MinnowBoard-org/design-files/expansion-boards-lures/relay-lure/Big Relay Board/Big Relay Lure front.png

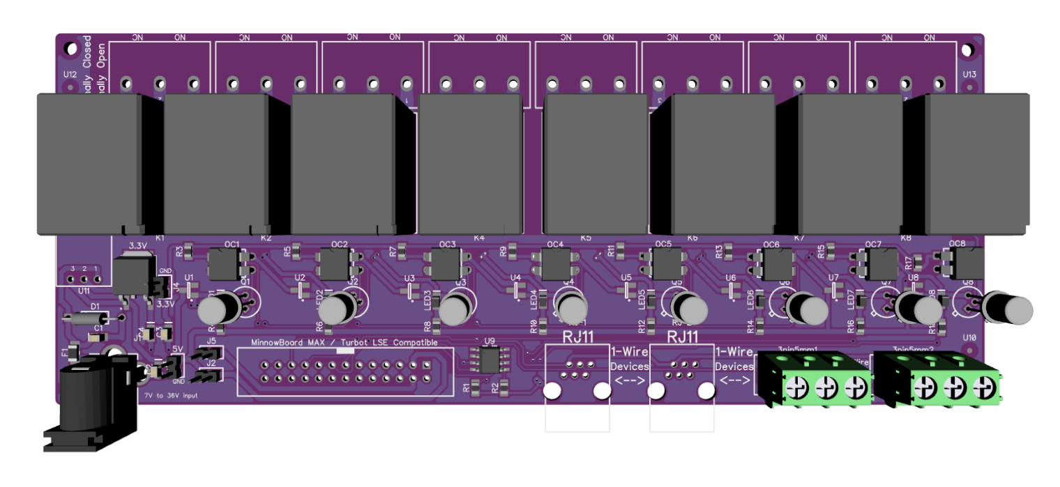
expansion-boards-lures/relay-lure/Big Relay Board/Big Relay Lure front.png
