MinnowBoard-org/design-files/minnowboard-turbot-dual-core/pcb-f200-revX205_Turbot-A/Turbot_F200_X205_VX/Minnowmax_Central_Library/LogFiles/HKP2PartsDB.txt

                    Expedition PCB ASCII to PartsDatabase Log
                    -----------------------------------------

                       10:25 PM Thursday, January 06, 2011
                                   Job Name: 

Replacing 'T:\Projects\ADI\Cinnamon_Bay_EX\Source\CBEX_X100\CBEX_Central_Library\Work\PartsDBLibs\ASCII.pdb'.

ASCII PDB           : T:\Projects\ADI\Cinnamon_Bay_EX\Source\CBEX_X100\PDB.hkp
PDB                 : T:\Projects\ADI\Cinnamon_Bay_EX\Source\CBEX_X100\CBEX_Central_Library\Work\PartsDBLibs\ASCII.pdb
Central Library     : T:\Projects\ADI\Cinnamon_Bay_EX\Source\CBEX_X100\CBEX_Central_Library\Work\ASCII.lmc
Common Property File: T:\Projects\ADI\Cinnamon_Bay_EX\Source\CBEX_X100\CBEX_Central_Library\Work\CentLib.prp

Processing Part '1110-0002'
Processing Part '1110-0003'
Processing Part '1110-0004'
Processing Part '1110-0005'
Processing Part '1110-0009'
Processing Part '1110-0010'
Processing Part '1110-0011'
Processing Part '1110-0012'
Processing Part '1110-0013'
Processing Part '1110-0014'
Processing Part '1110-0019'
Processing Part '1110-0021'
Processing Part '1110-0023'
Processing Part '1110-0024'
Processing Part '1110-0025'
Processing Part '1110-0026'
Processing Part '1110-0027'
Processing Part '1110-0028'
Processing Part '1110-0031'
Processing Part '1110-0033'
Processing Part '1110-0036'
Processing Part '1110-0038'
Processing Part '1110-0040'
Processing Part '1110-0041'
Processing Part '1110-0042'
Processing Part '1110-0044'
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
Processing Part '4641-0010'
Processing Part '4740-0010'
Processing Part '4760-0005'
Processing Part '4840-0007'
Processing Part '4840-0012'
Processing Part '4860-0009'
Processing Part '4860-0011'
Processing Part '4860-0012'
Processing Part '4860-0014'
Processing Part '44140-0008'

Verifying...

Created 'T:\Projects\ADI\Cinnamon_Bay_EX\Source\CBEX_X100\CBEX_Central_Library\Work\PartsDBLibs\ASCII.pdb' successfully.
