MinnowBoard-org/design-files/minnowboard-turbot-dual-E-Dual-and-Quadcore/F300_R201/Turbot_DUAL-E_Dual_Core_F300_R201-BOMRev201.xlsx

80201-0141-G00 - Manufactured PCA BOM, Minnowboard Turbot Dual Ethernet_Dual Core CPU, Dual I211 ENET Controllers, Rev: R201
Item | Qty | Part Number | Rev | Refdes | Description | Vendor | Vendor Part Number | Vendor Part Status | SUPPORT | PLACE
1 | 1 | 44140-0034 |  | SU1 | Label, Print on Demand, SMTC FAB SN | Brady | THT-14-728-10 | Preferred | YES
2 | 1 | 1120-0002 |  | R284 | RES, 0402, 1%, 1/16W, 29.4 | Rohm | MCR01MZPF29R4 | Preferred
 |  |  |  |  |  | KOA SPEER | RK73H1ETTP29R4F | Preferred
 |  |  |  |  |  | Panasonic | ERJ-2RKF29R4X | Preferred
 |  |  |  |  |  | Venkel Ltd. | CR0402-16W-29R4FT | Preferred
3 | 9 | 1120-0003 |  | R308,R832,R833,R834,R835,R868,R869,R870,R871 | RES, 0402, 1%, 1/16W, 33.2 | Rohm | MCR01MZPF33R2 | Preferred
 |  |  |  |  |  | KOA SPEER | RK73H1ETTP33R2F | Preferred
 |  |  |  |  |  | Panasonic | ERJ-2RKF33R2X | Preferred
 |  |  |  |  |  | Yageo | RC0402FR-0733R2L | Preferred
 |  |  |  |  |  | Walsin Technology Corporation | WR04X33R2FTL | Preferred
 |  |  |  |  |  | Venkel Ltd. | CR0402-16W-33R2FT | Preferred
4 | 11 | 1120-0009 |  | R50,R82,R119,R147,R170,R273,R274,R309,R322,R324,R340 | RES, 0402, 1%, 1/16W, 100K | Rohm | MCR01MZPF1003 | Preferred
 |  |  |  |  |  | KOA SPEER | RK73H1ETTP1003F | Preferred
 |  |  |  |  |  | Panasonic | ERJ-2RKF1003X | Preferred
 |  |  |  |  |  | Yageo | RC0402FR-07100KL | Preferred
 |  |  |  |  |  | Walsin Technology Corporation | WR04X1003FTL | Preferred
 |  |  |  |  |  | Venkel Ltd. | CR0402-16W-1003FT | Preferred
5 | 27 | 1120-0010 |  | R6-7,R15-17,R89,R94,R111,R134,R162,R186-187,R199,R208,R234,R249,R253,R259,R278,R288,R321,R837-839,R876-878 | RES, 0402, 1%, 1/16W, 1.00K | Rohm | MCR01MZPF1001 | Preferred
 |  |  |  |  |  | KOA SPEER | RK73H1ETTP1001F | Preferred
 |  |  |  |  |  | Panasonic | ERJ-2RKF1001X | Preferred
 |  |  |  |  |  | Yageo | RC0402FR-071KL | Preferred
 |  |  |  |  |  | Walsin Technology Corporation | WR04X1001FTL | Preferred
 |  |  |  |  |  | Venkel Ltd. | CR0402-16W-1001FT | Preferred
6 | 70 | 1120-0011 |  | R2,R13-14,R28-30,R71,R75,R83-84,R97,R102,R113,R116,R118,R120,R123-124,R133,R163-165,R183,R190-191,R211,R220-221,R237,R244-247,R254,R266-268,R271-272,R295,R319,R323,R400,R706,R810,R815,R820-828,R830-831,R851-852,R856-864,R866-867 | RES, 0402, 1%, 1/16W, 10.0K | Rohm | MCR01MZPF1002 | Preferred
 |  |  |  |  |  | KOA SPEER | RK73H1ETTP1002F | Preferred
 |  |  |  |  |  | Panasonic | ERJ-2RKF1002X | Preferred
 |  |  |  |  |  | Yageo | RC0402FR-0710KL | Preferred
 |  |  |  |  |  | Walsin Technology Corporation | WR04X1002FTL | Preferred
 |  |  |  |  |  | Venkel Ltd. | CR0402-16W-1002FT | Preferred
7 | 2 | 1120-0018 |  | R836,R872 | RES, 0402, 1%, 1/16W, 4.99K | Rohm | MCR01MZPF4991 | Preferred
 |  |  |  |  |  | KOA SPEER | RK73H1ETTP4991F | Preferred
 |  |  |  |  |  | Panasonic | ERJ-2RKF4991X | Preferred
 |  |  |  |  |  | Yageo | RC0402FR-074K99L | Preferred
 |  |  |  |  |  | Walsin Technology Corporation | WR04X4991FTL | Preferred
 |  |  |  |  |  | Venkel Ltd. | CR0402-16W-4991FT | Preferred
8 | 5 | 1120-0021 |  | R238,R240,R241,R242,R258 | RES, 0402, 1%, 1/16W, 49.9 | Rohm | MCR01MZPF49R9 | Preferred
 |  |  |  |  |  | KOA SPEER | RK73H1ETTP49R9F | Preferred
 |  |  |  |  |  | Panasonic | ERJ-2RKF49R9X | Preferred
 |  |  |  |  |  | Yageo | RC0402FR-0749R9L | Preferred
 |  |  |  |  |  | Walsin Technology Corporation | WR04X49R9FTL | Preferred
 |  |  |  |  |  | Venkel Ltd. | CR0402-16W-49R9FT | Preferred
9 | 5 | 1120-0022 |  | R65,R108,R169,R225,R320 | RES, 0402, 1%, 1/16W, 10.0 | Rohm | MCR01MZPF10R0 | Preferred
 |  |  |  |  |  | KOA SPEER | RK73H1ETTP10R0F | Preferred
 |  |  |  |  |  | Panasonic | ERJ-2RKF10R0X | Preferred
 |  |  |  |  |  | Yageo | RC0402FR-0710RL | Preferred
 |  |  |  |  |  | Walsin Technology Corporation | WR04X10R0FTL | Preferred
 |  |  |  |  |  | Venkel Ltd. | CR0402-16W-10R0FT | Preferred
10 | 24 | 1120-0023 |  | R311,R312,R313,R314,R315,R316,R317,R318,R328,R329,R330,R331,R341,R342,R343,R344,R345,R346,R347,R348,R349,R350,R351,R352 | RES, 0402, 1%, 1/16W, 35.7 | Rohm | MCR01MZPF35R7 | Preferred
 |  |  |  |  |  | KOA SPEER | RK73H1ETTP35R7F | Preferred
 |  |  |  |  |  | Panasonic | ERJ-2RKF35R7X | Preferred
 |  |  |  |  |  | Yageo | RC0402FR-0735R7L | Preferred
 |  |  |  |  |  | Walsin Technology Corporation | WR04X35R7FTL | Preferred
 |  |  |  |  |  | Venkel Ltd. | CR0402-16W-35R7FT | Preferred
11 | 4 | 1120-0025 |  | R91,R92,R201,R202 | RES, 0402, 1%, 1/16W, 100 | Rohm | MCR01MZPF1000 | Preferred
 |  |  |  |  |  | KOA SPEER | RK73H1ETTP1000F | Preferred
 |  |  |  |  |  | Panasonic | ERJ-2RKF1000X | Preferred
 |  |  |  |  |  | Yageo | RC0402FR-07100RL | Preferred
 |  |  |  |  |  | Walsin Technology Corporation | WR04X1000FTL | Preferred
 |  |  |  |  |  | Venkel Ltd. | CR0402-16W-1000FT | Preferred
12 | 1 | 1120-0026 |  | R179 | RES, 0402, 1%, 1/16W, 221 | Rohm | MCR01MZPF2210 | Preferred
 |  |  |  |  |  | KOA SPEER | RK73H1ETTP2210F | Preferred
 |  |  |  |  |  | Panasonic | ERJ-2RKF2210X | Preferred
 |  |  |  |  |  | Venkel Ltd. | CR0402-16W-2210FT | Preferred
13 | 2 | 1120-0029 |  | R95,R204 | RES, 0402, 1%, 1/16W, 15.0K | Rohm | MCR01MZPF1502 | Preferred
 |  |  |  |  |  | KOA SPEER | RK73H1ETTP1502F | Preferred
 |  |  |  |  |  | Panasonic | ERJ-2RKF1502X | Preferred
 |  |  |  |  |  | Yageo | RC0402FR-0715KL | Preferred
 |  |  |  |  |  | Venkel Ltd. | CR0402-16W-1502FT | Preferred
14 | 2 | 1120-0032 |  | R88,R198 | RES, 0402, 1%, 1/16W, 3.01K | Rohm | MCR01MZPF3011 | Preferred
 |  |  |  |  |  | KOA SPEER | RK73H1ETTP3011F | Preferred
 |  |  |  |  |  | Panasonic | ERJ-2RKF3011X | Preferred
 |  |  |  |  |  | Yageo | RC0402FR-073K01L | Obsolete
 |  |  |  |  |  | Walsin Technology Corporation | WR04X3011FTL | Preferred
 |  |  |  |  |  | Venkel Ltd. | CR0402-16W-3011FT | Preferred
15 | 2 | 1120-0037 |  | R106,R223 | RES, 0402, 1%, 1/16W, 165K | Rohm | MCR01MZPF1653 | Preferred
 |  |  |  |  |  | KOA SPEER | RK73H1ETTP1653F | Preferred
 |  |  |  |  |  | Panasonic | ERJ-2RKF1653X | Preferred
 |  |  |  |  |  | Yageo | RC0402FR-07165KL | Preferred
 |  |  |  |  |  | Walsin Technology Corporation | WR04X1653FTL | Preferred
 |  |  |  |  |  | Venkel Ltd. | CR0402-16W-1653FT | Preferred
16 | 1 | 1120-0041 |  | R35 | RES, 0402, 1%, 1/16W, 23.7K | Rohm | MCR01MZPF2372 | Preferred
 |  |  |  |  |  | KOA SPEER | RK73H1ETTP2372F | Preferred
 |  |  |  |  |  | Panasonic | ERJ-2RKF2372X | Preferred
 |  |  |  |  |  | Venkel Ltd. | CR0402-16W-2372FT | Preferred
17 | 3 | 1120-0044 |  | R38,R39,R213 | RES, 0402, 1%, 1/16W, 150 | Rohm | MCR01MZPF1500 | Preferred
 |  |  |  |  |  | KOA SPEER | RK73H1ETTP1500F | Preferred
 |  |  |  |  |  | Panasonic | ERJ-2RKF1500X | Preferred
 |  |  |  |  |  | Yageo | RC0402FR-07150RL | Preferred
 |  |  |  |  |  | Walsin Technology Corporation | WR04X1500FTL | Preferred
 |  |  |  |  |  | Venkel Ltd. | CR0402-16W-1500FT | Preferred
18 | 1 | 1120-0048 |  | R188 | RES, 0402, 1%, 1/16W, 1.00M | Rohm | MCR01MZPF1004 | Preferred
 |  |  |  |  |  | KOA SPEER | RK73H1ETTP1004F | Preferred
 |  |  |  |  |  | Panasonic | ERJ-2RKF1004X | Preferred
 |  |  |  |  |  | Yageo | RC0402FR-071ML | Preferred
 |  |  |  |  |  | Walsin Technology Corporation | WR04X1004FTL | Preferred
 |  |  |  |  |  | Venkel Ltd. | CR0402-16W-1004FT | Preferred
19 | 2 | 1120-0052 |  | R167,R230 | RES, 0402, 1%, 1/16W, 1.91K | Rohm | MCR01MZPF1911 | Preferred
 |  |  |  |  |  | KOA SPEER | RK73H1ETTP1911F | Preferred
 |  |  |  |  |  | Panasonic | ERJ-2RKF1911X | Preferred
 |  |  |  |  |  | Venkel Ltd. | CR0402-16W-1911FT | Preferred
20 | 2 | 1120-0055 |  | R131,R226 | RES, 0402, 1%, 1/16W, 14.0K | Rohm | MCR01MZPF1402 | Preferred
 |  |  |  |  |  | KOA SPEER | RK73H1ETTP1402F | Preferred
 |  |  |  |  |  | Panasonic | ERJ-2RKF1402X | Preferred
 |  |  |  |  |  | Yageo | RC0402FR-0714KL | Preferred
 |  |  |  |  |  | Walsin Technology Corporation | WR04X1402FTL | Preferred
 |  |  |  |  |  | Venkel Ltd. | CR0402-16W-1402FT | Preferred
21 | 1 | 1120-0060 |  | R136 | RES, 0402, 1%, 1/16W, 40.2K | Rohm | MCR01MZPF4022 | Preferred
 |  |  |  |  |  | KOA SPEER | RK73H1ETTP4022F | Preferred
 |  |  |  |  |  | Panasonic | ERJ-2RKF4022X | Preferred
 |  |  |  |  |  | Venkel Ltd. | CR0402-16W-4022FT | Preferred
22 | 1 | 1120-0079 |  | R3 | RES, 0402, 1%, 1/16W, 200 | Rohm | MCR01MZPF2000 | Preferred
 |  |  |  |  |  | KOA SPEER | RK73H1ETTP2000F | Preferred
 |  |  |  |  |  | Panasonic | ERJ-2RKF2000X | Preferred
 |  |  |  |  |  | Venkel Ltd. | CR0402-16W-2000FT | Preferred
23 | 2 | 1120-0083 |  | R24,R150 | RES, 0402, 1%, 1/16W, 12.1K | Rohm | MCR01MZPF1212 | Preferred
 |  |  |  |  |  | KOA SPEER | RK73H1ETTP1212F | Preferred
 |  |  |  |  |  | Panasonic | ERJ-2RKF1212X | Preferred
 |  |  |  |  |  | Yageo | RC0402FR-0712K1L | Preferred
 |  |  |  |  |  | Walsin Technology Corporation | WR04X1212FTL | Preferred
 |  |  |  |  |  | Venkel Ltd. | CR0402-16W-1212FT | Preferred
24 | 2 | 1120-0099 |  | R81,R194 | RES, 0402, 1%, 1/16W, 20.0 | Rohm | MCR01MZPF20R0 | Preferred
 |  |  |  |  |  | Walsin Technology Corporation | WR04X20R0FTL | Preferred
 |  |  |  |  |  | KOA SPEER | RK73H1ETTP20R0F | Preferred
 |  |  |  |  |  | Panasonic | ERJ-2RKF20R0X | Preferred
 |  |  |  |  |  | Yageo | RC0402FR-0720RL | Preferred
 |  |  |  |  |  | Venkel Ltd. | CR0402-16W-20R0FT | Preferred
25 | 4 | 1120-0103 |  | R60,R61,R256,R279 | RES, 0402, 1%, 1/16W, 20.0K | Rohm | MCR01MZPF2002 | Preferred
 |  |  |  |  |  | KOA SPEER | RK73H1ETTP2002F | Preferred
 |  |  |  |  |  | Panasonic | ERJ-2RKF2002X | Preferred
 |  |  |  |  |  | Yageo | RC0402FR-0720KL | Preferred
 |  |  |  |  |  | Walsin Technology Corporation | WR04X2002FTL | Preferred
 |  |  |  |  |  | Venkel Ltd. | CR0402-16W-2002FT | Preferred
26 | 1 | 1120-0112 |  | R153 | RES, 0402, 1%, 1/16W, 27.4K | Rohm | MCR01MZPF2742 | Preferred
 |  |  |  |  |  | KOA SPEER | RK73H1ETTP2742F | Preferred
 |  |  |  |  |  | Panasonic | ERJ-2RKF2742X | Preferred
 |  |  |  |  |  | Venkel Ltd. | CR0402-16W-2742FT | Preferred
27 | 2 | 1120-0115 |  | R105,R207 | RES, 0402, 1%, 1/16W, 44.2K | Rohm | MCR01MZPF4422 | Preferred
 |  |  |  |  |  | KOA SPEER | RK73H1ETTP4422F | Preferred
 |  |  |  |  |  | Panasonic | ERJ-2RKF4422X | Preferred
28 | 8 | 1120-0119 |  | R801,R802,R803,R804,R805,R806,R807,R808 | RES, 0402, 1%, 1/16W, 619 | Rohm | MCR01MZPF6190 | Preferred
 |  |  |  |  |  | KOA SPEER | RK73H1ETTP6190F | Preferred
 |  |  |  |  |  | Panasonic | ERJ-2RKF6190X | Preferred
 |  |  |  |  |  | Venkel Ltd. | CR0402-16W-6190FT | Preferred
29 | 1 | 1120-0121 |  | R212 | RES, 0402, 1%, 1/16W, 1.24K | Rohm | MCR01MZPF1241 | Preferred
 |  |  |  |  |  | KOA SPEER | RK73H1ETTP1241F | Preferred
 |  |  |  |  |  | Panasonic | ERJ-2RKF1241X | Preferred
 |  |  |  |  |  | Venkel Ltd. | CR0402-16W-1241FT | Preferred
30 | 1 | 1120-0122 |  | R214 | RES, 0402, 1%, 1/16W, 47.5 | Rohm | MCR01MZPF47R5 | Preferred
 |  |  |  |  |  | KOA SPEER | RK73H1ETTP47R5F | Preferred
 |  |  |  |  |  | Panasonic | ERJ-2RKF47R5X | Preferred
 |  |  |  |  |  | Venkel Ltd. | CR0402-16W-47R5FT | Preferred
31 | 2 | 1120-0138 |  | R304,R305 | RES, 0402, 1%, 1/16W, 30.1 | Rohm | MCR01MZPF30R1 | Preferred
 |  |  |  |  |  | KOA SPEER | RK73H1ETTP30R1F | Preferred
 |  |  |  |  |  | Panasonic | ERJ-2RKF30R1X | Preferred
 |  |  |  |  |  | Yageo | RC0402FR-0730R1L | Preferred
 |  |  |  |  |  | Walsin Technology Corporation | WR04X30R1FTL | Preferred
 |  |  |  |  |  | Venkel Ltd. | CR0402-16W-30R1FT | Preferred
32 | 1 | 1120-0149 |  | R816 | RES, 0402, 1%, 1/16W, 464K | Rohm | MCR01MZPF4643 | Preferred
 |  |  |  |  |  | KOA SPEER | RK73H1ETTP4643F | Preferred
 |  |  |  |  |  | Panasonic | ERJ-2RKF4643X | Preferred
 |  |  |  |  |  | Venkel Ltd. | CR0402-16W-4643FT | Preferred
33 | 1 | 1120-0157 |  | R215 | RES, 0402, 1%, 1/16W, 4.02K | Rohm | MCR01MZPF4021 | Preferred
 |  |  |  |  |  | KOA SPEER | RK73H1ETTP4021F | Preferred
 |  |  |  |  |  | Panasonic | ERJ-2RKF4021X | Preferred
 |  |  |  |  |  | Venkel Ltd. | CR0402-16W-4021FT | Preferred
34 | 4 | 1120-0167 |  | R139,R140,R327,R332 | RES, 0402, 1%, 1/16W, 240 | Panasonic | ERJ-2RKF2400X | Preferred
 |  |  |  |  |  | Rohm | MCR01MZPF2400 | Preferred
 |  |  |  |  |  | KOA SPEER | RK73H1ETTP2400F | Preferred
 |  |  |  |  |  | Yageo | RC0402FR-07240RL | Preferred
 |  |  |  |  |  | Walsin Technology Corporation | WR04X2400FTL | Preferred
 |  |  |  |  |  | Venkel Ltd. | CR0402-16W-2400FT | Preferred
35 | 1 | 1120-0168 |  | R855 | RES, 0402, 1%, 1/16W, 499 | Panasonic | ERJ-2RKF4990X | Preferred
 |  |  |  |  |  | Rohm | MCR01MZPF4990 | Preferred
 |  |  |  |  |  | KOA SPEER | RK73H1ETTP4990F | Preferred
36 | 1 | 1120-0172 |  | R25 | RES, 0402, 1%, 1/16W, 9.53K | Panasonic | ERJ-2RKF9531X | Preferred
 |  |  |  |  |  | Rohm | MCR01MZPF9531 | Preferred
 |  |  |  |  |  | KOA SPEER | RK73H1ETTP9531F | Preferred
 |  |  |  |  |  | Venkel Ltd. | CR0402-16W-9531FT | Preferred
37 | 1 | 1120-0173 |  | R34 | RES, 0402, 1%, 1/16W, 6.04K | Panasonic | ERJ-2RKF6041X | Preferred
 |  |  |  |  |  | Rohm | MCR01MZPF6041 | Preferred
 |  |  |  |  |  | KOA SPEER | RK73H1ETTP6041F | Preferred
 |  |  |  |  |  | Venkel Ltd. | CR0402-16W-6041FT | Preferred
38 | 1 | 1120-0187 |  | R814 | RES, 0402, 1%, 1/16W, 8.06K | Panasonic | ERJ-2RKF8061X | Preferred
 |  |  |  |  |  | Rohm | MCR01MZPF8061 | Preferred
 |  |  |  |  |  | KOA SPEER | RK73H1ETTP8061F | Preferred
 |  |  |  |  |  | Yageo | RC0402FR-078K06L | Preferred
 |  |  |  |  |  | Walsin Technology Corporation | WR04X8061FTL | Preferred
 |  |  |  |  |  | Venkel Ltd. | CR0402-16W-8061FT | Preferred
39 | 4 | 1120-0203 |  | R843,R844,R873,R874 | RES, 0402, 1%, 1/16W, 301 | Panasonic | ERJ-2RKF3010X | Preferred
 |  |  |  |  |  | Rohm | MCR01MZPF3010 | Preferred
 |  |  |  |  |  | KOA SPEER | RK73H1ETTP3010F | Preferred
 |  |  |  |  |  | Yageo | RC0402FR-07301RL | Preferred
 |  |  |  |  |  | Walsin Technology Corporation | WR04X3010FTL | Preferred
 |  |  |  |  |  | Venkel Ltd. | CR0402-16W-3010FT | Preferred
40 | 3 | 1120-0236 |  | R217,R218,R239 | RES, 0402, 1%, 1/16W, 402 | Rohm | MCR01MZPF4020 | Preferred
 |  |  |  |  |  | KOA SPEER | RK73H1ETTP4020F | Preferred
 |  |  |  |  |  | Panasonic | ERJ-2RKF4020X | Preferred
 |  |  |  |  |  | Yageo | RC0402FR-07402RL | Preferred
 |  |  |  |  |  | Walsin Technology Corporation | WR04X4020FTL | Preferred
 |  |  |  |  |  | Venkel Ltd. | CR0402-16W-4020FT | Preferred
41 | 1 | 1120-0267 |  | R817 | RES, 0402, 1%, 1/16W, 3.83K | Rohm | MCR01MZPF3831 | Preferred
 |  |  |  |  |  | KOA SPEER | RK73H1ETTP3831F | Preferred
 |  |  |  |  |  | Panasonic | ERJ-2RKF3831X | Preferred
 |  |  |  |  |  | Venkel Ltd. | CR0402-16W-3831FT | Preferred
42 | 2 | 1120-0282 |  | R96,R205 | RES, 0402, 1%, 1/16W, 75.0K | Rohm | MCR01MZPF7502 | Preferred
 |  |  |  |  |  | KOA SPEER | RK73H1ETTP7502F | Preferred
 |  |  |  |  |  | Panasonic | ERJ-2RKF7502X | Preferred
 |  |  |  |  |  | Yageo | RC0402FR-0775KL | Preferred
 |  |  |  |  |  | Walsin Technology Corporation | WR04X7502FTLD | Preferred
 |  |  |  |  |  | Venkel Ltd. | CR0402-16W-7502FT | Preferred
43 | 1 | 1120-0289 |  | R70 | RES, 0402, 1%, 1/16W, 88.7K | Panasonic | ERJ-2RKF8872X | Preferred
 |  |  |  |  |  | Rohm | MCR01MZPF8872 | Preferred
 |  |  |  |  |  | KOA SPEER | RK73H1ETTP8872F
44 | 2 | 1120-0294 |  | R77,R185 | RES, 0402, 1%, 1/16W, 45.3 | KOA SPEER | RK73H1ETTP45R3F | Preferred
 |  |  |  |  |  | Panasonic | ERJ-2RKF45R3X | Preferred
 |  |  |  |  |  | Vishay-Dale | CRCW040245R3FKED | Preferred
 |  |  |  |  |  | Yageo | RC0402FR-0745R3L | Preferred
 |  |  |  |  |  | Walsin Technology Corporation | WR04X45R3FTL | Preferred
 |  |  |  |  |  | Venkel Ltd. | CR0402-16W-45R3FT | Preferred
45 | 14 | 1120-0313 |  | R27,R44,R45,R47,R49,R52,R57,R117,R171,R172,R177,R236,R257,R307 | RES, 0402, 1%, 1/16W, 2.2K | Panasonic | ERJ-2RKF2201X | Preferred
 |  |  |  |  |  | Yageo | RC0402FR-072K2L | Preferred
 |  |  |  |  |  | Venkel Ltd. | CR0402-10W-2201FT | Preferred
46 | 5 | 1120-0315 |  | R11,R12,R100,R269,R270 | RES, 0402, 1%, 1/16W, 22 | Panasonic | ERJ-2RKF22R0X | Preferred
 |  |  |  |  |  | Venkel Ltd. | CR0402-10W-22R0FT | Preferred
47 | 1 | 1120-0317 |  | R819 | RES, 0402, 1%, 1/16W, 330 | Panasonic | ERJ-2RKF3300X | Preferred
 |  |  |  |  |  | Rohm | MCR01MZPF3300 | Preferred
 |  |  |  |  |  | Venkel Ltd. | CR0402-16W-3300FT | Preferred
48 | 2 | 1120-0318 |  | R148,R746 | RES, 0402, 1%, 1/16W, 470 | Panasonic | ERJ-2RKF4700X | Preferred
 |  |  |  |  |  | Yageo | RC0402FR-07470RL | Preferred
 |  |  |  |  |  | Venkel Ltd. | CR0402-16W-4700FT | Preferred
49 | 1 | 1120-0322 |  | R109 | RES, 0402, 1%, 1/16W, 499K | Vishay-Dale | CRCW0402499KFKED | Preferred
 |  |  |  |  |  | KOA SPEER | RK73H1ETTP4993F | Preferred
 |  |  |  |  |  | Panasonic | ERJ-2RKF4993X | Preferred
 |  |  |  |  |  | Venkel Ltd. | CR0402-16W-4993FT | Preferred
50 | 1 | 1120-0326 |  | R280 | RES, 0402, 1%, 1/16W, 23.2 | KOA SPEER | RK73H1ETTP23R2F | Preferred
 |  |  |  |  |  | Panasonic | ERJ-2RKF23R2X | Preferred
 |  |  |  |  |  | Vishay-Dale | CRCW040223R2FKED | Preferred
 |  |  |  |  |  | Venkel Ltd. | CR0402-16W-23R2FT | Preferred
51 | 1 | 1120-0327 |  | R281 | RES, 0402, 1%, 1/16W, 162 | KOA SPEER | RK73H1ETTP1620F | Preferred
 |  |  |  |  |  | Panasonic | ERJ-2RKF1620X | Preferred
 |  |  |  |  |  | Vishay-Dale | CRCW0402162RFKED | Preferred
52 | 16 | 1120-0328 |  | R23,R32,R33,R125,R126,R137,R138,R143,R144,R149,R282,R283,R310,R325,R326,R333 | RES, 0402, 1%, 1/16W, 4.7K | Rohm | TRR01MZPF4701 | Preferred
 |  |  |  |  |  | KOA SPEER | RK73H1ETTP4701F | Preferred
 |  |  |  |  |  | Panasonic | ERJ-2RKF4701X | Preferred
 |  |  |  |  |  | Venkel Ltd. | CR0402-16W-4701FT | Preferred
53 | 3 | 1120-0329 |  | R80,R101,R193 | RES, 0402, 1%, 1/16W, 16.9 | KOA SPEER | RK73H1ETTP16R9F | Preferred
 |  |  |  |  |  | Panasonic | ERJ-2RKF16R9X | Preferred
 |  |  |  |  |  | Vishay-Dale | CRCW040216R9FKED | Preferred
 |  |  |  |  |  | Venkel Ltd. | CR0402-16W-16R9FT | Preferred
54 | 3 | 1120-0330 |  | R104,R195,R197 | RES, 0402, 1%, 1/16W, 69.8 | KOA SPEER | RK73H1ETTP69R8F | Preferred
 |  |  |  |  |  | Panasonic | ERJ-2RKF69R8X | Preferred
 |  |  |  |  |  | Vishay-Dale | CRCW040269R8FKED | Preferred
 |  |  |  |  |  | Venkel Ltd. | CR0402-16W-69R8FT | Preferred
55 | 2 | 1120-0338 |  | R146,R227 | RES, 0402, 1%, 1/16W, 16.5K | Panasonic | ERJ-2RKF1652X | Preferred
 |  |  |  |  |  | Rohm | TRR01MZPF1652 | Preferred
 |  |  |  |  |  | KOA SPEER | RK73H1ETTP1652F | Preferred
56 | 2 | 1120-0351 |  | R93,R203 | RES, 0402, 1%, 1/16W, 18.7K | Samsung Electro-Mechanics America, Inc. | RC1005F1872CS | Preferred
 |  |  |  |  |  | Yageo | RC0402FR-0718K7L | Preferred
 |  |  |  |  |  | Panasonic | ERJ-2RKF1872X | Preferred
 |  |  |  |  |  | Vishay-Dale | CRCW040218K7FKED | Preferred
 |  |  |  |  |  | Rohm | MCR01MZPF1872 | Preferred
 |  |  |  |  |  | Walsin Technology Corporation | WR04X1872FTL | Preferred
 |  |  |  |  |  | Venkel Ltd. | CR0402-16W-1872FT | Preferred
57 | 3 | 1120-0359 |  | R142,R848,R879 | RES, 0402, 1%, 1/16W, 33.2K | Stackpole Electronics Inc | RMCF0402FT33K2 | Preferred
 |  |  |  |  |  | Vishay | CRCW040233K2FKED | Preferred
 |  |  |  |  |  | Panasonic | ERJ-2RKF3322X | Preferred
 |  |  |  |  |  | Venkel Ltd. | CR0402-16W-3322FT | Preferred
58 | 2 | 1120-0361 |  | R206,R812 | RES, 0402, 1%, 1/16W, 200K | Rohm | MCR01MZPF2003 | Preferred
 |  |  |  |  |  | KOA SPEER | RK73H1ETTP2003F | Preferred
 |  |  |  |  |  | Panasonic | ERJ-2RKF2003X | Preferred
 |  |  |  |  |  | Venkel Ltd. | CR0402-16W-2003FT | Preferred
59 | 5 | 1120-0363 |  | R8,R9,R10,R19,R21 | RES, 0402, 1%, 1/16W, 51.1 | Vishay-Dale | CRCW040251R1FKED | Preferred
 |  |  |  |  |  | KOA SPEER | RK73H1ETTP51R1F | Preferred
 |  |  |  |  |  | Panasonic | ERJ-2RKF51R1X | Preferred
 |  |  |  |  |  | Venkel Ltd. | CR0402-16W-51R1FT | Preferred
60 | 1 | 1120-0364 |  | R255 | RES, 0402, 1%, 1/16W, 73.2 | KOA SPEER | RK73H1ETTP73R2F | Preferred
 |  |  |  |  |  | Panasonic | ERJ-2RKF73R2X | Preferred
 |  |  |  |  |  | Vishay-Dale | CRCW040273R2FKED | Preferred
 |  |  |  |  |  | Venkel Ltd. | CR0402-16W-73R2FT | Preferred
61 | 1 | 1120-0365 |  | R135 | RES, 0402, 1%, 1/16W, 143K | Vishay-Dale | CRCW0402143KFKED | Preferred
 |  |  |  |  |  | KOA SPEER | RK73H1ETTP1433F | Preferred
 |  |  |  |  |  | Panasonic | ERJ-2RKF1433X | Preferred
 |  |  |  |  |  | Venkel Ltd. | CR0402-16W-1433FT | Preferred
62 | 1 | 1120-0366 |  | R76 | RES, 0402, 1%, 1/16W, 10.0M | KOA SPEER | RK73H1ETTP1005F | Preferred
 |  |  |  |  |  | Vishay-Dale | CRCW040210M0FKED | Preferred
 |  |  |  |  |  | Venkel Ltd. | CR0402-16W-1005FT | Preferred
63 | 1 | 1120-0367 |  | R40 | RES, 0402, 1%, 1/16W, 357 | Panasonic | ERJ-2RKF3570X | Preferred
 |  |  |  |  |  | Rohm | MCR01MZPF3570 | Preferred
 |  |  |  |  |  | KOA SPEER | RK73H1ETTP3570F | Preferred
 |  |  |  |  |  | Venkel Ltd. | CR0402-16W-3570FT | Preferred
64 | 62 | 1121-0001 |  | R5,R18,R20,R22,R26,R36,R37,R41,R42,R43,R46,R48,R51,R59,R62,R63,R64,R66,R67,R68,R69,R72,R73,R74,R78,R79,R98,R99,R103,R122,R127,R128,R129,R130,R151,R158,R159,R160,R175,R176,R178,R184,R192,R216,R232,R243,R248,R261,R263,R264,R293,R300,R302,R306,R353,R354,R809,R840,R841,R842,R849,R850 | RES, 0402, ZERO OHM JUMPER | Panasonic | ERJ-2GE0R00X | Preferred
 |  |  |  |  |  | Rohm | MCR01MZPJ000 | Preferred
 |  |  |  |  |  | Venkel Ltd. | CR0402-16W-000T | Preferred
 |  |  |  |  |  | Yageo | RC0402JR-070RL | Preferred
 |  |  |  |  |  | Walsin Technology Corporation | WR04X000PTL | Preferred
65 | 7 | 1121-0011 |  | R155,R156,R157,R173,R174,R180,R182 | RES, 0402, 5%, 1/16W, 100K | Panasonic | ERJ-2GEJ104X | Preferred
 |  |  |  |  |  | Rohm | MCR01MZPJ104 | Preferred
 |  |  |  |  |  | KOA SPEER | RK73B1ETTP104J | Preferred
66 | 2 | 1121-0025 |  | R90,R200 | RES, 0402, 5%, 1/16W, 47 | Panasonic | ERJ-2GEJ470X | Preferred
 |  |  |  |  |  | Rohm | MCR01MZPJ470 | Preferred
 |  |  |  |  |  | KOA SPEER | RK73B1ETTP470J | Preferred
67 | 2 | 1130-0002 |  | R107,R224 | RES, 0603, 1%, 1/16W, 100K | Panasonic | ERJ-3EKF1003V | Preferred
 |  |  |  |  |  | Rohm | MCR03EZPFX1003 | Preferred
 |  |  |  |  |  | KOA SPEER | RK73H1JTTD1003F | Preferred
 |  |  |  |  |  | Phycomp | 232270461004 | Preferred
 |  |  |  |  |  | Venkel Ltd. | CR0603-16W-1003FT | Preferred
68 | 2 | 1130-0011 |  | R853,R854 | RES, 0603, 1%, 1/16W, 49.9 | Panasonic | ERJ-3EKF49R9V | Preferred
 |  |  |  |  |  | Rohm | MCR03EZPFX49R9 | Preferred
 |  |  |  |  |  | KOA SPEER | RK73H1JTTD49R9F | Preferred
 |  |  |  |  |  | Yageo | RC0603FR-0749R9L | Preferred
 |  |  |  |  |  | Venkel Ltd. | CR0603-16W-49R9FT | Preferred
69 | 2 | 1130-0100 |  | R291,R298 | RES, 0603, 1%, 1/16W, 4.75 | Yageo | RC0603FR-074R75L | Preferred
 |  |  |  |  |  | Venkel Ltd. | CR0603-16W-4R75FT | Preferred
70 | 2 | 1130-0193 |  | R845,R846 | RES, 0603, 1%, 1/16W, 1.00 | Panasonic | ERJ-3RQF1R0V | Preferred
 |  |  |  |  |  | Yageo | RC0603FR-071RL | Preferred
 |  |  |  |  |  | Venkel Ltd. | CR0603-10W-1R00FT | Preferred
71 | 5 | 1130-0234 |  | R154,R166,R228,R229,R813 | RES, 0603, 1%, 1/16W, 2.20 | Yageo | RC0603FR-072R2L | Preferred
 |  |  |  |  |  | Vishay-Dale | CRCW06032R20FNEA | Preferred
 |  |  |  |  |  | Venkel Ltd. | CR0603-10W-2R20FT | Preferred
72 | 5 | 1131-0001 |  | FB7,R152,R222,R265,R275 | RES, 0603, ZERO OHM JUMPER | Panasonic | ERJ-3GEY0R00V | Preferred
 |  |  |  |  |  | Rohm | MCR03EZPJ000 | Preferred
 |  |  |  |  |  | Venkel Ltd. | CR0603-16W-000T | Preferred
73 | 2 | 1141-0026 |  | R168,R231 | RES, 0805, 5%, 1/10W, 2.2 | Panasonic | ERJ-6GEYJ2R2V | Preferred
 |  |  |  |  |  | Rohm | MCR10EZPJ2R2 | Preferred
 |  |  |  |  |  | KOA SPEER | RK73B2ATTD2R2J | Preferred
74 | 1 | 1150-0034 |  | R132 | RES, 1206, 1%, 1/8W, 2.20 | Rohm | MCR18EZHFL2R20 | Preferred
 |  |  |  |  |  | Vishay-Dale | CRCW12062R20FNEA | Preferred
 |  |  |  |  |  | Yageo | RC1206FR-072R2L | Preferred
 |  |  |  |  |  | Venkel Ltd. | CR1206-4W-2R20FT | Preferred
75 | 2 | 2220-0002 |  | C35,C62 | CAP, Ceramic NPO, 0402, 47pF, 5%, 50V | AVX | 04025A470JAT2A | Preferred
 |  |  |  |  |  | KEMET | C0402C470J5GACTU | Preferred
 |  |  |  |  |  | Murata | GRM1555C1H470JA01D | Preferred
 |  |  |  |  |  | Panasonic | ECJ-0EC1H470J | EOL
 |  |  |  |  |  | Murata | GRM1555C1H470JZ01 | EOL
 |  |  |  |  |  | Yageo | CC0402JRNPO9BN470 | Preferred
 |  |  |  |  |  | Walsin Technology Corporation | 0402N470J500LT | Preferred
 |  |  |  |  |  | Venkel Ltd. | C0402C0G500-470JNP | Preferred
76 | 2 | 2220-0003 |  | C42,C43 | CAP, Ceramic NPO, 0402, 18pF, 5%, 50V | AVX | 04025A180JAT2A | Preferred
 |  |  |  |  |  | Panasonic | ECJ-0EC1H180J | EOL
 |  |  |  |  |  | Murata | GRM1555C1H180JZ01 | Preferred
 |  |  |  |  |  | Walsin Technology Corporation | 0402N180J500CT | Preferred
 |  |  |  |  |  | Venkel Ltd. | C0402C0G500-180JNP | Preferred
77 | 2 | 2220-0014 |  | C36,C63 | CAP, Ceramic NPO, 0402, 220pF, 5%, 50V | Walsin | 0402N221J500LT | Preferred
 |  |  |  |  |  | Taiyo Yuden | UMK105CG221JV-F | Preferred
 |  |  |  |  |  | AVX | 04025A221JAT2A | Preferred
 |  |  |  |  |  | Murata | GRM1555C1H221JA01D | Preferred
 |  |  |  |  |  | Venkel Ltd. | C0402COG500-221JNE | Preferred
 |  |  |  |  |  | Panasonic | ECJ-0EC1H221J | EOL
78 | 7 | 2220-0017 |  | C119,C175,C176,C252,C253,C449,C450 | CAP, Ceramic NPO, 0402, 27pF, 5%, 50V | Yageo | CC0402JRNPO9BN270 | Preferred
 |  |  |  |  |  | Walsin | 0402N270J500LT | Preferred
 |  |  |  |  |  | AVX | 04025A270JAT2A | Preferred
 |  |  |  |  |  | KEMET | C0402C270J5GACTU | Preferred
 |  |  |  |  |  | Venkel Ltd. | C0402COG500-270JNE | Preferred
 |  |  |  |  |  | Panasonic | ECJ-0EC1H270J | EOL
79 | 2 | 2220-0022 |  | C106,C152 | CAP, Ceramic NPO, 0402, 22pF, 5%, 50V | AVX | 04025A220JAT2A | Preferred
 |  |  |  |  |  | Panasonic | ECJ-0EC1H220J | EOL
 |  |  |  |  |  | Murata | GRM1555C1H220JZ01D | Preferred
 |  |  |  |  |  | Venkel Ltd. | C0402COG500-220JNE | Preferred
80 | 4 | 2220-0025 |  | C39,C47,C113,C184 | CAP, Ceramic NPO, 0402, 470pF, 5%, 50V | Murata | GRM1555C1H471JA01D | Preferred
 |  |  |  |  |  | TDK | C1005C0G1H471J | EOL
 |  |  |  |  |  | TDK | C1005C0G1H471J050BA | Preferred
 |  |  |  |  |  | Walsin Technology Corporation | 0402N471J500LT | Preferred
 |  |  |  |  |  | Yageo | CC0402JRNPO9BN471 | Preferred
 |  |  |  |  |  | Venkel Ltd. | C0402C0G500-471JNP | Preferred
81 | 1 | 2220-0026 |  | C49 | CAP, Ceramic NPO, 0402, 10pF, 5%, 50V | AVX | 04025A100JAT2A | Preferred
 |  |  |  |  |  | Murata | GRM1555C1H100JA01D | Preferred
 |  |  |  |  |  | Murata | GRM1555C1H100JZ01D | EOL
 |  |  |  |  |  | Panasonic | ECJ-0EC1H100D | EOL
 |  |  |  |  |  | Venkel Ltd. | C0402C0G500-100JNP | Preferred
82 | 2 | 2220-0035 |  | C45,C167 | CAP, Ceramic NPO, 0402, 1000pF, 5%, 50V | Murata | GRM1555C1H102JA01D | Preferred
83 | 6 | 2220-0039 |  | C429,C430,C431,C462,C463,C464 | CAP, Ceramic NPO, 0402, 560pF, 5%, 50V | Murata | GRM1555C1H561JA01D | Preferred
 |  |  |  |  |  | Venkel Ltd. | C0402C0G500-561JNP | Preferred
84 | 1 | 2220-0047 |  | C382 | CAP, Ceramic NPO, 0402, 22pF, 2%, 50V | Murata | GRM1555C1H220GA01D | Preferred
 |  |  |  |  |  | Johanson Technology Inc | 500R07S220GV4T | Preferred
 |  |  |  |  |  | TDK | C1005C0G1H220G050BA | Preferred
85 | 4 | 2221-0002 |  | C37,C40,C64,C166 | CAP, Ceramic X7R, 0402, 2200pF, 10%, 50V | Walsin Technology Corporation | 0402B222K500CT | Preferred
 |  |  |  |  |  | Murata | GRM155R71H222KA01D | Preferred
 |  |  |  |  |  | AVX | 04025C222KAT2A | Preferred
 |  |  |  |  |  | Panasonic | ECJ-0EB1H222K | EOL
 |  |  |  |  |  | Venkel Ltd. | C0402X7R500-222KNP | Preferred
86 | 1 | 2221-0003 |  | C358 | CAP, Ceramic X7R, 0402, 4700pF, 10%, 25V | AVX | 04023C472KAT2A | Preferred
 |  |  |  |  |  | Panasonic | ECJ-0EB1E472K | EOL
 |  |  |  |  |  | Venkel Ltd. | C0402X7R250-472KNP | Preferred
87 | 2 | 2221-0017 |  | C425,C465 | CAP, Ceramic X7R, 0402, 0.039uF, 10%, 16V | Murata | GRM155R71C393KA01D | Preferred
 |  |  |  |  |  | KEMET | C0402C393K4RACTU | Preferred
 |  |  |  |  |  | Walsin Technology Corporation | 0402B393K160CT | Preferred
 |  |  |  |  |  | Taiyo Yuden | EMK105B7393KV-F | Preferred
 |  |  |  |  |  | Venkel Ltd. | C0402X7R160-393KNP | Preferred
88 | 2 | 2221-0023 |  | C75,C342 | CAP, Ceramic X7R, 0402, 0.22uF, 10%, 16V | Murata | GRM155R71C224KA12D | Preferred
 |  |  |  |  |  | Samsung | CL05B224KO5NNNC | Preferred
 |  |  |  |  |  | Venkel Ltd. | C0402X7R160-224KNP | Preferred
89 | 10 | 2221-0034 |  | C10-13,C173,C177-180,C210 | CAP, Ceramic X7R, 0402, 0.01uF, 10%, 50V | TDK | C1005X7R1H103K | EOL
 |  |  |  |  |  | TDK | C1005X7R1H103K050BB | Preferred
 |  |  |  |  |  | Murata | GRM155R71H103KA88D | Preferred
 |  |  |  |  |  | Walsin Technology Corporation | 0402B103K500CT | Preferred
 |  |  |  |  |  | Venkel Ltd. | C0402X7R500-103KNP | Preferred
90 | 2 | 2222-0008 |  | C50,C186 | CAP, Ceramic X5R, 0402, 0.22uF, 10%, 16V | Panasonic | ECJ-0EB1C224K | EOL
 |  |  |  |  |  | Taiyo Yuden | EMK105BJ224KV-F | Preferred
 |  |  |  |  |  | TDK | C1005X5R1C224K | EOL
 |  |  |  |  |  | TDK | C1005X5R1C224K050BB | Preferred
91 | 74 | 2222-0014 |  | C2,C24,C26-27,C44,C53,C97,C116-117,C160,C163,C170-172,C174,C181-183,C193-200,C203,C209,C213-223,C236,C239,C242-246,C255-266,C271-274,C276,C285-286,C292,C338,C340-341,C379-380,C428,C432,C457 | CAP, Ceramic X5R, 0402, 1.0uF, 10%, 25V | Murata | GRM155R61E105KA12D | Preferred
 |  |  |  |  |  | TDK | C1005X5R1E105K050BC | Preferred
 |  |  |  |  |  | Samsung Electro-Mechanics | CL05A105KA5NQNC | Preferred
 |  |  |  |  |  | Venkel Ltd. | C0402X5R250-105KNP | Preferred
92 | 142 | 2222-0016 |  | C1,C3-5,C14-15,C17-18,C20,C22,C25,C29-32,C41,C46,C59-60,C65,C70-73,C82,C84,C86,C92-94,C96,C105,C122,C124,C131,C133,C136,C138-139,C153-155,C158,C165,C168,C188-189,C191-192,C202,C204-208,C212,C226,C234-235,C237,C254,C275,C277,C283-284,C287-289,C291,C293,C300-301,C306-307,C309,C311,C320,C323,C327,C329,C332,C337,C339,C343-357,C375-377,C383,C400-418,C426-427,C433-447,C458-461 | CAP, Ceramic X5R, 0402, 0.1uF, 10%, 25V | AVX | 04023D104KAT2A | Preferred
 |  |  |  |  |  | Yageo | CC0402KRX5R8BB104 | Preferred
 |  |  |  |  |  | TDK | C1005X5R1E104K050BC | Preferred
 |  |  |  |  |  | Murata | GRM155R61E104KA87D | Preferred
 |  |  |  |  |  | Venkel Ltd. | C0402X5R250-104KNP | Preferred
93 | 2 | 2222-0017 |  | C149,C150 | CAP, Ceramic X5R, 0402, 2.2uF, 10%, 10V | TDK | C1005X5R1A225K050BC | Preferred
 |  |  |  |  |  | Samsung | CL05A225KP5NSNC | Preferred
 |  |  |  |  |  | Venkel Ltd. | C0402X5R100-225KNP | Preferred
94 | 32 | 2232-0001 |  | C108,C109,C110,C111,C123,C125,C130,C132,C134,C135,C142,C143,C144,C145,C146,C147,C318,C319,C321,C322,C330,C333,C363,C364,C365,C366,C368,C369,C370,C371,C372,C373 | CAP, Ceramic X5R, 0603, 0.47uF, 10%, 10V | AVX | 0603ZD474KAT2A | Preferred
 |  |  |  |  |  | Panasonic | ECJ-1VB1A474K | EOL
 |  |  |  |  |  | TDK | C1608X5R1A474KT | EOL
 |  |  |  |  |  | Venkel Ltd. | C0603X5R100-474KNE | Preferred
 |  |  |  |  |  | TDK | C1608X5R1A474K080AA | Preferred
95 | 35 | 2232-0012 |  | C6,C8,C19,C28,C95,C107,C115,C118,C151,C156,C159,C162,C241,C247,C267,C324,C335,C336,C359,C360,C361,C362,C367,C419,C420,C421,C422,C423,C424,C451,C452,C453,C454,C455,C456 | CAP, Ceramic X5R, 0603, 10.0uF, 20%, 6.3V | Panasonic | ECJ-1VB0J106M | EOL
 |  |  |  |  |  | Murata | GRM188R60J106ME47D | Preferred
 |  |  |  |  |  | Taiyo Yuden | JMK107BJ106MA-T | Preferred
 |  |  |  |  |  | HolyStone | C0603B106M007T | Preferred
 |  |  |  |  |  | TDK | C1608X5R0J106M | EOL
 |  |  |  |  |  | TDK | C1608X5R0J106M080AB | Preferred
 |  |  |  |  |  | Venkel Ltd. | C0603X5R6R3-106MNP | Preferred
96 | 5 | 2232-0016 |  | C48,C185,C227,C238,C240 | CAP, Ceramic X5R, 0603, 4.7uF, 10%, 16V | Samsung | CL10A475KO8NNNC | Preferred
 |  |  |  |  |  | Murata | GRM188R61C475KE11D | Preferred
 |  |  |  |  |  | HolyStone | C0603B475K016T | Preferred
 |  |  |  |  |  | TDK | C1608X5R1C475K080AC | Preferred
 |  |  |  |  |  | Venkel Ltd. | C0603X5R160-475KNP | Preferred
 |  |  |  |  |  | TDK | C1608X5R1C475K | EOL
97 | 4 | 2232-0017 |  | C51,C299,C302,C326 | CAP, Ceramic X5R, 0603, 10uF, 20%, 25V | Murata | GRM188R61E106MA73D | Preferred
 |  |  |  |  |  | TDK | C1608X5R1E106M080AC | Preferred
 |  |  |  |  |  | Samsung Electro-Mechanics | CL10A106MA8NRNC | Preferred
98 | 10 | 2232-0018 |  | C54,C55,C56,C57,C58,C98,C99,C305,C312,C313 | CAP, Ceramic X5R, 0603, 22uF, 20%, 10V | TDK | C1608X5R1A226M080AC | Preferred
99 | 2 | 2240-0005 |  | C52,C187 | CAP, Ceramic NPO, 0805, 1000pF, 5%, 50V | AVX | 08055A102JAT2A | Preferred
 |  |  |  |  |  | Panasonic | ECJ-2VC1H102J | EOL
 |  |  |  |  |  | KEMET | C0805C102J5GACTU | Preferred
 |  |  |  |  |  | Venkel Ltd. | C0805C0G500-102JNE | Preferred
 |  |  |  |  |  | Yageo | CC0805JRNPO9BN102 | Preferred
100 | 38 | 2242-0013 |  | C7,C21,C74,C83,C91,C103,C120,C121,C126,C127,C128,C137,C140,C141,C164,C190,C201,C224,C225,C248,C249,C268,C269,C278,C279,C282,C294,C295,C298,C303,C304,C308,C314,C315,C316,C317,C328,C334 | CAP, Ceramic X5R, 0805, 22uF, 10%, 16V | Samsung | CL21A226KOQNNNG | Preferred
 |  |  |  |  |  | Venkel Ltd. | C0805X5R160-226KNE | Preferred
 |  |  |  |  |  | TDK | C2012X5R1C226K125AC | Preferred
101 | 12 | 2242-0014 |  | C66,C67,C68,C78,C79,C80,C81,C88,C89,C90,C101,C102 | CAP, Ceramic X5R, 0805, 22uF, 10%, 6.3V, Low Profile | Samsung | CL21A226MQCLQNC | Preferred
 |  |  |  |  |  | Taiyo Yuden | JMK212ABJ226MD-T | Preferred
102 | 1 | 2267-0004 |  | C16 | CAP, Ceramic X7R, 1808, 1000pF, 10%, 3KV | AVX | 1808HC102KAT1A | Preferred
103 | 4 | 2466-0016 |  | C76,C77,C87,C129 | CAP, AL Polymer Elect, SM, 330uF, 20%, 2.0V, 7 mOHM | Panasonic | EEF-SX0D331XE | Preferred
 |  |  |  |  |  | Murata | ECASD60D337M007K00 | Preferred
104 | 2 | 3044-0010 |  | FB12,FB14 | FERRITE BEAD, 0603, 2.2A, 220 OHM | Murata | BLM18KG221SN1D | Preferred
105 | 2 | 3044-0011 |  | FB3,FB6 | FERRITE BEAD, 0603, 1.3A, 600 OHM | Murata | BLM18KG601SN1D | Preferred
106 | 9 | 3044-0012 |  | FB1,FB4,FB5,FB11,FB13,L5,L6,L12,L13 | FERRITE BEAD, 0603, 3.0A, 120 OHM | Murata | BLM18KG121TN1D | Preferred
107 | 3 | 3048-0004 |  | FB2,L1,L2 | FERRITE BEAD, 0805, 3.0A, 220 OHM | Murata | BLM21PG221SN1D | Preferred
 |  |  |  |  |  | TDK | MPZ2012S221A | Preferred
108 | 1 | 3120-0183 |  | L8 | INDUCTOR, 65nH, 15%, 19A, SM | Cooper-Busssman Coiltronics | FP0404R1-R065-R | Preferred
 |  |  |  |  |  | Vitec Electronics Corporation | 59PR65-650 | Preferred
 |  |  |  |  |  | ITG | SL1616A-R06LHF | Preferred
109 | 2 | 3120-0266 |  | L4,L18 | INDUCTOR, 470nH, +/-20%, 17.5A, SM | Abracon | ASPI-7318-R47M-T | Preferred
 |  |  |  |  |  | Signal Transformer | SCIHP0730-R47M | Preferred
110 | 4 | 3142-0014 |  | CHOKE1-4 | CM-CHOKE, USB / LVDS, 90 OHM, 0.33A, SM, -55 to +125 C | Murata | DLW21HN900SQ2 | Preferred
 |  |  |  |  |  | Central Technologies | CTDLW21SF-900T04 | Preferred
 |  |  |  |  |  | Venkel Ltd. | CMCC0805900NT | Preferred
111 | 4 | 3142-0024 |  | L14-17 | CM-CHOKE, 920 OHM, 0.16A, SM, -40 to +85 C | Murata | DLW21SN921SK2L | Preferred
112 | 1 | 3336-0031 |  | J3 | CONN, SM, MICRO SIM CARD, PUSH-PULL, 6 CIRCUIT, DET SW | Molex | 78727-0001 | Preferred
113 | 1 | 3349-0039 |  | J8 | CONN, SM, M.2 MINI CARD, B-KEY, 67 CKT, 4.2MM HT, 15U GOLD | TE Connectivity | 2199230-3 | Alternate Source
 |  |  |  |  |  | LOTES CO., LTD | APCI0105-P001A | Preferred
114 | 2 | 3362-0042 |  | J11,J12 | CONN, TH, RJ45 GigE W/ XFMR, GRN-ORN & GRN LEDS, RA, 0-70C | UDE Corp. | RB1-1Q6BAM1A | Preferred
115 | 1 | 3376-0004 |  | J13 | CONN, SM W/ TH TABS, HDMI TYPE A, RT ANGLE | FCI | 10029449-111RLF | Preferred
116 | 1 | 3430-0078 |  | J4 | CONN, TH, 6X1, 0.1 HEADER, VERT, TIN | Samtec | TSW-106-07-T-S | Preferred
117 | 3 | 3430-0206 |  | J5,J6,J7 | CONN, TH, 2X1, 0.1 HEADER, VERT, TIN | RSK | MESA01-02T2xxxDTA A=5.84, B=2.92 | Preferred
 |  |  |  |  |  | Sullins | PREC002SAAN-RC | Alternate Source
 |  |  |  |  |  | Samtec | TSW-102-23-T-S | Alternate Source
118 | 1 | 3430-0212 |  | J14 | CONN, TH, 2X1, 2 MM HEADER, SHROUD | JST | B2B-PH-K-S(LF)(SN) | Preferred
119 | 1 | 3462-0013 |  | J9 | CONN, TH, POWER JACK, 2.0MM CENTER PIN, SCREW ON, 5A, INCL. WASHER & NUT | Singatron | 2DC-S456CCS113 | Preferred
 |  |  |  |  |  | CUI Inc | PJ-066A | Preferred
120 | 1 | 3730-0012 |  | OCP1 | PTC OVERCURRENT PROTECTOR, 0.25A IHOLD, 24V, SM | Bel Fuse Inc. | 0ZCJ0025AF2E | Preferred
121 | 3 | 3740-0064 |  | X1,X2,Y2 | XTAL, 25.000 MHZ, 25/25 TOL/STAB, 18pF, -40 to +85C, 3.2x2.5 | Suntsu Frequency Control, Inc. | SCM18D48-25.000Mhz TR | Preferred
 |  |  |  |  |  | Transko | CS32-F2525CQ18-25.000MHz | Preferred
 |  |  |  |  |  | Fujicom | FSX3M 25.000000M18FGF | Preferred
122 | 1 | 3750-0010 |  | FL1 | FILTER, EMI/ESD, 40 OHM, 12pF, -40C to +85C | NXP | IP4252CZ16-8-TTL | Preferred
123 | 1 | 3770-0026 |  | SW1 | SWITCH, MOMENTARY, PUSHBUTTON, NO, RT ANG, TH | TE Connectivity | 1825027-5 | Preferred
124 | 4 | 3880-0004 |  | TH1,TH2,TH3,TH4 | THERMISTOR, NTC, SM, 0402, 1%, 1/16W, 100K@25C, B25/50=4250K | Murata | NCP15WF104F03RC | Preferred
125 | 1 | 4124-0013 |  | U41 | IC, DDR2/DDR3/DDR3LP BUCK CONTROLLER, TERM LDO, REF, -40 to +85 C | Richtek Technology Corp. | RT8207GQW | Preferred
126 | 2 | 4148-0141 |  | U25,U26 | IC, SYNC SWITCHING REG, BUCK, VR12, 14A OUT, 5-20V IN, 1.0V/1.1V VBOOT | ON Semiconductor | NCP81109GMNTXG | Preferred
127 | 1 | 4158-0047 |  | U32 | IC, DUAL POWER DIST SWITCH, 1.0A, 2.7-5.5V IN, ACT HIGH EN, REVERSE BLOCK | Diodes Inc. | AP2172MPG-13 | Preferred
128 | 1 | 4222-0059 |  | U39 | IC, INV, SCHMITT TRIGGER, SINGLE | TI | SN74LVC1G14DCKR | Preferred
129 | 2 | 4300-0074 |  | U42,U44 | IC, 10/100/1000 ETHERNET MAC/PHY, PCI EXPRESS, 0-70 C | Intel | WGI211ATSLJXZ | Preferred
 |  |  |  |  |  | Intel | WGI211AT | Preferred
130 | 1 | 4318-0010 |  | U40 | IC, DUAL BIDIR I2C & SMBUS BUS TRANSLATOR, -40 to +85 C | TI | PCA9306DCUT | Preferred
131 | 1 | 4327-0008 |  | U18 | IC, 4-BIT BIDIR LEVEL TRANSLATOR W AUTO DIR SENSE, 1.2-3.6V / 1.65-5.5V | NXP | NTB0104GU12,115 | Preferred
132 | 4 | 4327-0009 |  | U4,U5,U6,U7 | IC, 2-BIT BIDIR OD LEVEL TRANSLATOR W AUTO DIR, 1.2-3.6V / 1.65-5.5V | NXP | NTS0102GT,115 | Preferred
133 | 6 | 4327-0010 |  | U10,U14,U15,U16,U17,U19 | IC, 4-BIT BIDIR OD LEVEL TRANSLATOR W AUTO DIR, 1.2-3.6V / 1.65-5.5V | NXP | NTS0104GU12,115 | Preferred
134 | 4 | 4343-0015 |  | MEM1,MEM2,MEM3,MEM4 | IC, 4 GBIT DDR3L-1600 SDRAM, 256 Mbit x 16, 1.25nS, 1.35V, 0-85C | Micron | MT41K256M16TW-107:P | Preferred
 |  |  |  |  |  | Micron | MT41K256M16HA-125:E | Preferred
 |  |  |  |  |  | Kingston Technology Co. | D2516EC4BXGGB-U | Alternate Source
 |  |  |  |  |  | Nanya Technology Corp. | NT5CC256M16DP-DI | Alternate Source
 |  |  |  |  |  | Nanya Technology Corp. | NT5CC256M16CP-DI | EOL
 |  |  |  |  |  | Kingston Technology Co. | D2516EC4BXGGB | Obsolete
135 | 1 | 4460-0076 |  | CPU1 | IC, PROCESSOR, ATOM E3826 SOC, 1.46 GHZ, 2 CORE, DO STEP | Intel | FH8065301542215SR1X | Preferred
 |  |  |  |  |  | Intel | FH8065301542215 | Preferred
136 | 2 | 4532-0011 |  | Q2,Q9 | DIODE, DUAL SWITCHING, COM-CATHODE, 75V, 300MA | Diodes Inc. | BAV99-7-F | Preferred
137 | 3 | 4536-0009 |  | D5,D8,D10 | DIODE, SCHOTTKY, DUAL, COM-CATHODE, 30V, 200MA, LOW VF | NXP | BAT754C T/R | Preferred
138 | 5 | 4536-1002 |  | D3,D4,D6,D11,D12 | DIODE, SCHOTTKY, DUAL, COM-ANODE, 30V, 200MA | ON Semiconductor | BAT54ALT1G | Preferred
 |  |  |  |  |  | Diodes Inc. | BAT54A-7-F | Preferred
139 | 2 | 4560-0045 |  | D1,D2 | LED, SM, BLUE, 0603, RT ANGLE | LiteOn USA, Inc. | LTST-S270TBKT | Preferred
 |  |  |  |  |  | Everlight | 27-21/BHC-AP1Q2 /3C | Preferred
140 | 1 | 4620-0026 |  | D13 | DIODE, SM, ZENER, 4.3V, 200mW | ON Semiconductor | MM3Z4V3ST1G | Preferred
141 | 1 | 4720-1002 |  | Q4 | TRANSISTOR, NPN, SWITCHING, 40V, 200mA, 225mW | NXP | PMBT3904 | Preferred
 |  |  |  |  |  | ON Semiconductor | MMBT3904LT1G | Preferred
 |  |  |  |  |  | Fairchild Semiconductor | MMBT3904 | Preferred
142 | 2 | 4760-0005 |  | Q1,Q3 | TRANSISTOR, DUAL NPN, SWITCHING, 40V, 200mA | ON Semiconductor | MBT3904DW1T1G | Preferred
143 | 1 | 4820-0069 |  | Q105 | MOSFET, N CHANNEL, 20V, 2A, 120 mOHM @ 1.8 VGS | Fairchild Semiconductor | FDN327N | Preferred
144 | 2 | 4820-0071 |  | Q103,Q104 | MOSFET, N CHANNEL, 30V, 15.3A, 12mOHM | Vishay Siliconix | SISA18ADN-T1-GE3 | Preferred
145 | 3 | 4820-0073 |  | Q5,Q6,Q13 | MOSFET, N CHANNEL, 30V, 3.5A | Vishay Siliconix | Si2300DS-T1-GE3 | Preferred
 |  |  |  |  |  | Rohm | RXR035N03TCL | Preferred
146 | 6 | 4820-1004 |  | Q7,Q10,Q11,Q12,Q14,Q101 | MOSFET, N CHANNEL, 60V, 115mA | ON Semiconductor | 2N7002LT1G | Preferred
 |  |  |  |  |  | Diodes Inc. | 2N7002-7-F | Preferred
 |  |  |  |  |  | Fairchild Semiconductor | 2N7002_NL | Preferred
147 | 1 | 4840-0022 |  | U36 | MOSFET, P CHANNEL, 30V, 15A, 7.2mOHM | IR | IRF9321TRPBF | Preferred
148 | 1 | 4840-1002 |  | Q106 | MOSFET, P CHANNEL, 50V, 130mA | Fairchild Semiconductor | BSS84 | Preferred
 |  |  |  |  |  | ON Semiconductor | BSS84LT1G | Preferred
 |  |  |  |  |  | Diodes Inc. | BSS84-7-F | Preferred
149 | 1 | 4860-0031 |  | Q102 | MOSFET, DUAL N CHANNEL W/SCHOTTKY, 30V, 13A/23A | Fairchild Semiconductor | FDMS3604S | Preferred
150 | 1 | 60800-0081-G00 | R402 | U3 | Flash IC Programmed Part Assy, Turbot_ BIOS, 8MB | ADI Engineering | 60800-0081-G00 | Preferred
1 | 1 | 4356-0059 |  |  | IC, 64 MBIT DUAL/QUAD SPI SERIAL FLASH, 2.7-3.6V, -40 to +85C | Winbond | W25Q64JVSSIM-TR | Preferred
 |  |  |  |  |  | Winbond | W25Q64FVSSIG | Preferred
 |  |  |  |  |  | Winbond | W25Q64FVSSIG-TR | EOL
 |  |  |  |  |  | Winbond | W25Q64BVSSIG | Obsolete
 |  |  |  |  |  | Winbond | W25Q64CVSSIG | Obsolete
2 | 1 | 60801-0081-G00 | R402 |  | Flash Program Image File, Turbot_ BIOS, 8MB | ADI Engineering | 60801-0081-G00 | Preferred
3 | 1 | 60802-0081-G00 | R402 |  | Flash Programming Instructions, Turbot_ BIOS, 8MB | ADI Engineering | 60802-0081-G00 | Preferred
151 | 1 | 92030-0007 |  | L11 | INDUCTOR, 1.0UH, 11A, SM | Abracon | ASPI-0630HI-1R0M-T15 | Preferred
152 | 1 | 92030-0009 |  | L3 | INDUCTOR, 2.2UH, 10A, 20%, SM | Cooper-Busssman Coiltronics | HCP0805-2R2-R | Preferred
153 | 1 | 92050-0019 |  | P2 | CONN, SM, MICRO SD CARD W DETECT SWITCH, RT ANG | Alps Electric Co., Ltd. | SCHA5B0200 | Preferred
154 | 1 | 92050-0022 |  | J10 | CONN, SM, 30X2, 0.8MM FH BOARD-BOARD RECEPTACLE, 5H, GOLD | TE Connectivity | 5177985-2 | Preferred
155 | 1 | 92050-0025 |  | USB1 | CONN, TH, USB A 2.0 TOP / USB A 3.0 BOT, DUAL, RT ANGLE | Foxconn | UEA1112C-UHS6-4F | Preferred
 |  |  |  |  |  | Link-PP International Technology | LPUSB1013 | Alternate Source
156 | 1 | 92050-0026 |  | J1 | CONN, TH, 4X2, 0.1X0.1 HEADER, VERTICAL, TIN | RSK | MEDA01-04T2002DTA | Preferred
 |  |  |  |  |  | Sullins | PREC004DAAN-RC | Alternate Source
 |  |  |  |  |  | Samtec | TSW-104-23-T-D | Alternate Source
 |  |  |  |  |  | RSK | MEDA01-04T2xxxDTA A=5.84, B=2.92 | Obsolete
157 | 1 | 92050-0028 |  | JP1 | CONN, TH, 2X13, 0.1X0.1 HEADER, 16MM HEIGHT, VERTICAL, TIN | RSK | MEDA02-13T2013TA | Preferred
 |  |  |  |  |  | Major League Electronics | BSTS-113-D-A-16-T-290-LF | Alternate Source
 |  |  |  |  |  | Adam Technologies, Inc. | DPH-2-26-T-.230/.110/.290 | Alternate Source
 |  |  |  |  |  | RSK | MEDA02-13T2xxxTA A=5.84,B=7.37,C=2.79 | Obsolete
158 | 1 | 92050-0029 |  | BH1 | BATTERY HOLDER, 12MM CELL, VERTICAL, TH | Memory Protection Devices | BS-1225-PC | Preferred
159 | 1 | 92060-0007 |  | Y1 | XTAL, 32.768KHz, 20 PPM, 12.5pF, LOW PROFILE | Transko | CS2012-A-32.768K-TR | Preferred
 |  |  |  |  |  | Abracon | ABS06-32.768KHZ-T | Preferred
160 | 1 | 92070-0045 |  | U2 | IC, HDMI COMPANION, I2C LEVEL SHIFT, ESD, LOAD SWITCH | TI | TPD12S016PWR | Preferred
161 | 1 | 92070-0046 |  | U13 | IC, REG, BUCK WITH LDO, 24V, 6A | Monolithic Power Systems | NB670GQ-Z | Preferred
162 | 1 | 92070-0047 |  | U35 | IC, SYSTEM POWER CONTROL | Nuvoton | NCT3012S TR | Preferred
163 | 1 | 92070-0050 |  | U38 | IC, LDO REG, ADJUSTABLE, 5A | Anpec Electronics Corp. | APL5912KAC-TRG | Preferred
164 | 2 | 92070-0051 |  | U21,U24 | IC, LDO REG, ADJUSTABLE, 3A | Anpec Electronics Corp. | APL5933AKAI-TRG | Preferred
165 | 1 | 92070-0052 |  | U1 | IC, BUFFER, LOW POWER, 0.8-3.6V | TI | SN74AUP1G34DBVR | Preferred
 |  |  |  |  |  | TI | SN74AUP1G34DBVRE4 | Preferred
166 | 1 | 92070-0053 |  | U20 | IC, LDO REG, ADJUSTABLE, 0.5A | ON Semiconductor | NCP606MNADJT2G | Preferred
167 | 2 | 92080-0004 |  | D7,D9 | TVS, UNIDIR, 5V, 84W, SMD | Diodes Inc. | D5V0L1B2LP-7B | Preferred
168 | 2 | 92080-0006 |  | U8,U9 | TVS, UNIDIR, DIODE COUPLED 10KV ESD CLAMP ARRAY, 4 LINE USB | TI | TPD4S012DRYR | Preferred
169 | 1 | 92080-0007 |  | U29 | TVS, UNIDIR, DIODE COUPLED 8KV ESD CLAMP ARRAY, 4 LINE USB3.0 | TI | TPD4EUSB30DQAR | Preferred
170 | 3 | 1120-0010 |  | R233,R289,R401 | RES, 0402, 1%, 1/16W, 1.00K | Rohm | MCR01MZPF1001 | Preferred |  | DNI
 |  |  |  |  |  | KOA SPEER | RK73H1ETTP1001F | Preferred
 |  |  |  |  |  | Panasonic | ERJ-2RKF1001X | Preferred
 |  |  |  |  |  | Yageo | RC0402FR-071KL | Preferred
 |  |  |  |  |  | Walsin Technology Corporation | WR04X1001FTL | Preferred
 |  |  |  |  |  | Venkel Ltd. | CR0402-16W-1001FT | Preferred
171 | 12 | 1120-0011 |  | R31,R55,R112,R114,R189,R209-210,R219,R260,R811,R829,R865 | RES, 0402, 1%, 1/16W, 10.0K | Rohm | MCR01MZPF1002 | Preferred |  | DNI
 |  |  |  |  |  | KOA SPEER | RK73H1ETTP1002F | Preferred
 |  |  |  |  |  | Panasonic | ERJ-2RKF1002X | Preferred
 |  |  |  |  |  | Yageo | RC0402FR-0710KL | Preferred
 |  |  |  |  |  | Walsin Technology Corporation | WR04X1002FTL | Preferred
 |  |  |  |  |  | Venkel Ltd. | CR0402-16W-1002FT | Preferred
172 | 2 | 1120-0032 |  | R847,R875 | RES, 0402, 1%, 1/16W, 3.01K | Rohm | MCR01MZPF3011 | Preferred |  | DNI
 |  |  |  |  |  | KOA SPEER | RK73H1ETTP3011F | Preferred
 |  |  |  |  |  | Panasonic | ERJ-2RKF3011X | Preferred
 |  |  |  |  |  | Yageo | RC0402FR-073K01L | Obsolete
 |  |  |  |  |  | Walsin Technology Corporation | WR04X3011FTL | Preferred
 |  |  |  |  |  | Venkel Ltd. | CR0402-16W-3011FT | Preferred
173 | 1 | 1120-0034 |  | R250 | RES, 0402, 1%, 1/16W, 75.0 | Rohm | MCR01MZPF75R0 | Preferred |  | DNI
 |  |  |  |  |  | KOA SPEER | RK73H1ETTP75R0F | Preferred
 |  |  |  |  |  | Panasonic | ERJ-2RKF75R0X | Preferred
174 | 1 | 1120-0103 |  | R161 | RES, 0402, 1%, 1/16W, 20.0K | Rohm | MCR01MZPF2002 | Preferred |  | DNI
 |  |  |  |  |  | KOA SPEER | RK73H1ETTP2002F | Preferred
 |  |  |  |  |  | Panasonic | ERJ-2RKF2002X | Preferred
 |  |  |  |  |  | Yageo | RC0402FR-0720KL | Preferred
 |  |  |  |  |  | Walsin Technology Corporation | WR04X2002FTL | Preferred
 |  |  |  |  |  | Venkel Ltd. | CR0402-16W-2002FT | Preferred
175 | 6 | 1120-0313 |  | R1,R53,R54,R56,R58,R115 | RES, 0402, 1%, 1/16W, 2.2K | Panasonic | ERJ-2RKF2201X | Preferred |  | DNI
 |  |  |  |  |  | Yageo | RC0402FR-072K2L | Preferred
 |  |  |  |  |  | Venkel Ltd. | CR0402-10W-2201FT | Preferred
176 | 1 | 1120-0322 |  | R110 | RES, 0402, 1%, 1/16W, 499K | Vishay-Dale | CRCW0402499KFKED | Preferred |  | DNI
 |  |  |  |  |  | KOA SPEER | RK73H1ETTP4993F | Preferred
 |  |  |  |  |  | Panasonic | ERJ-2RKF4993X | Preferred
 |  |  |  |  |  | Venkel Ltd. | CR0402-16W-4993FT | Preferred
177 | 1 | 1120-0328 |  | R4 | RES, 0402, 1%, 1/16W, 4.7K | Rohm | TRR01MZPF4701 | Preferred |  | DNI
 |  |  |  |  |  | KOA SPEER | RK73H1ETTP4701F | Preferred
 |  |  |  |  |  | Panasonic | ERJ-2RKF4701X | Preferred
 |  |  |  |  |  | Venkel Ltd. | CR0402-16W-4701FT | Preferred
178 | 4 | 1120-0330 |  | R85,R86,R87,R196 | RES, 0402, 1%, 1/16W, 69.8 | KOA SPEER | RK73H1ETTP69R8F | Preferred |  | DNI
 |  |  |  |  |  | Panasonic | ERJ-2RKF69R8X | Preferred
 |  |  |  |  |  | Vishay-Dale | CRCW040269R8FKED | Preferred
 |  |  |  |  |  | Venkel Ltd. | CR0402-16W-69R8FT | Preferred
179 | 1 | 1120-0361 |  | R141 | RES, 0402, 1%, 1/16W, 200K | Rohm | MCR01MZPF2003 | Preferred |  | DNI
 |  |  |  |  |  | KOA SPEER | RK73H1ETTP2003F | Preferred
 |  |  |  |  |  | Panasonic | ERJ-2RKF2003X | Preferred
 |  |  |  |  |  | Venkel Ltd. | CR0402-16W-2003FT | Preferred
180 | 3 | 1121-0001 |  | R121,R181,R235 | RES, 0402, ZERO OHM JUMPER | Panasonic | ERJ-2GE0R00X | Preferred |  | DNI
 |  |  |  |  |  | Rohm | MCR01MZPJ000 | Preferred
 |  |  |  |  |  | Venkel Ltd. | CR0402-16W-000T | Preferred
 |  |  |  |  |  | Yageo | RC0402JR-070RL | Preferred
 |  |  |  |  |  | Walsin Technology Corporation | WR04X000PTL | Preferred
181 | 1 | 1131-0001 |  | R818 | RES, 0603, ZERO OHM JUMPER | Panasonic | ERJ-3GEY0R00V | Preferred |  | DNI
 |  |  |  |  |  | Rohm | MCR03EZPJ000 | Preferred
 |  |  |  |  |  | Venkel Ltd. | CR0603-16W-000T | Preferred
182 | 1 | 1141-0014 |  | R145 | RES, 0805, ZERO OHM JUMPER | Panasonic | ERJ-6GEY0R00V | Preferred |  | DNI
 |  |  |  |  |  | Rohm | MCR10EZPJ000 | Preferred
 |  |  |  |  |  | Yageo | RC0805JR-070RL | Preferred
 |  |  |  |  |  | Venkel Ltd. | CR0805-8W-000T | Preferred
183 | 1 | 2220-0008 |  | C331 | CAP, Ceramic NPO, 0402, 3.3pF, +/-0.25pF, 50V | AVX | 04025A3R3CAT2A | Preferred |  | DNI
 |  |  |  |  |  | KEMET | C0402C339C5GACTU | Preferred
 |  |  |  |  |  | Murata | GRM1555C1H3R3CZ01 | Preferred
184 | 2 | 2220-0024 |  | C9,C23 | CAP, Ceramic NPO, 0402, 150pF, 5%, 50V | AVX | 04025A151JAT2A | Preferred |  | DNI
 |  |  |  |  |  | Panasonic | ECJ-0EC1H151J | EOL
185 | 2 | 2220-0026 |  | C69,C374 | CAP, Ceramic NPO, 0402, 10pF, 5%, 50V | AVX | 04025A100JAT2A | Preferred |  | DNI
 |  |  |  |  |  | Murata | GRM1555C1H100JA01D | Preferred
 |  |  |  |  |  | Murata | GRM1555C1H100JZ01D | EOL
 |  |  |  |  |  | Panasonic | ECJ-0EC1H100D | EOL
 |  |  |  |  |  | Venkel Ltd. | C0402C0G500-100JNP | Preferred
186 | 3 | 2221-0001 |  | C34,C61,C381 | CAP, Ceramic X7R, 0402, 1000pF, 10%, 50V | Yageo | CC0402KRX7R9BB102 | Preferred |  | DNI
 |  |  |  |  |  | Walsin | 0402B102K500CT | Preferred
 |  |  |  |  |  | AVX | 04025C102KAT2A | Preferred
 |  |  |  |  |  | Venkel Ltd. | C0402X7R500-102KNE | Preferred
 |  |  |  |  |  | Panasonic | ECJ-0EB1H102K | EOL
187 | 2 | 2221-0004 |  | C38,C104 | CAP, Ceramic X7R, 0402, 0.01uF, 10%, 16V | Yageo | CC0402KRX7R7BB103 | Preferred |  | DNI
 |  |  |  |  |  | Walsin | 0402B103K160CT | Preferred
 |  |  |  |  |  | AVX | 0402YC103KAT2A | Preferred
 |  |  |  |  |  | Venkel Ltd. | C0402X7R160-103KNE | Preferred
 |  |  |  |  |  | Panasonic | ECJ-0EB1C103K | EOL
188 | 1 | 2222-0014 |  | C33 | CAP, Ceramic X5R, 0402, 1.0uF, 10%, 25V | Murata | GRM155R61E105KA12D | Preferred |  | DNI
 |  |  |  |  |  | TDK | C1005X5R1E105K050BC | Preferred
 |  |  |  |  |  | Samsung Electro-Mechanics | CL05A105KA5NQNC | Preferred
 |  |  |  |  |  | Venkel Ltd. | C0402X5R250-105KNP | Preferred
189 | 6 | 2222-0016 |  | C85,C100,C112,C114,C290,C378 | CAP, Ceramic X5R, 0402, 0.1uF, 10%, 25V | AVX | 04023D104KAT2A | Preferred |  | DNI
 |  |  |  |  |  | Yageo | CC0402KRX5R8BB104 | Preferred
 |  |  |  |  |  | TDK | C1005X5R1E104K050BC | Preferred
 |  |  |  |  |  | Murata | GRM155R61E104KA87D | Preferred
 |  |  |  |  |  | Venkel Ltd. | C0402X5R250-104KNP | Preferred
190 | 1 | 2232-0016 |  | C157 | CAP, Ceramic X5R, 0603, 4.7uF, 10%, 16V | Samsung | CL10A475KO8NNNC | Preferred |  | DNI
 |  |  |  |  |  | Murata | GRM188R61C475KE11D | Preferred
 |  |  |  |  |  | HolyStone | C0603B475K016T | Preferred
 |  |  |  |  |  | TDK | C1608X5R1C475K080AC | Preferred
 |  |  |  |  |  | Venkel Ltd. | C0603X5R160-475KNP | Preferred
 |  |  |  |  |  | TDK | C1608X5R1C475K | EOL
191 | 6 | 2267-0004 |  | C148,C161,C169,C211,C233,C448 | CAP, Ceramic X7R, 1808, 1000pF, 10%, 3KV | AVX | 1808HC102KAT1A | Preferred |  | DNI
192 | 1 | 3044-0011 |  | FB8 | FERRITE BEAD, 0603, 1.3A, 600 OHM | Murata | BLM18KG601SN1D | Preferred |  | DNI
193 | 1 | 3430-0010 |  | J2 | CONN, TH, 2X1, 0.1 HEADER, FRICTION LOCK, VERTICAL | Tyco Electronics | 640456-2 | Preferred |  | DNI
194 | 1 | 4348-0002 |  | U33 | IC, EEPROM, 2 KBIT, 2 WIRE SER, WP UPPER HALF, -40 to +85 C | Atmel | AT24C02AN-10SI-2.7 | EOL |  | DNI
 |  |  |  |  |  | Atmel | AT24C02AN-10SU-2.7 | Preferred
 |  |  |  |  |  | Atmel | AT24HC02C-SSHM-T | Preferred
 |  |  |  |  |  | Atmel | AT24HC02C-SSHM | Preferred
195 | 2 | 4356-0082 |  | U43,U45 | IC, 8MBIT SPI SERIAL FLASH, 2.7-3.6V, -40 to +85 C | Adesto Technologies | AT25DF081A-SSH-T | Preferred |  | DNI
 |  |  |  |  |  | Adesto Technologies | AT25SF081-SSHD-T | Preferred
 |  |  |  |  |  | Adesto Technologies | AT25DF081A-SSH-B | Preferred
