MinnowBoard-org/design-files/minnowboard-v1/rev-a/MinnowBoard_RevA_MFG/Minnow_RevA_XY.xlsx

Design Name C:/Cadwork/Circuitco_Minnow_RevA/Minnow_RevA_No_Logo.brd
Date Wed Aug 14 11:44:06 2013
Total Components: &nbsp1073
Component Report
REFDES | COMP_DEVICE_TYPE | COMP_VALUE | COMP_TOL | COMP_PACKAGE | SYM_X | SYM_Y | SYM_ROTATE | SYM_MIRROR
BH1 | BATTERY_2_BATT3_190X610_BATT HO | BATT HOLDER, BS-1225-PC |  | BATT3_190X610 | 1050 | 140 | 0 | YES
C1 | CAP NP_0805_10UF | 10uF |  | 805 | 1000 | 4000 | 180 | NO
C2 | CAP NP_0805_10UF | 10uF |  | 805 | 1600 | 4000 | 0 | NO
C3 | CAP 0603 0_0.1UF/25V_0603_0.1UF | 0.1uF |  | 603 | 2060 | 4025 | 90 | NO
C4 | CAP NP_0_1808_8200PF | 8200pF |  | 1808 | 2155 | 4060 | 90 | NO
C5 | CAP NP_0_1808_150PF | 150pF |  | 1808 | 2400 | 4060 | 90 | NO
C6 | CAP NP_0402_1UF | 1uF |  | 402 | 525 | 3975 | 270 | NO
C7 | CAP NP_0402_2700PF | 2700pF |  | 402 | 1000 | 3825 | 180 | NO
C8 | CAP NP_0402_0.1UF | 0.1uF |  | 402 | 1600 | 3925 | 0 | NO
C9 | CAP_0.1UF_X5R_6.3V_20% 0201 _04 | 0.1uf |  | 402 | 1800 | 3860 | 90 | NO
C10 | CAP NP_0603_4.7UF | 4.7uF |  | 603 | 2400 | 3825 | 90 | NO
C11 | CAPACITOR POL_4_3528_100UF | 100uF |  | 3528 | 2762.5 | 3850 | 90 | NO
C12 | CAPACITOR POL_4_3528_100UF | 100uF |  | 3528 | 3012.5 | 3850 | 90 | NO
C13 | CAP NP_0402_2700PF | 2700pF |  | 402 | 1000 | 3725 | 180 | NO
C14 | CAP NP_0402_0.1UF | 0.1uF |  | 402 | 1000 | 3675 | 180 | NO
C15 | CAP NP_0402_0.1UF | 0.1uF |  | 402 | 1600 | 3775 | 0 | NO
C16 | CAP NP_0402_2.2UF | 2.2uF |  | 402 | 1600 | 3675 | 0 | NO
C17 | CAP_0.1UF_X5R_6.3V_20% 0201 __2 | 1uF |  | 402 | 2200 | 3650 | 90 | NO
C18 | CAP NP_0402_1UF | 1uF |  | 402 | 1825 | 3500 | 270 | NO
C19 | CAP NP_0402_1UF | 1uF |  | 402 | 1925 | 3500 | 90 | NO
C20 | CAP NP_0603_4.7UF | 4.7uF |  | 603 | 2200 | 3500 | 90 | NO
C21 | CAP NP_0_1808_8200PF | 8200pF |  | 1808 | 4000 | 3550 | 180 | NO
C22 | CAP NP_0805_10UF | 10uF |  | 805 | 350 | 3350 | 90 | NO
C23 | CAP NP_0402_0.1UF | 0.1uF |  | 402 | 475 | 3350 | 90 | NO
C24 | CAP NP_0402_0.1UF | 0.1uF |  | 402 | 575 | 3350 | 90 | NO
C25 | CAP NP_0402_2.2UF | 2.2uF |  | 402 | 675 | 3350 | 90 | NO
C26 | CAP NP_0603_4.7UF | 4.7uF |  | 603 | 2200 | 3350 | 270 | NO
C27 | CAP_0.1UF_X5R_6.3V_20% 0201 _04 | 0.1uf |  | 402 | 2750 | 3200 | 90 | NO
C28 | CAP_0.1UF_X5R_6.3V_20% 0201 _04 | 0.1uf |  | 402 | 2875 | 3200 | 90 | NO
C29 | CAP_0.1UF_X5R_6.3V_20% 0201 _04 | 0.1uf |  | 402 | 2225 | 2975 | 0 | NO
C30 | CAP_0.1UF_X5R_6.3V_20% 0201 _04 | 0.1uf |  | 402 | 2225 | 2935 | 0 | NO
C31 | CAP_0.1UF_X5R_6.3V_20% 0201 _04 | 0.1uf |  | 402 | 2225 | 2815 | 0 | NO
C32 | CAP NP_0805_10UF | 10uF |  | 805 | 350 | 2750 | 270 | NO
C33 | CAP NP_0402_0.1UF | 0.1uF |  | 402 | 525 | 2750 | 270 | NO
C34 | CAP NP_0402_2700PF | 2700pF |  | 402 | 625 | 2750 | 270 | NO
C35 | CAP NP_0402_2700PF | 2700pF |  | 402 | 675 | 2750 | 270 | NO
C36 | CAP_0.1UF_X5R_6.3V_20% 0201 _04 | 0.1uf |  | 402 | 2225 | 2775 | 0 | NO
C37 | CAP_0.1UF_X5R_6.3V_20% 0201 _04 | 0.1uf |  | 402 | 2225 | 2735 | 0 | NO
C38 | CAP_0.1UF_X5R_6.3V_20% 0201 _04 | 0.1uf |  | 402 | 2225 | 2695 | 0 | NO
C39 | CAP_0.1UF_X5R_6.3V_20% 0201 _04 | 0.1uf |  | 402 | 2225 | 2655 | 0 | NO
C40 | CAP_0.1UF_X5R_6.3V_20% 0201 _04 | 0.1uf |  | 402 | 2225 | 2615 | 0 | NO
C41 | CAP NP_0805_10UF | 10uF |  | 805 | 650 | 2400 | 180 | NO
C42 | CAP_0.1UF_X5R_6.3V_20% 0201 _04 | 0.1uf |  | 402 | 2225 | 2575 | 0 | NO
C43 | CAP_0.1UF_X5R_6.3V_20% 0201 _04 | 0.1uf |  | 402 | 2225 | 2535 | 0 | NO
C44 | CAP_0.1UF_X5R_6.3V_20% 0201 _04 | 0.1uf |  | 402 | 2225 | 2495 | 180 | NO
C45 | CAP_0.1UF_X5R_6.3V_20% 0201 _04 | 0.1uf |  | 402 | 2225 | 2455 | 180 | NO
C46 | CAP NP_0402_0.1UF | 0.1uF |  | 402 | 2375 | 2575 | 180 | NO
C47 | CAP NP_0402_1UF | 1uF |  | 402 | 2375 | 2535 | 180 | NO
C48 | CAP NP_0402_0.1UF | 0.1uF |  | 402 | 800 | 2325 | 0 | NO
C49 | CAP NP_0402_100PF | 100pF |  | 402 | 800 | 2275 | 0 | NO
C50 | CAP NP_0402_1UF | 1uF |  | 402 | 1225 | 2125 | 270 | NO
C51 | CAP NP_0402_100PF | 100pF |  | 402 | 1575 | 2125 | 90 | NO
C52 | CAP_0.1UF_X5R_6.3V_20% 0201 _04 | 0.1uf |  | 402 | 2055 | 2125 | 270 | NO
C53 | CAP_0.1UF_X5R_6.3V_20% 0201 _04 | 0.1uf |  | 402 | 2095 | 2125 | 270 | NO
C54 | CAP_0.1UF_X5R_6.3V_20% 0201 _04 | 0.1uf |  | 402 | 2135 | 2125 | 270 | NO
C55 | CAP_0.1UF_X5R_6.3V_20% 0201 _04 | 0.1uf |  | 402 | 2175 | 2125 | 270 | NO
C56 | CAP NP_0402_1UF | 1uF |  | 402 | 1000 | 1650 | 90 | NO
C57 | CAP NP_0402_0.1UF | 0.1uF |  | 402 | 1775 | 1650 | 90 | NO
C58 | CAP POL_1206P_1UF, TANTALUM | 1uF, TANTALUM |  | 1206P | 1875 | 1650 | 90 | NO
C59 | CAP NP_0402_0.1UF | 0.1uF |  | 402 | 1950 | 1650 | 270 | NO
C60 | CAP NP_0402_0.1UF | 0.1uF |  | 402 | 2000 | 1650 | 270 | NO
C61 | CAP NP_0402_100PF | 100pF |  | 402 | 2050 | 1650 | 270 | NO
C62 | CAP NP_0402_0.1UF | 0.1uF |  | 402 | 2110 | 1650 | 90 | NO
C63 | CAP NP_0402_100PF | 100pF |  | 402 | 2150 | 1650 | 90 | NO
C64 | CAP NP_0402_100PF | 100pF |  | 402 | 2190 | 1650 | 90 | NO
C65 | CAP NP_0805_10UF | 10uF |  | 805 | 2700 | 1775 | 270 | NO
C66 | CAP NP_0805_10UF | 10uF |  | 805 | 2925 | 1775 | 270 | NO
C67 | CAP NP_0805_10UF | 10uF |  | 805 | 3025 | 1775 | 270 | NO
C68 | CAP NP_0805_10UF | 10uF |  | 805 | 3125 | 1775 | 270 | NO
C69 | CAP NP_0805_10UF | 10uF |  | 805 | 3350 | 1775 | 270 | NO
C70 | CAP NP_0805_10UF | 10uF |  | 805 | 3450 | 1775 | 270 | NO
C71 | CAP NP_0805_22UF | 22uF |  | 805 | 500 | 1550 | 180 | NO
C72 | CAP NP_0402_18PF | 18pF |  | 402 | 1325 | 1550 | 0 | NO
C73 | CAP NP_0402_0.1UF | 0.1uF |  | 402 | 1350 | 1400 | 0 | NO
C74 | CAP NP_0402_18PF | 18pF |  | 402 | 1405 | 1550 | 180 | NO
C75 | CAP NP_0402_20PF | 20pF |  | 402 | 1800 | 1510 | 180 | NO
C76 | CAP NP_0402_0.1UF | 0.1uF |  | 402 | 2725 | 1500 | 0 | NO
C77 | CAP NP_0402_0.1UF | 0.1uF |  | 402 | 2925 | 1500 | 0 | NO
C78 | CAP NP_0402_0.1UF | 0.1uF |  | 402 | 4015 | 1410 | 0 | NO
C79 | CAP NP_0805_10UF | 10uF |  | 805 | 700 | 1350 | 180 | NO
C80 | CAP NP_0402_1UF | 1uF |  | 402 | 700 | 1287.5 | 180 | NO
C81 | CAP NP_0805_10UF | 10uF |  | 805 | 700 | 1225 | 180 | NO
C82 | CAP NP_0805_10UF | 10uF |  | 805 | 700 | 1100 | 180 | NO
C83 | CAP NP_0402_0.1UF | 0.1uF |  | 402 | 700 | 1037.5 | 180 | NO
C84 | CAP NP_0402_0.1UF | 0.1uF |  | 402 | 1350 | 1150 | 0 | NO
C85 | CAP NP_0402_0.1UF | 0.1uF |  | 402 | 1350 | 1065 | 0 | NO
C86 | CAP NP_0402_20PF | 20pF |  | 402 | 1800 | 1190 | 180 | NO
C87 | CAP NP_0805_22UF | 22uF |  | 805 | 700 | 975 | 180 | NO
C88 | CAP NP_0805_10UF | 10uF |  | 805 | 700 | 875 | 180 | NO
C89 | CAP NP_0402_470PF | 470pF |  | 402 | 2937.5 | 875 | 270 | NO
C90 | CAP NP_0805_10UF | 10uF |  | 805 | 825 | 700 | 270 | NO
C91 | CAP NP_0805_22UF | 22uF |  | 805 | 1025 | 700 | 270 | NO
C92 | CAP NP_0805_22UF | 22uF |  | 805 | 1125 | 700 | 270 | NO
C93 | CAP NP_0402_470PF | 470pF |  | 402 | 2550 | 675 | 0 | NO
C94 | CAP NP_0402_0.1UF | 0.1uF |  | 402 | 2550 | 625 | 0 | NO
C95 | CAP NP_0402_470PF | 470pF |  | 402 | 2675 | 675 | 0 | NO
C96 | CAP NP_0402_0.1UF | 0.1uF |  | 402 | 2675 | 625 | 0 | NO
C97 | CAP NP_0402_0.1UF | 0.1uF |  | 402 | 2800 | 650 | 270 | NO
C98 | CAP NP_0402_0.1UF | 0.1uF |  | 402 | 2850 | 650 | 270 | NO
C99 | CAP NP_0402_0.1UF | 0.1uF |  | 402 | 2900 | 650 | 270 | NO
C100 | CAP NP_0402_0.01UF | 0.01uF |  | 402 | 3040 | 750 | 270 | NO
C101 | CAP NP_0402_0.1UF | 0.1uF |  | 402 | 3775 | 450 | 0 | NO
C102 | CAP NP_0402_0.1UF | 0.1uF |  | 402 | 3850 | 525 | 270 | NO
C103 | CAP_0.1UF_X5R_6.3V_20% 0201 _04 | 0.1uf |  | 402 | 975 | 325 | 90 | NO
C104 | CAP_2.2UF_X5R_6.3V_10%_0402_040 | 2.2uF |  | 402 | 1025 | 325 | 270 | NO
C105 | CAP_0.1UF_X5R_6.3V_20% 0201 _04 | 0.1uf |  | 402 | 1075 | 325 | 270 | NO
C106 | CAP_2.2UF_X5R_6.3V_10%_0402_040 | 2.2uF |  | 402 | 1125 | 325 | 270 | NO
C107 | CAP_0.1UF_X7R_16V_10% 0402 _040 | 47pF |  | 402 | 3230 | 250 | 90 | NO
C108 | CAP_0.1UF_X7R_16V_10% 0402 _040 | 47pF |  | 402 | 3280 | 250 | 90 | NO
C109 | CAP NP_0603_4.7UF | 4.7uF |  | 603 | 3330 | 250 | 270 | NO
C110 | CAP NP_0_1808_8200PF | 8200pF |  | 1808 | 1775 | 175 | 270 | NO
C111 | CAP NP_0_1808_8200PF | 8200pF |  | 1808 | 2625 | 175 | 270 | NO
C112 | CAP NP_0_1808_150PF | 150pF |  | 1808 | 3725 | 175 | 270 | NO
C113 | CAP NP_0_1808_8200PF | 8200pF |  | 1808 | 3785 | 4060 | 270 | YES
C114 | CAP NP_0402_0.1UF | 0.1uF |  | 402 | 3640 | 4090 | 0 | YES
C115 | CAP NP_0805_10UF | 10uF |  | 805 | 3510 | 4090 | 0 | YES
C116 | CAP NP_0402_0.1UF | 0.1uF |  | 402 | 1600 | 3825 | 180 | YES
C117 | CAP NP_0402_2700PF | 2700pF |  | 402 | 1000 | 3875 | 0 | YES
C118 | CAP_0.1UF_X5R_6.3V_20% 0201 __1 | 0.01uf |  | 402 | 3675 | 3450 | 0 | YES
C119 | CAP_0.1UF_X5R_6.3V_20% 0201 __1 | 0.01uf |  | 402 | 3675 | 3500 | 0 | YES
C120 | CAP_0402_47PF_COG_50V_0402_47NF | 47nF |  | 402 | 3100 | 3650 | 90 | YES
C121 | CAP_0402_47PF_COG_50V_0402_47NF | 47nF |  | 402 | 3050 | 3650 | 90 | YES
C122 | CAP_0.1UF_X7R_16V_10% 0402 _0_1 | 0.1uf |  | 402 | 3000 | 3650 | 270 | YES
C123 | CAP_0.1UF_X7R_16V_10% 0402 _0_1 | 0.1uf |  | 402 | 2950 | 3650 | 270 | YES
C124 | CAP_0.1UF_X5R_6.3V_20% 0201 _04 | 0.1uf |  | 402 | 2775 | 3650 | 270 | YES
C125 | CAP_0.1UF_X5R_6.3V_20% 0201 __2 | 1uF |  | 402 | 2725 | 3650 | 270 | YES
C126 | CAP_0.1UF_X5R_6.3V_20% 0201 __1 | 0.01uf |  | 402 | 2675 | 3650 | 270 | YES
C127 | CAP_0.1UF_X5R_6.3V_20% 0201 _04 | 0.1uf |  | 402 | 2625 | 3650 | 270 | YES
C128 | CAP_0.1UF_X5R_6.3V_20% 0201 _04 | 0.1uf |  | 402 | 2545 | 3650 | 270 | YES
C129 | CAP_0.1UF_X5R_6.3V_20% 0201 _04 | 0.1uf |  | 402 | 2465 | 3650 | 270 | YES
C130 | CAP_0.1UF_X5R_6.3V_20% 0201 _04 | 0.1uf |  | 402 | 2385 | 3650 | 270 | YES
C131 | CAP_0.1UF_X5R_6.3V_20% 0201 _04 | 0.1uf |  | 402 | 2200 | 3650 | 270 | YES
C132 | CAP_0.1UF_X5R_6.3V_20% 0201 __1 | 0.01uf |  | 402 | 2150 | 3650 | 270 | YES
C133 | CAP NP_0402_0.1UF | 0.1uF |  | 402 | 1600 | 3775 | 180 | YES
C134 | CAP NP_0402_0.1UF | 0.1uF |  | 402 | 1600 | 3725 | 180 | YES
C135 | CAP NP_0402_2.2UF | 2.2uF |  | 402 | 1600 | 3625 | 180 | YES
C136 | CAP NP_0402_0.1UF | 0.1uF |  | 402 | 1000 | 3775 | 0 | YES
C137 | CAP NP_0402_2700PF | 2700pF |  | 402 | 1000 | 3625 | 0 | YES
C138 | CAP_0.1UF_X5R_6.3V_20% 0201 __1 | 0.01uf |  | 402 | 3675 | 3600 | 0 | YES
C139 | CAP_0.1UF_X5R_6.3V_20% 0201 __1 | 0.01uf |  | 402 | 3675 | 3650 | 0 | YES
C140 | CAP NP_0402_1UF | 1uF |  | 402 | 2950 | 3550 | 270 | YES
C141 | CAP_0402_47PF_COG_50V_0402_47NF | 47nF |  | 402 | 2875 | 3450 | 90 | YES
C142 | CAP_0.1UF_X7R_16V_10% 0402 _0_1 | 0.1uf |  | 402 | 2825 | 3550 | 90 | YES
C143 | CAP_0402_47PF_COG_50V_0402_47NF | 47nF |  | 402 | 2775 | 3550 | 270 | YES
C144 | CAP_0.1UF_X5R_6.3V_20% 0201 __1 | 0.01uf |  | 402 | 2650 | 3550 | 90 | YES
C145 | CAP_0.1UF_X5R_6.3V_20% 0201 _04 | 0.1uf |  | 402 | 2650 | 3450 | 270 | YES
C146 | CAP_0.1UF_X5R_6.3V_20% 0201 _04 | 0.1uf |  | 402 | 2600 | 3550 | 90 | YES
C147 | CAP_0.1UF_X5R_6.3V_20% 0201 _04 | 0.1uf |  | 402 | 2600 | 3450 | 270 | YES
C148 | CAP_0.1UF_X5R_6.3V_20% 0201 __3 | 100pF |  | 402 | 2550 | 3550 | 90 | YES
C149 | CAP_0.1UF_X5R_6.3V_20% 0201 __1 | 0.01uf |  | 402 | 2500 | 3550 | 90 | YES
C150 | CAP_0.1UF_X5R_6.3V_20% 0201 _04 | 0.1uf |  | 402 | 2450 | 3550 | 90 | YES
C151 | CAP_0.1UF_X5R_6.3V_20% 0201 __3 | 100pF |  | 402 | 2400 | 3450 | 90 | YES
C152 | CAP_0.1UF_X5R_6.3V_20% 0201 __1 | 0.01uf |  | 402 | 2350 | 3550 | 90 | YES
C153 | CAP_0.1UF_X5R_6.3V_20% 0201 _04 | 0.1uf |  | 402 | 2300 | 3550 | 90 | YES
C154 | CAP_0.1UF_X5R_6.3V_20% 0201 _04 | 0.1uf |  | 402 | 2200 | 3500 | 270 | YES
C155 | CAP_0.1UF_X5R_6.3V_20% 0201 __1 | 0.01uf |  | 402 | 2150 | 3500 | 270 | YES
C156 | CAP NP_0402_12PF | 12pF |  | 402 | 1690 | 3525 | 180 | YES
C157 | CAP NP_0402_12PF | 12pF |  | 402 | 1690 | 3475 | 180 | YES
C158 | CAP NP_0402_1UF | 1uF |  | 402 | 3150 | 3350 | 90 | YES
C159 | CAP_0.1UF_X7R_16V_10% 0402 _0_1 | 0.1uf |  | 402 | 2875 | 3350 | 90 | YES
C160 | CAP NP_0603_4.7UF | 4.7uF |  | 603 | 2675 | 3200 | 90 | YES
C161 | CAP_0.1UF_X5R_6.3V_20% 0201 __3 | 100pF |  | 402 | 2650 | 3350 | 270 | YES
C162 | CAP_0.1UF_X5R_6.3V_20% 0201 __1 | 0.01uf |  | 402 | 2600 | 3350 | 270 | YES
C163 | CAP_0.1UF_X5R_6.3V_20% 0201 __2 | 1uF |  | 402 | 2600 | 3200 | 90 | YES
C164 | CAP_0.1UF_X5R_6.3V_20% 0201 _04 | 0.1uf |  | 402 | 2550 | 3350 | 270 | YES
C165 | CAP_0.1UF_X5R_6.3V_20% 0201 __3 | 100pF |  | 402 | 2450 | 3350 | 90 | YES
C166 | CAP_0.1UF_X5R_6.3V_20% 0201 __1 | 0.01uf |  | 402 | 2400 | 3350 | 90 | YES
C167 | CAP_0.1UF_X5R_6.3V_20% 0201 _04 | 0.1uf |  | 402 | 2350 | 3350 | 90 | YES
C168 | CAP NP_0402_1UF | 1uF |  | 402 | 2100 | 3225 | 180 | YES
C169 | CAP NP_0402_1UF | 1uF |  | 402 | 1975 | 3250 | 270 | YES
C170 | CAP NP_0402_1UF | 1uF |  | 402 | 1925 | 3250 | 270 | YES
C171 | CAP NP_0402_2.2UF | 2.2uF |  | 402 | 725 | 3350 | 270 | YES
C172 | CAP NP_0402_0.1UF | 0.1uF |  | 402 | 625 | 3350 | 270 | YES
C173 | CAP NP_0402_0.1UF | 0.1uF |  | 402 | 525 | 3350 | 270 | YES
C174 | CAP POL_1411_THT_47UF | 47uF |  | 1411_THT | 3350 | 3025 | 180 | YES
C175 | CAP POL_1411_THT_47UF | 47uF |  | 1411_THT | 3000 | 3025 | 180 | YES
C176 | CAP NP_0402_0.1UF | 0.1uF |  | 402 | 2225 | 3025 | 0 | YES
C177 | CAP NP_0402_0.1UF | 0.1uF |  | 402 | 2100 | 3175 | 180 | YES
C178 | CAP NP_0402_1UF | 1uF |  | 402 | 2100 | 3125 | 0 | YES
C179 | CAP NP_0402_0.1UF | 0.1uF |  | 402 | 3150 | 2900 | 90 | YES
C180 | CAP_0.1UF_X5R_6.3V_20% 0201 __1 | 0.01uf |  | 402 | 3095 | 2900 | 90 | YES
C181 | CAP_0.1UF_X5R_6.3V_20% 0201 __1 | 0.01uf |  | 402 | 3055 | 2900 | 90 | YES
C182 | CAP_0.1UF_X5R_6.3V_20% 0201 __1 | 0.01uf |  | 402 | 3015 | 2900 | 90 | YES
C183 | CAP_0.1UF_X5R_6.3V_20% 0201 __1 | 0.01uf |  | 402 | 2975 | 2900 | 90 | YES
C184 | CAP NP_0402_0.1UF | 0.1uF |  | 402 | 2912.5 | 2900 | 90 | YES
C185 | CAP NP_0402_820PF | 820pF |  | 402 | 2800 | 2900 | 90 | YES
C186 | CAP NP_0805_22UF | 22uF |  | 805 | 2525 | 2895 | 180 | YES
C187 | CAP NP_0402_1UF | 1uF |  | 402 | 2375 | 2825 | 180 | YES
C188 | CAP_0.1UF_X5R_6.3V_20% 0201 _04 | 0.1uf |  | 402 | 2100 | 2865 | 180 | YES
C189 | CAP_0.1UF_X5R_6.3V_20% 0201 _04 | 0.1uf |  | 402 | 2100 | 2825 | 180 | YES
C190 | CAP NP_0402_0.1UF | 0.1uF |  | 402 | 1822.8 | 2928.24 | 270 | YES
C191 | CAP NP_0402_1UF | 1uF |  | 402 | 1778.24 | 2928.24 | 270 | YES
C192 | CAP NP_0402_0.1UF | 0.1uF |  | 402 | 1733.68 | 2928.24 | 270 | YES
C193 | CAP NP_0402_1UF | 1uF |  | 402 | 1689.12 | 2928.24 | 270 | YES
C194 | CAP NP_0402_1UF | 1uF |  | 402 | 1644.56 | 2928.24 | 270 | YES
C195 | CAP NP_0402_1UF | 1uF |  | 402 | 1600 | 2928.24 | 270 | YES
C196 | CAP NP_0402_1UF | 1uF |  | 402 | 1555.44 | 2928.24 | 270 | YES
C197 | CAP NP_0402_1UF | 1uF |  | 402 | 1510.88 | 2928.24 | 270 | YES
C198 | CAP NP_0402_1UF | 1uF |  | 402 | 1466.32 | 2928.24 | 270 | YES
C199 | CAP NP_0402_1UF | 1uF |  | 402 | 1421.76 | 2928.24 | 270 | YES
C200 | CAP NP_0402_1UF | 1uF |  | 402 | 1377.2 | 2928.24 | 270 | YES
C201 | CAP NP_0402_1UF | 1uF |  | 402 | 1332.64 | 2928.24 | 270 | YES
C202 | CAP NP_0402_820PF | 820pF |  | 402 | 3409.645 | 2793.7 | 270 | YES
C203 | CAP NP_0402_2.2UF | 2.2uF |  | 402 | 3330.905 | 2793.7 | 270 | YES
C204 | CAP NP_0402_2.2UF | 2.2uF |  | 402 | 3252.165 | 2793.7 | 270 | YES
C205 | CAP NP_0402_200PF | 200pF |  | 402 | 3291.535 | 2675.59 | 90 | YES
C206 | CAP NP_0402_2.2UF | 2.2uF |  | 402 | 3252.165 | 2675.59 | 90 | YES
C207 | CAP NP_0402_0.1UF | 0.1uF |  | 402 | 3212.795 | 2675.59 | 90 | YES
C208 | CAP NP_0402_200PF | 200pF |  | 402 | 3212.795 | 2793.7 | 270 | YES
C209 | CAP NP_0402_0.1UF | 0.1uF |  | 402 | 3173.425 | 2675.59 | 270 | YES
C210 | CAP NP_0402_0.1UF | 0.1uF |  | 402 | 3134.055 | 2793.7 | 90 | YES
C211 | CAP NP_0402_0.1UF | 0.1uF |  | 402 | 3134.055 | 2675.59 | 270 | YES
C212 | CAP NP_0402_820PF | 820pF |  | 402 | 3094.685 | 2793.7 | 90 | YES
C213 | CAP NP_0402_2.2UF | 2.2uF |  | 402 | 3055.315 | 2793.7 | 270 | YES
C214 | CAP NP_0402_0.1UF | 0.1uF |  | 402 | 3055.315 | 2675.59 | 90 | YES
C215 | CAP NP_0402_0.1UF | 0.1uF |  | 402 | 3015.945 | 2793.7 | 270 | YES
C216 | CAP NP_0402_0.1UF | 0.1uF |  | 402 | 3015.945 | 2675.59 | 270 | YES
C217 | CAP NP_0402_0.1UF | 0.1uF |  | 402 | 2976.575 | 2793.7 | 270 | YES
C218 | CAP NP_0402_2.2UF | 2.2uF |  | 402 | 2976.575 | 2675.59 | 90 | YES
C219 | CAP NP_0402_2.2UF | 2.2uF |  | 402 | 2937.205 | 2793.7 | 270 | YES
C220 | CAP NP_0402_0.1UF | 0.1uF |  | 402 | 2937.205 | 2675.59 | 90 | YES
C221 | CAP NP_0402_0.1UF | 0.1uF |  | 402 | 2897.835 | 2793.7 | 90 | YES
C222 | CAP NP_0402_200PF | 200pF |  | 402 | 2897.835 | 2675.59 | 90 | YES
C223 | CAP NP_0402_2.2UF | 2.2uF |  | 402 | 2858.465 | 2793.7 | 270 | YES
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
C411 | CAP NP_0402_0.1UF | 0.1uF |  | 402 | 2200 | 700 | 270 | YES
C412 | CAP_0.1UF_X7R_16V_10% 0402 _0_1 | 0.1uf |  | 402 | 3350 | 425 | 270 | YES
C413 | CAP_0.1UF_X7R_16V_10% 0402 _0_1 | 0.1uf |  | 402 | 3200 | 425 | 270 | YES
C414 | CAP NP_0402_0.1UF | 0.1uF |  | 402 | 2250 | 500 | 270 | YES
C415 | CAP NP_0402_0.1UF | 0.1uF |  | 402 | 2200 | 500 | 270 | YES
C417 | CAP POL_220UF_RD205SMD_THT_250D | 220uF |  | RD205SMD_THT_250D | 950 | 575 | 90 | YES
C418 | CAP POL_220UF_RD205SMD_THT_250D | 220uF |  | RD205SMD_THT_250D | 675 | 575 | 90 | YES
C419 | CAP_470PF_X7R_25V_10%_0402_04_1 | 470pF |  | 402 | 400 | 500 | 90 | YES
C420 | CAP_0.1UF_X5R_6.3V_20% 0201 _04 | 0.1uf |  | 402 | 250 | 500 | 90 | YES
C421 | CAP_2.2UF_X5R_6.3V_10%_0402_040 | 2.2uF |  | 402 | 200 | 500 | 90 | YES
C422 | CAP_2.2UF_X5R_6.3V_10%_0402_040 | 2.2uF |  | 402 | 150 | 500 | 90 | YES
C423 | CAP NP_0402_0.1UF | 0.1uF |  | 402 | 3300 | 980 | 270 | YES
C424 | CAP NP_0402_0.1UF | 0.1uF |  | 402 | 3350 | 760 | 90 | YES
C1043 | CAP NP_0402_0.1UF | 0.1uF |  | 402 | 4075 | 1000 | 270 | YES
C1044 | CAP NP_0402_1UF | 1uF |  | 402 | 4000 | 600 | 90 | YES
D1 | DIODE_7_SOD-123_SCS0520P | SCS0520P |  | SOD-123 | 1850 | 4025 | 90 | NO
D2 | PGB0010603MR_F603-41X39_PGB0010 | PGB0010603MR |  | F603-41X39 | 2737.5 | 4100 | 270 | NO
D3 | PGB0010603MR_F603-41X39_PGB0010 | PGB0010603MR |  | F603-41X39 | 2837.5 | 4100 | 270 | NO
D4 | PGB0010603MR_F603-41X39_PGB0010 | PGB0010603MR |  | F603-41X39 | 2937.5 | 4100 | 270 | NO
D5 | PGB0010603MR_F603-41X39_PGB0010 | PGB0010603MR |  | F603-41X39 | 3037.5 | 4100 | 270 | NO
D6 | 1/4M8.2Z10_SOD123_146LS_MMSZ522 | MMSZ5226B-7-F |  | SOD123_146LS | 1825 | 3750 | 0 | NO
D7 | DIODE_SMCJ36CA_SMC_SMCJ5.0CA | SMCJ5.0CA |  | SMC | 200 | 600 | 270 | NO
D8 | DIODE_SMCJ36CA_SMC_MBRS410LT3G | MBRS410LT3G |  | SMC | 450 | 600 | 270 | NO
D9 | BAT54C/SOT_3_SOT23A_BAT54C, SOT | BAT54C, SOT23 |  | SOT23A | 1275 | 325 | 0 | NO
D10 | DIODE_DUAL_UMD3_RB717F | RB717F |  | UMD3 | 2860 | 3650 | 90 | YES
D11 | LED_LTST-S270GKT_0_LED_LTST-S27 | LTST-S270GKT |  | LED_LTST-S270GKT_RA | 4150 | 1750 | 90 | YES
D12 | LED_LTST-S270GKT_0_LED_LTST-S27 | LTST-S270GKT |  | LED_LTST-S270GKT_RA | 4150 | 1600 | 90 | YES
D13 | LED_LTST-S270GKT_0_LED_LTST-S27 | LTST-S270GKT |  | LED_LTST-S270GKT_RA | 4150 | 1450 | 90 | YES
D14 | LED_LTST-S270KRKT_2_LED_LTST-S2 | LTST-S270KRKT |  | LED_LTST-S270GKT_RA | 4150 | 1300 | 90 | YES
D15 | LED_LTST-S270GKT_0_LED_LTST-S27 | LTST-S270GKT |  | LED_LTST-S270GKT_RA | 4150 | 1150 | 90 | YES
F1 | KE32_3_1.15A_0603_0467002_NR_2A | 0467002_NR_2A_LF |  | 603 | 2000 | 4025 | 90 | NO
F2 | NANO-SMF_1206_0.75A (1206L075WR | 0.75A (1206L075WRT) |  | 1206 | 3100 | 600 | 90 | YES
FB1 | BEAD_0603_BEAD | BEAD |  | 603 | 2787.5 | 3025 | 270 | NO
FB2 | BEAD_0603_BEAD | BEAD |  | 603 | 3137.5 | 3025 | 270 | NO
FB3 | BEAD_0603_BEAD | BEAD |  | 603 | 2775 | 1775 | 90 | NO
FB4 | BEAD_0603_BEAD | BEAD |  | 603 | 3275 | 1775 | 270 | NO
FB5 | BEAD_0603_BEAD | BEAD |  | 603 | 1900 | 425 | 0 | NO
FB6 | FER_180_200_0805_SM-7351-IND-08 | 150OHM800mA |  | SM-7351-IND-0805 | 3150 | 3500 | 270 | YES
FB7 | FER_180_200_0805_SM-7351-IND-08 | 150OHM800mA |  | SM-7351-IND-0805 | 3025 | 3500 | 90 | YES
FB8 | BEAD_0603_BEAD | BEAD |  | 603 | 2525 | 2825 | 0 | YES
FB9 | BEAD_0603_BEAD | BEAD |  | 603 | 2525 | 2770 | 0 | YES
FB10 | BEAD_0603_BEAD | BEAD |  | 603 | 2525 | 2550 | 0 | YES
FB11 | BEAD_0603_BEAD | BEAD |  | 603 | 2525 | 2495 | 0 | YES
FB12 | BEAD_0603_BEAD | BEAD |  | 603 | 1775 | 1650 | 90 | YES
FB13 | BEAD_0603_BEAD | BEAD |  | 603 | 2075 | 1125 | 0 | YES
GH1 | TEST_PAD_0_TP135X185R_SMD_TEST_ | TEST_PAD_1 |  | TP135X185R_SMD | 450 | 2550 | 0 | NO
GH2 | TEST_PAD_0_TP135X185R_SMD_TEST_ | TEST_PAD_1 |  | TP135X185R_SMD | 3700 | 1275 | 0 | NO
GH3 | TEST_PAD_0_TP135X185R_SMD_TEST_ | TEST_PAD_1 |  | TP135X185R_SMD | 600 | 1725 | 0 | YES
GH4 | TEST_PAD_0_TP135X185R_SMD_TEST_ | TEST_PAD_1 |  | TP135X185R_SMD | 3200 | 925 | 0 | YES
J1 | CONN_HDMI_TYPEA_SMD_HDMIA_RA_HD | HDMIConnA |  | SMD_HDMIA_RA | 1985 | 3865 | 180 | YES
J2 | JUMPER_SIP2_JUMPER | JUMPER |  | SIP2 | 1850 | 3650 | 270 | YES
J3 | SATA_HEADER_RA_SATA_RA_04708040 | 470804005 |  | SATA_RA | 3776.378 | 3550 | 180 | YES
J4 | HEADER_4_SIP4_HEADER_4 | HEADER_4 |  | SIP4 | 3550 | 3450 | 0 | YES
J5 | JUMPER_SIP2_JUMPER | JUMPER |  | SIP2 | 3650 | 3250 | 0 | YES
J7 | CONN PCB 30X2_CONN60_ITP_XDP_VR | CONN_ITP_XDP |  | CONN60_ITP_XDP_VR | 225 | 2100 | 180 | YES
J8 | CONN SOCKET 50X2/SM_1_CON2X50SM | CONN PLUG 50x2/SM |  | CON2X50SMD_P8MMLS-1 | 3925 | 1975 | 270 | YES
J9 | HEADER 5X2_0_HDR2X5_HEADER 5X2 | HEADER 5X2 |  | HDR2X5 | 3575 | 1475 | 0 | YES
J10 | HEADER 3_1_SIP3_HEADER 3 | HEADER 3 |  | SIP3 | 3775 | 975 | 0 | YES
J11 | HEADER 4X2_1_HDR2X4_HEADER 4X2 | HEADER 4x2 |  | HDR2X4 | 3575 | 675 | 0 | YES
J12 | CONNECTORRJ45_GIGABIT_6605814-6 | RJ-45 Gigabit |  | 6605814-6 | 2000 | 600 | 0 | YES
J13 | JUMPER_SIP2_JUMPER | JUMPER |  | SIP2 | 800 | 300 | 90 | YES
J14 | CONN_MICROUSBAB_USB5_FCI-101035 | USB_MicroB |  | USB5_FCI-10103594 | 3725 | 230 | 270 | YES
J15 | CONN_PWRJACK_RAPC712_RAPC712_RA | RAPC712 |  | RAPC712 | 550 | 350 | 270 | YES
L1 | L_SMALL_0805_MLB_201209-0030P-N | MLB_201209-0030P-N1 |  | 805 | 1930 | 4025 | 270 | NO
L2 | PLW3216S_0_CHOKE_QTC24CG_EXC24C | EXC24CG900U |  | CHOKE_QTC24CG | 1963.345 | 3838.43 | 90 | NO
L3 | PLW3216S_0_CHOKE_QTC24CG_EXC24C | EXC24CG900U |  | CHOKE_QTC24CG | 2022.405 | 3838.43 | 90 | NO
L4 | PLW3216S_0_CHOKE_QTC24CG_EXC24C | EXC24CG900U |  | CHOKE_QTC24CG | 2081.455 | 3838.43 | 90 | NO
L5 | PLW3216S_0_CHOKE_QTC24CG_EXC24C | EXC24CG900U |  | CHOKE_QTC24CG | 2140.515 | 3838.43 | 90 | NO
L6 | FER_MMZ1608R301A_IND603-24X32_F | FERRITE, MMZ1608R301A |  | IND603-24X32 | 2475 | 3825 | 270 | NO
L7 | FER_MMZ1608R301A_IND603-24X32_F | FERRITE, MMZ1608R301A |  | IND603-24X32 | 2137.5 | 3650 | 270 | NO
L8 | FER_MMZ1608R301A_IND603-24X32_F | FERRITE, MMZ1608R301A |  | IND603-24X32 | 2137.5 | 3500 | 270 | NO
L9 | FER_MMZ1608R301A_IND603-24X32_F | FERRITE, MMZ1608R301A |  | IND603-24X32 | 2137.5 | 3350 | 90 | NO
L10 | FER_MMZ1608R301A_IND603-24X32_F | FERRITE, MMZ1608R301A |  | IND603-24X32 | 2600 | 3200 | 90 | NO
L11 | FER_MMZ1608R301A_IND603-24X32_F | FERRITE, MMZ1608R301A |  | IND603-24X32 | 2675 | 3200 | 90 | NO
L12 | INDUCTOR_IND2P9SMD_4SQ_4.7UH | 4.7uH |  | IND2P9SMD_4SQ | 825 | 1600 | 180 | NO
L13 | INDUCTOR_IND3P6SMD_4P9SQ_1.5UH | 1.5uH |  | IND3P6SMD_4P9SQ | 250 | 1425 | 0 | NO
L14 | INDUCTOR_IND3P6SMD_4P9SQ_1.5UH | 1.5uH |  | IND3P6SMD_4P9SQ | 250 | 1200 | 0 | NO
L15 | INDUCTOR_COIL5MMSMD_6SQ_1.5UH | 1.5uH |  | COIL5MMSMD_6SQ | 1575 | 1350 | 90 | NO
L16 | INDUCTOR_COIL5MMSMD_6SQ_1.5UH | 1.5uH |  | COIL5MMSMD_6SQ | 1575 | 1000 | 90 | NO
L17 | INDUCTOR_IND3P6SMD_4P9SQ_1.5UH | 1.5uH |  | IND3P6SMD_4P9SQ | 250 | 975 | 0 | NO
L18 | FER_MMZ1608R301A_IND603-24X32_F | FERRITE, MMZ1608R301A |  | IND603-24X32 | 2725 | 3550 | 270 | YES
L19 | INDUCTOR_IND2P75SMD_2P6X2P8_1UH | 1uH |  | IND2P75SMD_2P6X2P8 | 750 | 2575 | 270 | YES
L20 | INDUCTOR_IND3P4SMD_5SQ_1.8UH | 1.8uH |  | IND3P4SMD_5SQ | 2350 | 2345 | 270 | YES
L21 | INDUCTOR_1210_4.7UH | 4.7uH |  | 1210 | 1875 | 1650 | 90 | YES
MTG1 | MHOLE_MTGH200C125D_PL_MHOLE | MHOLE |  | MTGH200C125D_PL | 150 | 4050 | 0 | NO
MTG2 | MHOLE_MTGH200C125D_PL_MHOLE | MHOLE |  | MTGH200C125D_PL | 4050 | 4050 | 0 | NO
MTG3 | MHOLE_MTGH200C125D_PL_MHOLE | MHOLE |  | MTGH200C125D_PL | 150 | 150 | 0 | NO
MTG4 | MHOLE_MTGH200C125D_PL_MHOLE | MHOLE |  | MTGH200C125D_PL | 4050 | 150 | 0 | NO
P1 | MICROSD_CONN_8_SD-MICRO-SCHA5B0 | SCHA5B0200 |  | SD-MICRO-SCHA5B0300 | 3535 | 4012.41 | 180 | NO
P2 | CONN_STEREO_BLUE_CUI-SJ1-3515-S | SJ1-3515-SMT-TR-BE |  | CUI-SJ1-3515-SMT | 3160 | 4090 | 90 | YES
P3 | CONN_STEREO_GREEN_CUI-SJ1-3515- | SJ1-3515-SMT-TR-GR |  | CUI-SJ1-3515-SMT | 2625 | 4090 | 90 | YES
P4 | MINI-USB-AB-SOCKET_USB5MINI_4SH | mini USB-B |  | USB5MINI_4SHIELDED_SMD | 3255 | 250 | 270 | YES
P5 | CONN_54819-0578_0_USB_STACKED2_ | USB-A Conn. |  | USB_STACKED2 | 2757.1 | 456.2 | 0 | YES
Q1 | RN1907_SMINI6-F3-B_DMC56404 | DMC56404 |  | SMINI6-F3-B | 3837.5 | 1650 | 90 | NO
Q2 | RN1907_SMINI6-F3-B_DMC56404 | DMC56404 |  | SMINI6-F3-B | 4015 | 1200 | 0 | NO
Q3 | MOSFET_NCHAN_BSS138_SOT23_GSD_B | BSS138 |  | SOT23_GSD | 3100 | 1400 | 270 | YES
Q4 | MOSFET_NCHAN_BSS138_SOT23_GSD_B | BSS138 |  | SOT23_GSD | 2925 | 1400 | 270 | YES
Q5 | MOSFET_NCHAN_BSS138_SOT23_GSD_B | BSS138 |  | SOT23_GSD | 2750 | 1400 | 270 | YES
Q6 | MOSFET_NCHAN_BSS138_SOT23_GSD_B | BSS138 |  | SOT23_GSD | 2925 | 1200 | 270 | YES
Q7 | MOSFET_NCHAN_BSS138_SOT23_GSD_B | BSS138 |  | SOT23_GSD | 2750 | 1200 | 270 | YES
Q8 | RN1907_SMINI6-F3-B_DMC56404 | DMC56404 |  | SMINI6-F3-B | 3925 | 475 | 180 | YES
Q9 | MOSFET_PCHAN_DMG1013T_SOT23_GSD | DMG1013T |  | SOT23_GSD | 3775 | 575 | 0 | YES
R1 | RESISTOR_0402_56.2 | 56.2 |  | 402 | 525 | 4065 | 90 | NO
R2 | RESISTOR_0402_56.2 | 56.2 |  | 402 | 575 | 4065 | 90 | NO
R3 | RESISTOR_0402_56.2 | 56.2 |  | 402 | 625 | 4065 | 90 | NO
R4 | RESISTOR_0402_56.2 | 56.2 |  | 402 | 675 | 4065 | 90 | NO
R5 | RESISTOR_0402_56.2 | 56.2 |  | 402 | 285 | 3825 | 180 | NO
R6 | RESISTOR_0402_56.2 | 56.2 |  | 402 | 375 | 3825 | 180 | NO
R7 | RESISTOR_0402_56.2 | 56.2 |  | 402 | 575 | 3975 | 90 | NO
R8 | RESISTOR_0402_56.2 | 56.2 |  | 402 | 625 | 3975 | 90 | NO
R9 | RESISTOR_0402_56.2 | 56.2 |  | 402 | 725 | 3975 | 90 | NO
R10 | RESISTOR_0402_10K | 10K |  | 402 | 1600 | 3875 | 180 | NO
R11 | RESISTOR_0402_10K | 10K |  | 402 | 1600 | 3825 | 0 | NO
R12 | RESISTOR_0402_51K | 51K |  | 402 | 1850 | 3860 | 90 | NO
R13 | RES_4.75K_1/16W_1%_0402_0402_4. | 4.7K |  | 402 | 2862.5 | 3800 | 90 | NO
R14 | RES_4.75K_1/16W_1%_0402_0402_4. | 4.7K |  | 402 | 2912.5 | 3800 | 90 | NO
R15 | RESISTOR_0402_56.2 | 56.2 |  | 402 | 285 | 3775 | 180 | NO
R16 | RESISTOR_0402_56.2 | 56.2 |  | 402 | 375 | 3775 | 0 | NO
R17 | RESISTOR_0402_56.2 | 56.2 |  | 402 | 375 | 3725 | 180 | NO
R18 | RESISTOR_0402_56.2 | 56.2 |  | 402 | 375 | 3625 | 180 | NO
R19 | RESISTOR_0402_56.2 | 56.2 |  | 402 | 375 | 3575 | 180 | NO
R20 | RESISTOR_0402_39.2 | 39.2 |  | 402 | 375 | 3525 | 180 | NO
R21 | RESISTOR_0402_56.2 | 56.2 |  | 402 | 1000 | 3575 | 0 | NO
R22 | RESISTOR_0402_56.2 | 56.2 |  | 402 | 1000 | 3525 | 0 | NO
R23 | RESISTOR_0402_56.2 | 56.2 |  | 402 | 1000 | 3475 | 0 | NO
R24 | RESISTOR_0402_56.2 | 56.2 |  | 402 | 1000 | 3425 | 0 | NO
R25 | RESISTOR_0402_10K | 10K |  | 402 | 1575 | 3500 | 270 | NO
R26 | RESISTOR_0402_49.9 | 49.9 |  | 402 | 1625 | 3500 | 90 | NO
R27 | RESISTOR_0603_10M | 10M |  | 603 | 1700 | 3500 | 90 | NO
R28 | RESISTOR_0402_20K | 20K |  | 402 | 1875 | 3500 | 90 | NO
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
R455 | RESISTOR_0402_10K | 10K |  | 402 | 3500 | 875 | 90 | YES
R456 | RESISTOR_0402_10K | 10K |  | 402 | 2150 | 800 | 270 | YES
R457 | RESISTOR_0402_10K | 10K |  | 402 | 2100 | 800 | 270 | YES
R458 | RESISTOR_0402_0 | 0 |  | 402 | 1250 | 875 | 270 | YES
R459 | RESISTOR_0402_0 | 0 |  | 402 | 1200 | 875 | 270 | YES
R460 | RESISTOR_0402_0 | 0 |  | 402 | 850 | 875 | 270 | YES
R461 | RESISTOR_0402-S_0 | 0 |  | 0402-S | 750 | 875 | 90 | YES
R462 | RESISTOR_0805_0 | 0 |  | 805 | 500 | 875 | 0 | YES
R463 | RES_33_1/16W_5%_0402_0402_0 | 0 |  | 402 | 3300 | 625 | 90 | YES
R464 | RES_470_1/10W_5%_0402_0805_0 | 0 |  | 805 | 475 | 712.5 | 270 | YES
R465 | RES_4.75K_1/16W_1%_0402_0402_4. | 4.7K |  | 402 | 3350 | 525 | 270 | YES
R466 | RES_4.75K_1/16W_1%_0402_0402_0 | 0 |  | 402 | 3300 | 425 | 90 | YES
R467 | RES_4.75K_1/16W_1%_0402_0402_10 | 10K |  | 402 | 3250 | 425 | 90 | YES
R468 | RES_4.75K_1/16W_1%_0402_0402_1K | 1K |  | 402 | 3150 | 425 | 90 | YES
R469 | RES_33_1/16W_5%_0402_0402_27 | 27 |  | 402 | 3100 | 425 | 90 | YES
R470 | RES_33_1/16W_5%_0402_0402_27 | 27 |  | 402 | 3050 | 425 | 90 | YES
R471 | RES_470_1/10W_5%_0402_0402_470K | 470K |  | 402 | 350 | 500 | 90 | YES
R472 | RES_470_1/10W_5%_0402_0402_280K | 280K |  | 402 | 300 | 500 | 90 | YES
R473 | RESISTOR_0402_1K | 1K |  | 402 | 3825 | 2950 | 180 | NO
R474 | RESISTOR_0402_1K | 1K |  | 402 | 3825 | 2225 | 180 | NO
R475 | RESISTOR_0402_1K | 1K |  | 402 | 3825 | 1865 | 180 | NO
R476 | RESISTOR_0402_10K | 10K |  | 402 | 3900 | 375 | 270 | NO
R618 | RESISTOR_0402_1K | 1K |  | 402 | 3200 | 1500 | 0 | NO
R619 | RESISTOR_0402_1K | 1K |  | 402 | 3025 | 1425 | 270 | NO
R620 | RESISTOR_0402_1K | 1K |  | 402 | 2525 | 1425 | 270 | NO
R621 | RESISTOR_0402_0 | 0 |  | 402 | 3250 | 3520 | 90 | YES
R622 | RESISTOR_0402-S_0 | 0 |  | 0402-S | 3300 | 3520 | 270 | YES
R623 | RESISTOR_0402_1K | 1K |  | 402 | 4075 | 600 | 90 | YES
R624 | RESISTOR_0402_1K | 1K |  | 402 | 3925 | 600 | 90 | YES
R625 | RESISTOR_0402_1K | 1K |  | 402 | 3962.5 | 600 | 90 | YES
R626 | RESISTOR_0402_2.2K | 2.2K |  | 402 | 4037.5 | 600 | 270 | YES
R627 | RESISTOR_0402_1K | 1K |  | 402 | 3937.5 | 1000 | 270 | YES
R628 | RESISTOR_0402_1K | 1K |  | 402 | 3975 | 1000 | 270 | YES
R629 | RESISTOR_0402_10K | 10K |  | 402 | 4015 | 1460 | 180 | NO
RT1 | THERMISTOR_0805_PTC,0ZCE0010FF2 | PTC,0ZCE0010FF2G |  | 805 | 1775 | 4025 | 270 | NO
S1 | 3-POS SW_3_SW3SMD_D320000G_RA_T | TL3320AF100Q |  | SW3SMD_D320000G_RA | 3946.26 | 3000 | 90 | NO
S2 | 3-POS SW_3_SW3SMD_D320000G_RA_T | TL3320AF100Q |  | SW3SMD_D320000G_RA | 3946.26 | 2650 | 90 | NO
S3 | 3-POS SW_3_SW3SMD_D320000G_RA_T | TL3320AF100Q |  | SW3SMD_D320000G_RA | 3946.26 | 2300 | 90 | NO
S4 | 3-POS SW_3_SW3SMD_D320000G_RA_T | TL3320AF100Q |  | SW3SMD_D320000G_RA | 3946.26 | 1950 | 90 | NO
S5 | 3-POS SW_3_SW3SMD_D320000G_RA_T | TL3320AF100Q |  | SW3SMD_D320000G_RA | 3950 | 925 | 90 | NO
S6 | 3-POS SW_3_SW3SMD_D320000G_RA_T | TL3320AF100Q |  | SW3SMD_D320000G_RA | 3950 | 575 | 90 | NO
TP2 | TEST_PAD_1_TP40-SMT_TEST_PAD_1 | TEST_PAD_1 |  | TP40-SMT | 2000 | 3650 | 0 | NO
TP3 | TEST_PAD_1_TP40-SMT_TEST_PAD_1 | TEST_PAD_1 |  | TP40-SMT | 2070 | 3650 | 0 | NO
TP4 | TEST_PAD_1_TP40-SMT_TEST_PAD_1 | TEST_PAD_1 |  | TP40-SMT | 2775 | 3450 | 0 | NO
TP5 | TEST_PAD_1_TP40-SMT_TEST_PAD_1 | TEST_PAD_1 |  | TP40-SMT | 3300 | 3525 | 0 | NO
TP6 | TEST_PAD_1_TP40-SMT_TEST_PAD_1 | TEST_PAD_1 |  | TP40-SMT | 3300 | 3440 | 0 | NO
TP7 | TEST_PAD_1_TP40-SMT_TEST_PAD_1 | TEST_PAD_1 |  | TP40-SMT | 3375 | 3525 | 0 | NO
TP8 | TEST_PAD_1_TP40-SMT_TEST_PAD_1 | TEST_PAD_1 |  | TP40-SMT | 3375 | 3440 | 0 | NO
TP9 | TEST_PAD_1_TP40-SMT_TEST_PAD_1 | TEST_PAD_1 |  | TP40-SMT | 3450 | 3525 | 0 | NO
TP10 | TEST_PAD_1_TP40-SMT_TEST_PAD_1 | TEST_PAD_1 |  | TP40-SMT | 3450 | 3440 | 0 | NO
TP11 | TEST_PAD_1_TP40-SMT_TEST_PAD_1 | TEST_PAD_1 |  | TP40-SMT | 2975 | 3250 | 0 | NO
TP12 | TEST_PAD_1_TP40-SMT_TEST_PAD_1 | TEST_PAD_1 |  | TP40-SMT | 3050 | 3250 | 0 | NO
TP13 | TEST_PAD_1_TP40-SMT_TEST_PAD_1 | TEST_PAD_1 |  | TP40-SMT | 3125 | 3250 | 0 | NO
TP14 | TEST_PAD_1_TP40-SMT_TEST_PAD_1 | TEST_PAD_1 |  | TP40-SMT | 3300 | 3375 | 0 | NO
TP15 | TEST_PAD_1_TP40-SMT_TEST_PAD_1 | TEST_PAD_1 |  | TP40-SMT | 3300 | 3300 | 0 | NO
TP16 | TEST_PAD_1_TP40-SMT_TEST_PAD_1 | TEST_PAD_1 |  | TP40-SMT | 3375 | 3375 | 0 | NO
TP17 | TEST_PAD_1_TP40-SMT_TEST_PAD_1 | TEST_PAD_1 |  | TP40-SMT | 3375 | 3300 | 0 | NO
TP18 | TEST_PAD_1_TP40-SMT_TEST_PAD_1 | TEST_PAD_1 |  | TP40-SMT | 3450 | 3375 | 0 | NO
TP19 | TEST_PAD_1_TP40-SMT_TEST_PAD_1 | TEST_PAD_1 |  | TP40-SMT | 3450 | 3300 | 0 | NO
TP20 | TEST_PAD_1_TP40-SMT_TEST_PAD_1 | TEST_PAD_1 |  | TP40-SMT | 3650 | 3350 | 0 | NO
TP21 | TEST_PAD_1_TP40-SMT_TEST_PAD_1 | TEST_PAD_1 |  | TP40-SMT | 2975 | 3175 | 0 | NO
TP22 | TEST_PAD_1_TP40-SMT_TEST_PAD_1 | TEST_PAD_1 |  | TP40-SMT | 3050 | 3175 | 0 | NO
TP23 | TEST_PAD_1_TP40-SMT_TEST_PAD_1 | TEST_PAD_1 |  | TP40-SMT | 3125 | 3175 | 0 | NO
TP24 | TEST_PAD_1_TP40-SMT_TEST_PAD_1 | TEST_PAD_1 |  | TP40-SMT | 3525 | 1812.5 | 0 | NO
TP25 | TEST_PAD_1_TP40-SMT_TEST_PAD_1 | TEST_PAD_1 |  | TP40-SMT | 3525 | 1737.5 | 0 | NO
U1 | MT47H256M8_DDR2_FBGA60PIN_MT47H | MT47H256M8 |  | DDR2_FBGA60PIN | 1300 | 3750 | 180 | NO
U2 | SIL1162_0_QFP48S7X7P5LS7P87_SII | SII1362 |  | QFP48S7X7P5LS7P87 | 2475 | 3500 | 180 | NO
U3 | IC_TLV320AIC3104_0_QFP48S7X7P5L | ALC262 |  | QFP48S7X7P5LS7P87 | 3025 | 3500 | 180 | NO
U4 | MT47H256M8_DDR2_FBGA60PIN_MT47H | MT47H256M8 |  | DDR2_FBGA60PIN | 600 | 3050 | 270 | NO
U5 | INTEL_ATOM_PROCESSOR_E6XX_2_BGA | INTEL_ATOM_Processor_E6XX |  | BGA676_22X22_8MM_MPI_ISO_BKPLT | 1600 | 2750 | 90 | NO
U6 | PCH EG20T_BGA_376P_(S1+S2+S3+S4 | PCH EG20T |  | BGA_376P | 3075 | 2400 | 270 | NO
U7 | 74LVC1G08_0_SC70-5_74LVC1G07DCK | 74LVC1G07DCK |  | SC70-5 | 1925 | 1875 | 180 | NO
U8 | 74LVC1G08_0_SC70-5_74LVC1G07DCK | 74LVC1G07DCK |  | SC70-5 | 2075 | 1875 | 180 | NO
U9 | AR8031-AL1A_QFN48_QFN48S6X6P4_A | AR8031_AL1A |  | QFN48S6X6P4 | 2075 | 1350 | 0 | NO
U10 | TPS2054BD_SO16-25X75_TPS2054BD | TPS2054BD |  | SO16-25X75 | 2775 | 1300 | 180 | NO
U11 | W25Q64_SOIC8_260-1_W25Q32CV | W25Q32CV |  | SOIC8_260-1 | 3175 | 1300 | 270 | NO
U12 | SN74LVC1G06DCK_1_DCK5_SN74LVC1G | SN74LVC1G06 |  | DCK5 | 4015 | 1325 | 0 | NO
U13 | DA6011_1_BGA169_N13_P8_DA6011 | DA6011 |  | BGA169_N13_P8 | 1050 | 1175 | 90 | NO
U14 | TXS0104EPW_TSSOP14_TXS0104EPW | TXS0104EPW |  | TSSOP14 | 3525 | 875 | 270 | NO
U15 | SN74LVC1G06DCK_1_SOT23-5_SN74LV | SN74LVC1G14DBVR |  | SOT23-5 | 2100 | 750 | 180 | NO
U16 | SN74LVC1G06DCK_1_SOT23-5_SN74LV | SN74LVC1G14DBVR |  | SOT23-5 | 2240 | 750 | 180 | NO
U17 | TPS73633DBVT_1_SOT23-5_TPS73633 | TPS73633DBVR |  | SOT23-5 | 3005 | 625 | 0 | NO
U18 | 74LVC1G08_SOT23-5_74LVC1G08DBVR | 74LVC1G08DBVR |  | SOT23-5 | 2100 | 550 | 180 | NO
U19 | 74LVC1G08_SOT23-5_74LVC1G08DBVR | 74LVC1G08DBVR |  | SOT23-5 | 2240 | 550 | 180 | NO
U20 | PROT_TPD4S012_U_6_DRY_TPD4S012 | TPD4S012 |  | U_6_DRY | 2550 | 560 | 0 | NO
U21 | PROT_TPD4S012_U_6_DRY_TPD4S012 | TPD4S012 |  | U_6_DRY | 2675 | 560 | 0 | NO
U22 | FT232RL_1_SSOP16_025P_186_FT230 | FT230XS |  | SSOP16_025P_186 | 3200 | 525 | 180 | NO
U23 | PROT_TPD4S012_U_6_DRY_TPD4S012 | TPD4S012 |  | U_6_DRY | 3775 | 375 | 0 | NO
U24 | TPD6E001RSE_U_10_RSE_TPD6E001 | TPD6E001 |  | U_10_RSE | 3510 | 3970 | 90 | YES
U25 | TPD2E001DRL_U_5_DRL_TPD2E001 | TPD2E001 |  | U_5_DRL | 3510 | 3725 | 90 | YES
U26 | MT47H256M8_DDR2_FBGA60PIN_MT47H | MT47H256M8 |  | DDR2_FBGA60PIN | 1300 | 3750 | 180 | YES
U27 | MT47H256M8_DDR2_FBGA60PIN_MT47H | MT47H256M8 |  | DDR2_FBGA60PIN | 600 | 3050 | 270 | YES
U28 | LM95245_SSOP8_0256P_146_LM95245 | LM95245CIMM |  | SSOP8_0256P_146 | 725 | 2250 | 90 | YES
U29 | TPS22922_0_BGA6_C2_P5MM_TPS2292 | TPS22922 |  | BGA6_C2_P5MM | 1387.5 | 1975 | 90 | YES
U30 | 74LVC1G08_SOT23-5_74LVC1G08DBVR | 74LVC1G08DBVR |  | SOT23-5 | 2150 | 1650 | 180 | YES
U31 | SI7540DP_16_PWRPAK_SO-8_SI7540D | SI7540DP |  | PWRPAK_SO-8 | 250 | 1425 | 0 | YES
U32 | SI7540DP_16_PWRPAK_SO-8_SI7540D | SI7540DP |  | PWRPAK_SO-8 | 250 | 1200 | 0 | YES
U33 | SI7540DP_16_PWRPAK_SO-8_SI7540D | SI7540DP |  | PWRPAK_SO-8 | 250 | 975 | 0 | YES
U34 | PWR_TLV70233DBV_0_SO8-25X75_TL5 | TL5209 |  | SO8-25X75 | 250 | 687.5 | 90 | YES
U35 | TPS71718_DBV-5_TPS79318 | TPS79318 |  | DBV-5 | 1075 | 312.5 | 90 | YES
U36 | TXS0104EPW_TSSOP14_TXS0104EPW | TXS0104EPW |  | TSSOP14 | 3225 | 875 | 270 | NO
U37 | GTL2005_TSSOP14_GTL2005PW | GTL2005PW |  | TSSOP14 | 4000 | 800 | 270 | YES
Y1 | CRYSTAL_THT_14_3MHZ_HC-46X_ECS- | ECS-143-20-46X |  | HC-46X | 1365 | 1650 | 90 | NO
Y2 | CRYSTAL_SMT_14_3MHZ_ECX-53_ECS- | ECS-143-20-30-TR |  | ECX-53 | 1365 | 1650 | 0 | NO
Y3 | CRYSTAL_THT_25_0MHZ_HC-46X_ECS- | ECS-250-20-46X-TR |  | HC-46X | 1805 | 1350 | 0 | NO
Y4 | CRYSTAL_SMT_25_0MHZ_ECX-53_ECS- | ECS-250-20-30-TR |  | ECX-53 | 1805 | 1350 | 270 | NO
Y5 | CRYSTAL_THT_32_768KHZ_XTAL_CFS- | 32.768KHz, CITIZEN |  | XTAL_CFS-145 | 1750 | 3500 | 180 | YES
Y6 | CRYSTAL_SMT_32_768KHZ_2-SMD_32. | 32.768KHz, CITIZEN |  | 2-SMD | 1810 | 3500 | 90 | YES
