MinnowBoard-org/design-files/minnowboard-turbot-dual-core/pcb-f200-revX205_Turbot-A/STEPLibrary/0402C_V3.step

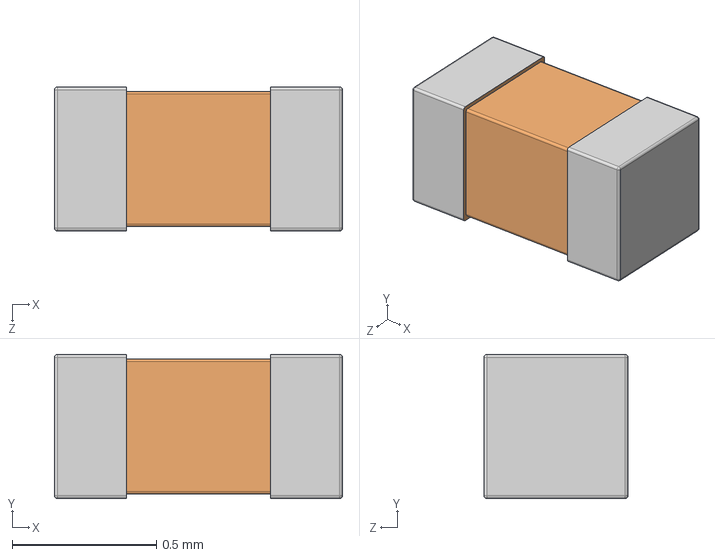
[picture p21: CAD file, 2017-04-18]
minnowboard-turbot-dual-core/pcb-f200-revX205_Turbot-A/STEPLibrary/0402C_V3.step
1.00 x 0.5 x 0.5 mm
