MinnowBoard-org/design-files/minnowboard-turbot-dual-core/pcb-f200-revX205_Turbot-A/Turbot_F200_X205_VX/PCB/Layout/3D/ImportedPartModels/QFN 405x5.STEP

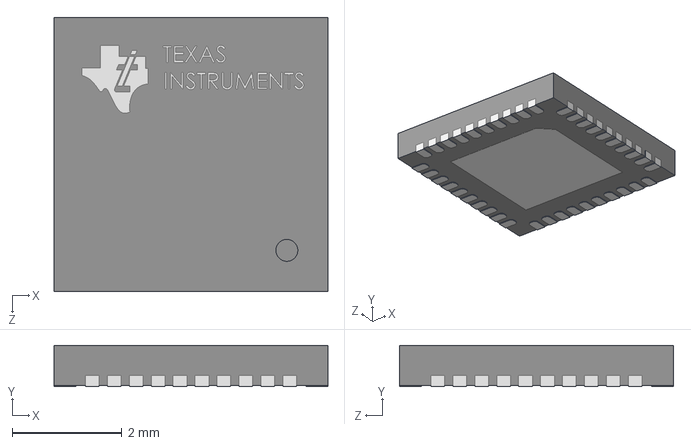
[picture p22: CAD file, 2017-04-18]
minnowboard-turbot-dual-core/pcb-f200-revX205_Turbot-A/Turbot_F200_X205_VX/PCB/Layout/3D/ImportedPartModels/QFN 405x5.STEP
5.00 x 0.75 x 5.00 mm
