MinnowBoard-org/design-files/minnowboard-turbot-dual-core/pcb-f200-revX205_Turbot-A/STEPLibrary/TSW-104-23-T-D.stp

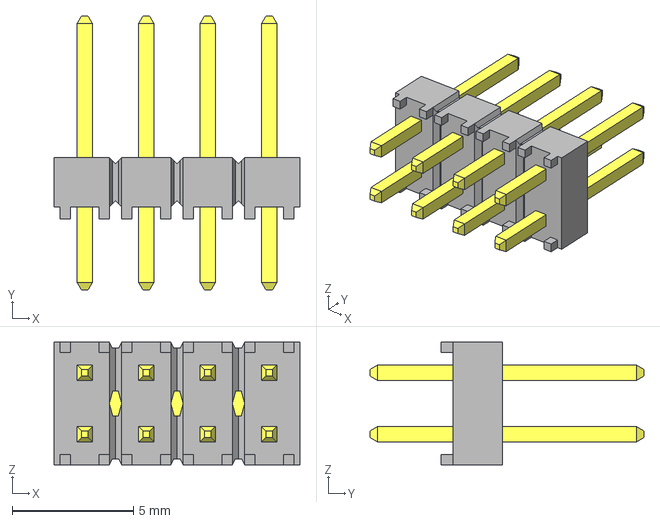
[picture p23: CAD file, 2017-04-18]
minnowboard-turbot-dual-core/pcb-f200-revX205_Turbot-A/STEPLibrary/TSW-104-23-T-D.stp
10.2 x 11.3 x 5.08 mm
_TSW-104-23-T-D_body
_T-1S6-16-TSW-1-23-4-D
