MinnowBoard-org/design-files/minnowboard-turbot-dual-core/pcb-f200-revX205_Turbot-A/Turbot_F200_X205_VX/PCB/Layout/3D/ImportedPartModels/FB0603.stp

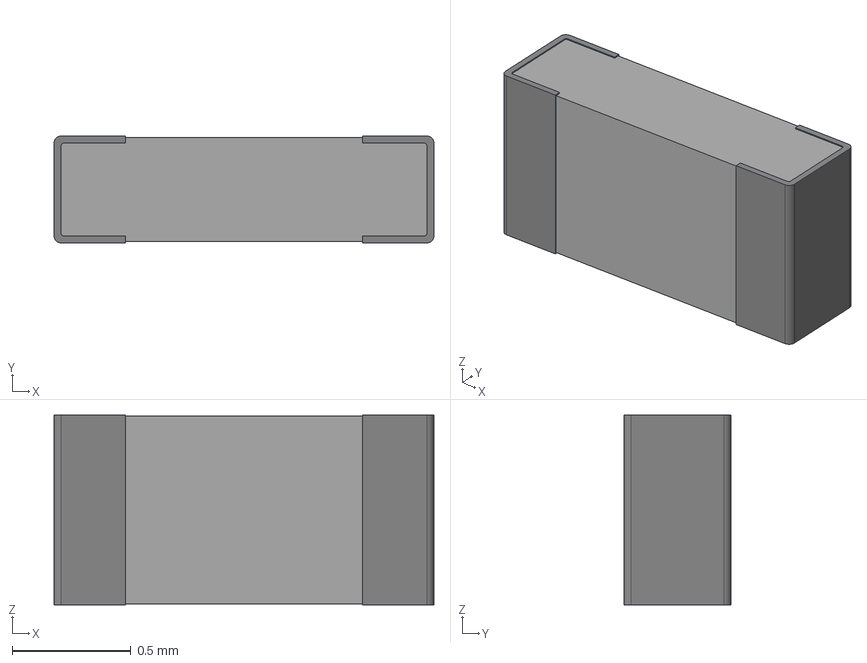
[picture p24: CAD file, 2017-04-18]
minnowboard-turbot-dual-core/pcb-f200-revX205_Turbot-A/Turbot_F200_X205_VX/PCB/Layout/3D/ImportedPartModels/FB0603.stp
1.60 x 0.45 x 0.8 mm
