MinnowBoard-org/design-files/minnowboard-turbot-dual-core/pcb-f200-revX205_Turbot-A/STEPLibrary/USON6.step

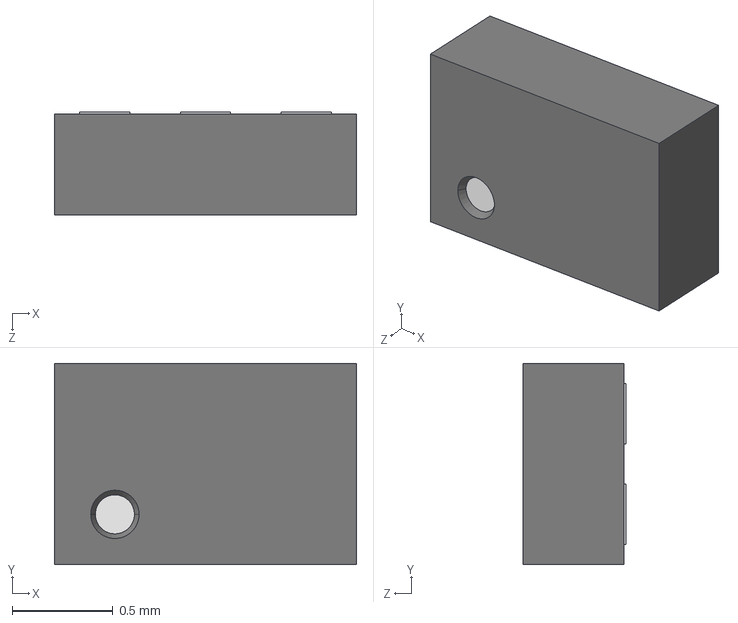
[picture p26: CAD file, 2017-04-18]
minnowboard-turbot-dual-core/pcb-f200-revX205_Turbot-A/STEPLibrary/USON6.step
1.50 x 1.00 x 0.51 mm
