MinnowBoard-org/design-files/minnowboard-turbot-dual-core/pcb-f200-revX205_Turbot-A/Turbot_F200_X205_VX/PCB/Layout/3D/ImportedPartModels/DFN6_3_3p3.step

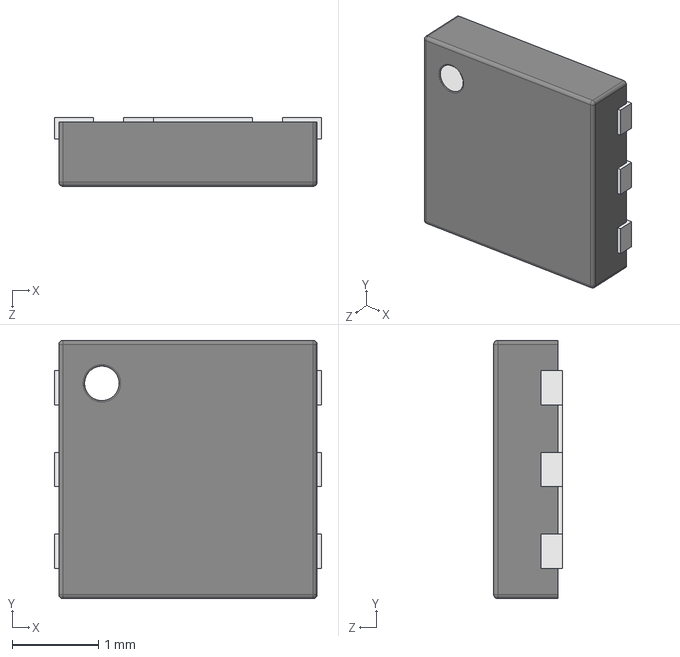
[picture p27: CAD file, 2017-04-18]
minnowboard-turbot-dual-core/pcb-f200-revX205_Turbot-A/Turbot_F200_X205_VX/PCB/Layout/3D/ImportedPartModels/DFN6_3_3p3.step
3.10 x 3.00 x 0.8 mm
