MinnowBoard-org/design-files/minnowboard-turbot-dual-core/pcb-f200-revX205_Turbot-A/STEPLibrary/1206R.step

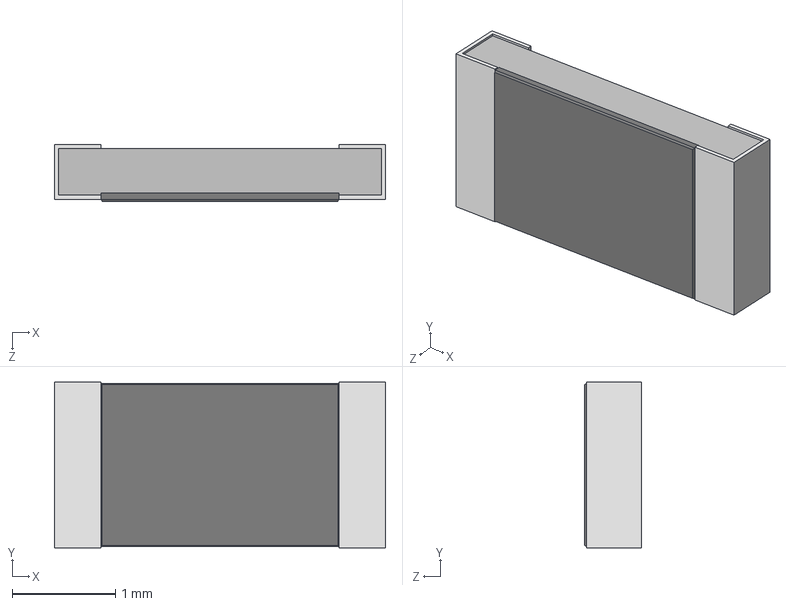
[picture p28: CAD file, 2017-04-18]
minnowboard-turbot-dual-core/pcb-f200-revX205_Turbot-A/STEPLibrary/1206R.step
3.20 x 1.60 x 0.55 mm
