MinnowBoard-org/design-files/minnowboard-turbot-dual-core/pcb-f200-revX205_Turbot-A/Turbot_F200_X205_VX/PCB/Layout/3D/ImportedPartModels/IND0805_4pin.step

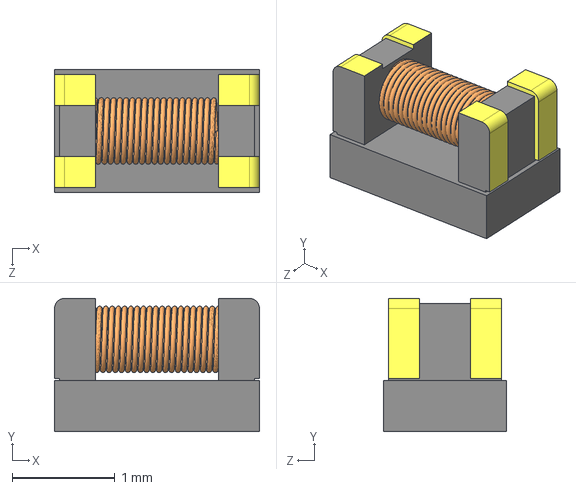
[picture p29: CAD file, 2017-04-18]
minnowboard-turbot-dual-core/pcb-f200-revX205_Turbot-A/Turbot_F200_X205_VX/PCB/Layout/3D/ImportedPartModels/IND0805_4pin.step
2.00 x 1.30 x 1.20 mm
