MinnowBoard-org/design-files/minnowboard-turbot-dual-core/pcb-f200-revX205_Turbot-A/STEPLibrary/SOP8.step

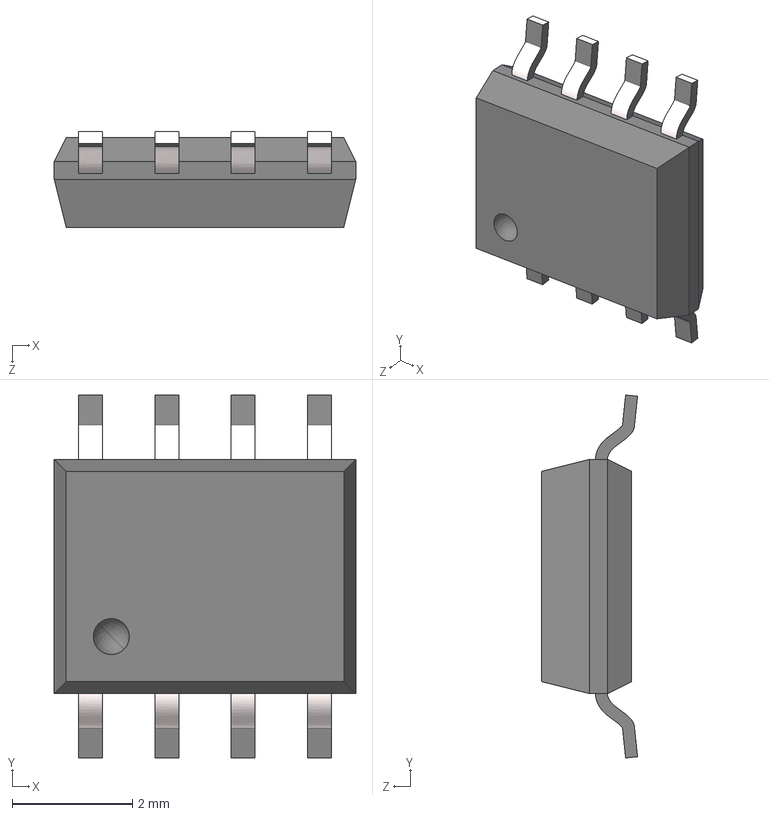
[picture p31: CAD file, 2017-04-18]
minnowboard-turbot-dual-core/pcb-f200-revX205_Turbot-A/STEPLibrary/SOP8.step
5.02 x 6.04 x 1.60 mm
