MinnowBoard-org/design-files/minnowboard-turbot-dual-core/pcb-f200-revX205_Turbot-A/STEPLibrary/XDFN2_v2.STEP

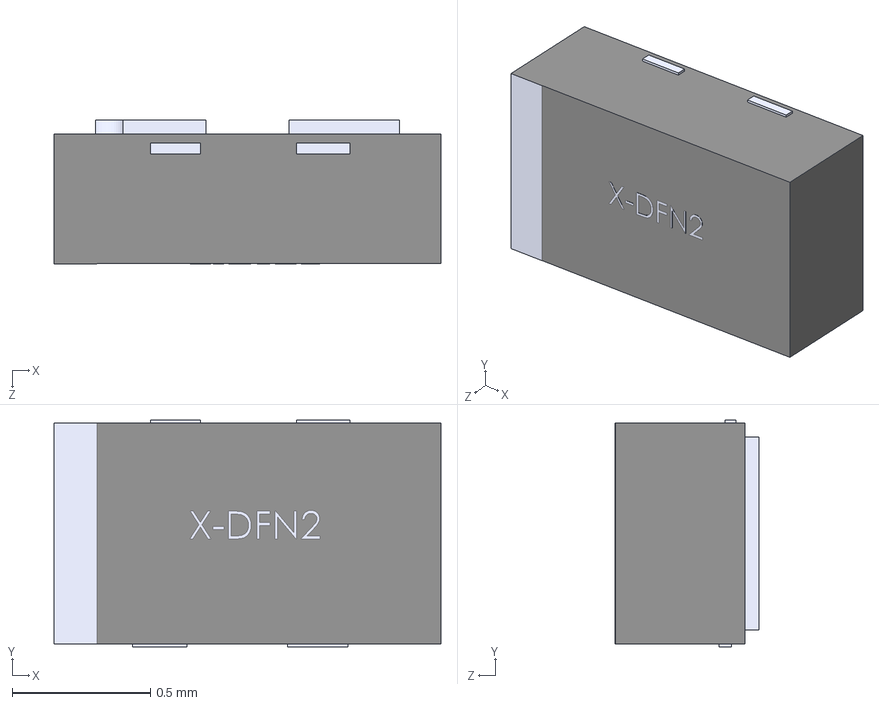
[picture p35: CAD file, 2017-04-18]
minnowboard-turbot-dual-core/pcb-f200-revX205_Turbot-A/STEPLibrary/XDFN2_v2.STEP
1.40 x 0.82 x 0.521 mm
