MinnowBoard-org/design-files/minnowboard-turbot-dual-core/pcb-f200-revX205_Turbot-A/STEPLibrary/PowerPak_SO8.step

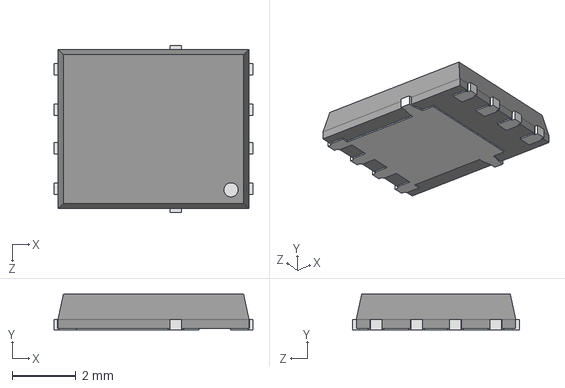
[picture p38: CAD file, 2017-04-18]
minnowboard-turbot-dual-core/pcb-f200-revX205_Turbot-A/STEPLibrary/PowerPak_SO8.step
6.24 x 1.12 x 5.25 mm
