MinnowBoard-org/design-files/minnowboard-turbot-dual-core/pcb-f200-revX205_Turbot-A/STEPLibrary/PDSO-G24_7p8x4p4.step

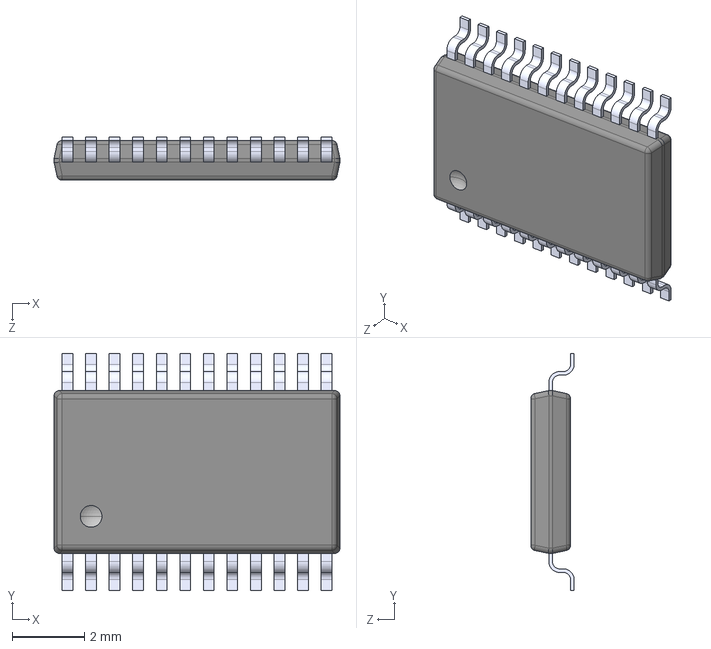
[picture p40: CAD file, 2017-04-18]
minnowboard-turbot-dual-core/pcb-f200-revX205_Turbot-A/STEPLibrary/PDSO-G24_7p8x4p4.step
7.90 x 6.55 x 1.20 mm
