MinnowBoard-org/design-files/minnowboard-turbot-dual-core/pcb-f200-revX205_Turbot-A/STEPLibrary/DRL0005A.stp

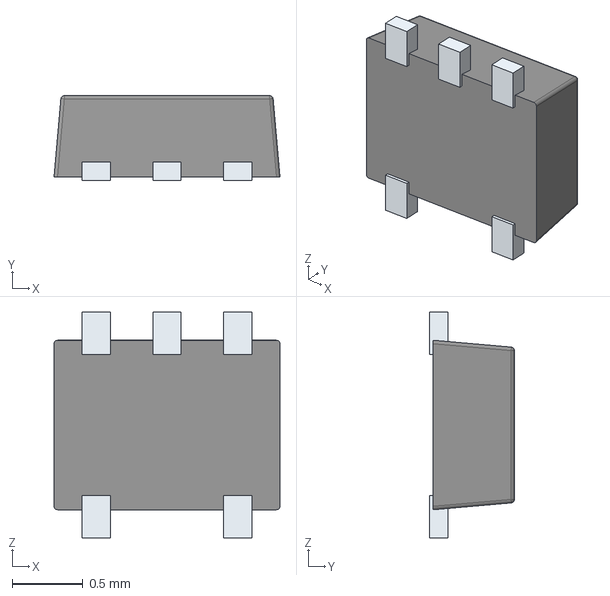
[picture p48: CAD file, 2017-04-18]
minnowboard-turbot-dual-core/pcb-f200-revX205_Turbot-A/STEPLibrary/DRL0005A.stp
1.60 x 0.6 x 1.60 mm
FRAME_DRL0005A
BODY_DRL0005A
