MinnowBoard-org/design-files/minnowboard-turbot-dual-core/pcb-f200-revX205_Turbot-A/STEPLibrary/ASPI-0630HI.STEP

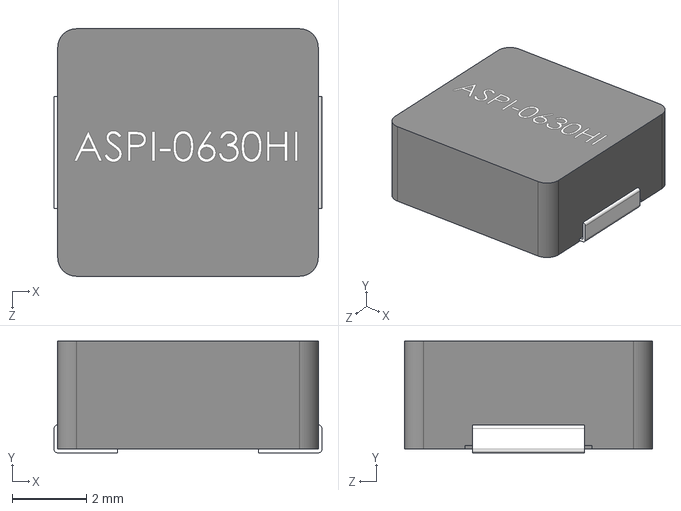
[picture p50: CAD file, 2017-04-18]
minnowboard-turbot-dual-core/pcb-f200-revX205_Turbot-A/STEPLibrary/ASPI-0630HI.STEP
7.20 x 3.00 x 6.65 mm
