MinnowBoard-org/design-files/minnowboard-turbot-dual-core/pcb-f200-revX205_Turbot-A/Turbot_F200_X205_VX/PCB/Layout/3D/ImportedPartModels/LED0603.STEP

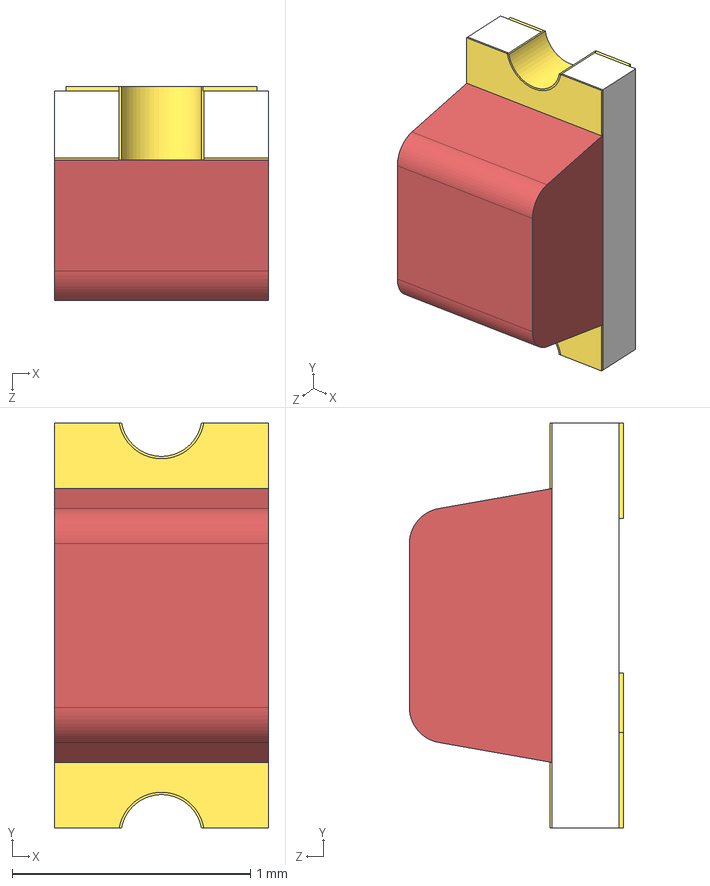
[picture p51: CAD file, 2017-04-18]
minnowboard-turbot-dual-core/pcb-f200-revX205_Turbot-A/Turbot_F200_X205_VX/PCB/Layout/3D/ImportedPartModels/LED0603.STEP
0.9 x 1.70 x 0.9 mm
User Library-LTST-C190EKT_Pad
User Library-LTST-C190EKT_Pad005
User Library-LTST-C190EKT_Pad001
User Library-LTST-C190EKT_Pad004
User Library-LTST-C190EKT_Pad003
User Library-LTST-C190EKT_Lens
