MinnowBoard-org/design-files/minnowboard-turbot-dual-core/pcb-f200-revX205_Turbot-A/STEPLibrary/ASPI-7318.STEP

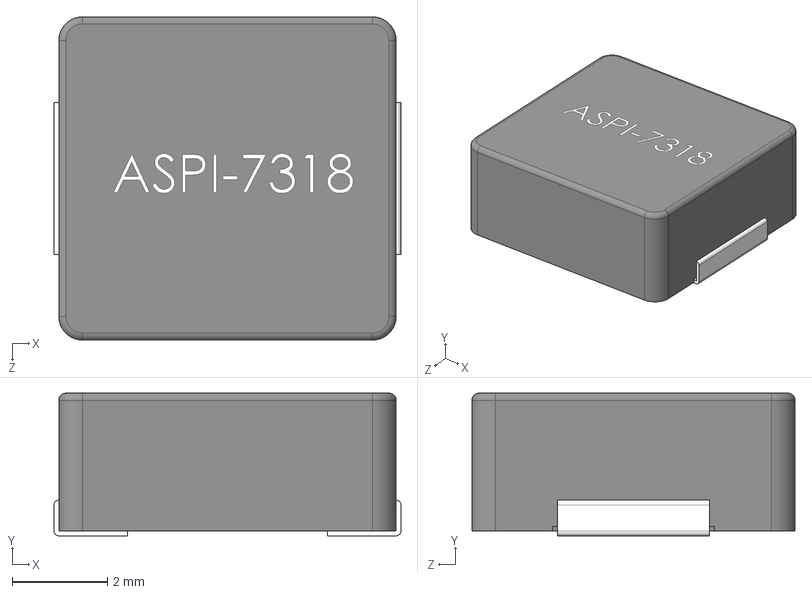
[picture p54: CAD file, 2017-04-18]
minnowboard-turbot-dual-core/pcb-f200-revX205_Turbot-A/STEPLibrary/ASPI-7318.STEP
7.30 x 3.00 x 6.80 mm
