MinnowBoard-org/design-files/minnowboard-turbot-dual-core/pcb-f200-revX205_Turbot-A/STEPLibrary/258-0004869.STEP

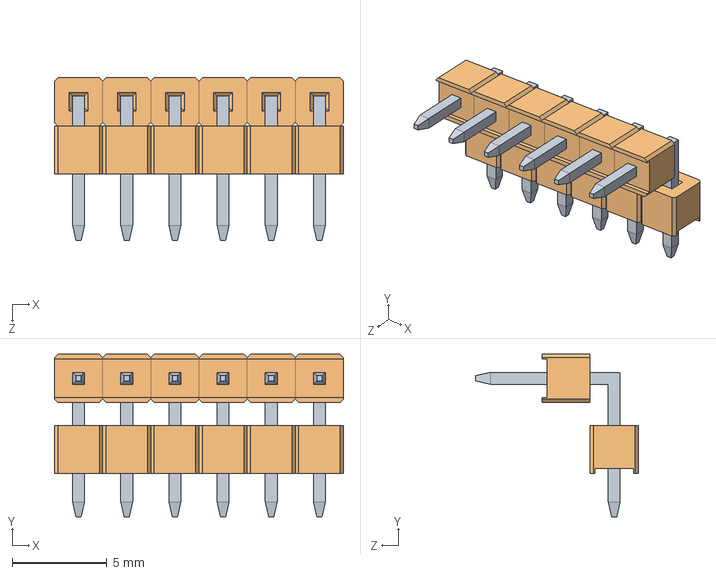
[picture p58: CAD file, 2017-04-18]
minnowboard-turbot-dual-core/pcb-f200-revX205_Turbot-A/STEPLibrary/258-0004869.STEP
15.2 x 8.57 x 8.57 mm
BSTCR-1 BOTTOM PIN x 6
BSTCR-1 single row body x 12
