MinnowBoard-org/design-files/minnowboard-turbot-dual-core/pcb-f200-revX205_Turbot-A/STEPLibrary/3225I.STEP

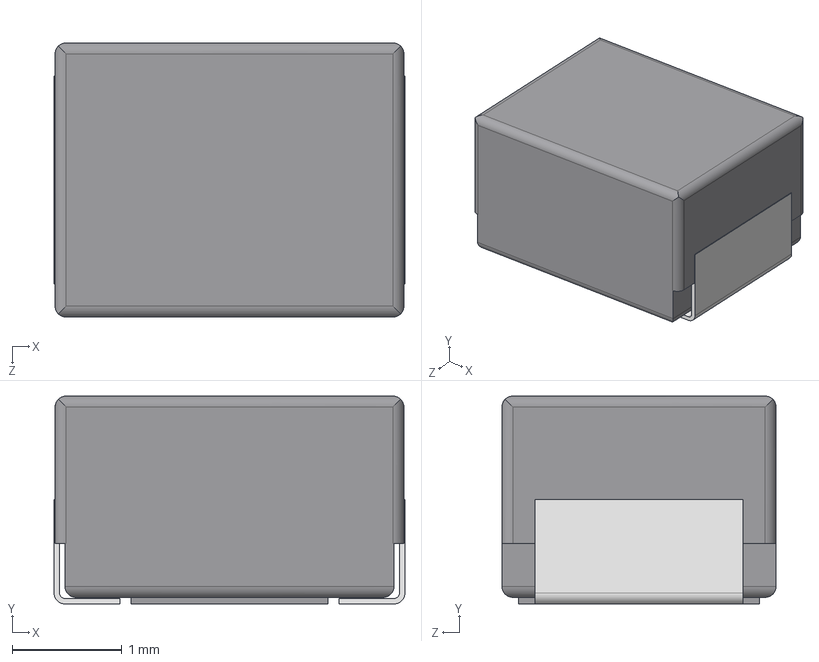
[picture p59: CAD file, 2017-04-18]
minnowboard-turbot-dual-core/pcb-f200-revX205_Turbot-A/STEPLibrary/3225I.STEP
3.20 x 1.90 x 2.50 mm
User Library-3225_Component1
User Library-3225_Component2
User Library-3225_Component3
