MinnowBoard-org/design-files/minnowboard-turbot-dual-core/pcb-f200-revX205_Turbot-A/STEPLibrary/XTAL4SMD.STEP

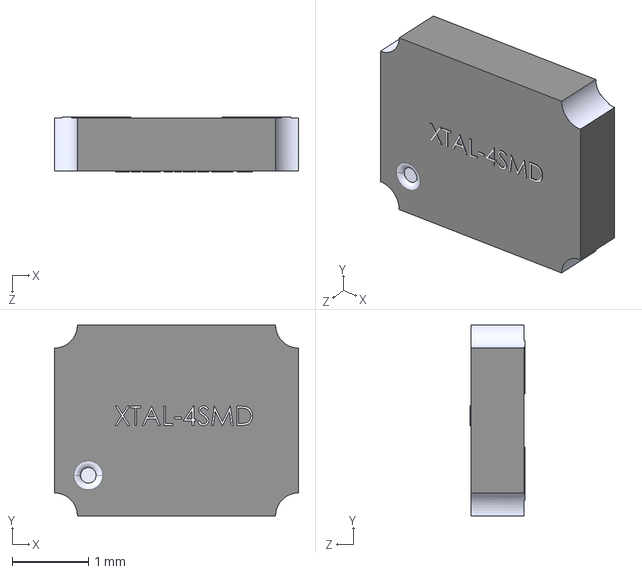
[picture p64: CAD file, 2017-04-18]
minnowboard-turbot-dual-core/pcb-f200-revX205_Turbot-A/STEPLibrary/XTAL4SMD.STEP
3.20 x 2.50 x 0.72 mm
