MinnowBoard-org/design-files/minnowboard-turbot-dual-core/pcb-f200-revX205_Turbot-A/STEPLibrary/SOT363_SC70_6.step

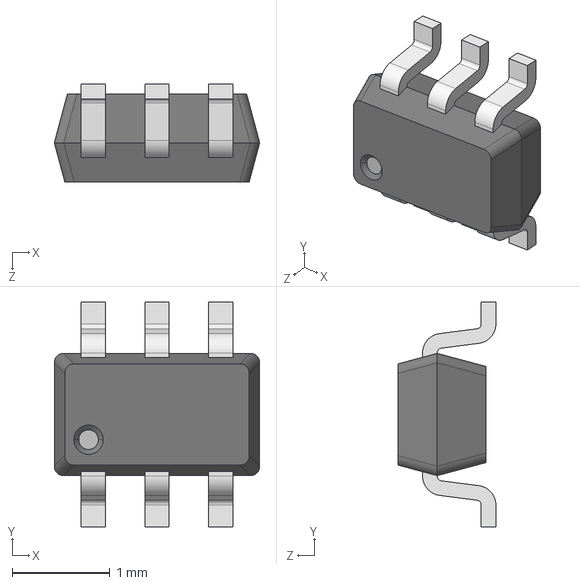
[picture p67: CAD file, 2017-04-18]
minnowboard-turbot-dual-core/pcb-f200-revX205_Turbot-A/STEPLibrary/SOT363_SC70_6.step
2.10 x 2.30 x 1.00 mm
