MinnowBoard-org/design-files/minnowboard-v1/rev-a/MinnowBoard_Schematics_002-003195_REVA_CCR.pdf

# BOARD HISTORY

# DATE

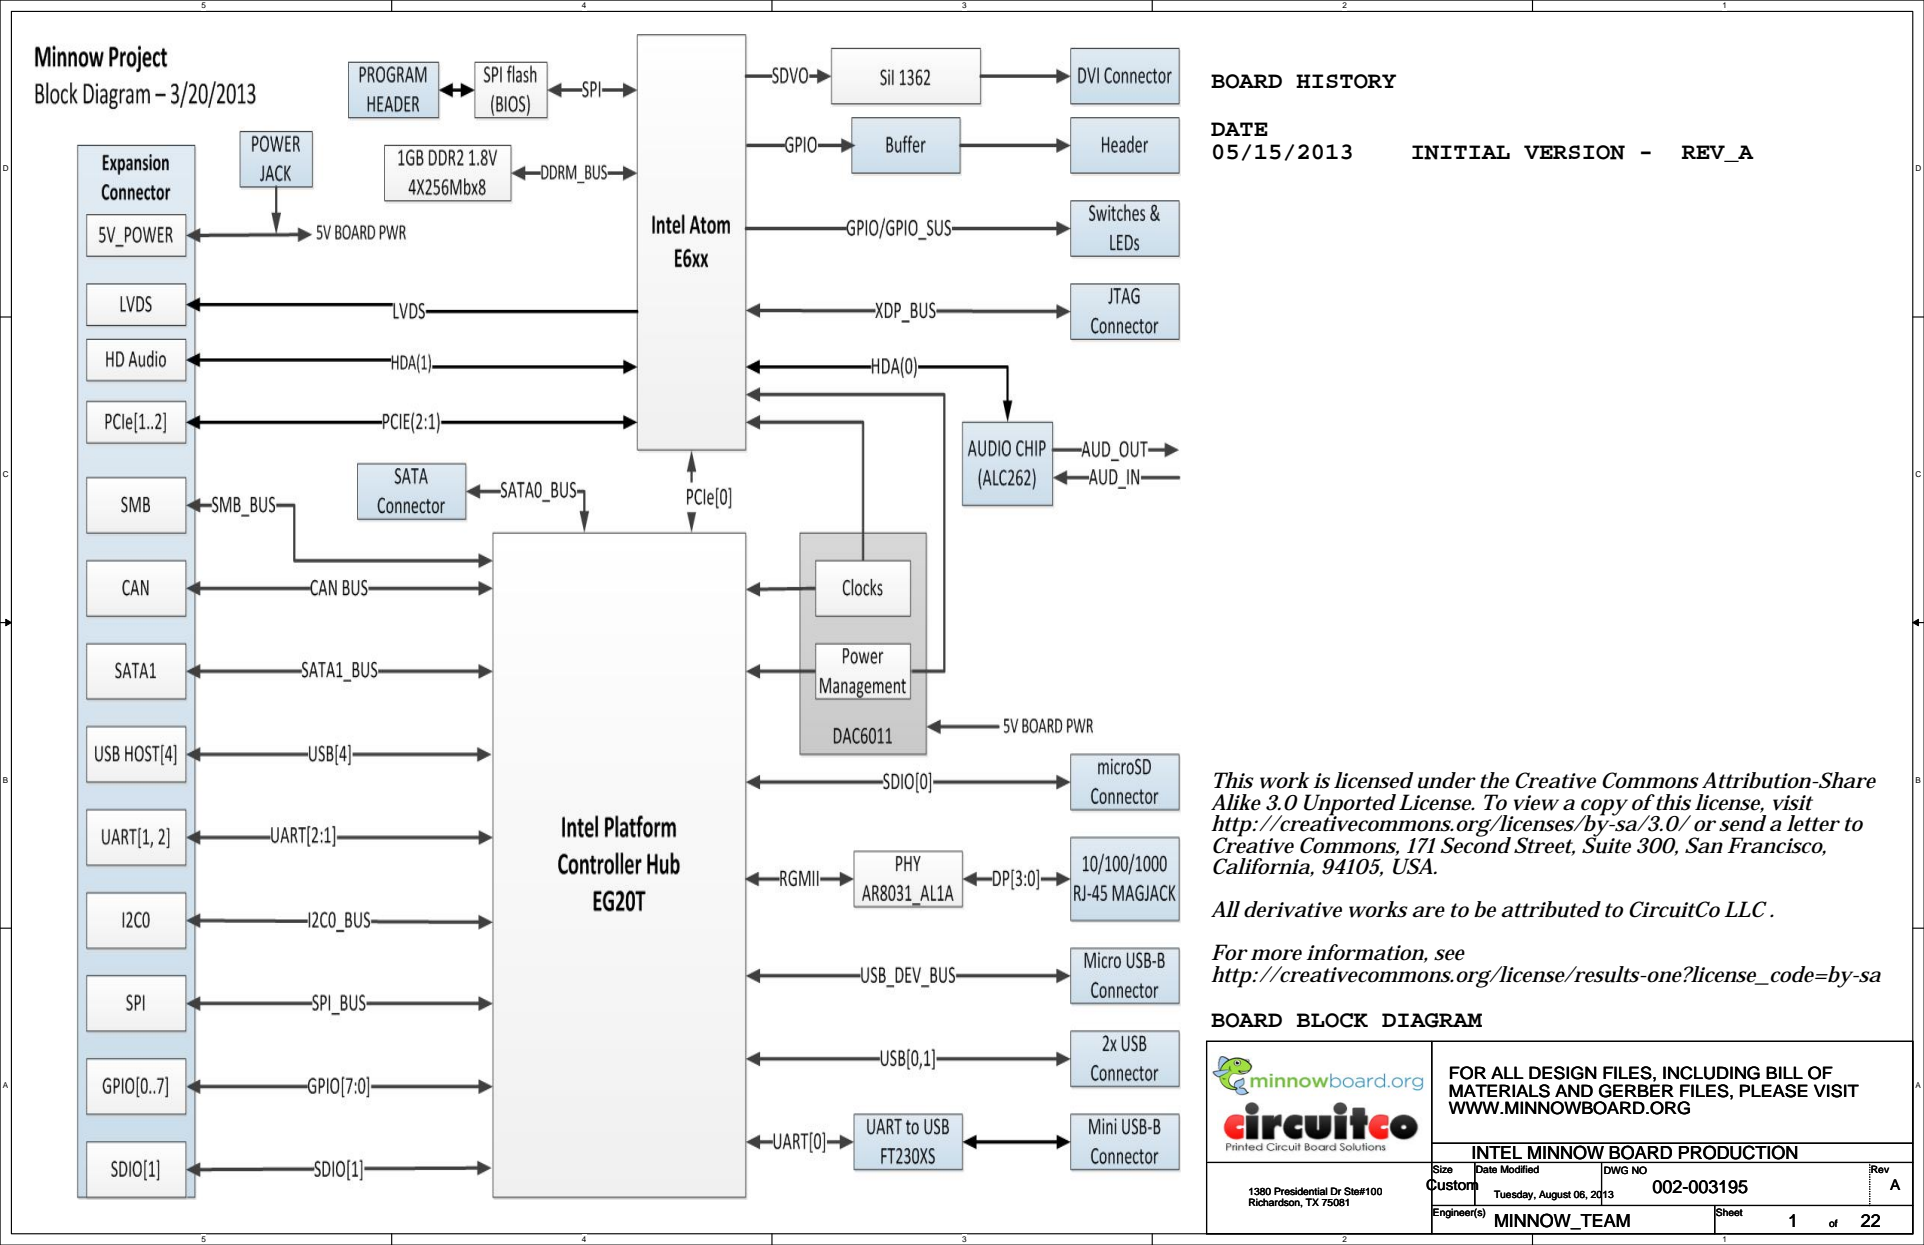
[picture p189: page 1]
INITIAL VERSION - REV_A

This work is licensed under the Creative Commons Attribution-Share
Alike 3.0 Unported License. To view a copy of this license, visit
http://creativecommons.org/licenses/by-sa/3.0/ or send a letter to
Creative Commons, 171 Second Street, Suite 300, San Francisco,
California, 94105, USA.
All derivative works are to be attributed to CircuitCo LLC .
For more information, see
http://creativecommons.org/license/results-one?license_code=by-sa
BOARD BLOCK DIAGRAM

FOR ALL DESIGN FILES, INCLUDING BILL OF
MATERIALS AND GERBER FILES, PLEASE VISIT
WWW.MINNOWBOARD.ORG

INTEL MINNOW BOARD PRODUCTION

Custom 1380 Presidential Dr Ste#100 Richardson, TX 75081 | Size | Date Modified | DWG NO 002-003195 002-003195 002-003195 | Rev A Tuesday, August 06, 2013 A Tuesday, August 06, 2013 A Tuesday, August 06, 2013

Engineer(s) MINNOW_TEAM | Sheet of

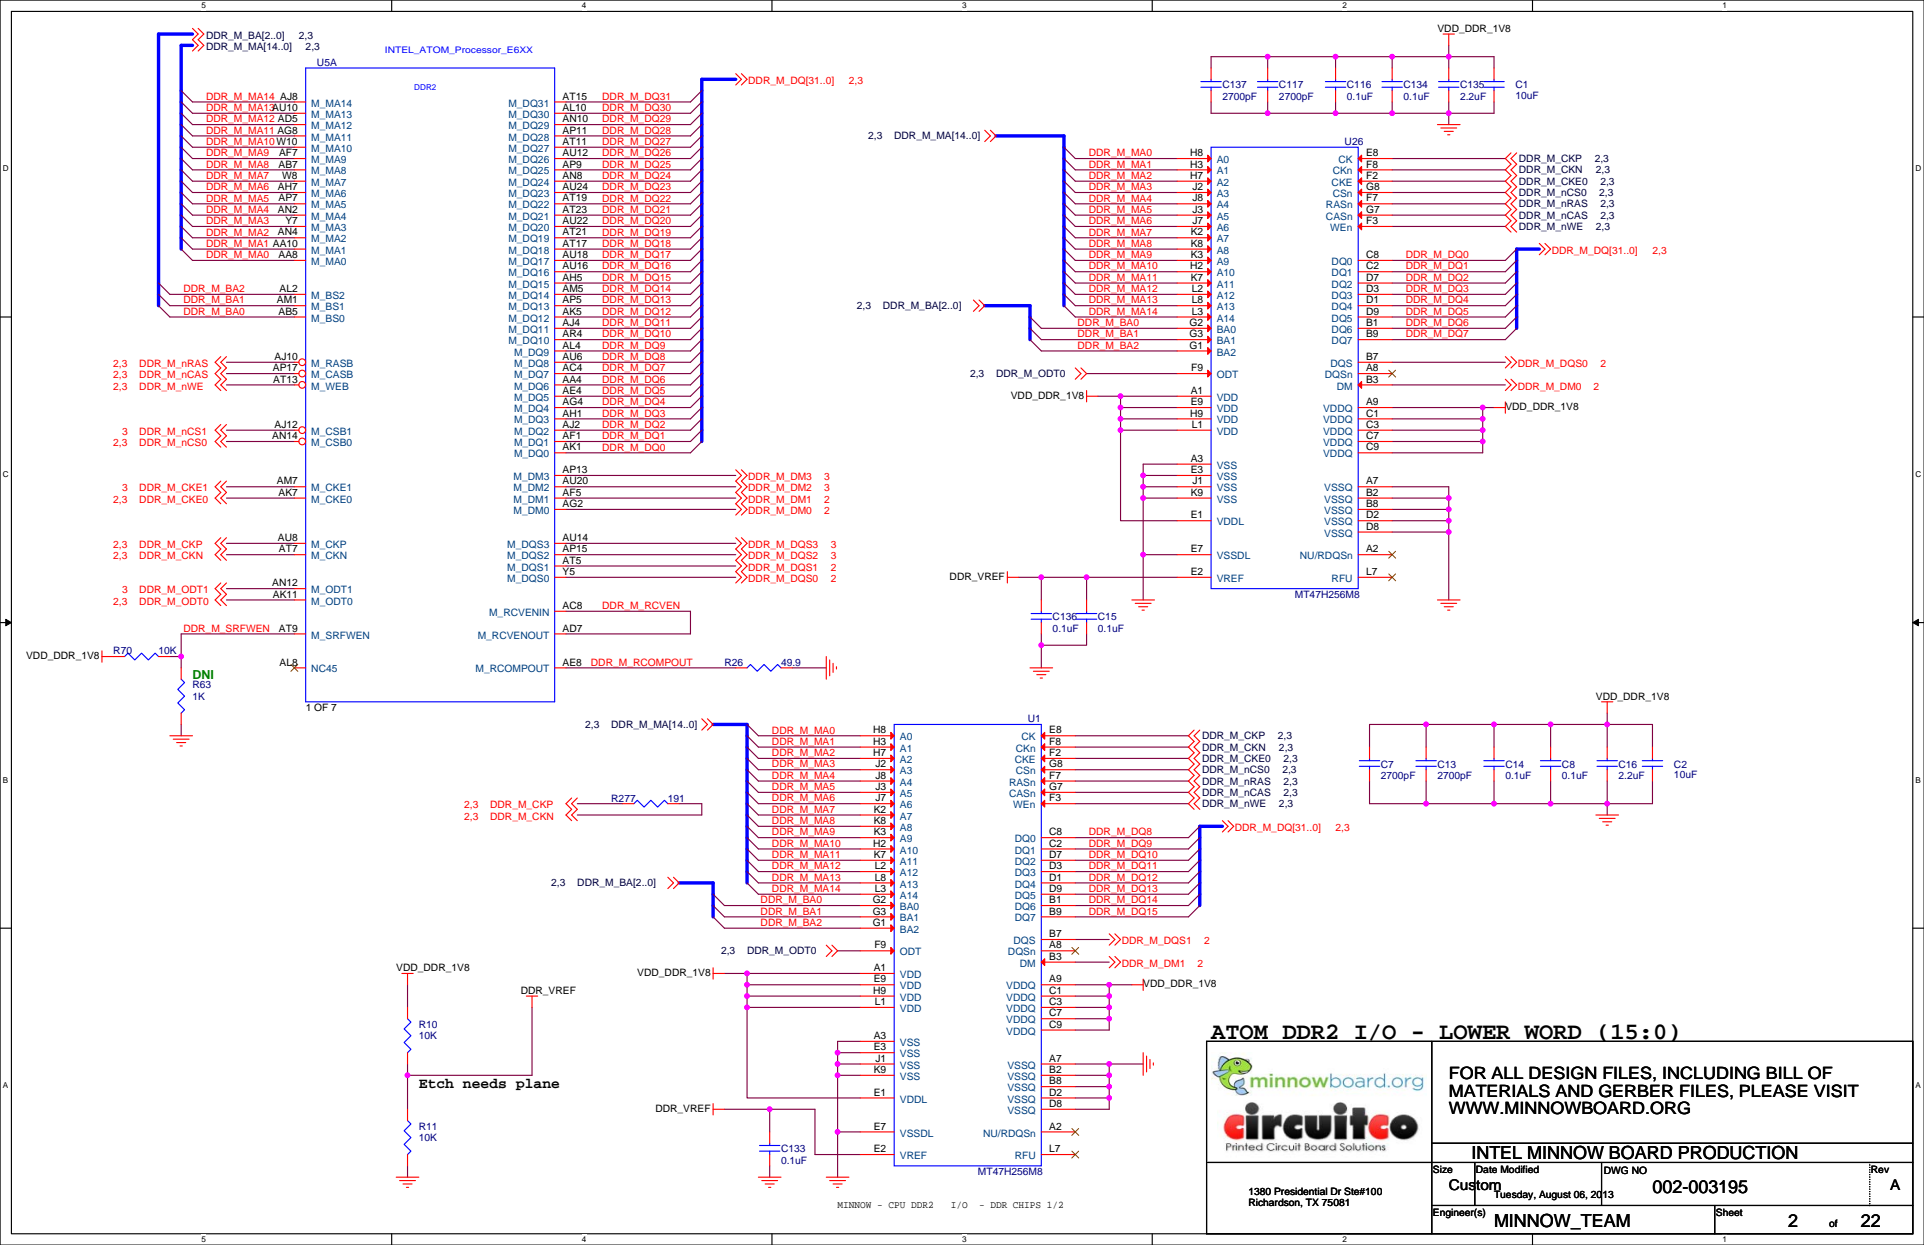
[picture p190: page 2]

FOR ALL DESIGN FILES, INCLUDING BILL OF
MATERIALS AND GERBER FILES, PLEASE VISIT
WWW.MINNOWBOARD.ORG

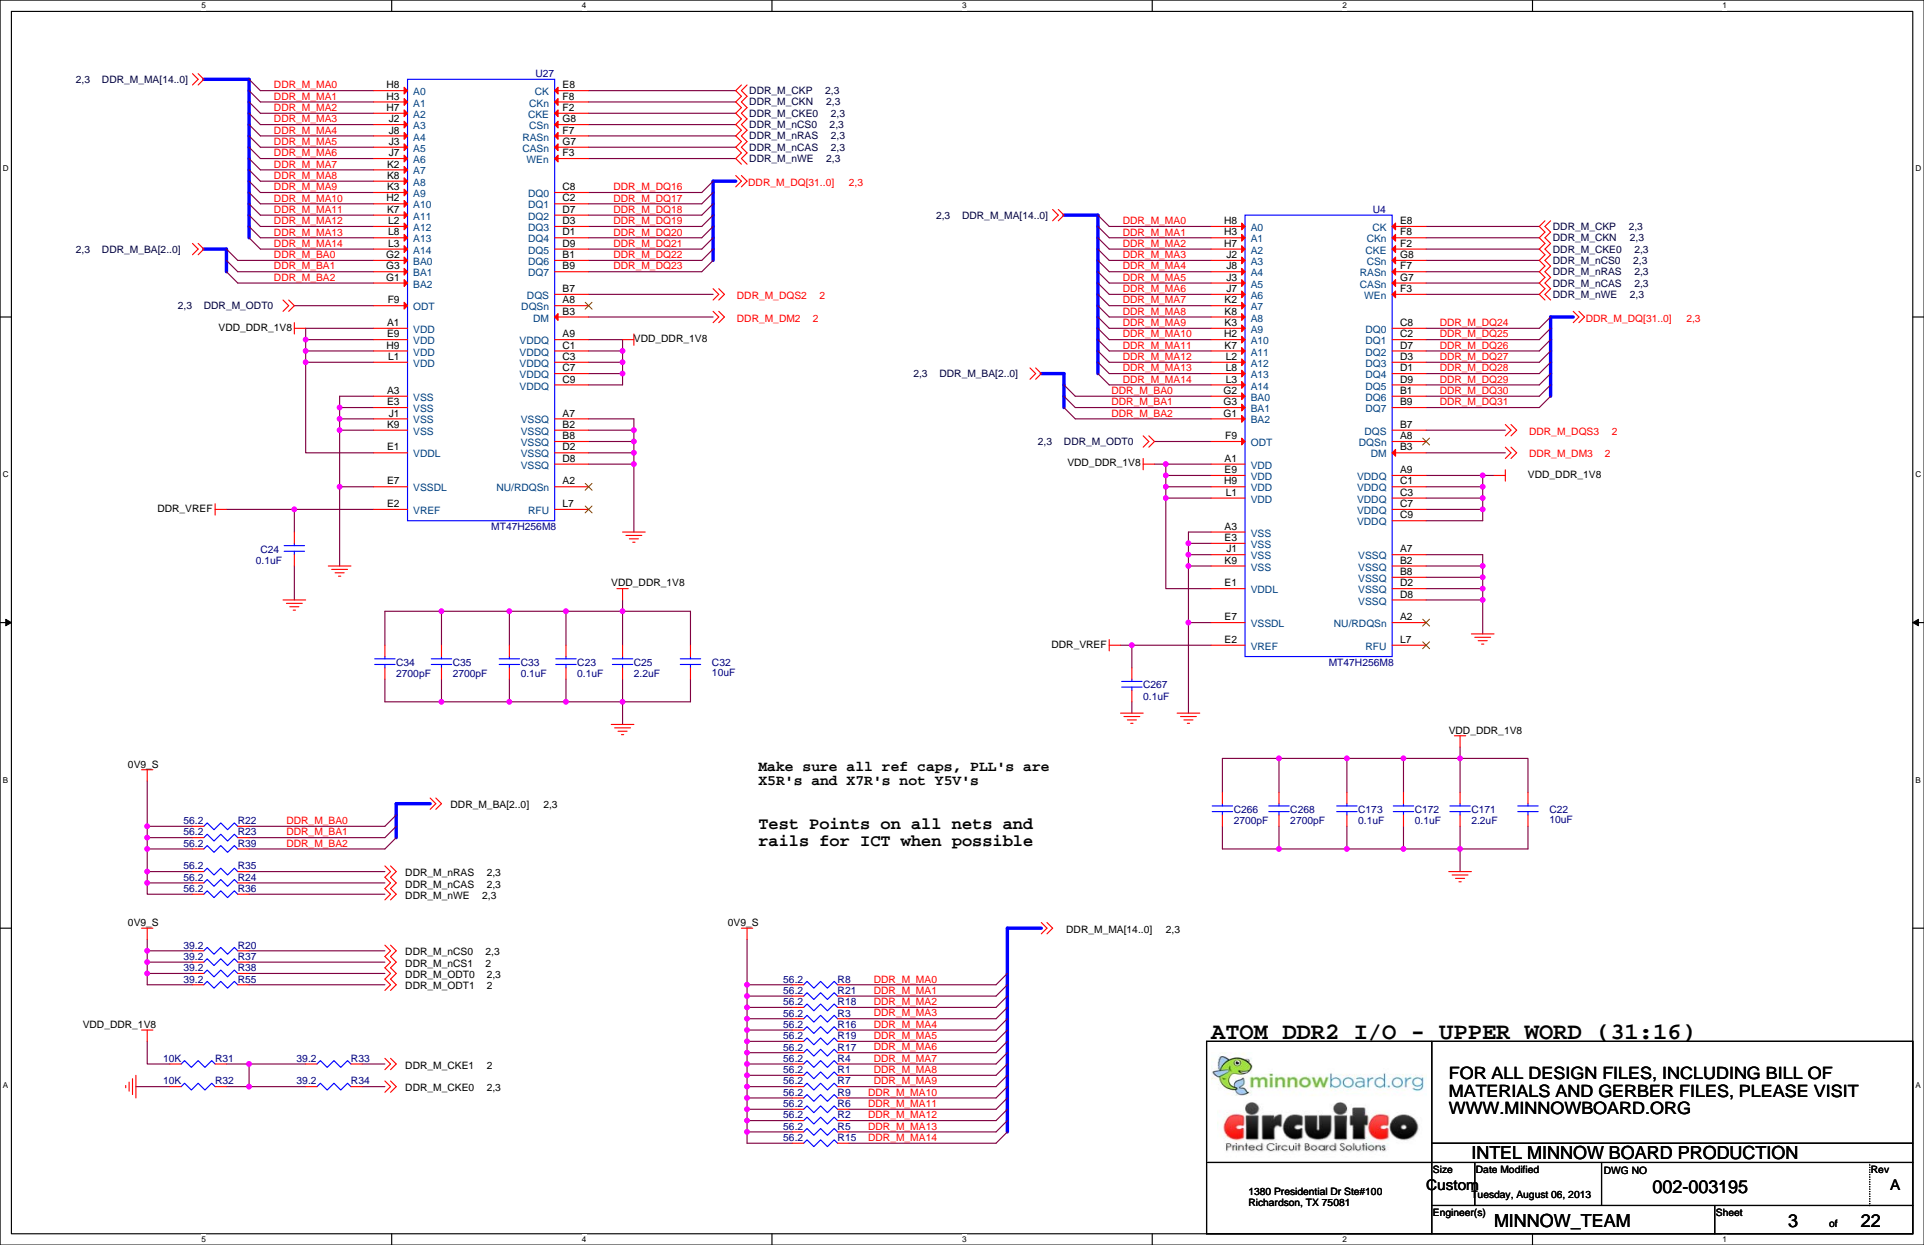
[picture p191: page 3]

Make sure all ref caps, PLL's are
X5R's and X7R's not Y5V's

Test Points on all nets and
rails for ICT when possible

FOR ALL DESIGN FILES, INCLUDING BILL OF
MATERIALS AND GERBER FILES, PLEASE VISIT
WWW.MINNOWBOARD.ORG

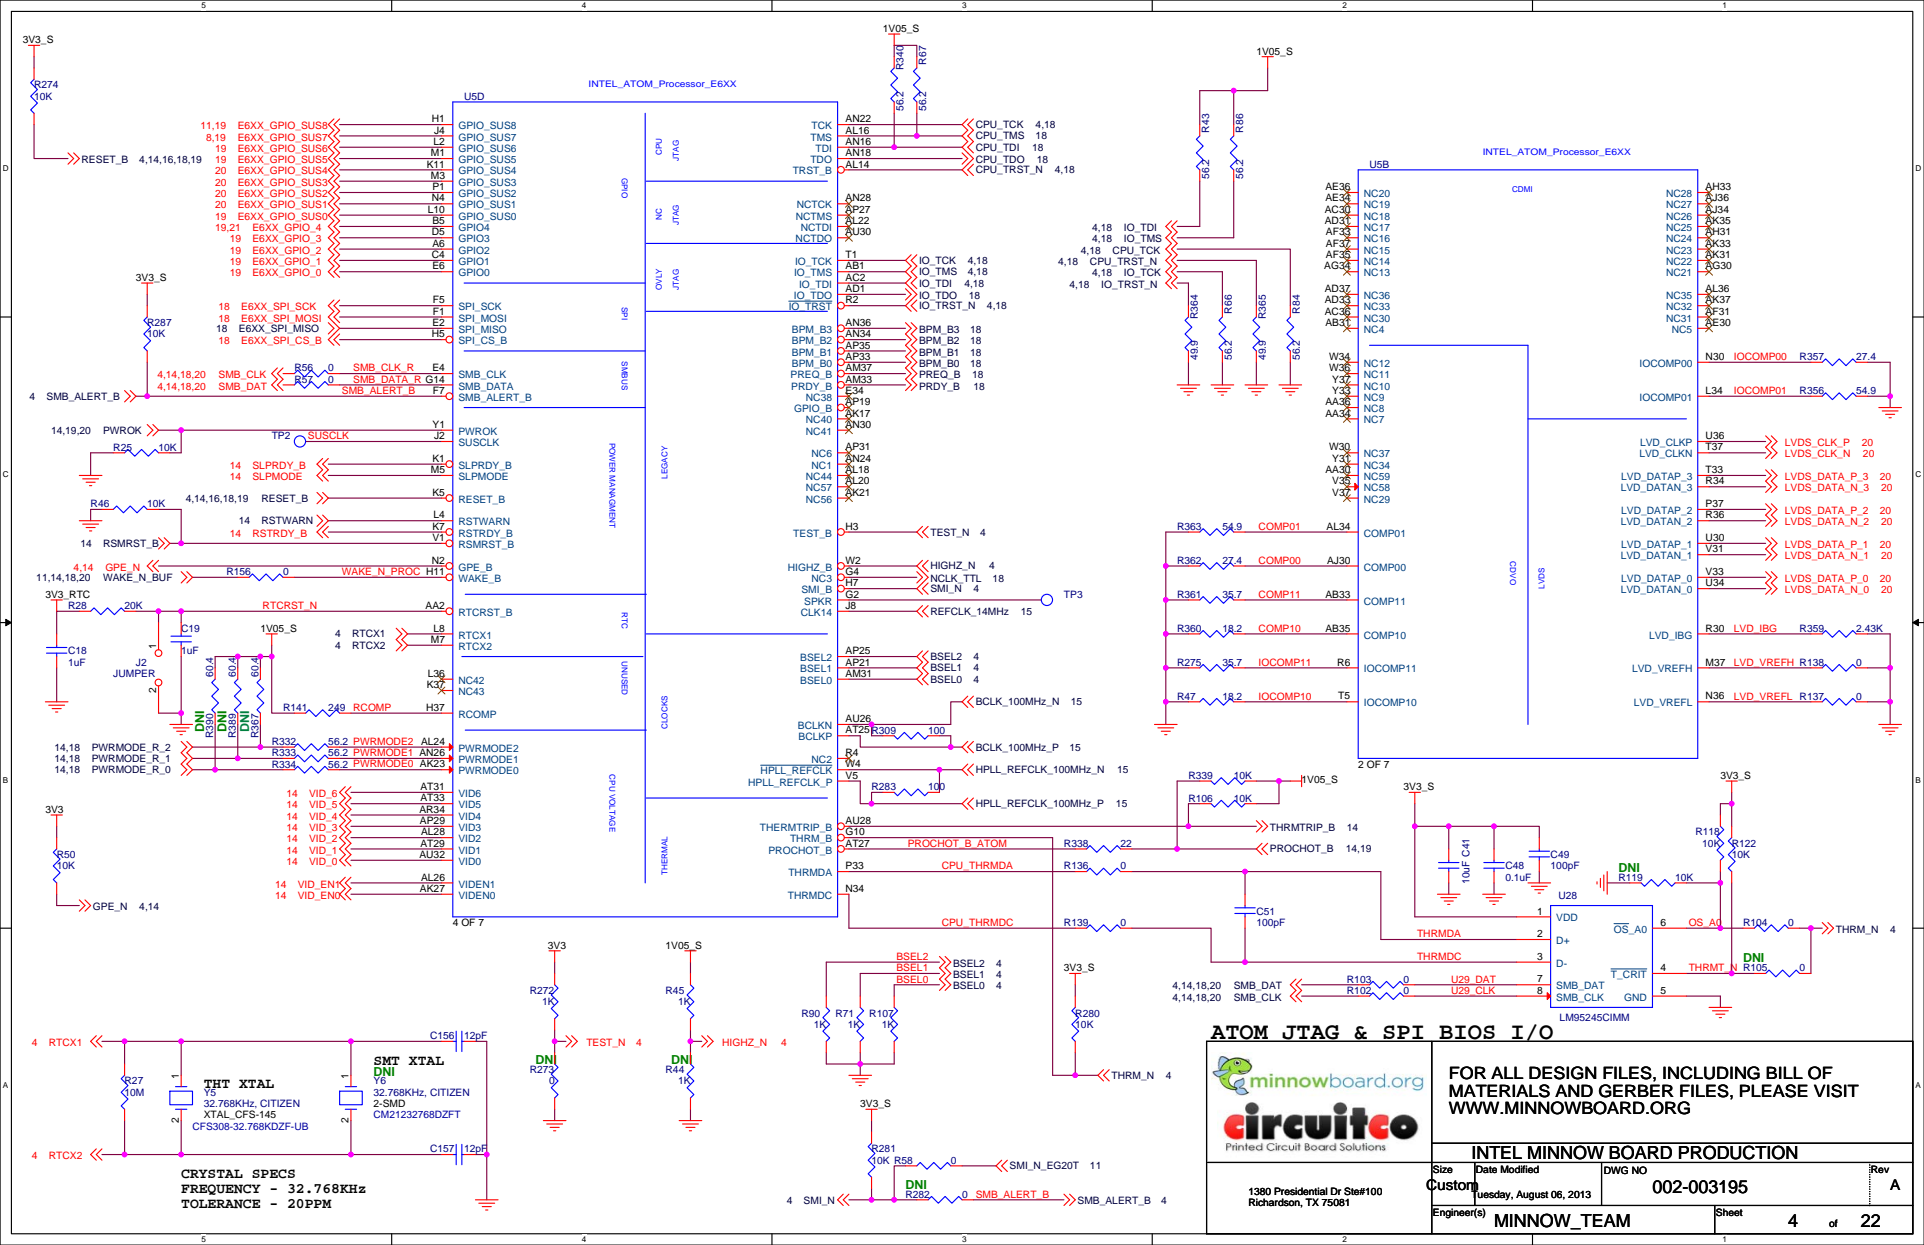
[picture p192: page 4]

THERMAL CPU NC CLOCKS

GPIO SMBUS UNUSED RTC

FOR ALL DESIGN FILES, INCLUDING BILL OF
MATERIALS AND GERBER FILES, PLEASE VISIT
WWW.MINNOWBOARD.ORG

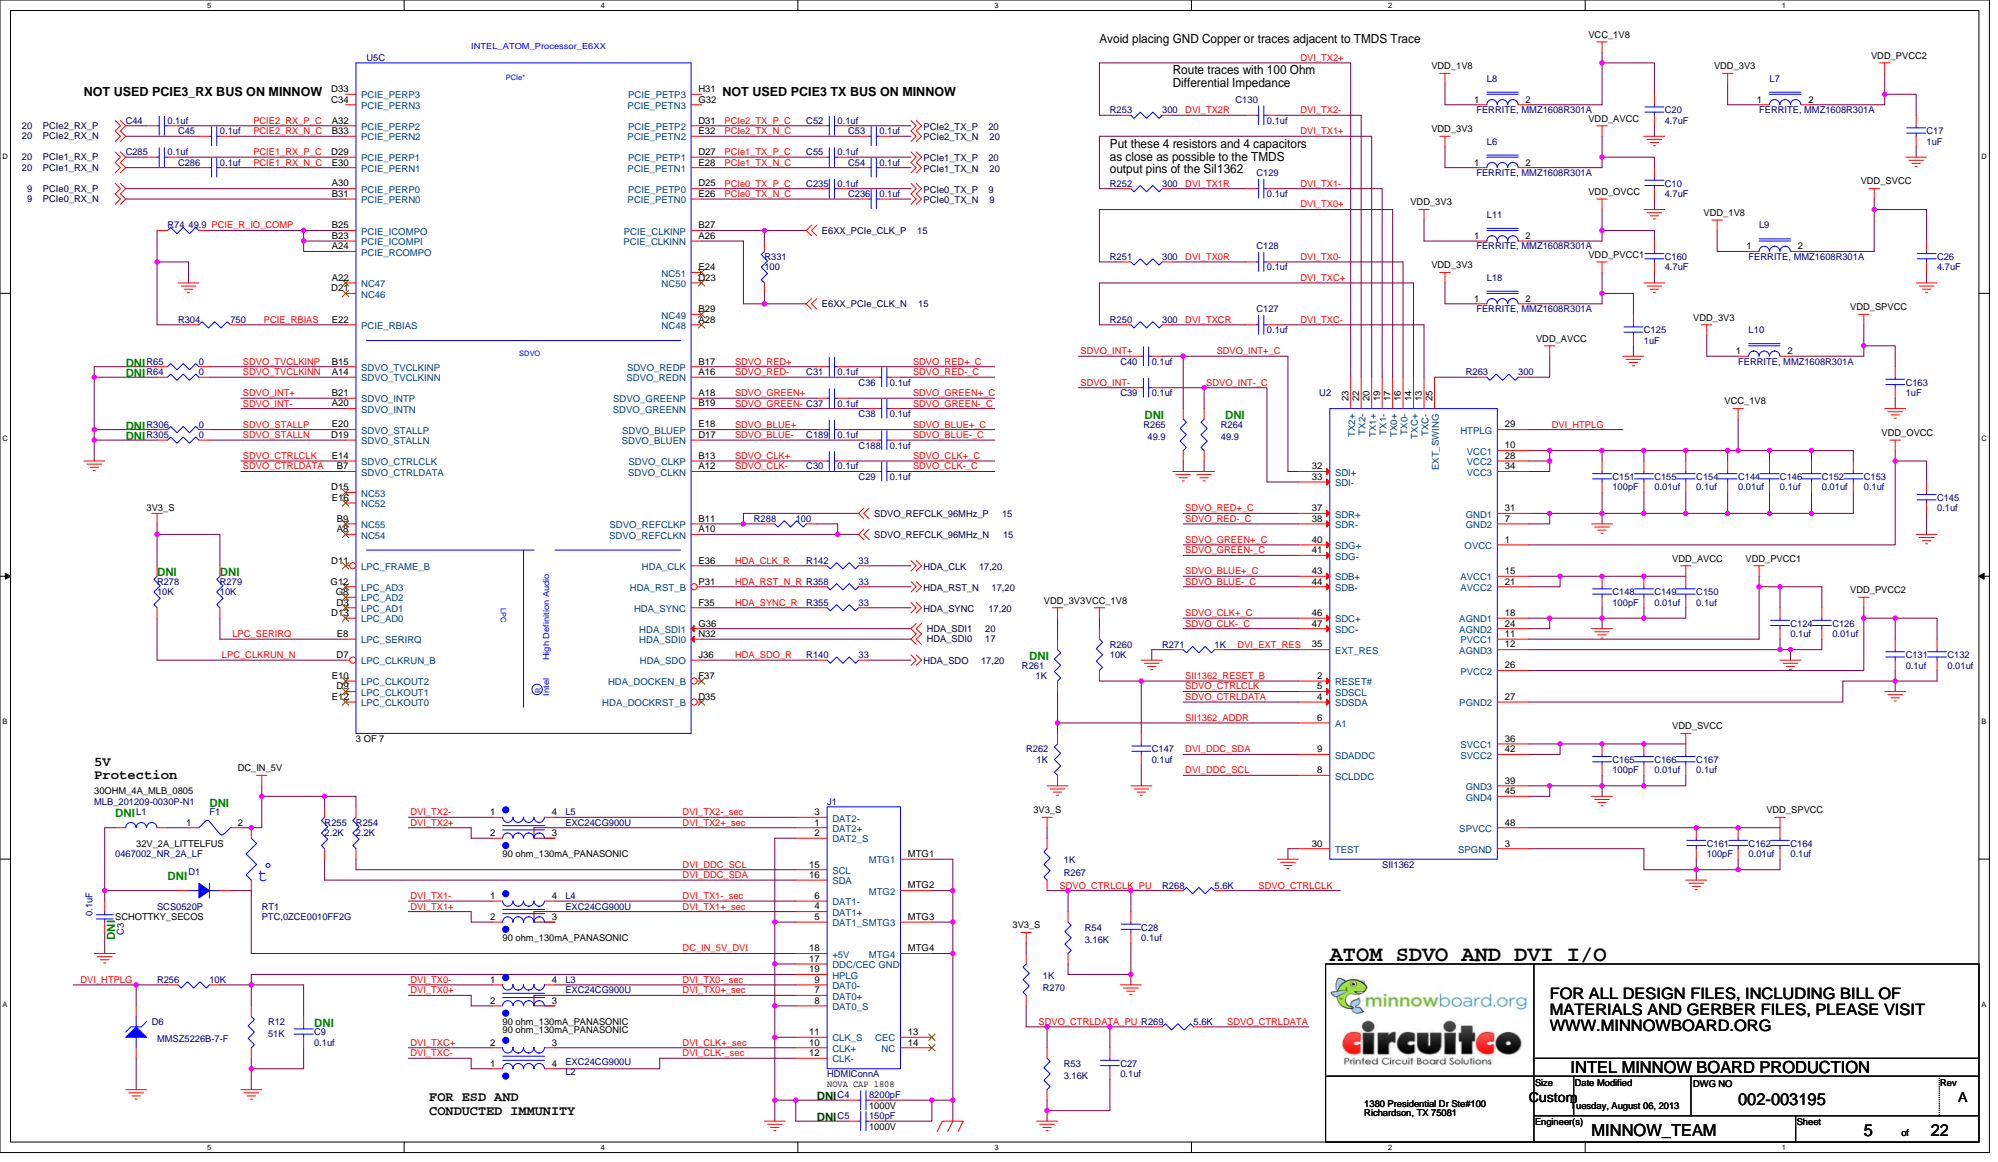
[picture p193: page 5]

Avoid placing GND Copper or traces adjacent to TMDS Trace

Route traces with 100 Ohm
Differential Impedance

Put these 4 resistors and 4 capacitors
as close as possible to the TMDS
output pins of the SiI1362

Intel High Definition Audio

ATOM SDVO AND DVI I/O

FOR ALL DESIGN FILES, INCLUDING BILL OF
MATERIALS AND GERBER FILES, PLEASE VISIT
WWW.MINNOWBOARD.ORG

INTEL MINNOW BOARD PRODUCTION

Custom Custom Custom 1380 Presidential Dr Ste#100 1380 Presidential Dr Ste#100 1380 Presidential Dr Ste#100 Richardson, TX 75081 Richardson, TX 75081 Richardson, TX 75081 | Size Size Size | Date Modified Date Modified Date Modified Tuesday, August 06, 2013 Tuesday, August 06, 2013 Tuesday, August 06, 2013 | DWG NO DWG NO DWG NO 002-003195 002-003195 002-003195 | Rev Rev Rev A A A

Engineer(s) Engineer(s) Engineer(s) MINNOW_TEAM MINNOW_TEAM MINNOW_TEAM | Sheet Sheet Sheet 5 5 5 22 22 22 of of of

## Thick etch

VCC4 AC24 | Thick etch 1V8_1V8_S_VCCA | VOUT2 B1

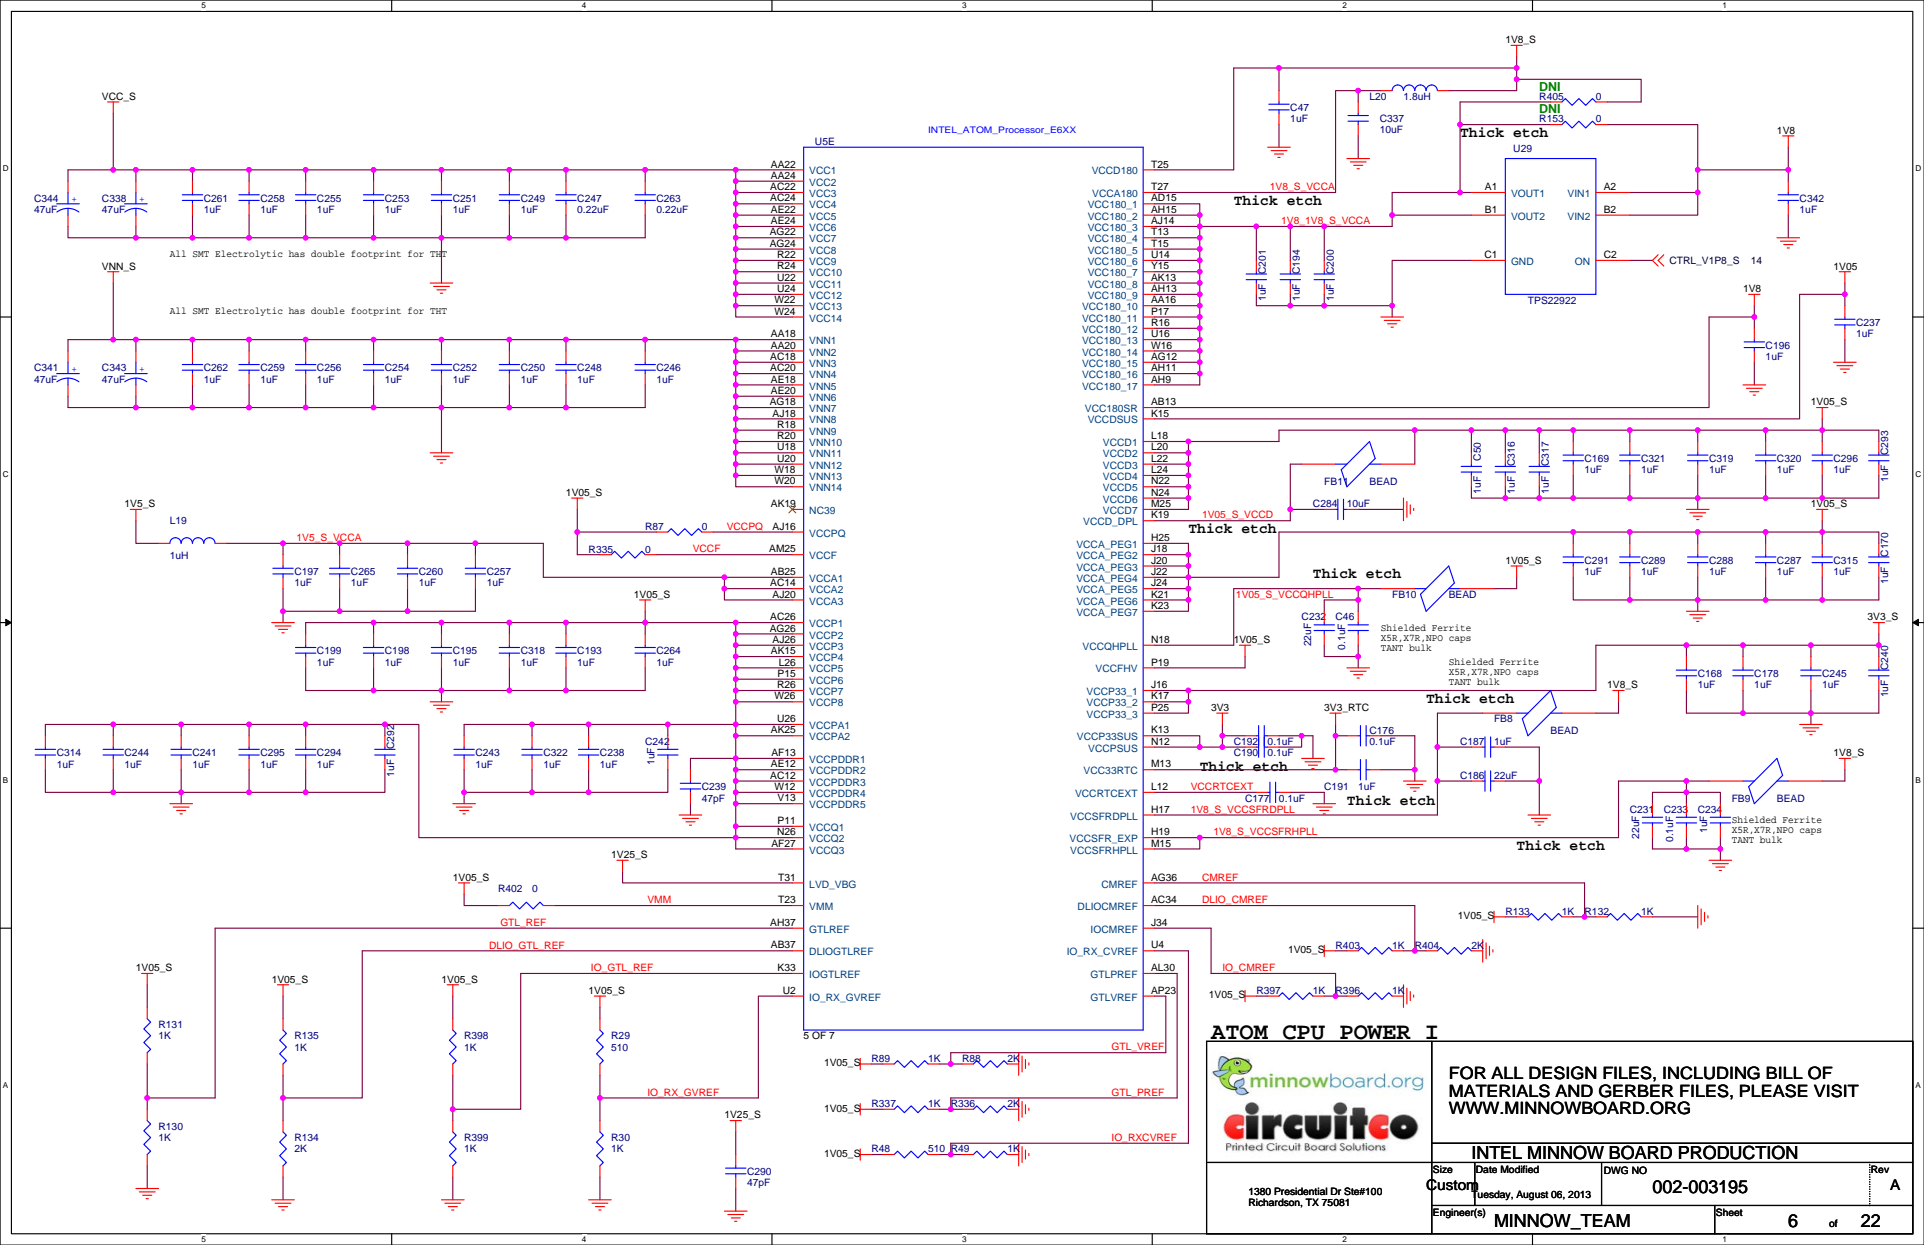
[picture p194: page 6]

VCC6 AE24 | | GND C1

All SMT Electrolytic has double footprint for THT

FOR ALL DESIGN FILES, INCLUDING BILL OF
MATERIALS AND GERBER FILES, PLEASE VISIT
WWW.MINNOWBOARD.ORG

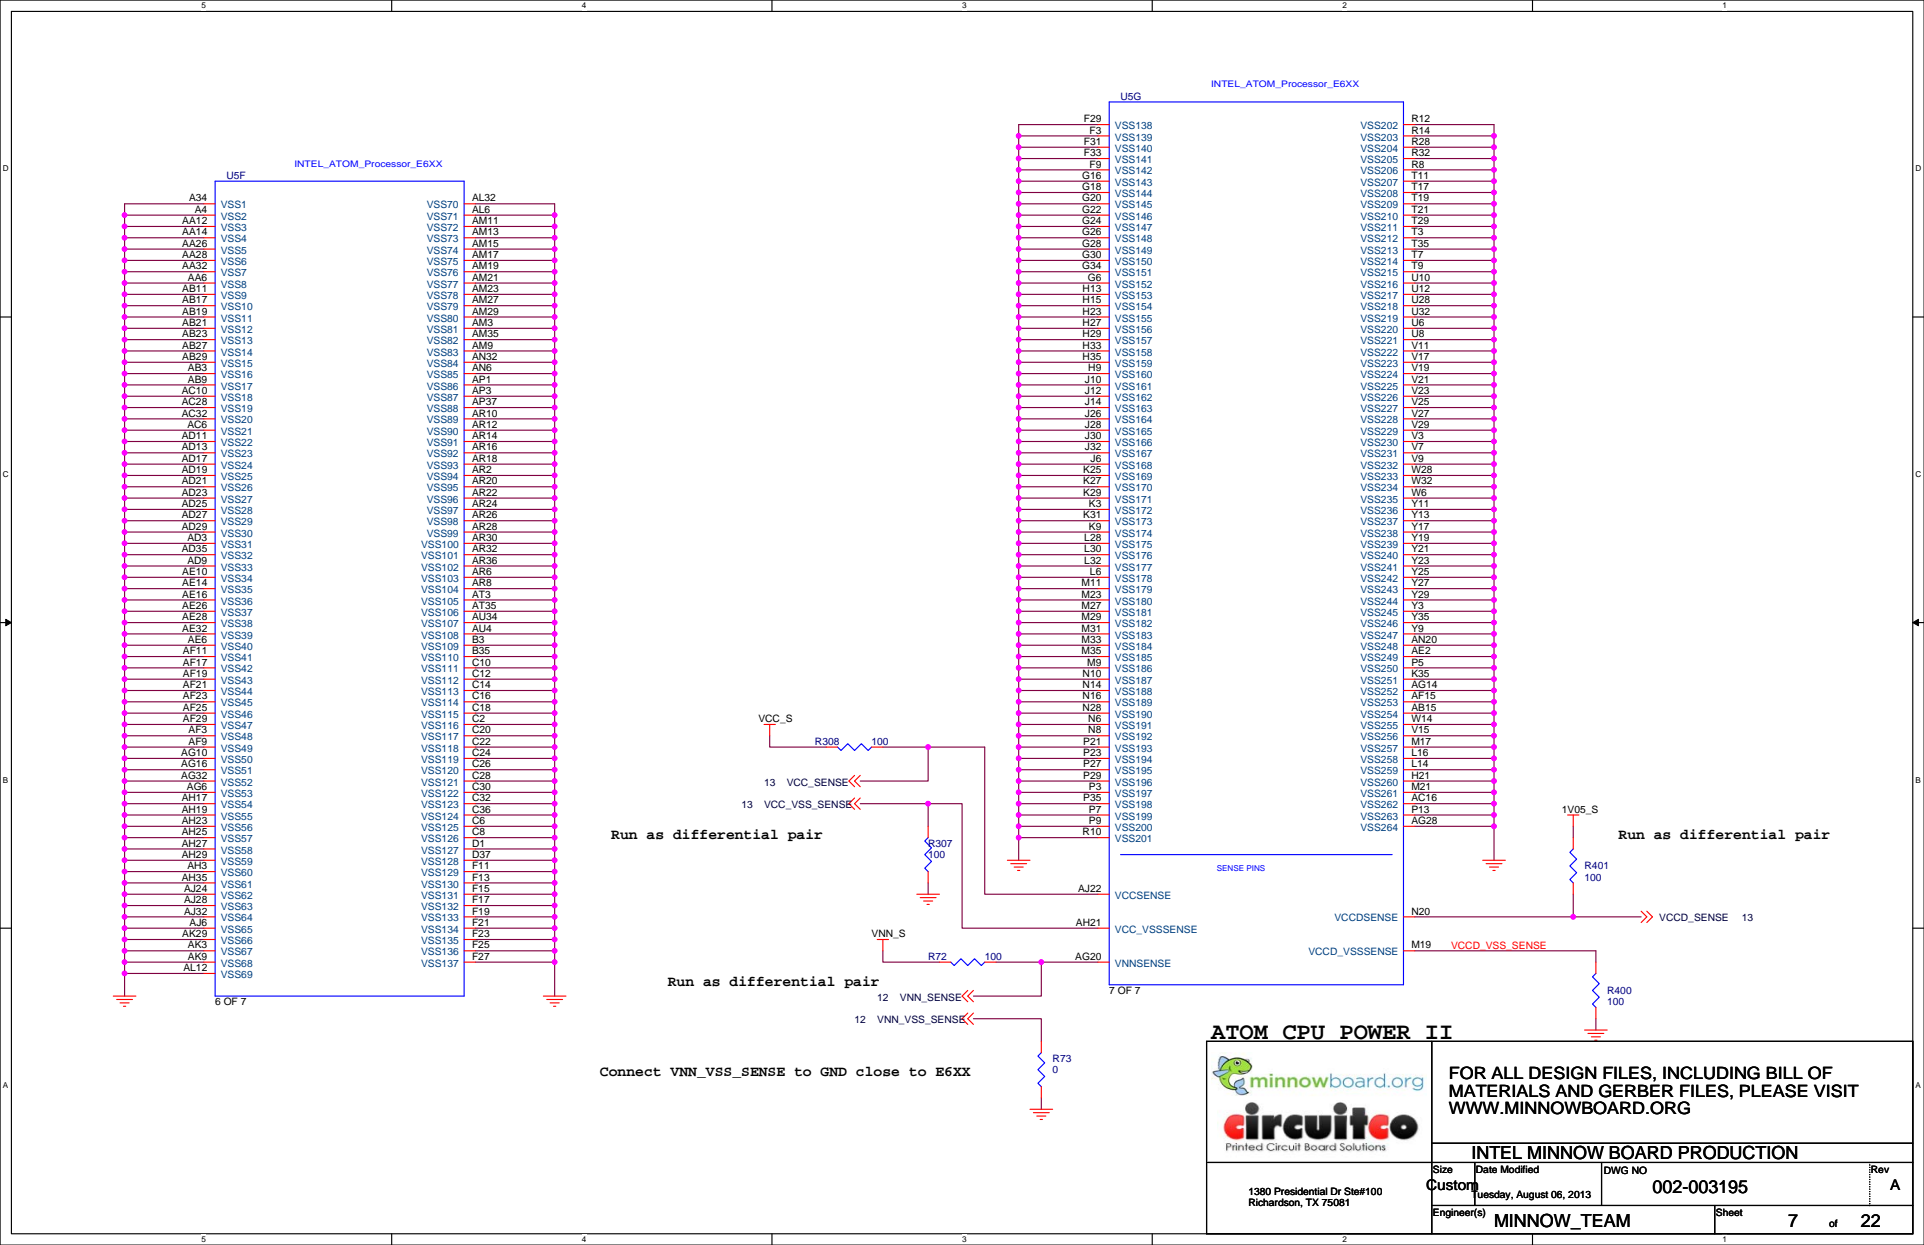
[picture p195: page 7]

Run as differential pair

ATOM CPU POWER II

Connect VNN_VSS_SENSE to GND close to E6XX

FOR ALL DESIGN FILES, INCLUDING BILL OF
MATERIALS AND GERBER FILES, PLEASE VISIT
WWW.MINNOWBOARD.ORG

## EMI Place holders

### DNI

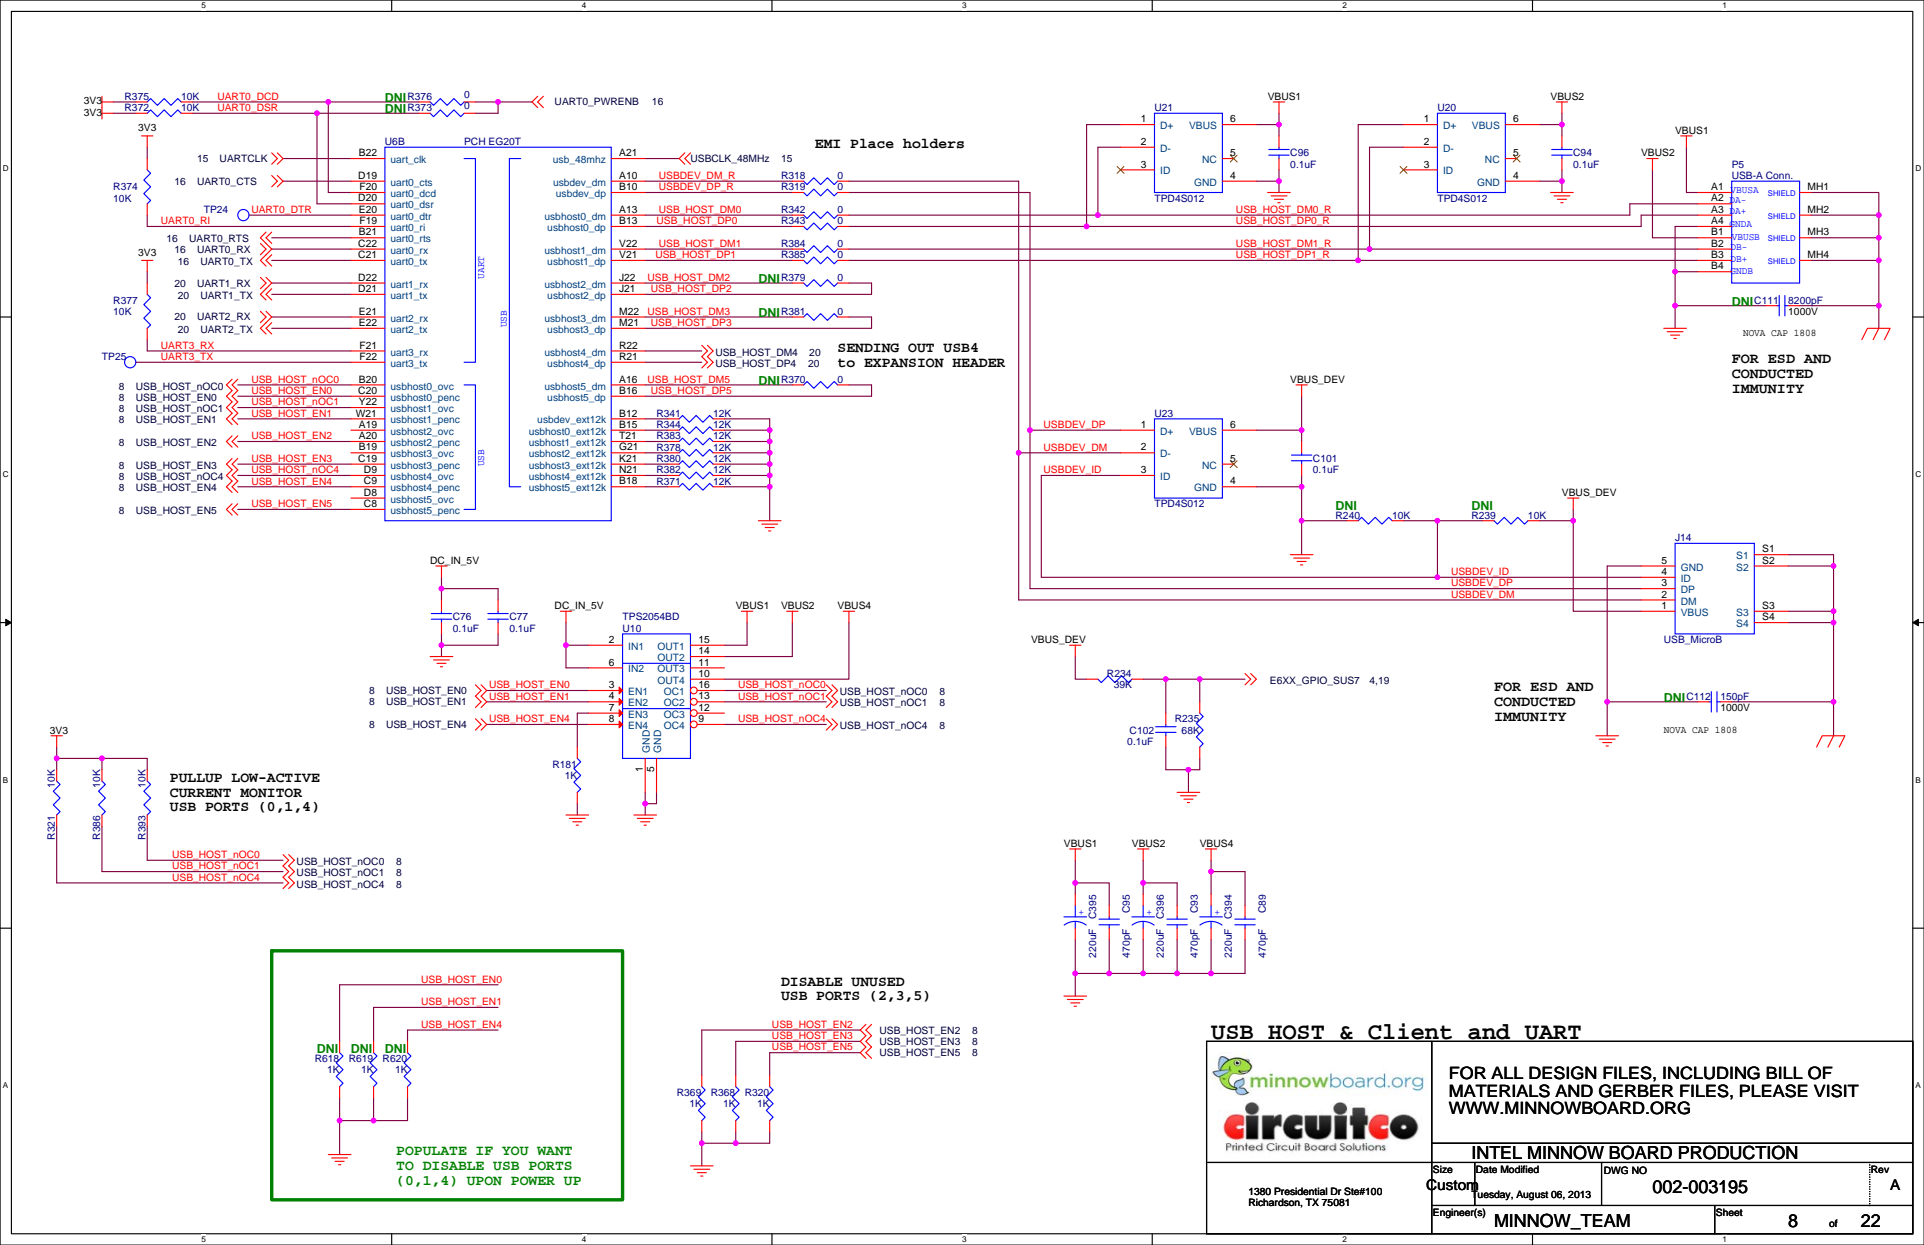
[picture p196: page 8]

USB HOST & Client and UART

FOR ALL DESIGN FILES, INCLUDING BILL OF
MATERIALS AND GERBER FILES, PLEASE VISIT
WWW.MINNOWBOARD.ORG

POPULATE IF YOU WANT
TO DISABLE USB PORTS
(0,1,4) UPON POWER UP

### DNI

R300 100

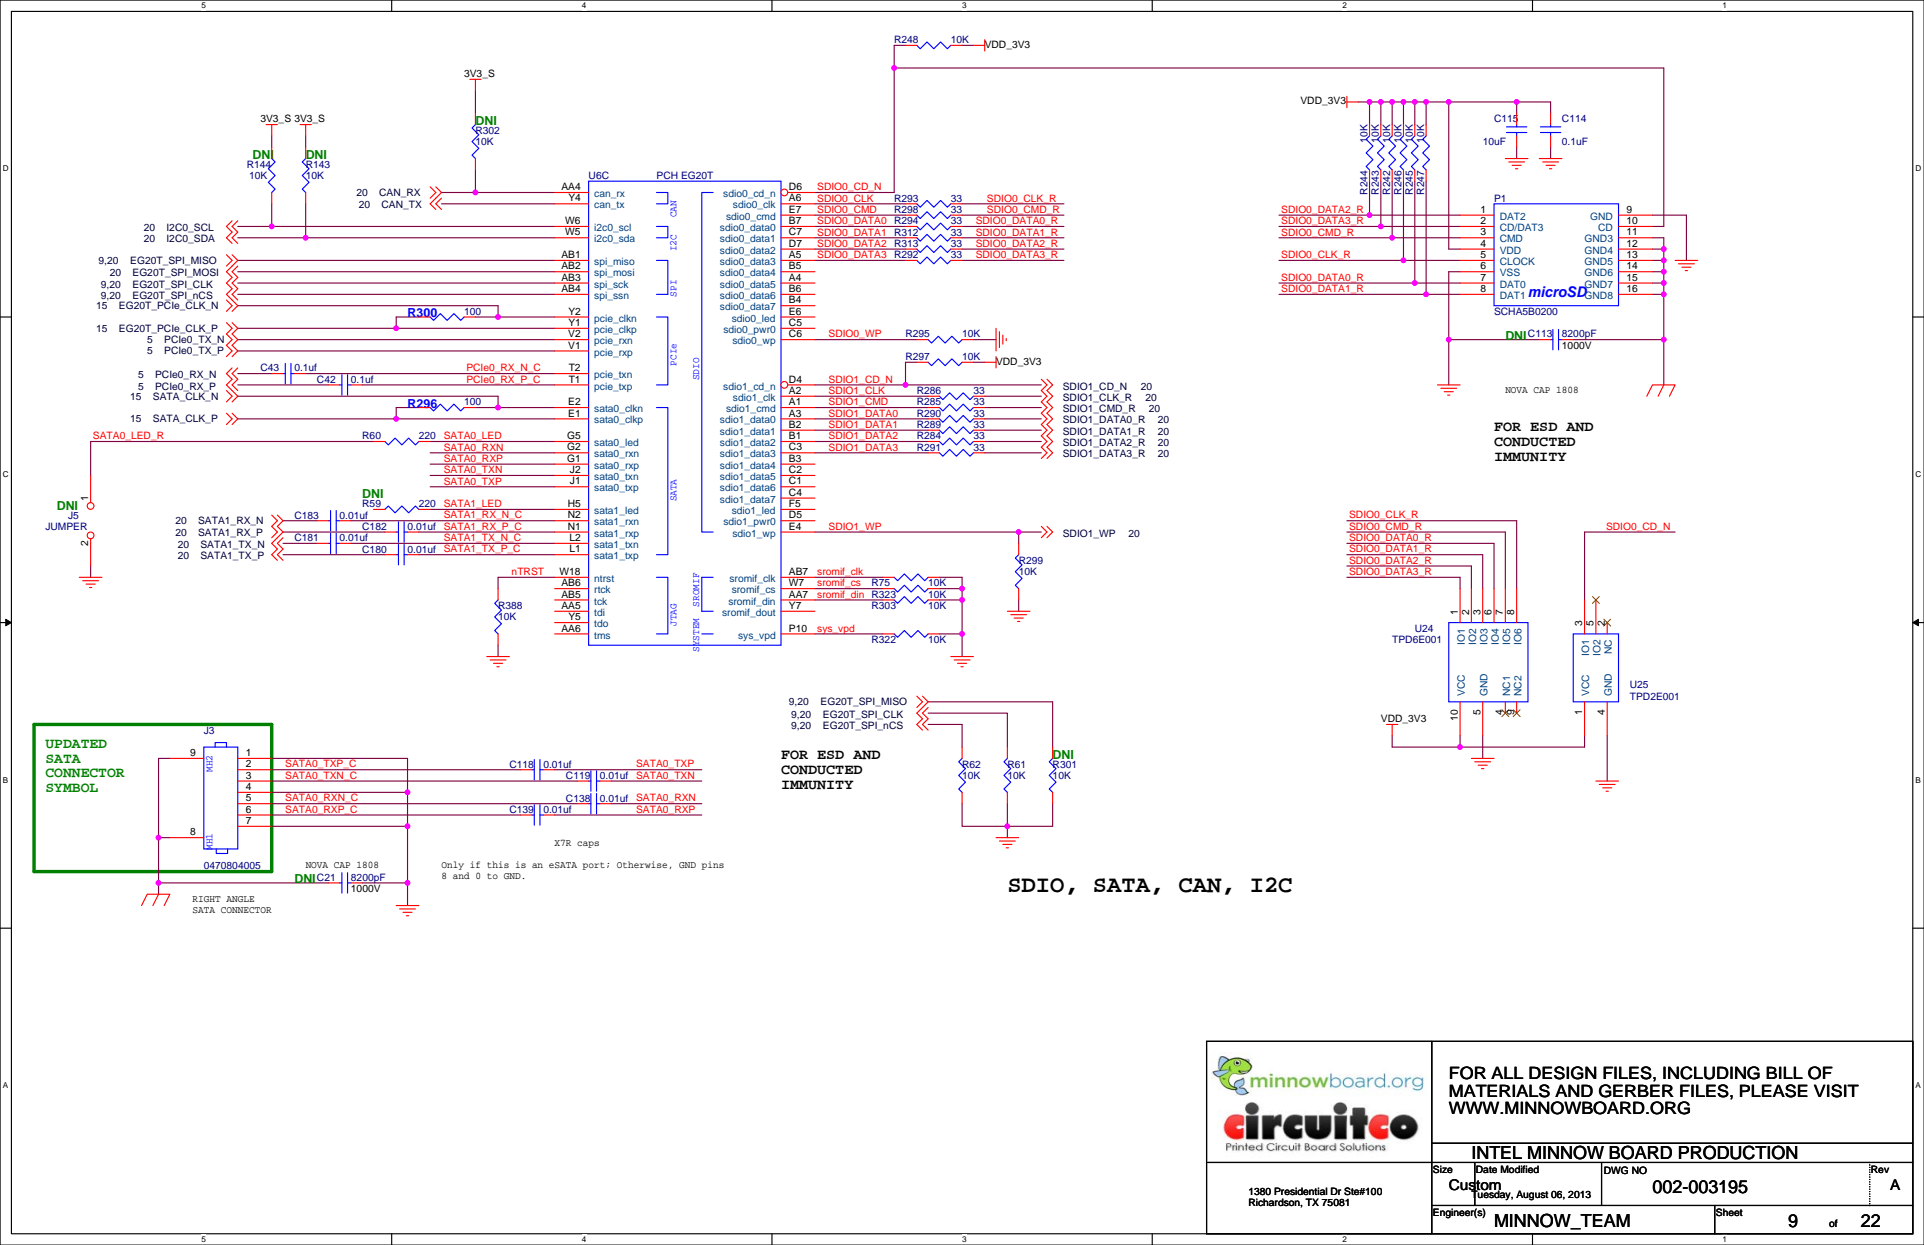
[picture p197: page 9]

CAN I2C JTAG PCIe SATA SPI

2 | SATA0_TXP_C
3 | SATA0_TXN_C | | C119 | 0.01uf SATA0_TXN
5 | SATA0_RXN_C
6 | SATA0_RXP_C | C139 | 0.01uf | SATA0_RXP

Only if this is an eSATA port; Otherwise, GND pins

FOR ALL DESIGN FILES, INCLUDING BILL OF
MATERIALS AND GERBER FILES, PLEASE VISIT
WWW.MINNOWBOARD.ORG

Thick etch | Thick etch
vdd19 W4 | vdd18 V18 | vdd17 V14 | vdd16 V11 | vdd15 V6 | vdd14 R18 | vdd13 R4 | vdd12 P12 | vdd11 M18 | vdd10 M14 | vdd9 M9 | vdd8 M5 | vdd7 L14 | vdd6 L9 | vdd5 K4 | vdd4 J5 | vdd3 E16 | vdd2 E13 | vdd1 E10

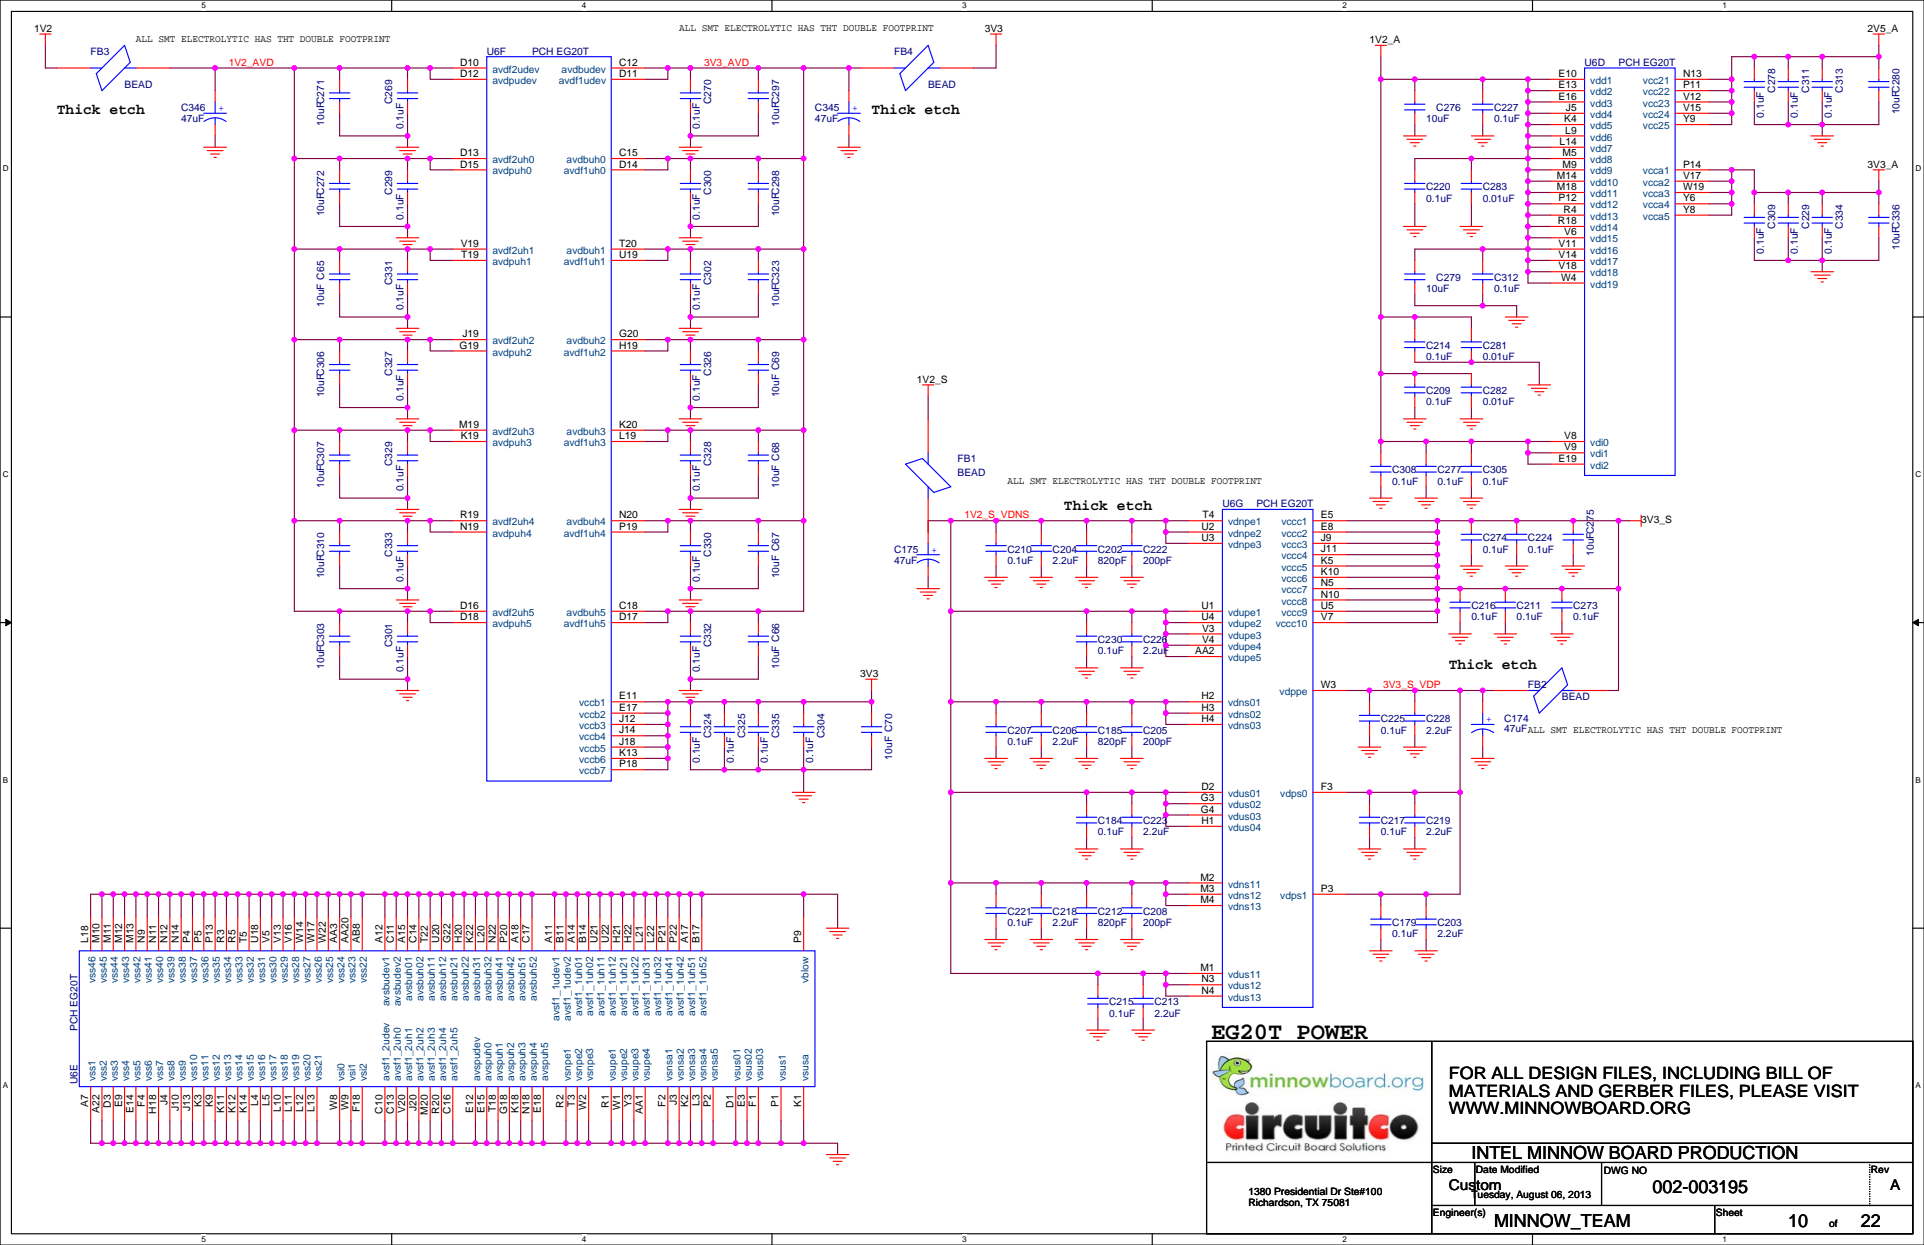
[picture p198: page 10]

ALL SMT ELECTROLYTIC HAS THT DOUBLE FOOTPRINT

avdpuh1 T19

avdpuh2 G19

avdpuh3 K19

C207 | C206 | C185 C184 | C205 | vdns02 H3 vdns03 H4 vdus01 D2

C218 | | vdns12 M3

vdus12 N3

FOR ALL DESIGN FILES, INCLUDING BILL OF
MATERIALS AND GERBER FILES, PLEASE VISIT
WWW.MINNOWBOARD.ORG

## x5r and x7r. NO Y5V

## THICK ETCH

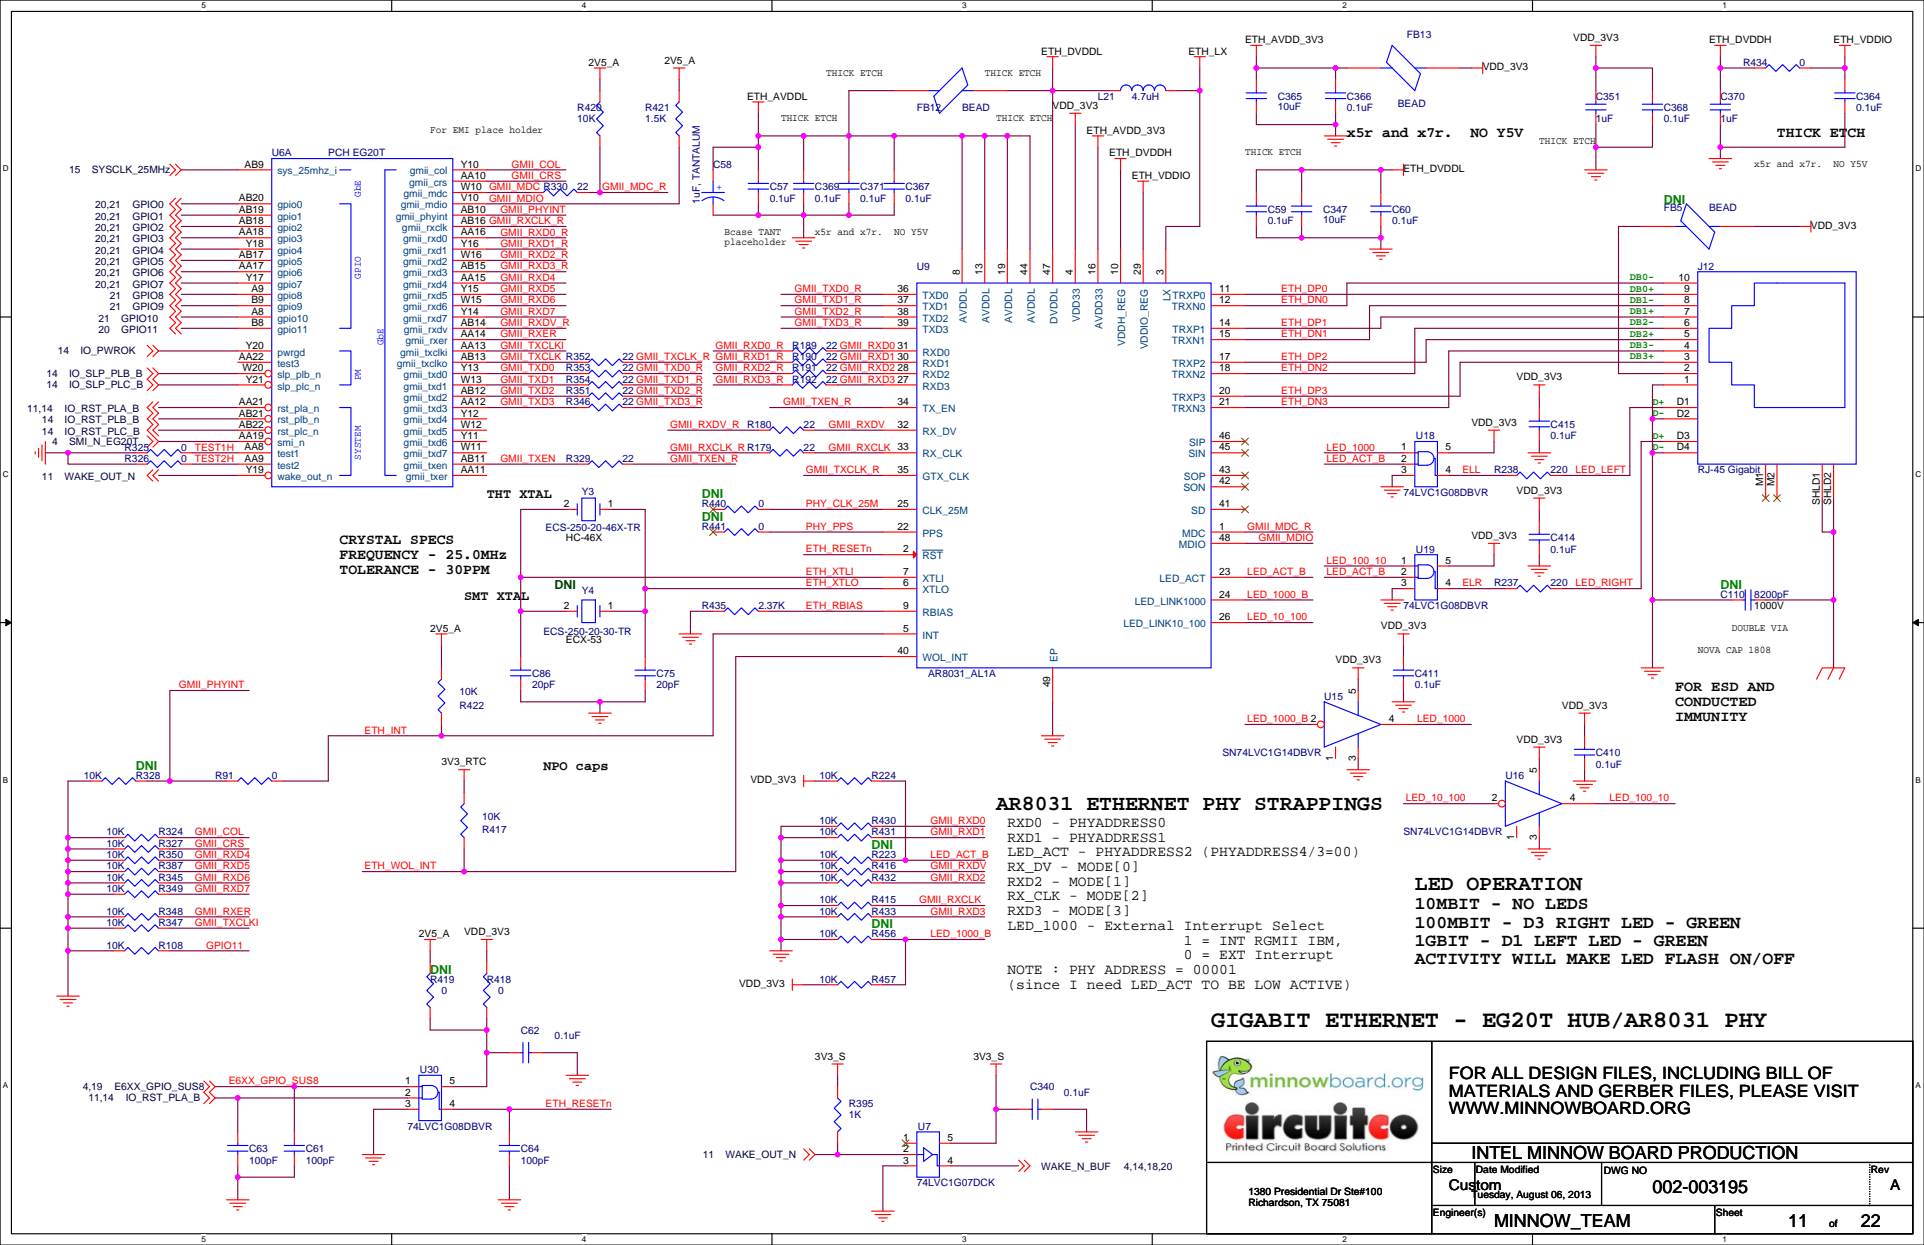
[picture p199: page 11]

For EMI place holder

GbE GPIO PM SYSTEM

SN74LVC1G14DBVR
LED OPERATION
10MBIT - NO LEDS
100MBIT - D3 RIGHT LED - GREEN
1GBIT - D1 LEFT LED - GREEN
ACTIVITY WILL MAKE LED FLASH ON/OFF

NOTE : PHY ADDRESS = 00001
(since I need LED_ACT TO BE LOW ACTIVE)

GIGABIT ETHERNET - EG20T HUB/AR8031 PHY

FOR ALL DESIGN FILES, INCLUDING BILL OF
MATERIALS AND GERBER FILES, PLEASE VISIT
WWW.MINNOWBOARD.ORG

## THICK ETCH

### DNI

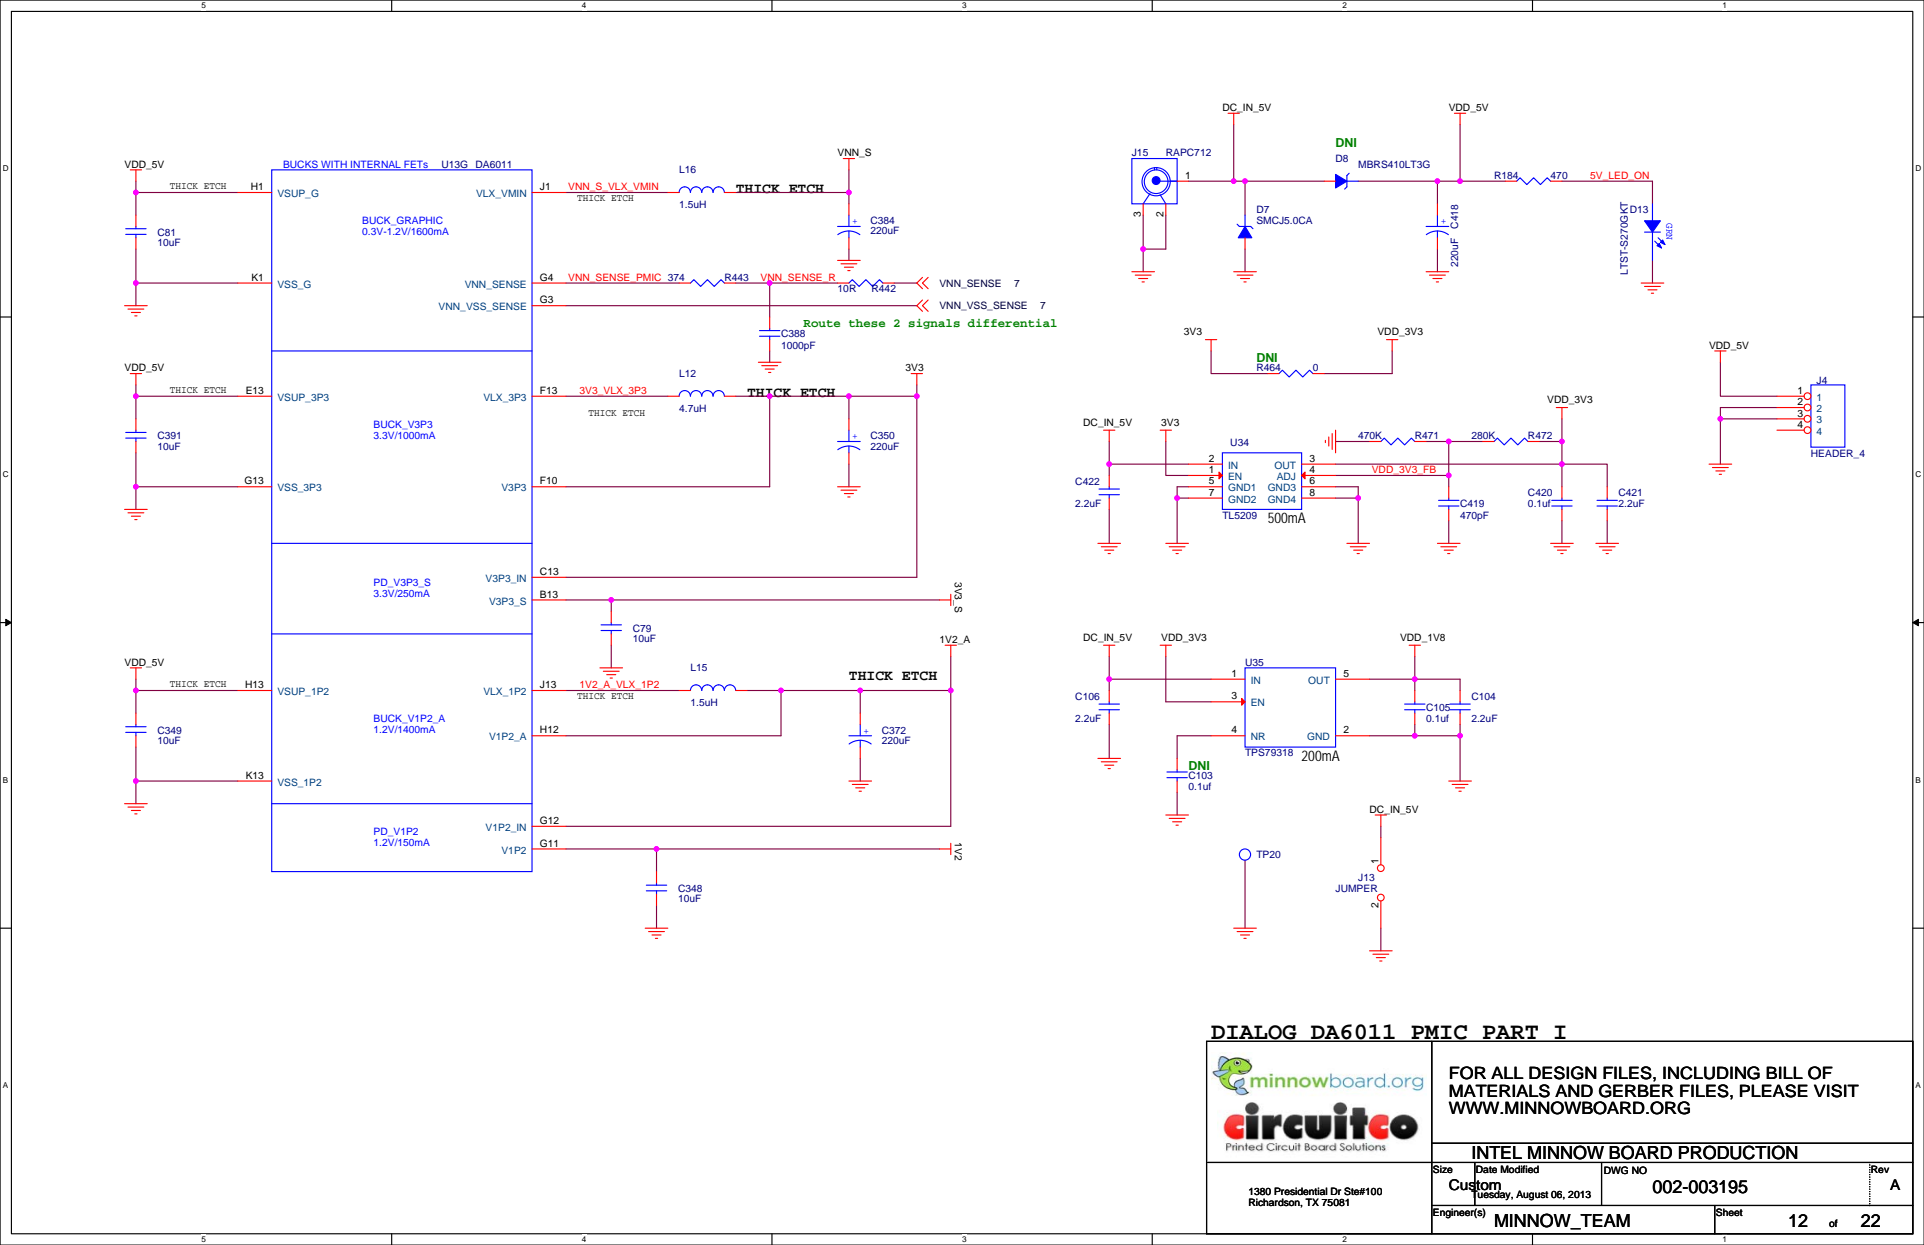
[picture p200: page 12]

BUCKS WITH INTERNAL FETs

FOR ALL DESIGN FILES, INCLUDING BILL OF
MATERIALS AND GERBER FILES, PLEASE VISIT
WWW.MINNOWBOARD.ORG

## NOTE: The FOLLOWING IS

CRUCIAL TO PMIC OPERATION.

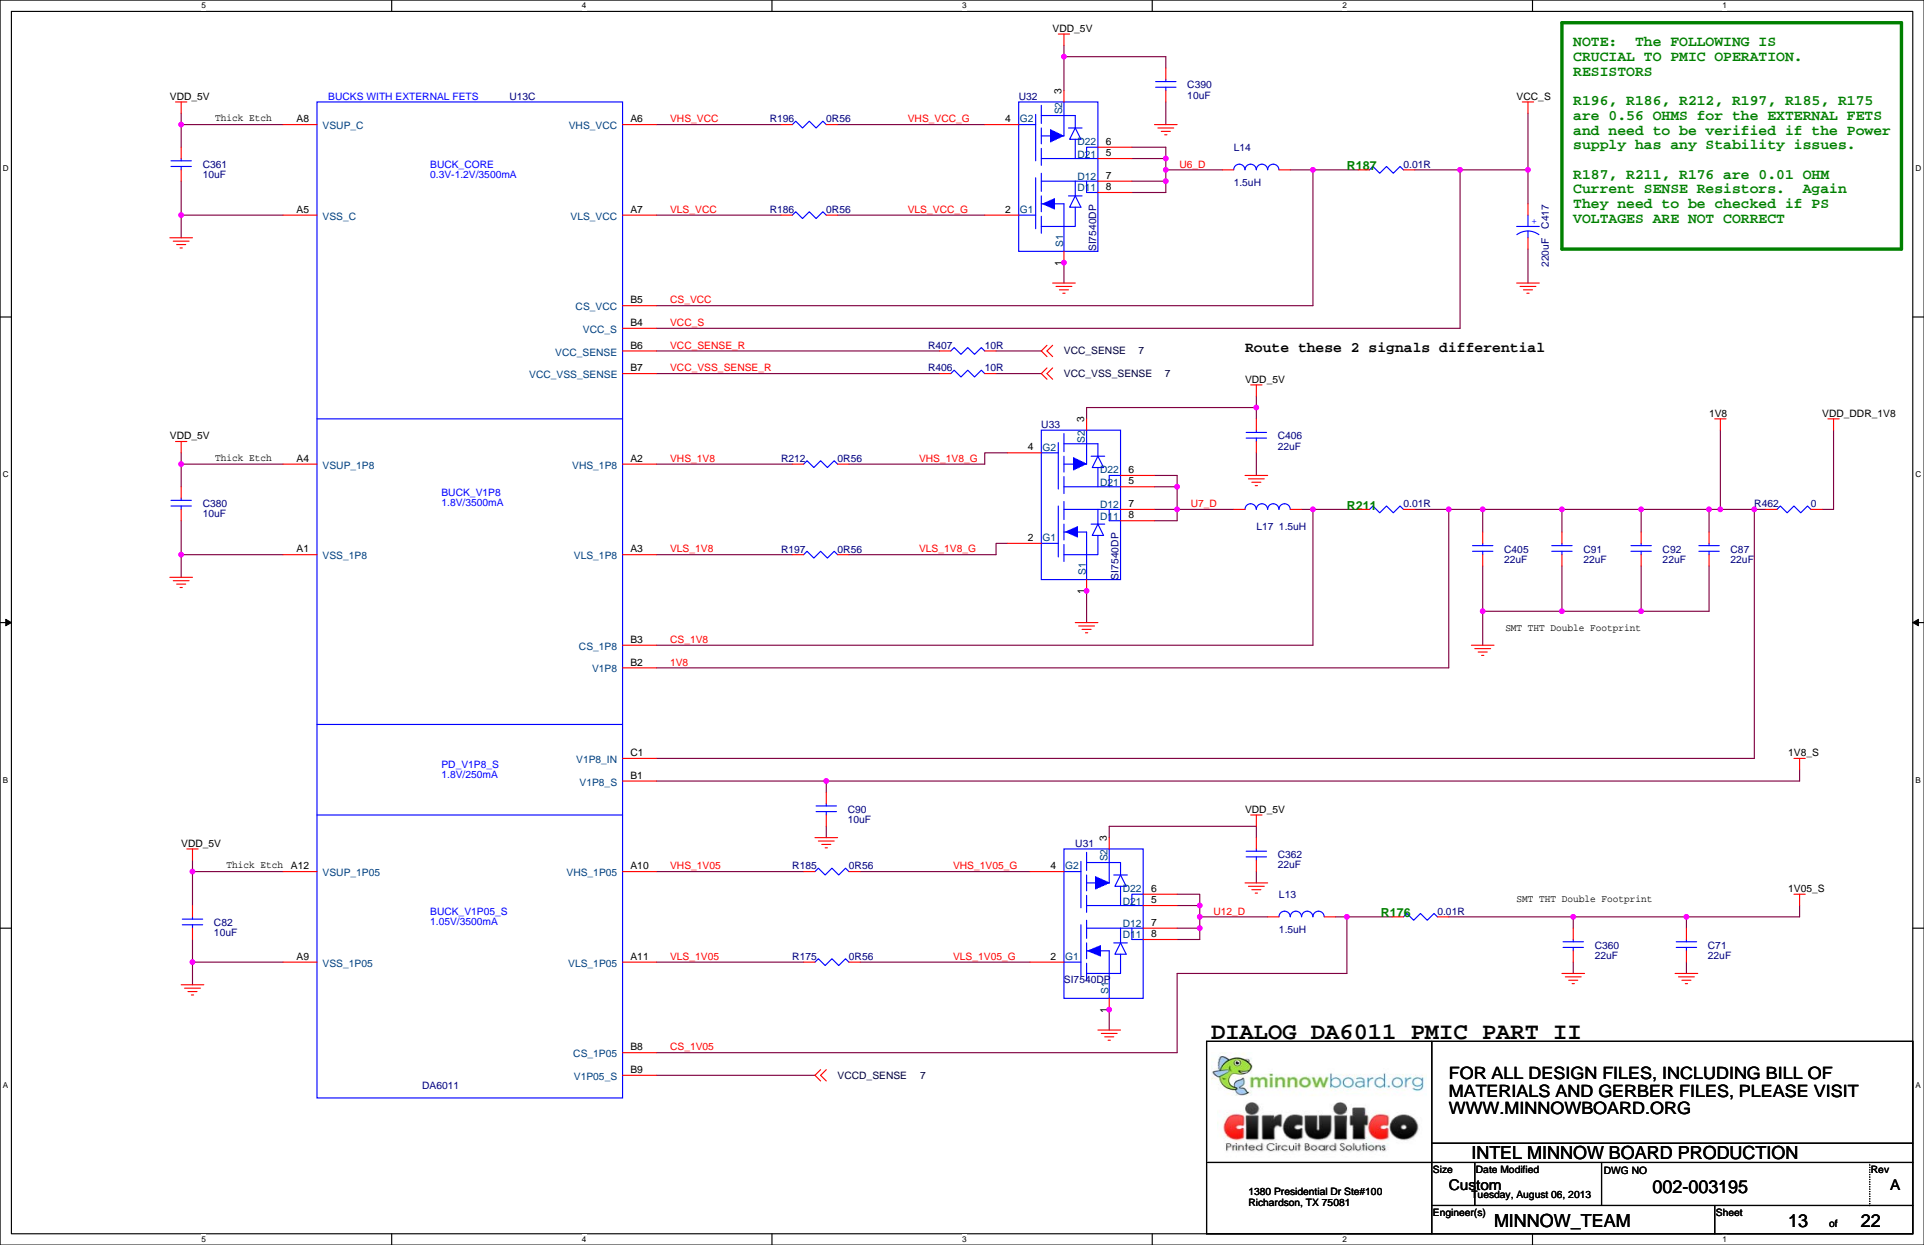
[picture p201: page 13]

RESISTORS
are 0.56 OHMS for the EXTERNAL FETS
and need to be verified if the Power
supply has any Stability issues.
R187, R211, R176 are 0.01 OHM
Current SENSE Resistors. Again
They need to be checked if PS
+ C⁴¹⁷ 220uF
VOLTAGES ARE NOT CORRECT

Route these 2 signals differential

SMT THT Double Footprint

DIALOG DA6011 PMIC PART II

FOR ALL DESIGN FILES, INCLUDING BILL OF
MATERIALS AND GERBER FILES, PLEASE VISIT
WWW.MINNOWBOARD.ORG

### DNI

### DNI

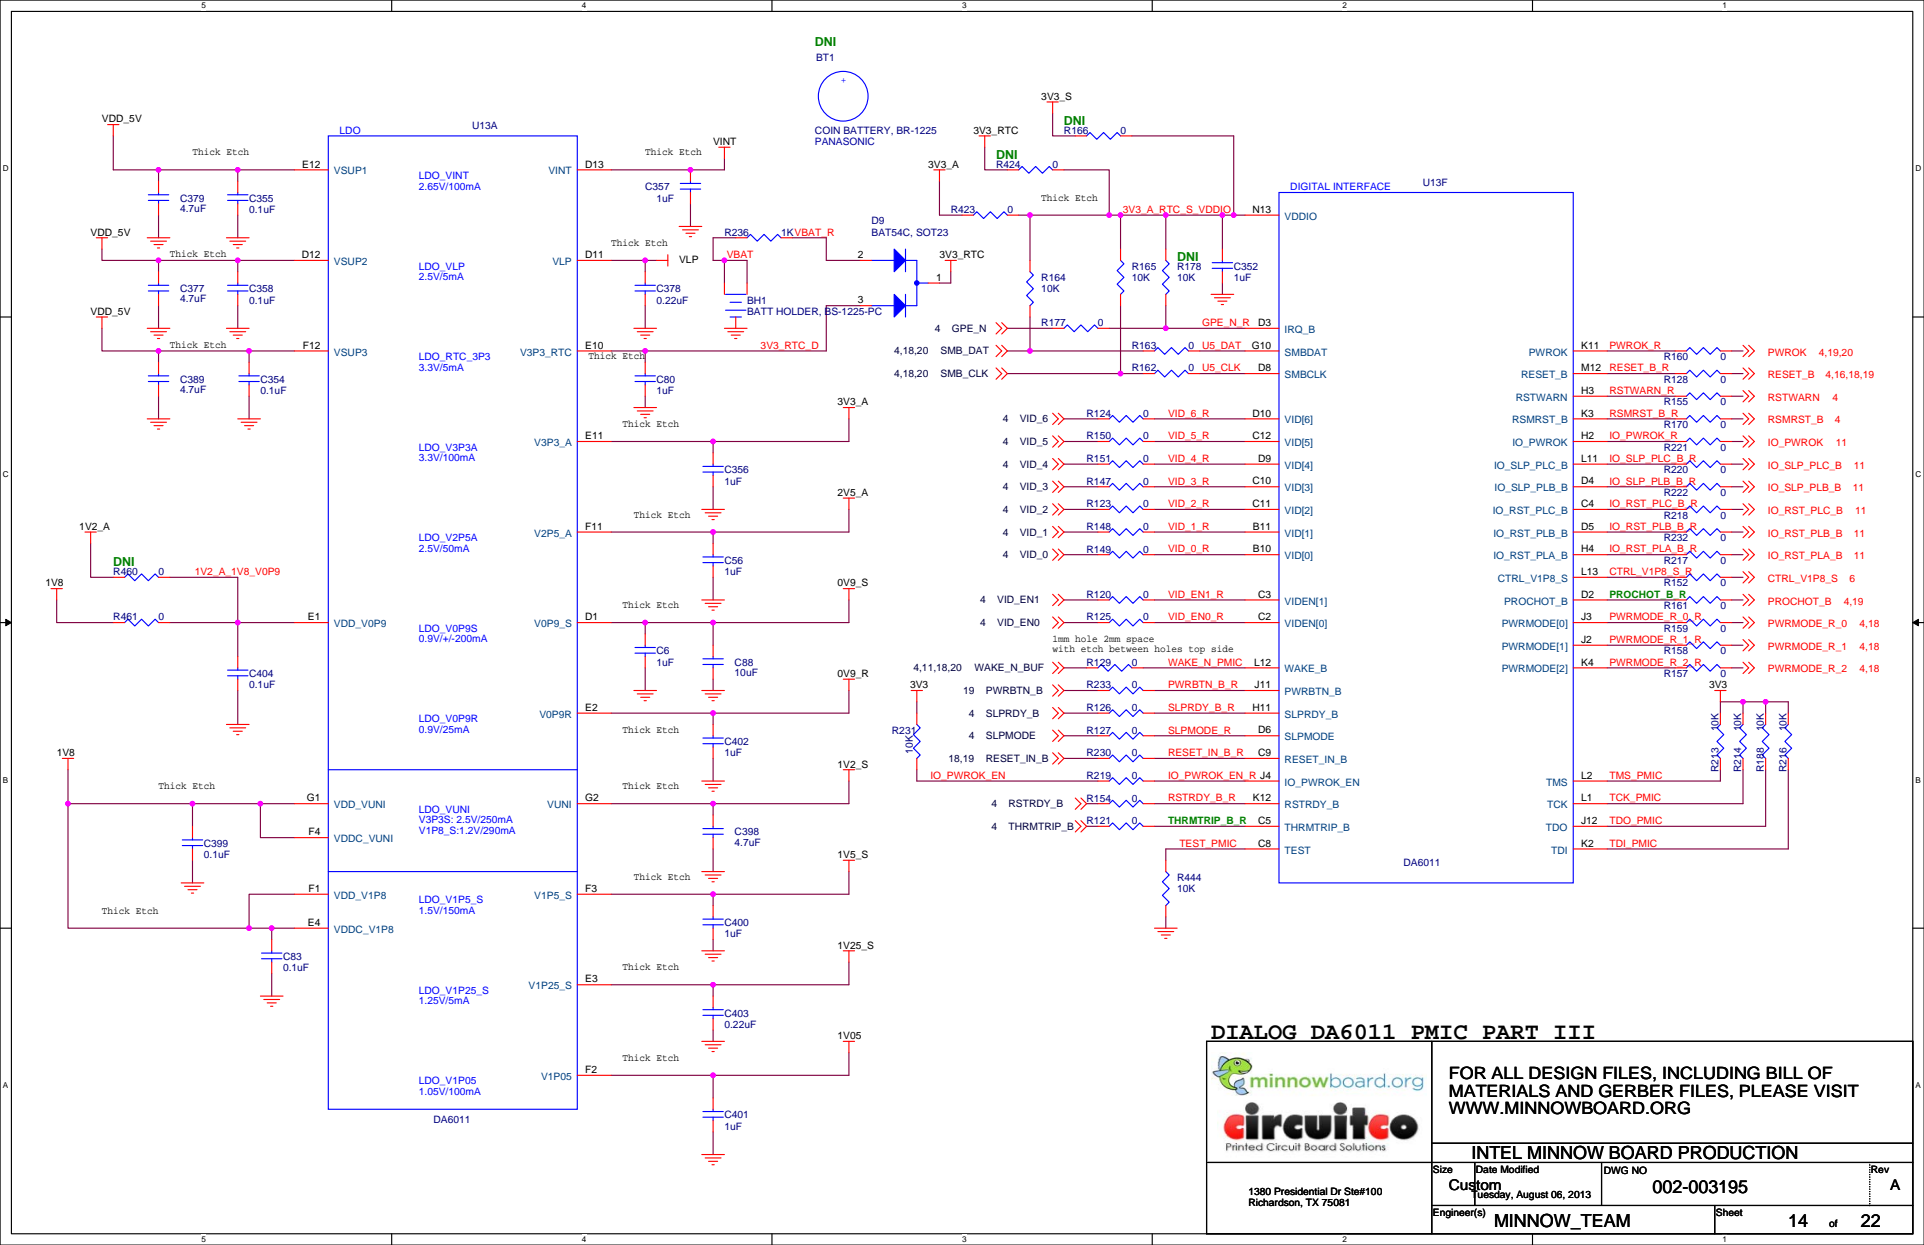
[picture p202: page 14]

BATT HOLDER, BS-1225-PC

1mm hole 2mm space
with etch between holes top side

DIALOG DA6011 PMIC PART III

FOR ALL DESIGN FILES, INCLUDING BILL OF
MATERIALS AND GERBER FILES, PLEASE VISIT
WWW.MINNOWBOARD.ORG

## THT XTAL

C359 | VSS_QUIET D7 | SMT XTAL

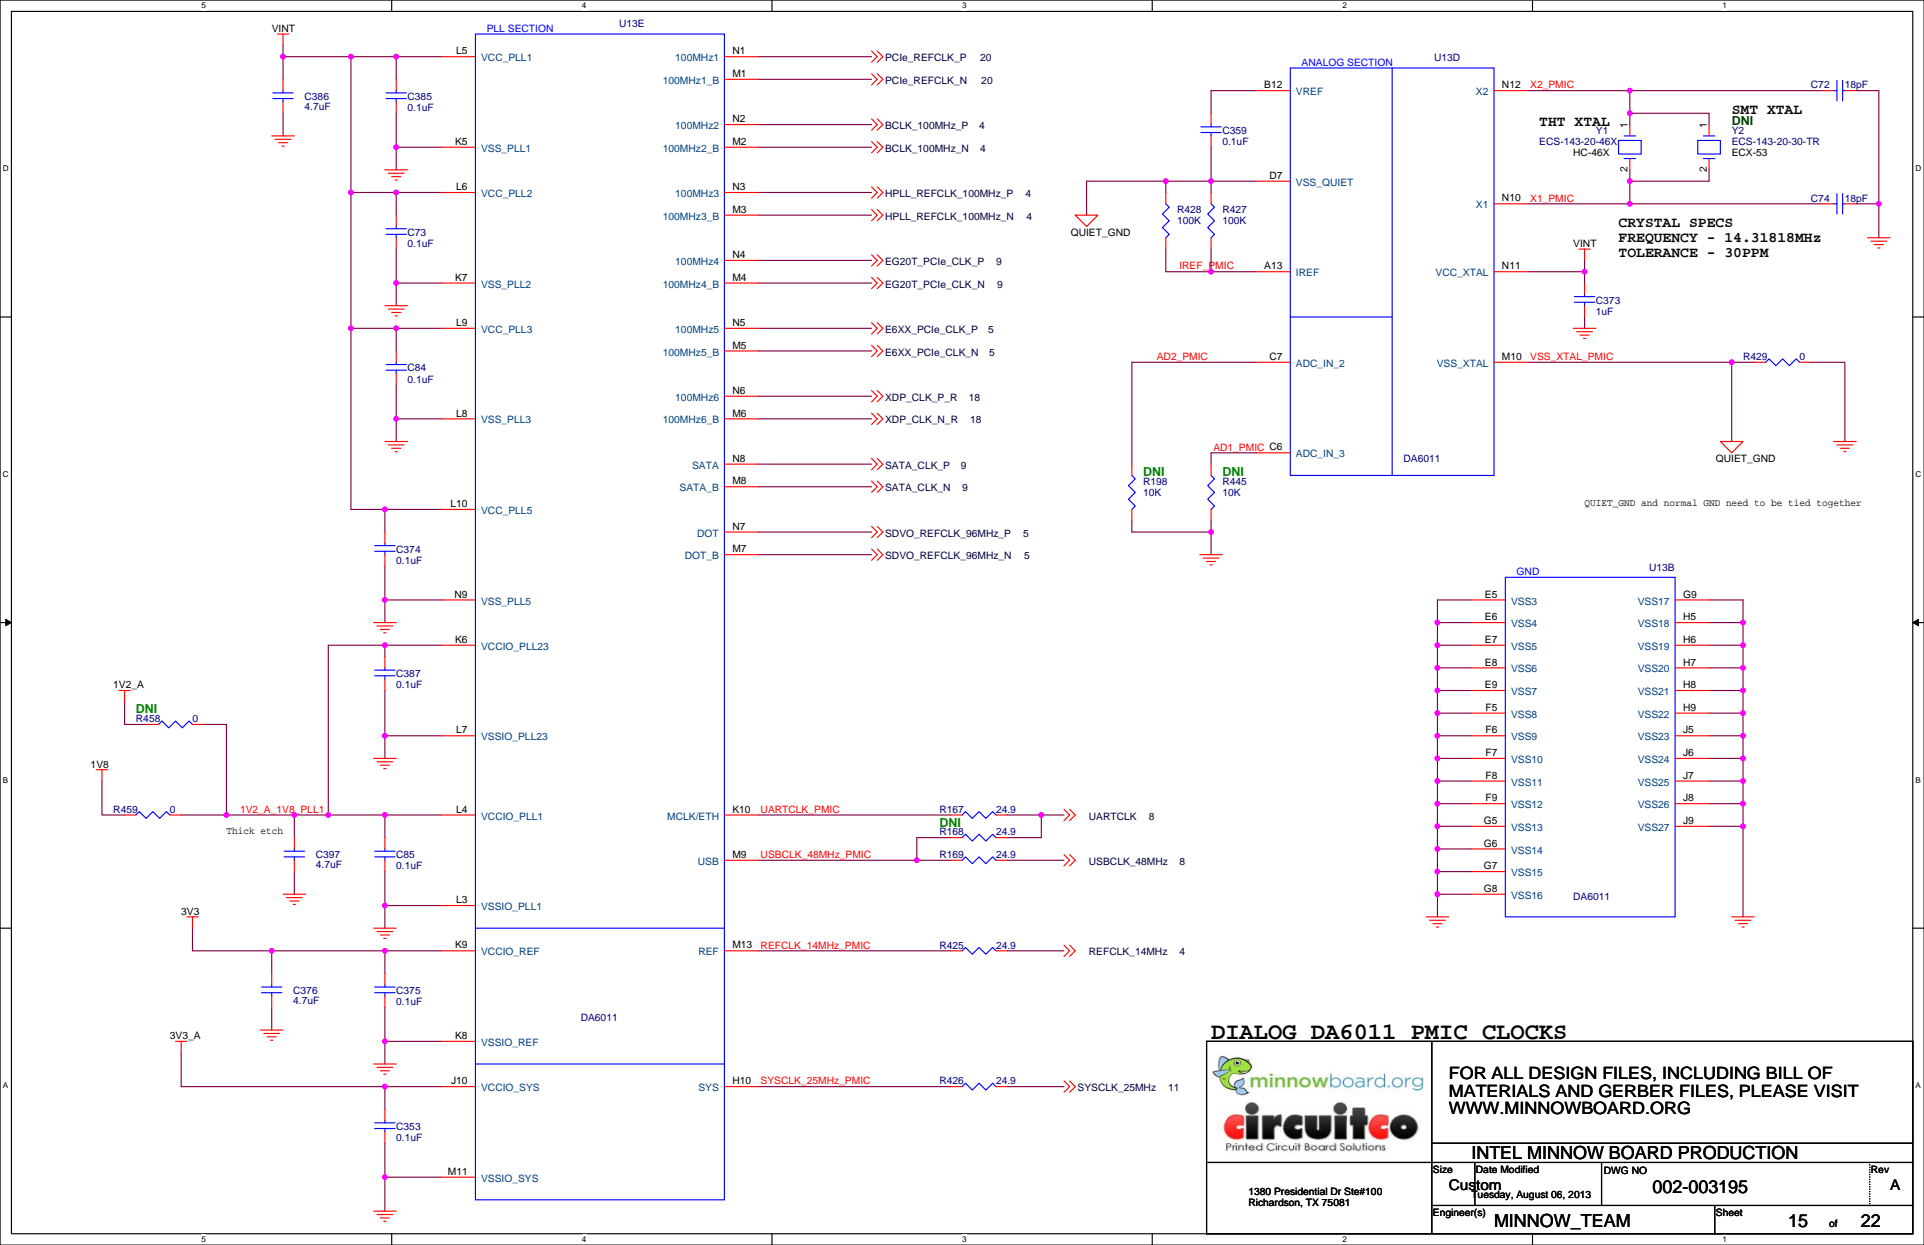
[picture p203: page 15]

VREF B12

QUIET_GND and normal GND need to be tied together

FOR ALL DESIGN FILES, INCLUDING BILL OF
MATERIALS AND GERBER FILES, PLEASE VISIT
WWW.MINNOWBOARD.ORG

# VDD_USB_3V3 Power Supply

## Thick etch

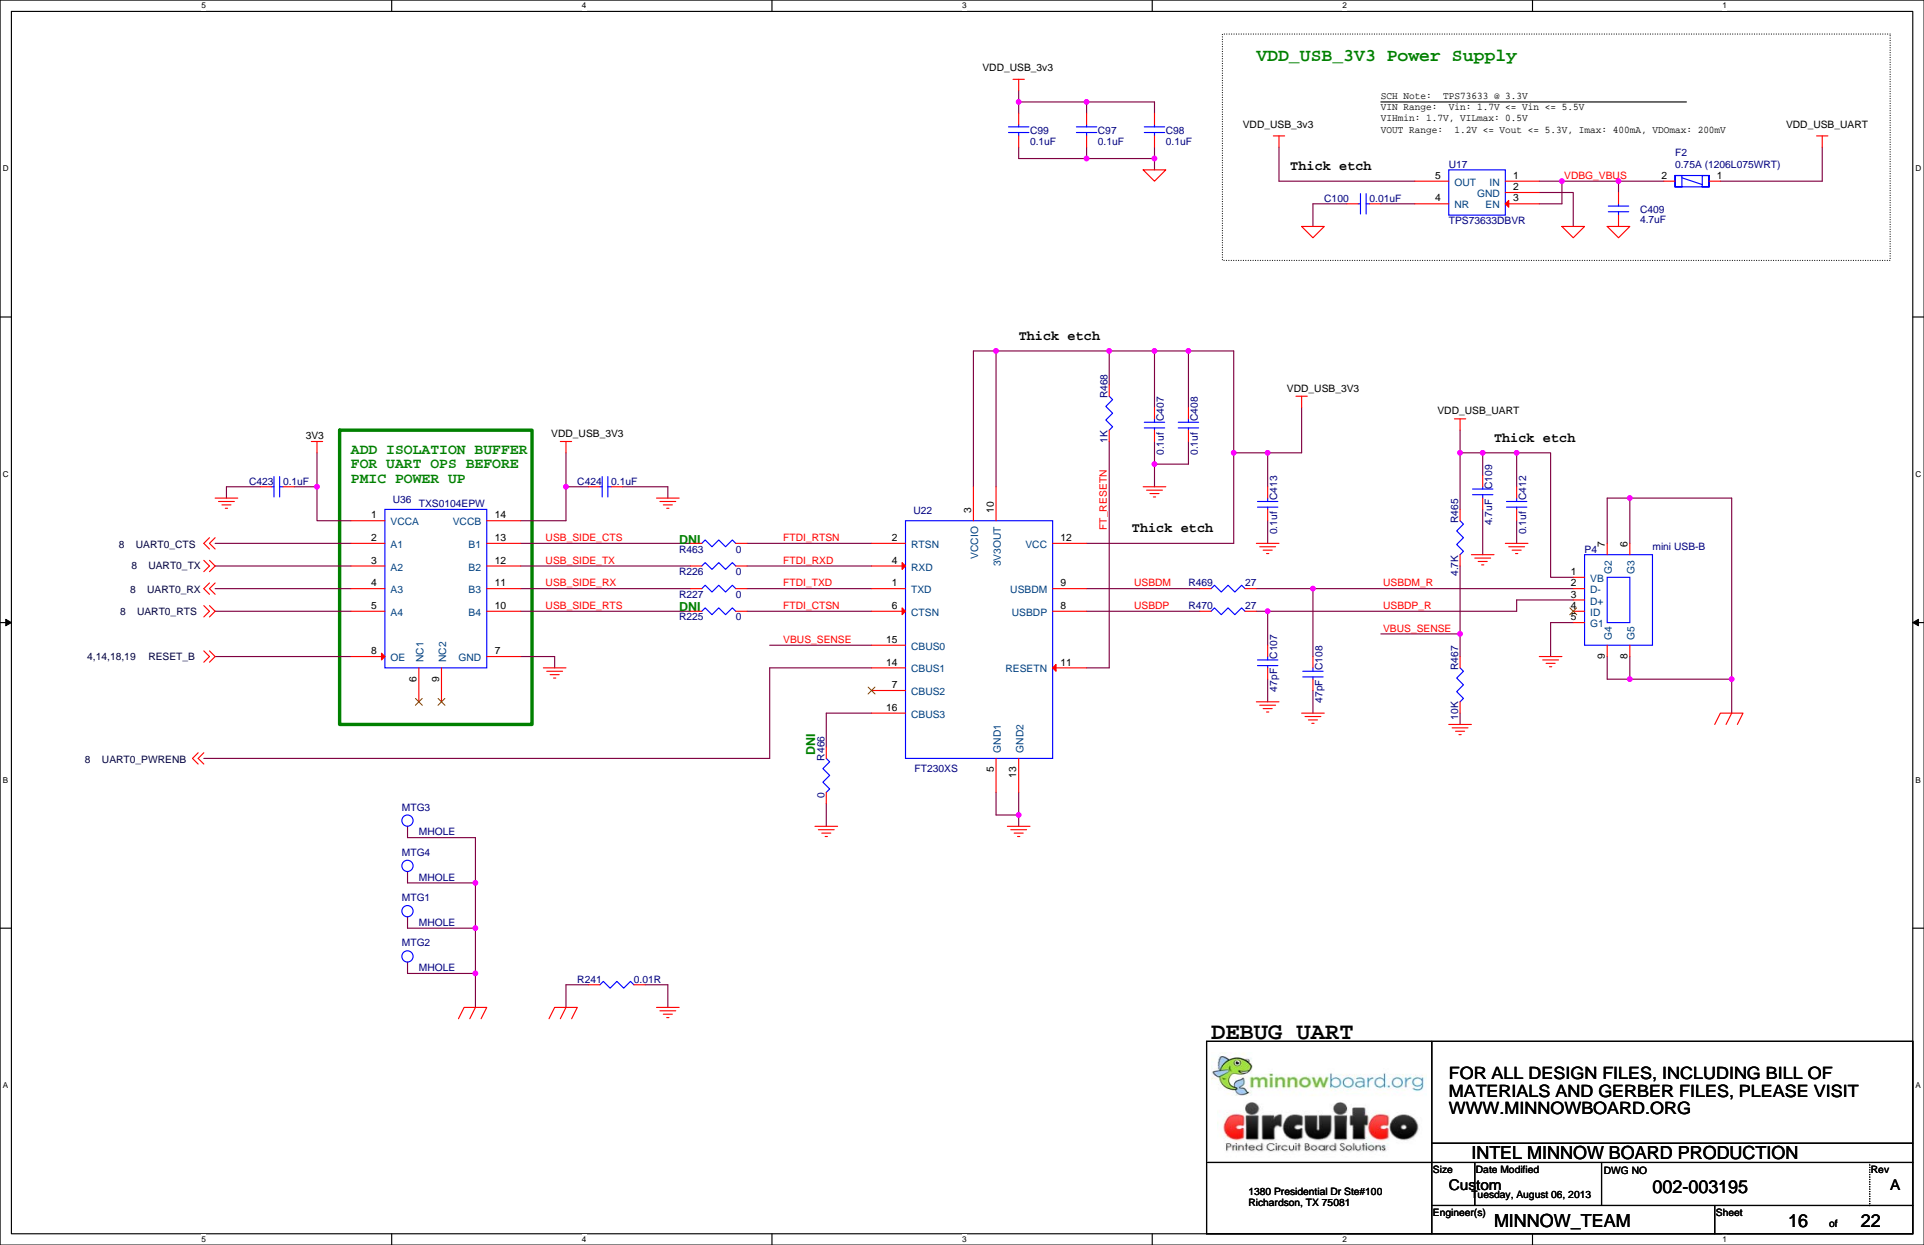
[picture p204: page 16]

SCH Note: TPS73633 @ 3.3V
VIN Range: Vin: 1.7V <= Vin <= 5.5V
VIHmin: 1.7V, VILmax: 0.5V
VOUT Range: 1.2V <= Vout <= 5.3V, Imax: 400mA, VDOmax: 200mV

ADD ISOLATION BUFFER
FOR UART OPS BEFORE
PMIC POWER UP

FOR ALL DESIGN FILES, INCLUDING BILL OF
MATERIALS AND GERBER FILES, PLEASE VISIT
WWW.MINNOWBOARD.ORG

## ADD SELECTION FOR AUDIO IC

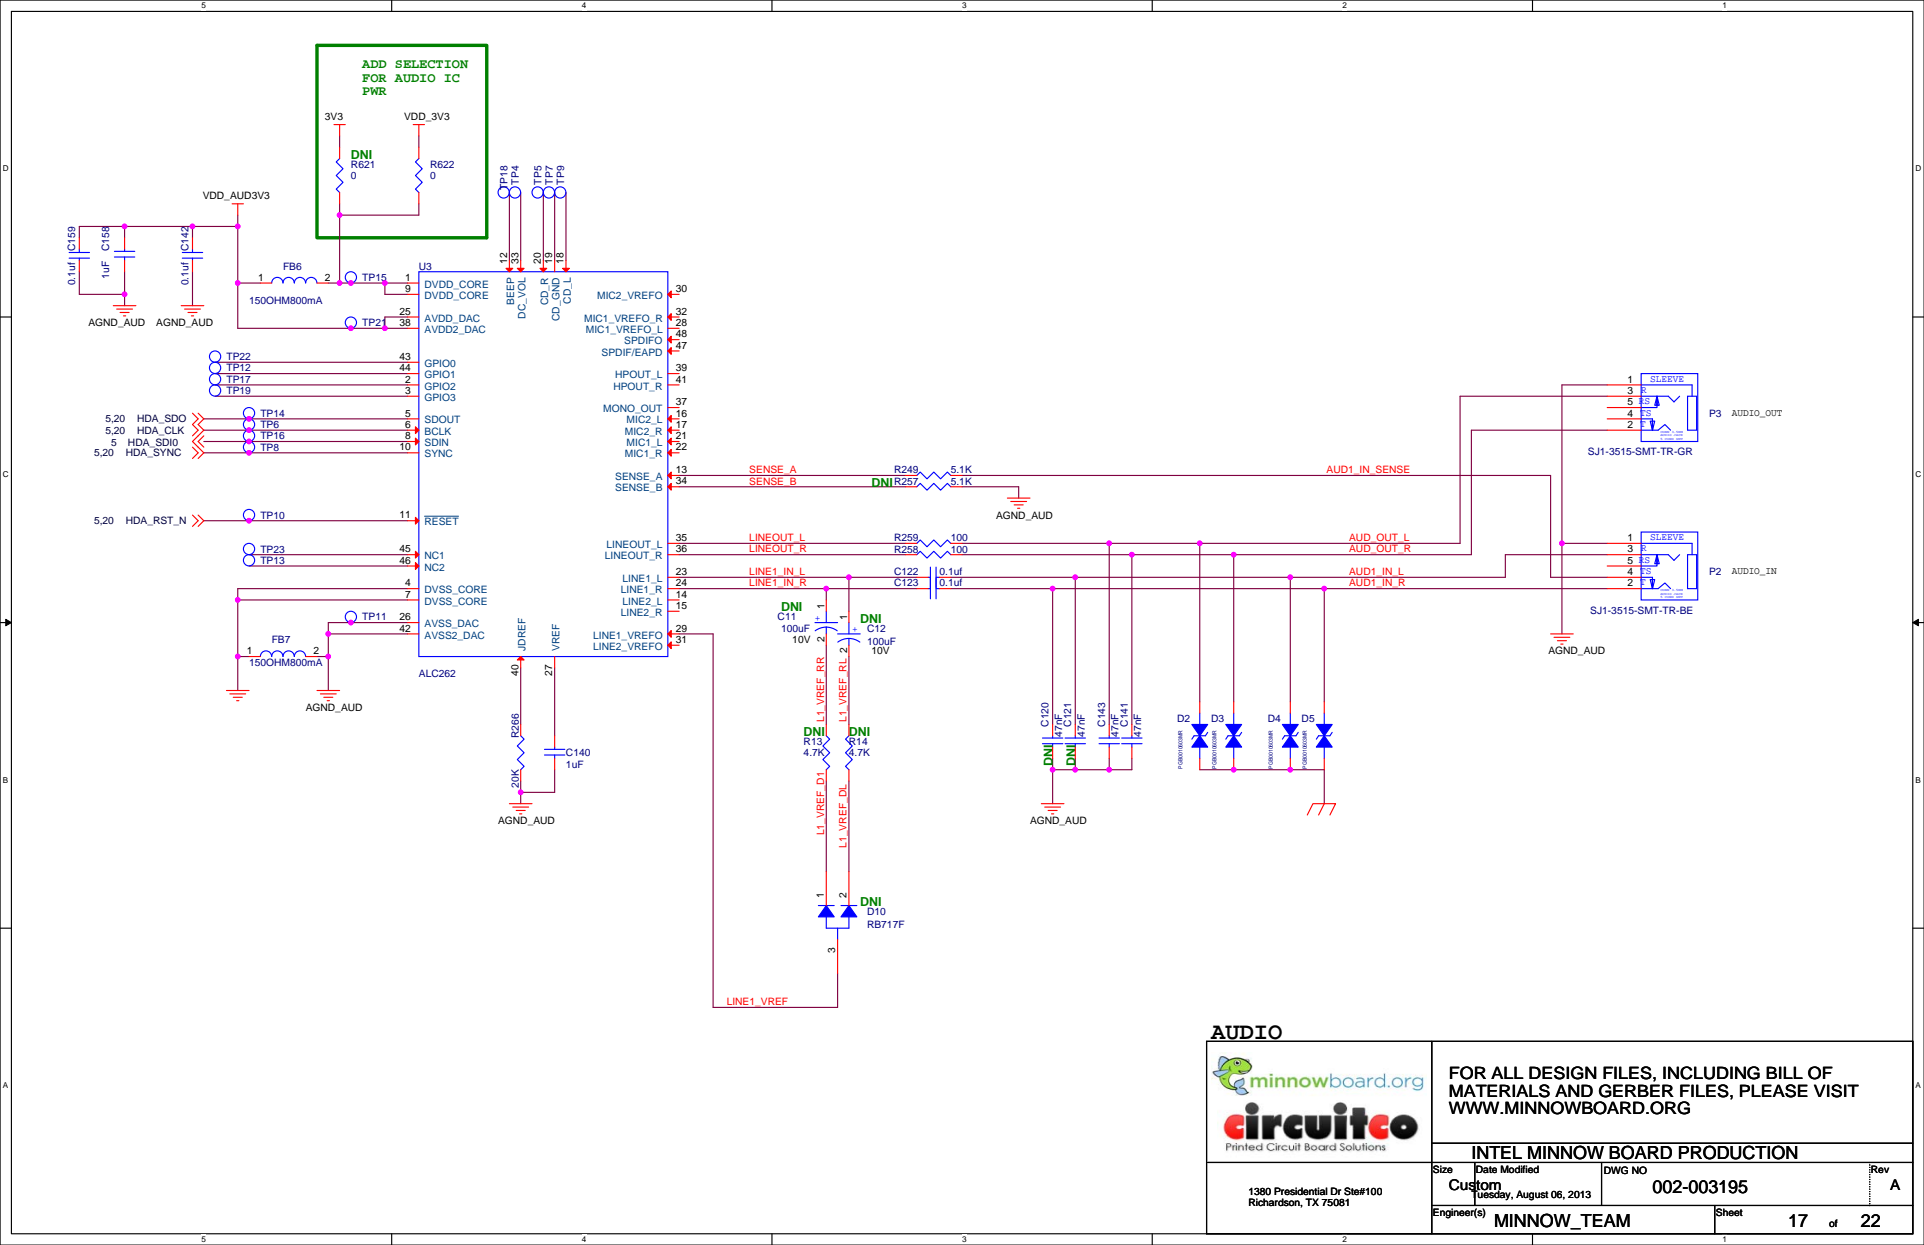
[picture p205: page 17]

FOR ALL DESIGN FILES, INCLUDING BILL OF
MATERIALS AND GERBER FILES, PLEASE VISIT
WWW.MINNOWBOARD.ORG

## NOTE: WHEN VERIFY OR PROGRAM OCCURS DEDIPROG ACTIVATES 3V3_DEDIPROG (3.3V)

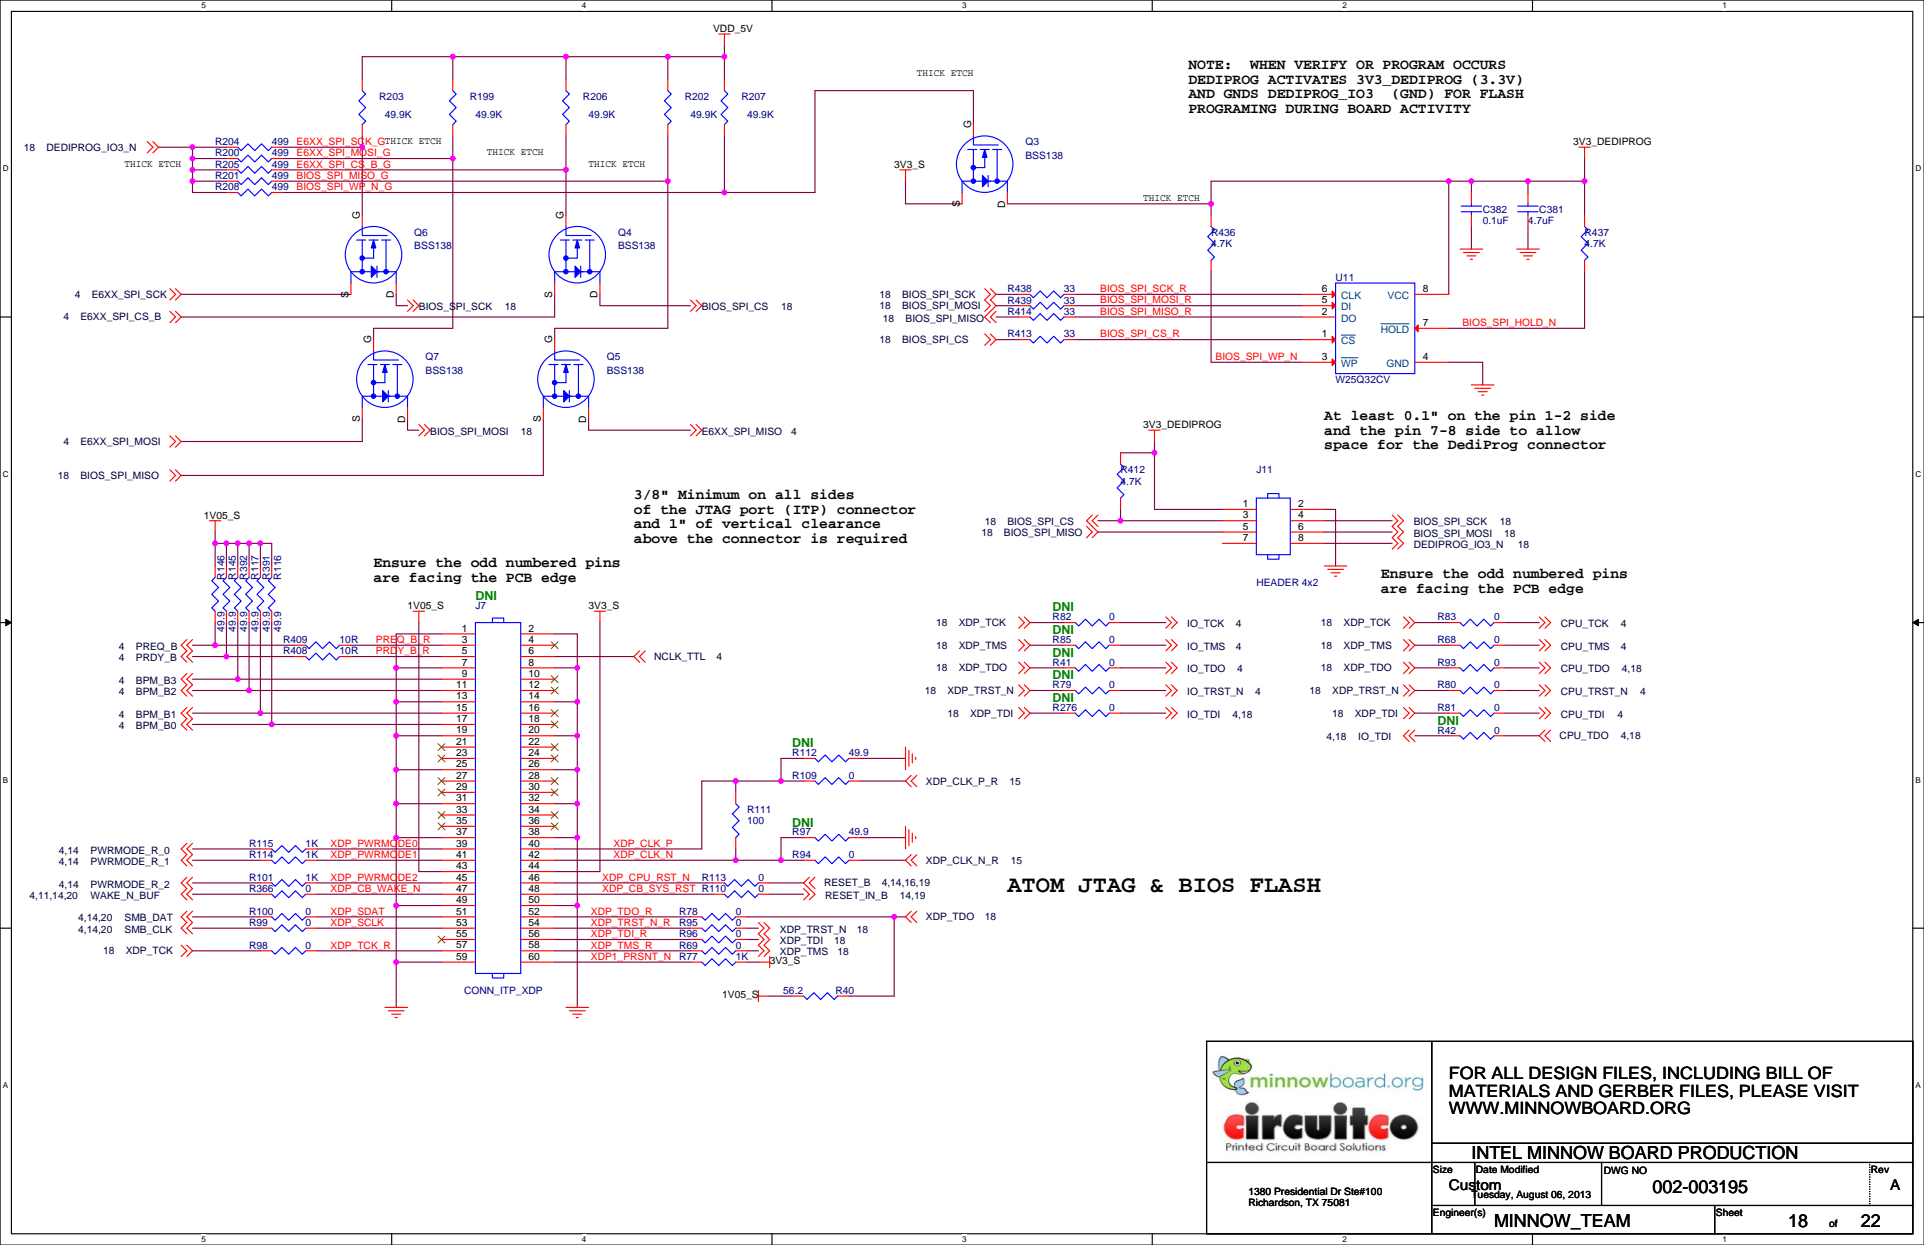
[picture p206: page 18]

AND GNDS DEDIPROG_IO3 (GND) FOR FLASH
PROGRAMING DURING BOARD ACTIVITY

R205 499 E6XX_SPI_CS_B_G
R201 499 BIOS_SPI_MISO_G
R208 499 BIOS_SPI_WP_N_G

At least 0.1" on the pin 1-2 side
and the pin 7-8 side to allow
space for the DediProg connector

3/8" Minimum on all sides
of the JTAG port (ITP) connector
and 1" of vertical clearance
above the connector is required

BIOS_SPI_SCK 18
BIOS_SPI_MOSI 18
Ensure the odd numbered pins
are facing the PCB edge

9 | | 10
11 | 12
13 | 14
15 | | 16
17 | | 18
19 | | 20
21 23 25 | | 22

42 | | XDP_CLK_N
44

ATOM JTAG & BIOS FLASH

FOR ALL DESIGN FILES, INCLUDING BILL OF
MATERIALS AND GERBER FILES, PLEASE VISIT
WWW.MINNOWBOARD.ORG

# ATOM BOOTSTRAP DEFINITIONS

GPIO(0) | = BOOT FLASH SRC (1=SPI)

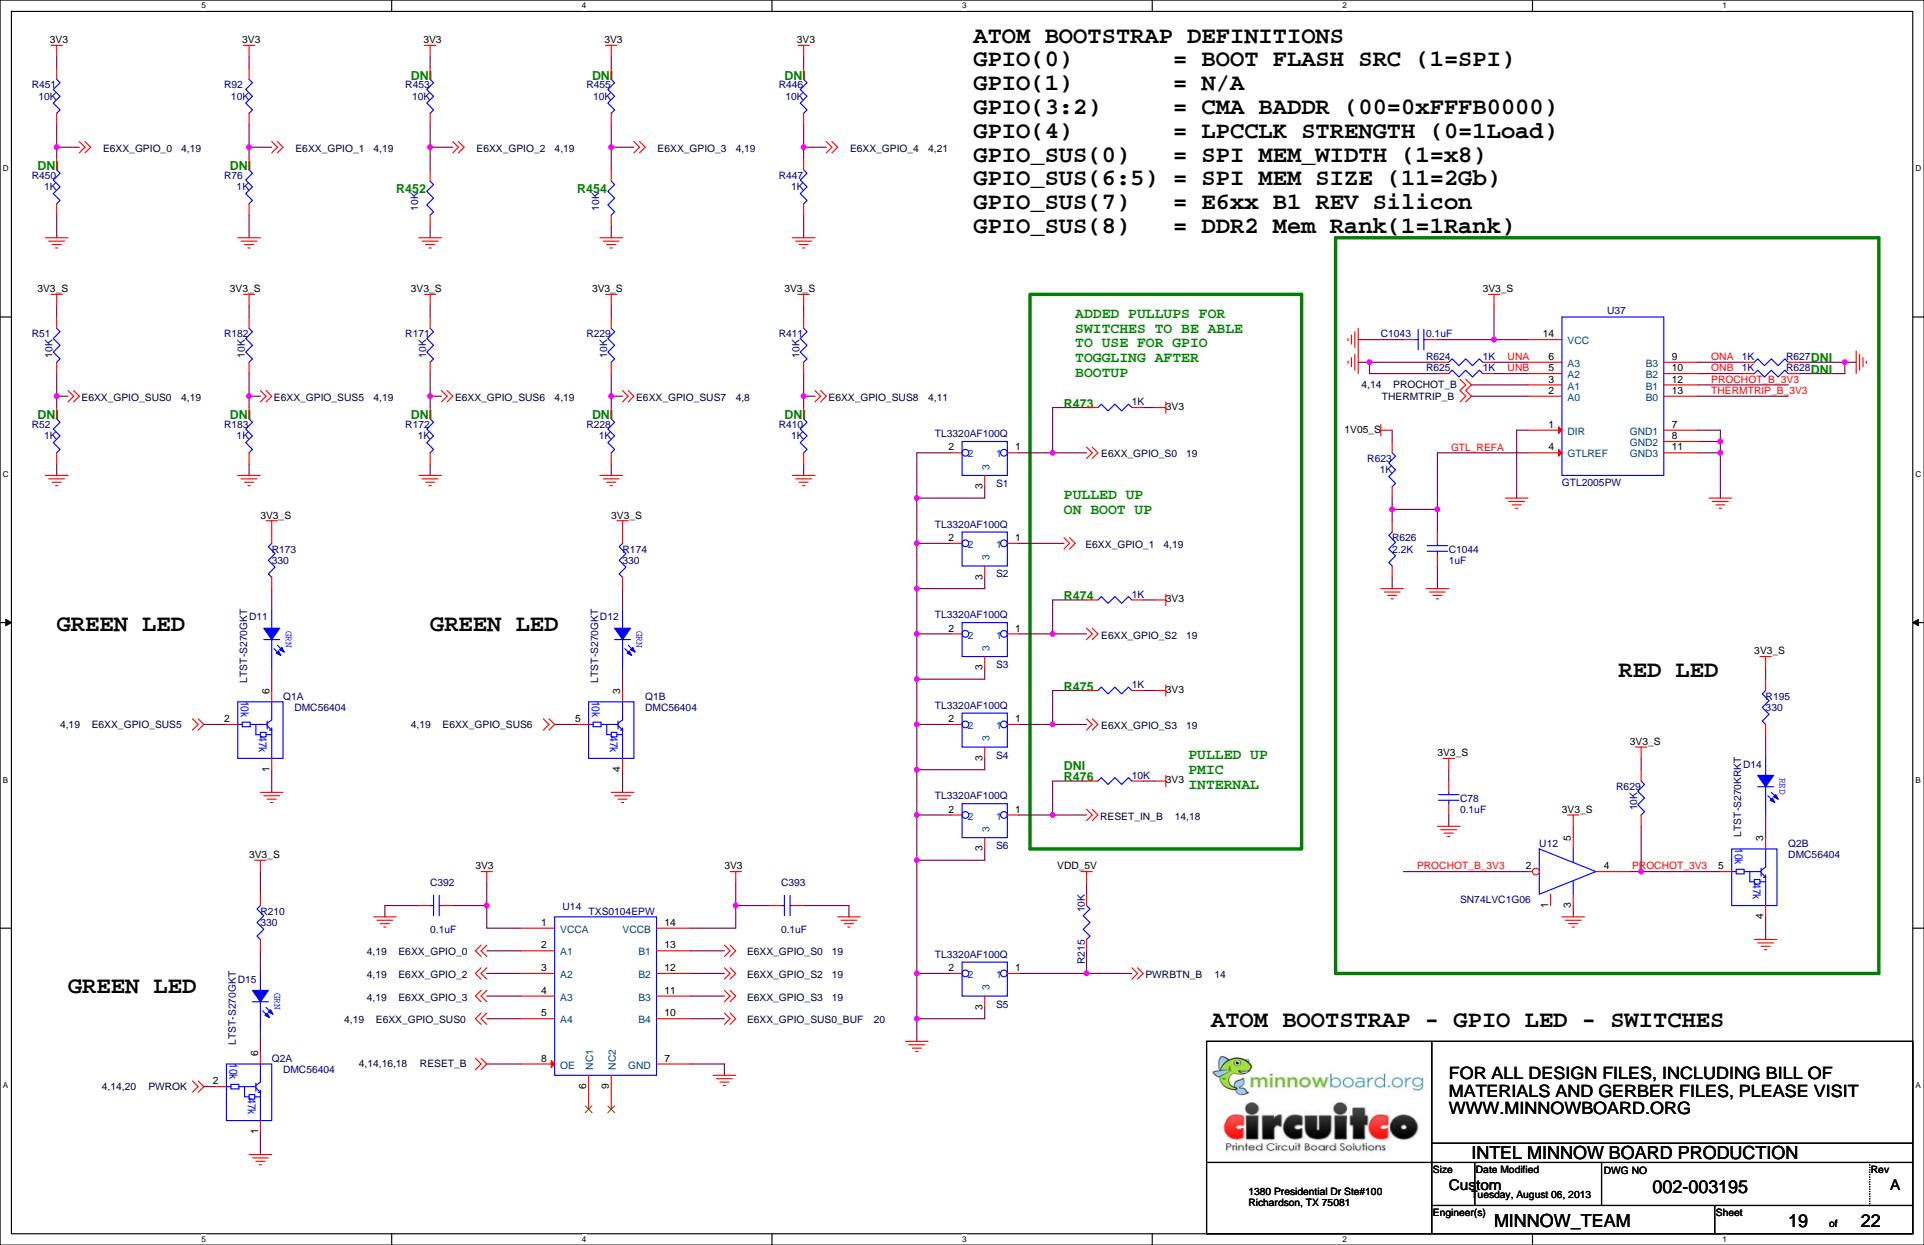
[picture p207: page 19]

ADDED PULLUPS FOR
SWITCHES TO BE ABLE
TO USE FOR GPIO
TOGGLING AFTER
BOOTUP

PWRBTN_B 14
ATOM BOOTSTRAP - GPIO LED - SWITCHES

FOR ALL DESIGN FILES, INCLUDING BILL OF
MATERIALS AND GERBER FILES, PLEASE VISIT
WWW.MINNOWBOARD.ORG

### DNI

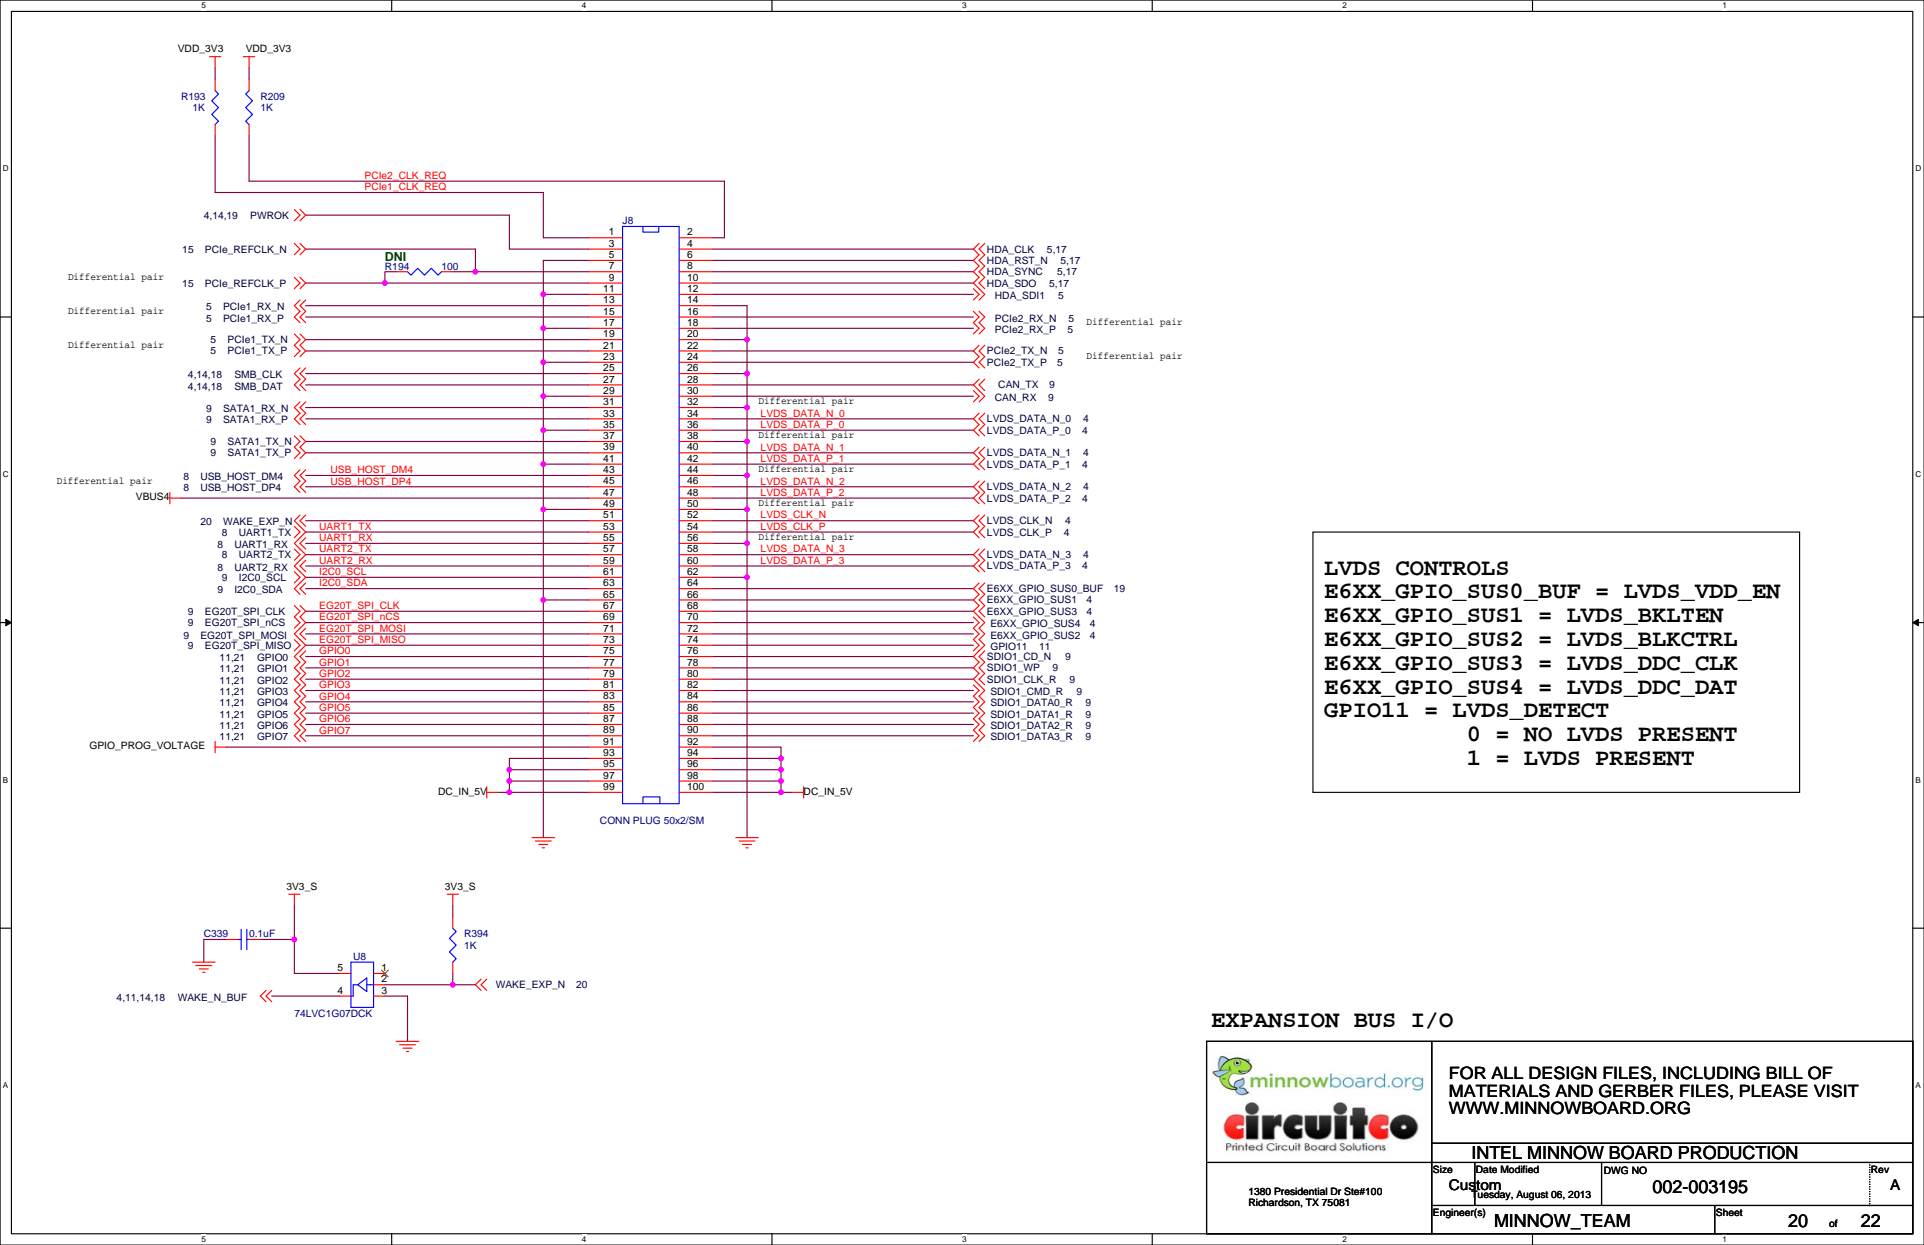
[picture p208: page 20]
Differential pair; EXPANSION BUS I/O; LVDS CONTROLS E6XX_GPIO_SUS0_BUF = LVDS_VDD_EN E6XX_GPIO_SUS1 = LVDS_BKLTEN E6XX_GPIO_SUS2 = LVDS_BLKCTRL E6XX_GPIO_SUS3 = LVDS_DDC_CLK E6XX_GPIO_SUS4 = LVDS_DDC_DAT GPIO11 = LVDS_DETECT; PCIe1_CLK_REQ; UART2_TX; I2C0_SDA; I2C0_SCL; EG20T_SPI_nCS; UART1_RX; UART1_TX; UART2_RX; GPIO0; EG20T_SPI_CLK; GPIO4; EG20T_SPI_MOSI EG20T_SPI_MISO; GPIO6; GPIO5; GPIO1 GPIO2 GPIO3; GPIO7; USB_HOST_DM4 USB_HOST_DP4; PCIe2_CLK_REQ; LVDS_CLK_N LVDS_CLK_P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

0 = NO LVDS PRESENT
1 = LVDS PRESENT

93
95 | 96
97 | 98
99 | 100

CONN PLUG 50x2/SM

FOR ALL DESIGN FILES, INCLUDING BILL OF
MATERIALS AND GERBER FILES, PLEASE VISIT
WWW.MINNOWBOARD.ORG

# GPIO-flash-programmer

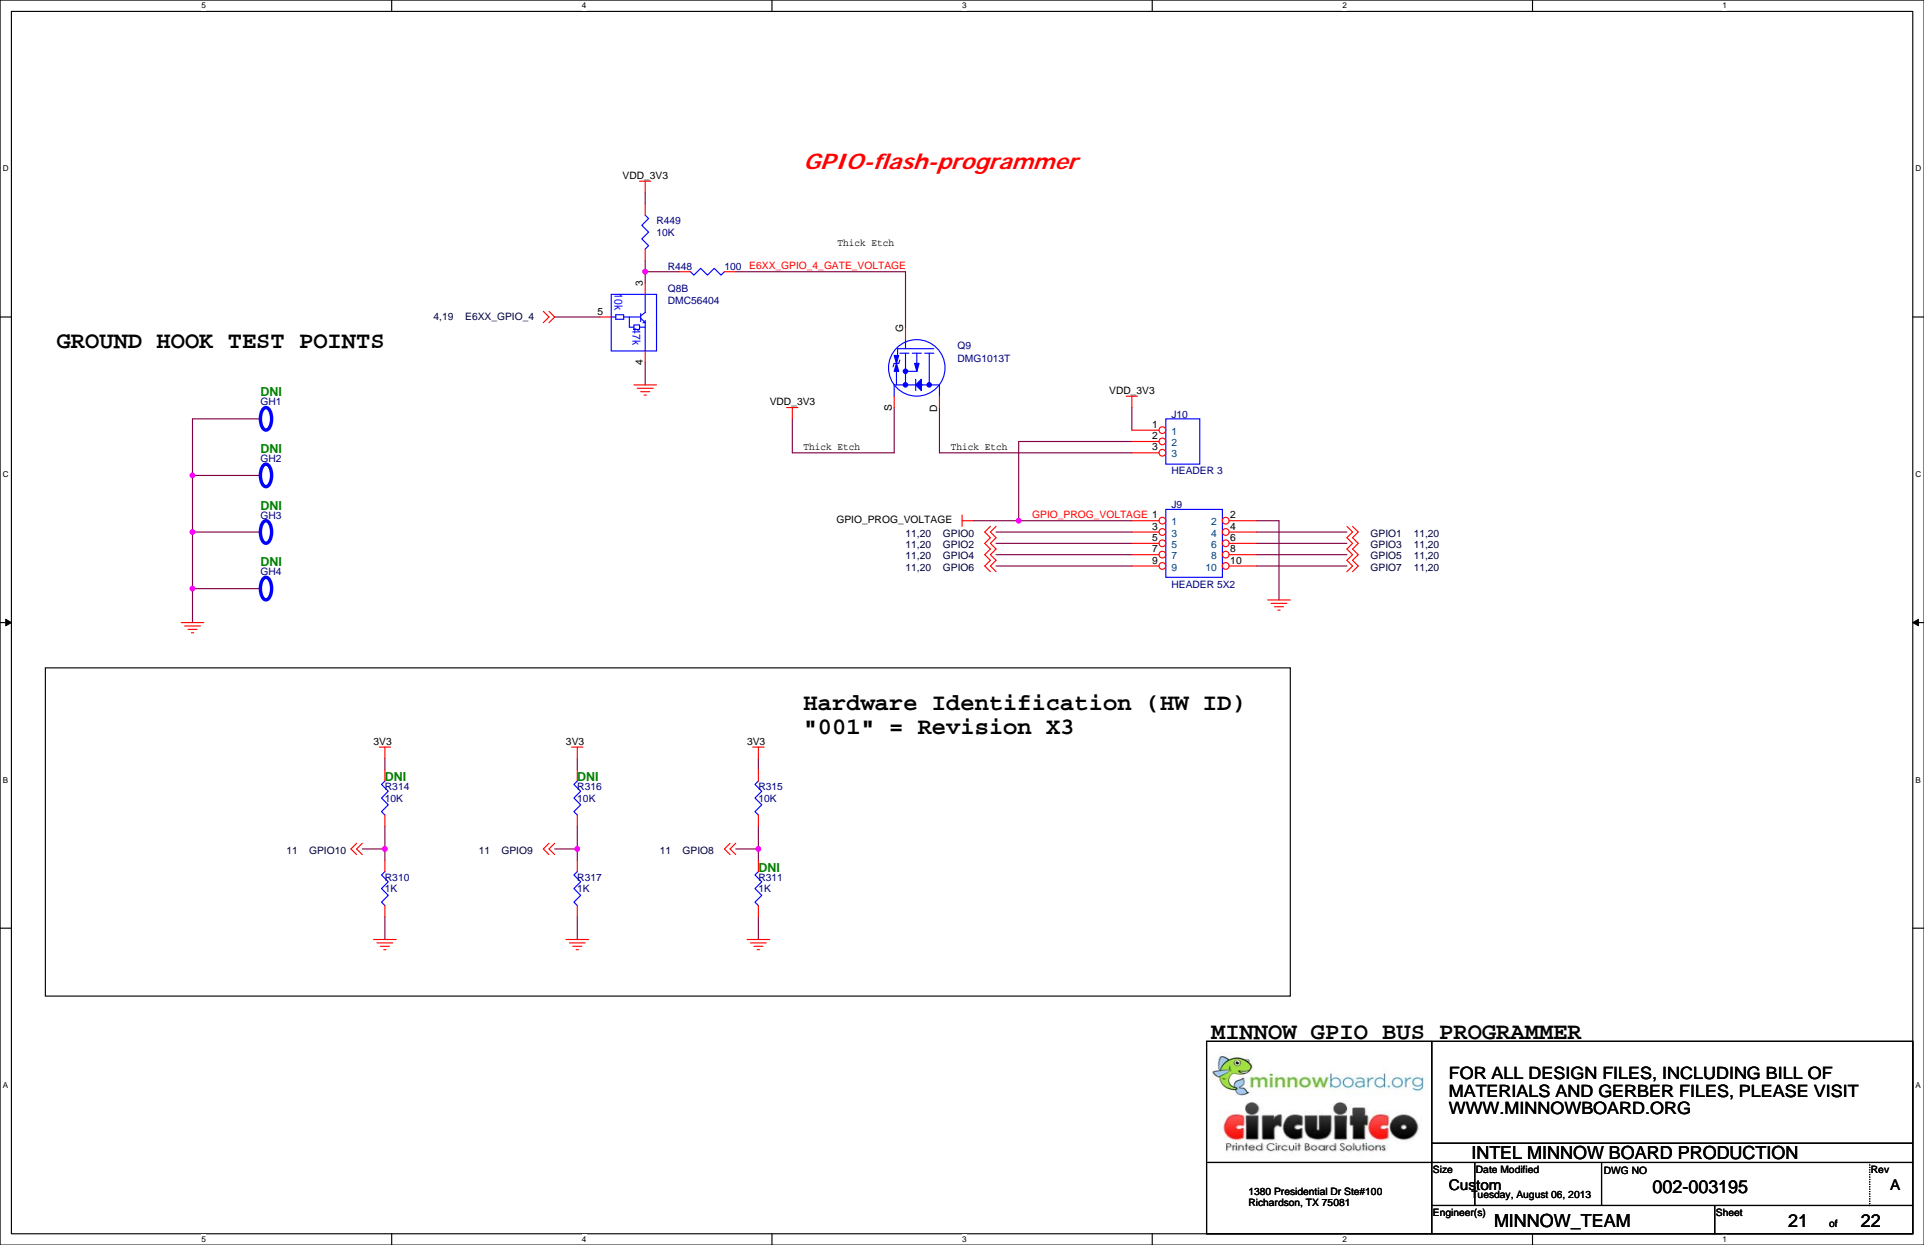
[picture p209: page 21]

GROUND HOOK TEST POINTS

Hardware Identification (HW ID)
"001" = Revision X3

MINNOW GPIO BUS PROGRAMMER

FOR ALL DESIGN FILES, INCLUDING BILL OF
MATERIALS AND GERBER FILES, PLEASE VISIT
WWW.MINNOWBOARD.ORG

BOTTOM SIDE | TOP SIDE

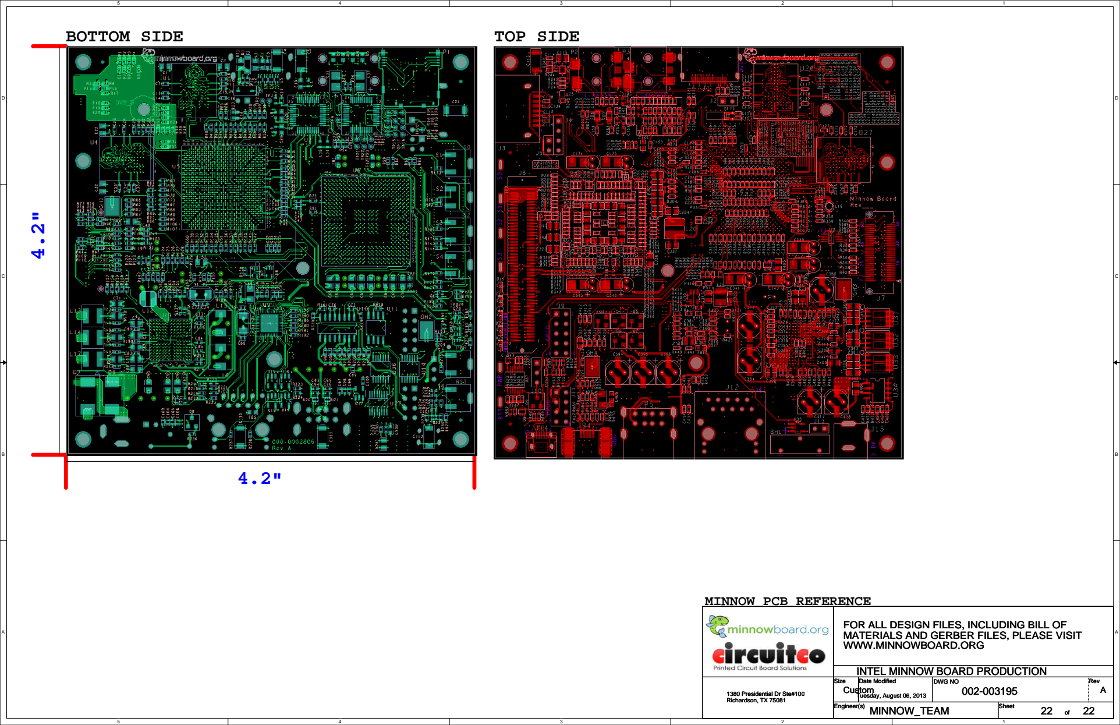
[picture p210: page 22]

MINNOW PCB REFERENCE

FOR ALL DESIGN FILES, INCLUDING BILL OF
MATERIALS AND GERBER FILES, PLEASE VISIT
WWW.MINNOWBOARD.ORG
