MinnowBoard-org/design-files/expansion-boards-lures/relay-lure/Big Relay Board/Schematic_big_relay_lure.pdf

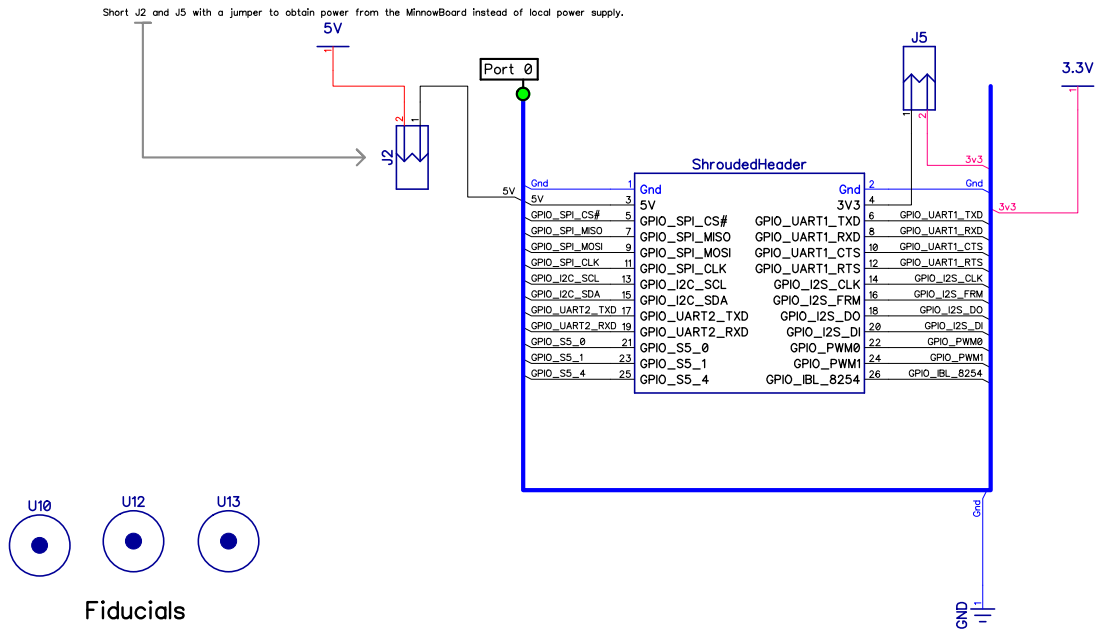
[picture p211: page 1]

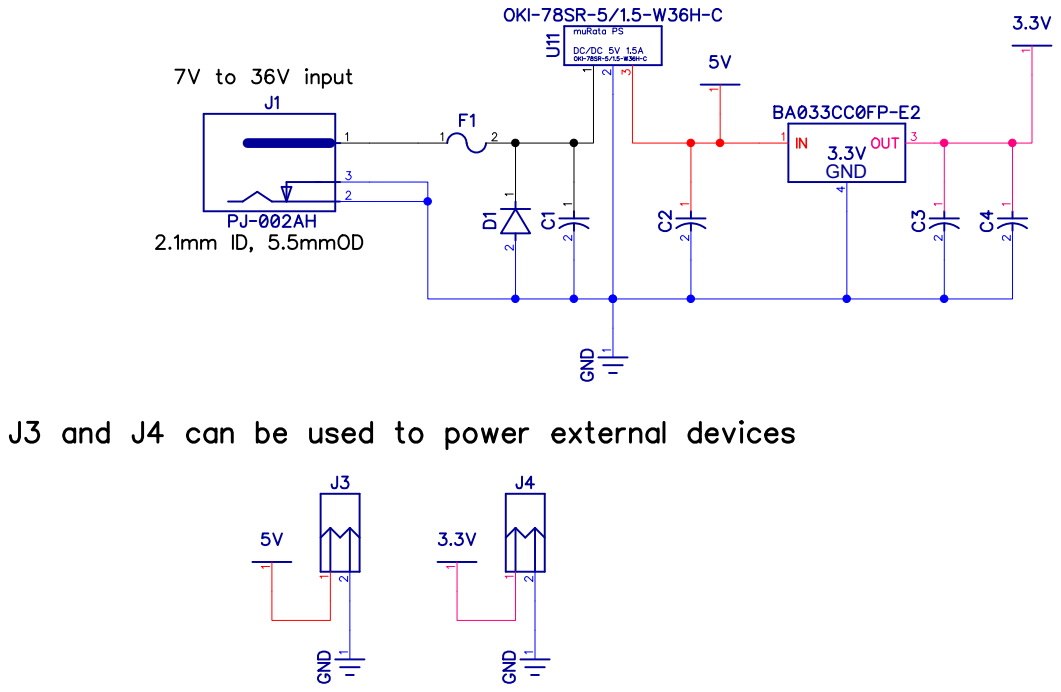
[picture p212: page 2]
GND

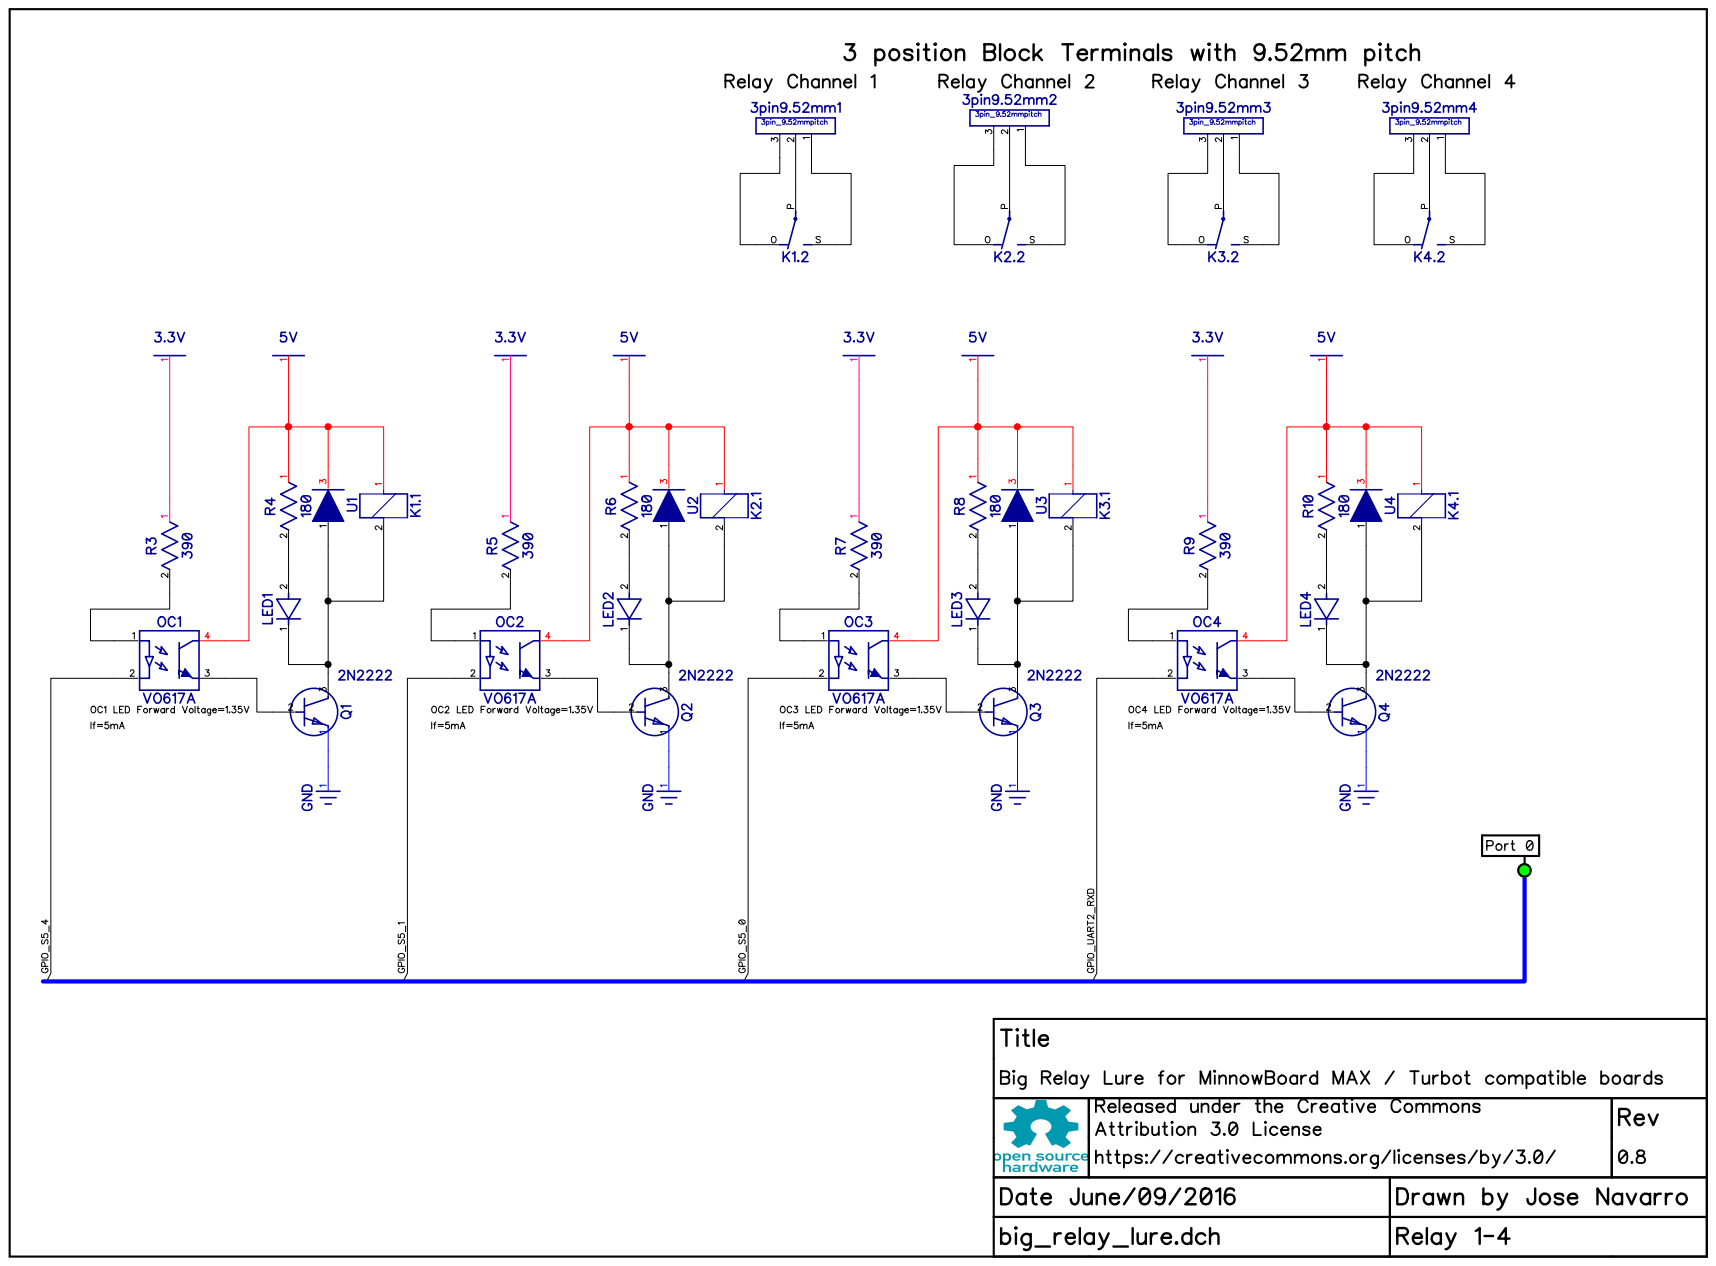
[picture p213: page 3]

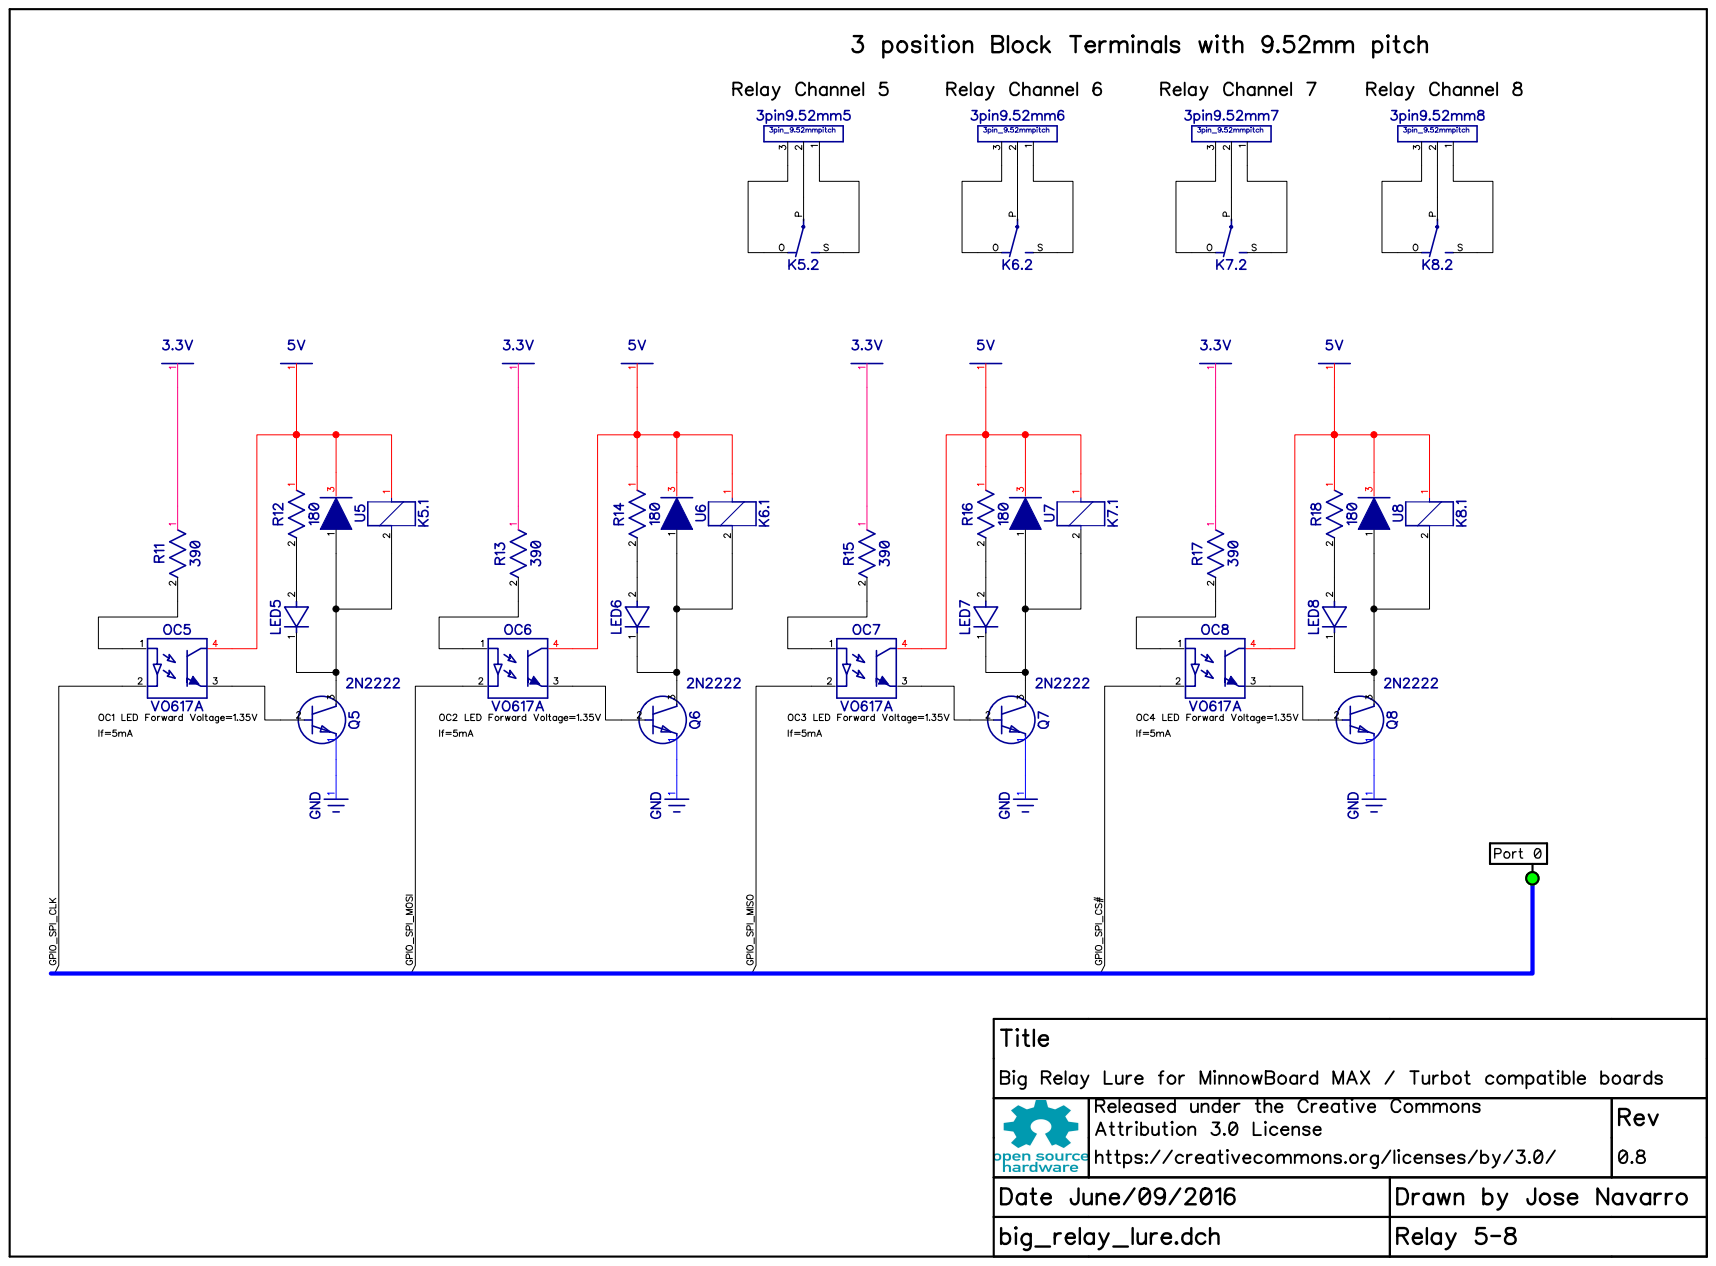
[picture p214: page 4]

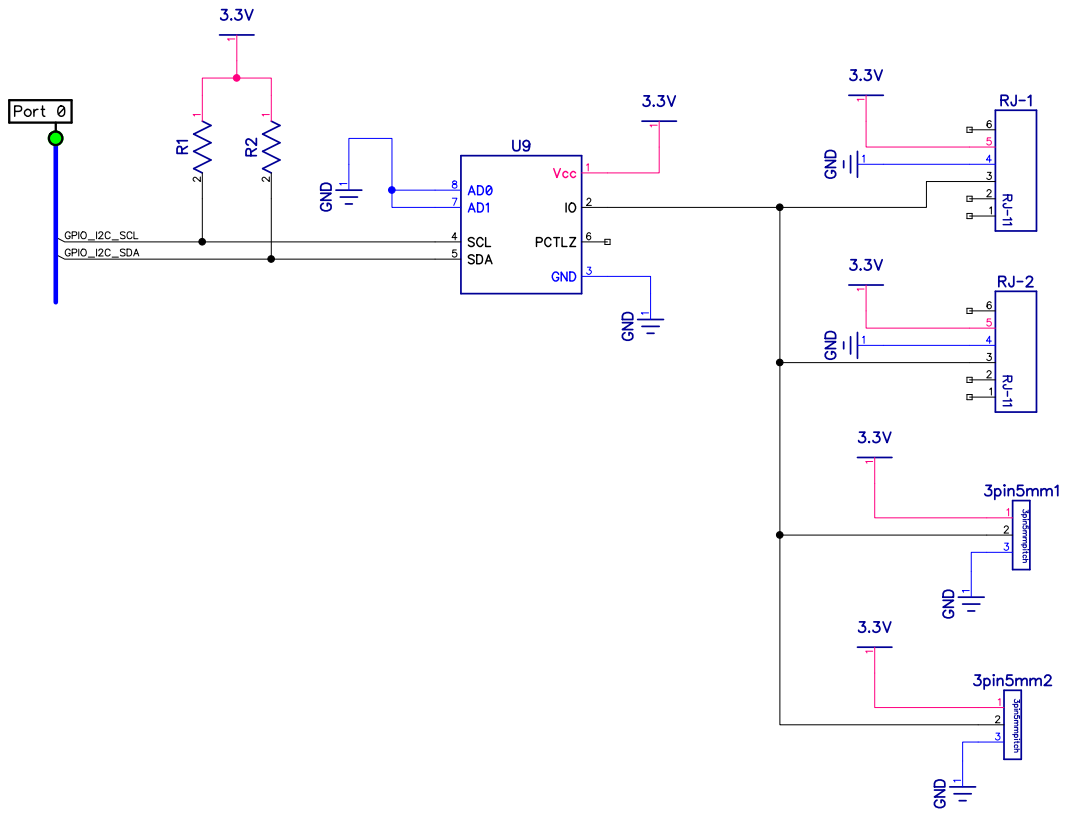
[picture p215: page 5]
