MinnowBoard-org/design-files/minnowboard-turbot-quad-core/F400_R302/MM-32900-0021-A1-20161019-updated.pdf

A

| 2 | 3 | 4 | 5 | 6 | 7

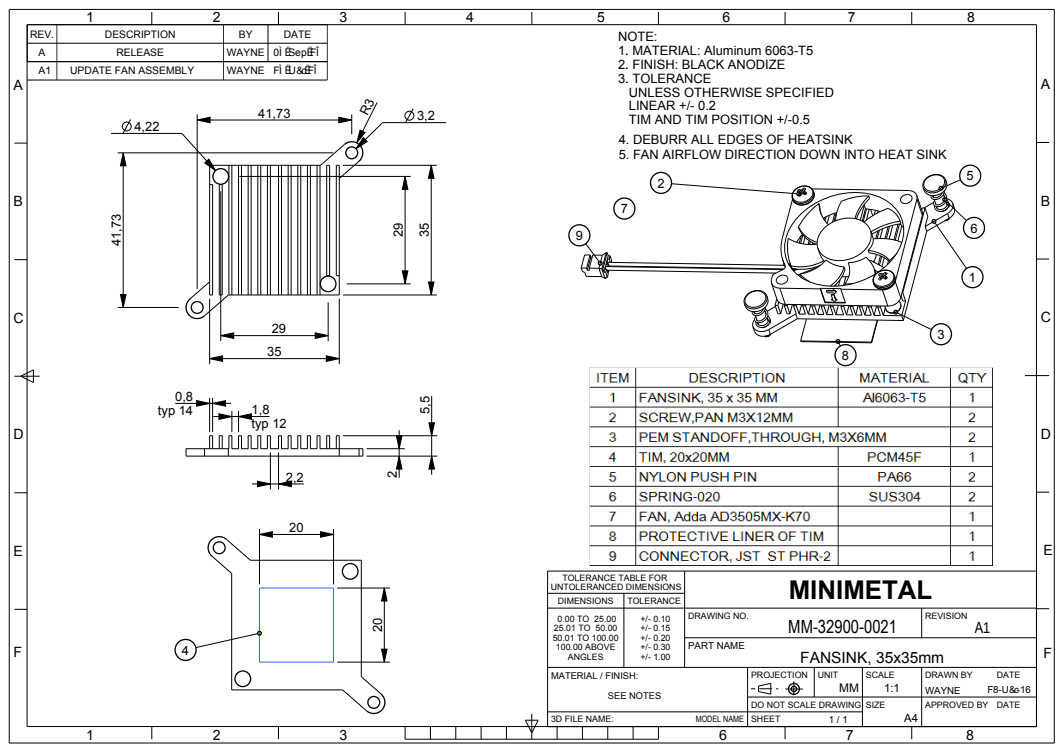
[picture p216: page 1]
DIMENSIONS; TOLERANCE; MINIMETAL; 0.00 TO 25.00 25.01 TO 50.00 50.01 TO 100.00 100.00 ABOVE ANGLES; DRAWING NO.; REVISION; PART NAME; FANSINK, 35x35mm; typ 14; typ 12

REV. | DESCRIPTION | BY | DATE
A | RELEASE | WAYNE | 0Sep
A1 | UPDATE FAN ASSEMBLY | WAYNE 2FW

NOTE:
1. MATERIAL: Aluminum 6063-T5
2. FINISH: BLACK ANODIZE
3. TOLERANCE
UNLESS OTHERWISE SPECIFIED
LINEAR +/- 0.2
TIM AND TIM POSITION +/-0.5
4. DEBURR ALL EDGES OF HEATSINK
5. FAN AIRFLOW DIRECTION DOWN INTO HEAT SINK

TOLERANCE TABLE FOR
UNTOLERANCED DIMENSIONS

MATERIAL / FINISH: SEE NOTES | PROJECTION | UNIT MM | SCALE 1:1 | DRAWN BY DATE WAYNE 8-2FW-16

DO NOT SCALE DRAWING | | SIZE A4 | APPROVED BY DATE
3D FILE NAME: MODEL NAME | SHEET 1 / 1

A

A

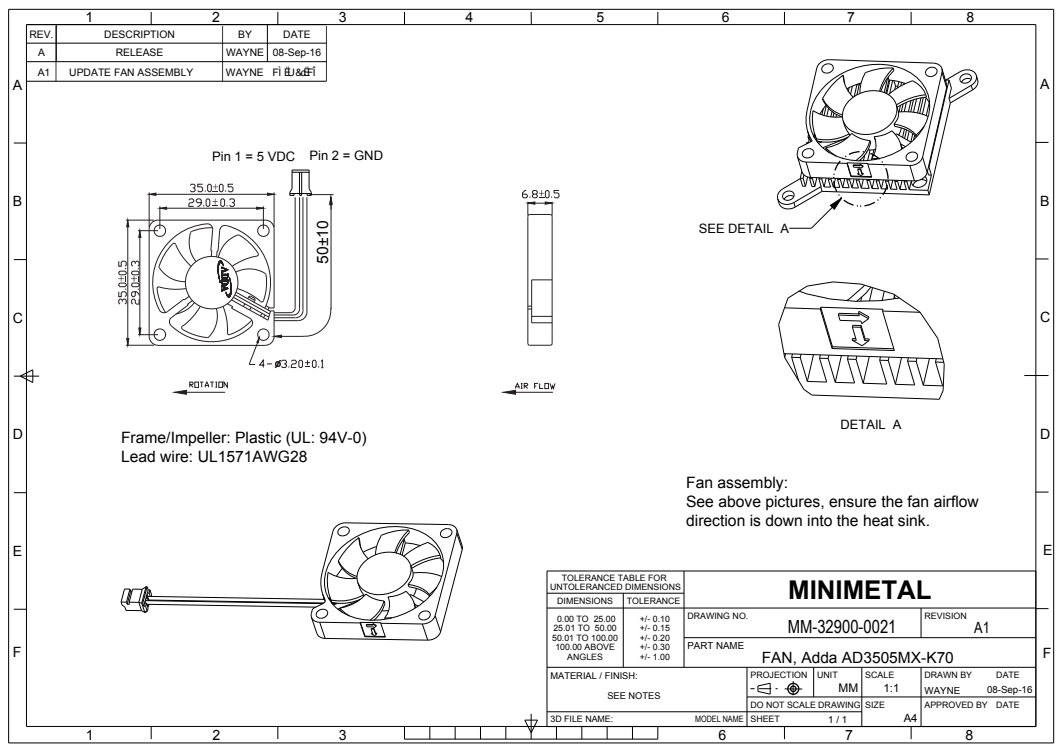
[picture p217: page 2]
DIMENSIONS; TOLERANCE; MINIMETAL; 0.00 TO 25.00 25.01 TO 50.00 50.01 TO 100.00 100.00 ABOVE ANGLES; DRAWING NO.; REVISION; PART NAME; FAN, Adda AD3505MX-K70; MATERIAL / FINISH:; SEE NOTES; PROJECTION; UNIT; SCALE; DRAWN BY; DATE; WAYNE; 08-Sep-16; RELEASE; 08-Sep-16 50±10; SEE DETAIL A; DETAIL A; UPDATE FAN ASSEMBLY; WAYNE 2FW

Pin 1 = 5 VDC Pin 2 = GND

Frame/Impeller: Plastic (UL: 94V-0)
Lead wire: UL1571AWG28

Fan assembly:
See above pictures, ensure the fan airflow
direction is down into the heat sink.

TOLERANCE TABLE FOR
UNTOLERANCED DIMENSIONS

A

A

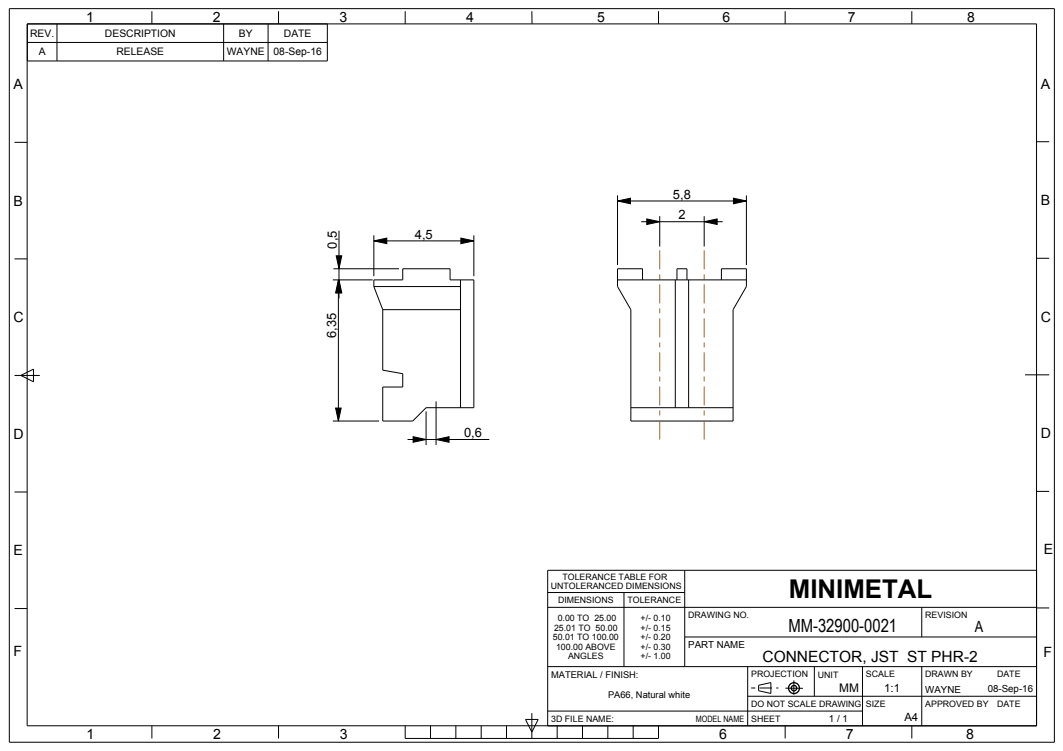
[picture p218: page 3]
DIMENSIONS; TOLERANCE; MINIMETAL; 0.00 TO 25.00 25.01 TO 50.00 50.01 TO 100.00 100.00 ABOVE ANGLES; DRAWING NO.; REVISION; PART NAME; MATERIAL / FINISH:; PA66, Natural white; PROJECTION; UNIT; SCALE; DRAWN BY; DATE; WAYNE; 08-Sep-16; RELEASE

TOLERANCE TABLE FOR
UNTOLERANCED DIMENSIONS

CONNECTOR, JST ST PHR-2

A

A

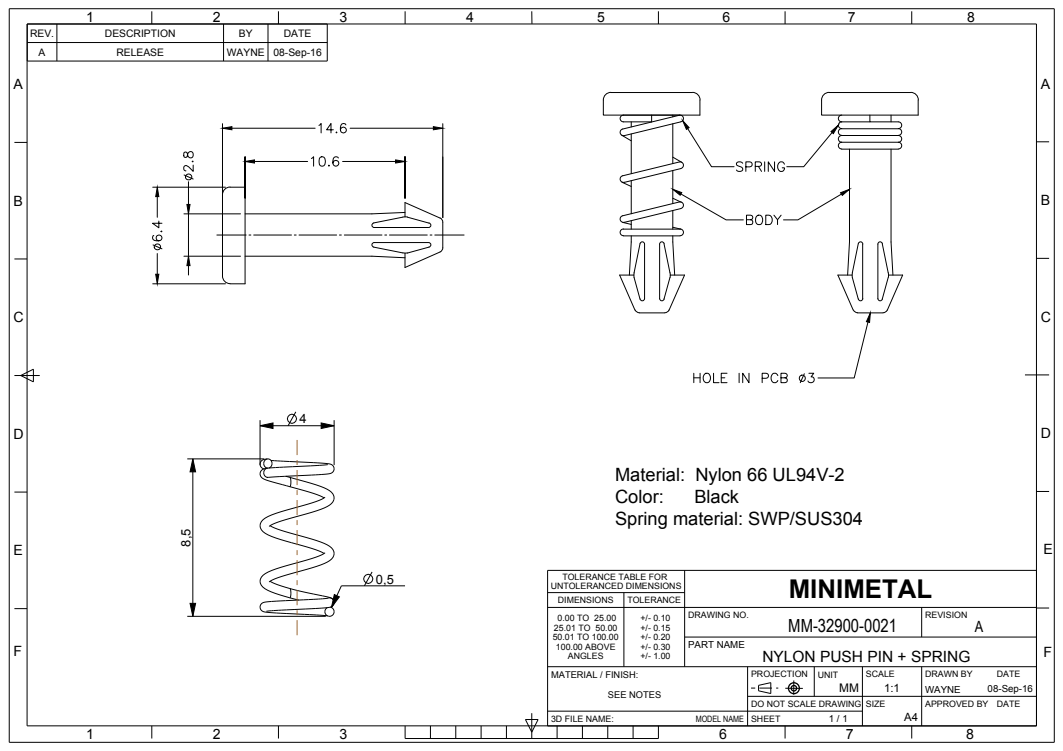
[picture p219: page 4]
DIMENSIONS; TOLERANCE; MINIMETAL; 0.00 TO 25.00 25.01 TO 50.00 50.01 TO 100.00 100.00 ABOVE ANGLES; DRAWING NO.; REVISION; PART NAME; MATERIAL / FINISH:; SEE NOTES; PROJECTION; UNIT; SCALE; DRAWN BY; DATE; WAYNE; 08-Sep-16; RELEASE; Color:; Black

Material: Nylon 66 UL94V-2
Spring material: SWP/SUS304

TOLERANCE TABLE FOR
UNTOLERANCED DIMENSIONS

NYLON PUSH PIN + SPRING
