MinnowBoard-org/design-files/minnowboard-v1/rev-a/Minnow_RevA_FAB.pdf

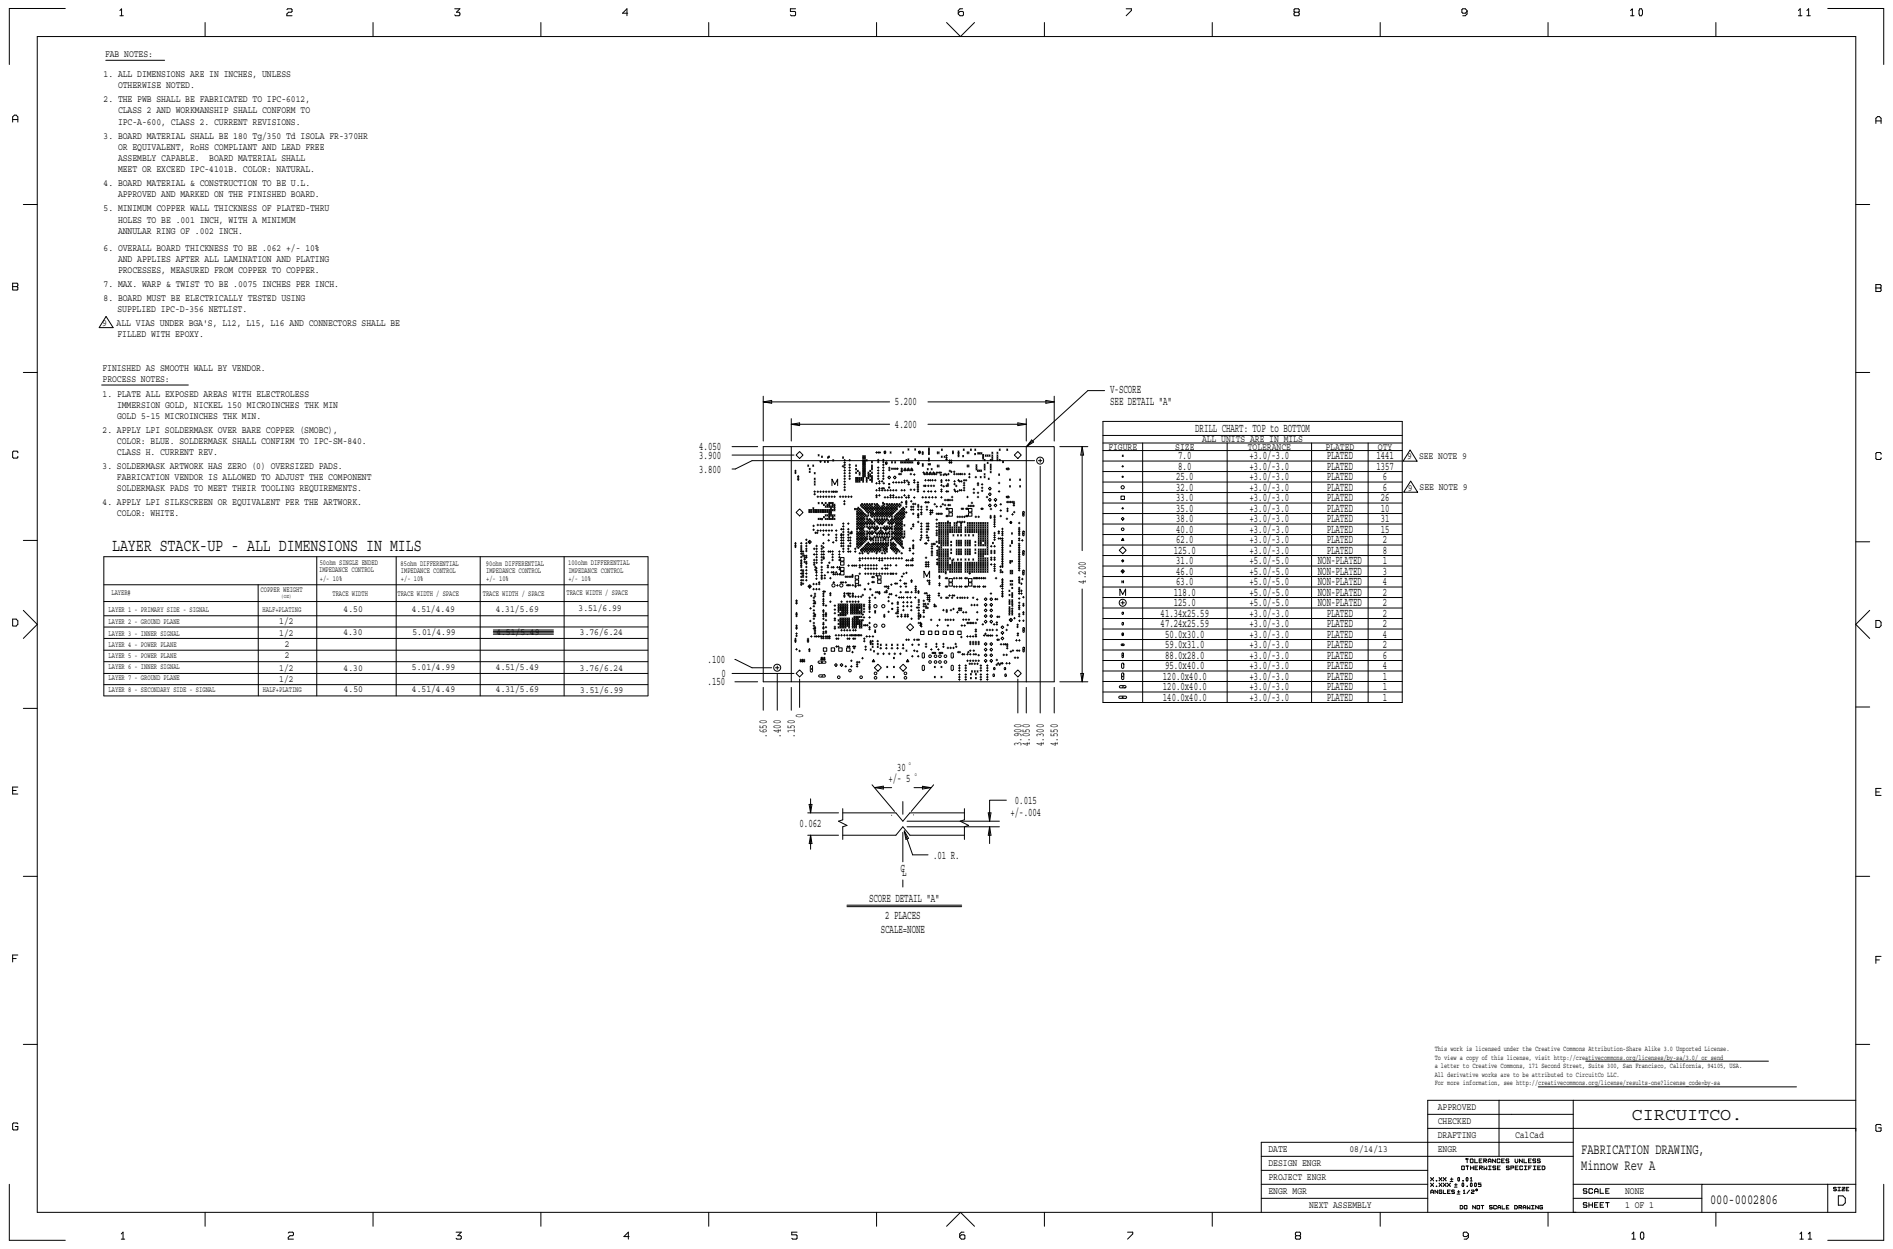
[picture p220: page 1]
Minnow Rev A; FABRICATION DRAWING,; NONE; CIRCUITCO.; SCORE DETAIL "A"; SCALE=NONE; 2 PLACES; ENGR MGR; PROJECT ENGR; NEXT ASSEMBLY; CHECKED; APPROVED; ALL VIAS UNDER BGA'S, L12, L15, L16 AND CONNECTORS SHALL BE; ASSEMBLY CAPABLE.; BOARD MATERIAL SHALL; FAB NOTES:; LAYER#; HALF+PLATING; COPPER WEIGHT; 50ohm SINGLE ENDED IMPEDANCE CONTROL; TRACE WIDTH; IMPEDANCE CONTROL; 85ohm DIFFERENTIAL; 90ohm DIFFERENTIAL; 100ohm DIFFERENTIAL IMPEDANCE CONTROL; SEE DETAIL "A"; V-SCORE; SEE NOTE 9

1. ALL DIMENSIONS ARE IN INCHES, UNLESS
OTHERWISE NOTED.

2. THE PWB SHALL BE FABRICATED TO IPC-6012,
CLASS 2 AND WORKMANSHIP SHALL CONFORM TO
IPC-A-600, CLASS 2. CURRENT REVISIONS.
3. BOARD MATERIAL SHALL BE 180 Tg/350 Td ISOLA FR-370HR
OR EQUIVALENT, RoHS COMPLIANT AND LEAD FREE
MEET OR EXCEED IPC-4101B. COLOR: NATURAL.

4. BOARD MATERIAL & CONSTRUCTION TO BE U.L.
APPROVED AND MARKED ON THE FINISHED BOARD.

5. MINIMUM COPPER WALL THICKNESS OF PLATED-THRU
HOLES TO BE .001 INCH, WITH A MINIMUM
ANNULAR RING OF .002 INCH.

6. OVERALL BOARD THICKNESS TO BE .062 +/- 10%
AND APPLIES AFTER ALL LAMINATION AND PLATING
PROCESSES, MEASURED FROM COPPER TO COPPER.

7. MAX. WARP & TWIST TO BE .0075 INCHES PER INCH.

8. BOARD MUST BE ELECTRICALLY TESTED USING
SUPPLIED IPC-D-356 NETLIST.

FILLED WITH EPOXY.

FINISHED AS SMOOTH WALL BY VENDOR.
PROCESS NOTES:

1. PLATE ALL EXPOSED AREAS WITH ELECTROLESS
IMMERSION GOLD, NICKEL 150 MICROINCHES THK MIN
GOLD 5-15 MICROINCHES THK MIN.
2. APPLY LPI SOLDERMASK OVER BARE COPPER (SMOBC),
COLOR: BLUE. SOLDERMASK SHALL CONFIRM TO IPC-SM-840.
CLASS H. CURRENT REV.
3. SOLDERMASK ARTWORK HAS ZERO (0) OVERSIZED PADS.
FABRICATION VENDOR IS ALLOWED TO ADJUST THE COMPONENT
SOLDERMASK PADS TO MEET THEIR TOOLING REQUIREMENTS.
4. APPLY LPI SILKSCREEN OR EQUIVALENT PER THE ARTWORK.
COLOR: WHITE.

DRILL CHART: TOP to BOTTOM
ALL UNITS ARE IN MILS

FIGURE | SIZE | TOLERANCE | PLATED | QTY

7.0 | +3.0/-3.0 | PLATED | 1441
8.0 | +3.0/-3.0 | PLATED | 1357
25.0 | +3.0/-3.0 | PLATED | 6
32.0 | +3.0/-3.0 | PLATED | 6
33.0 | +3.0/-3.0 | PLATED | 26
35.0 | +3.0/-3.0 | PLATED | 10
38.0 | +3.0/-3.0 | PLATED | 31
40.0 | +3.0/-3.0 | PLATED | 15
62.0 | +3.0/-3.0 | PLATED | 2
125.0 | +3.0/-3.0 | PLATED | 8
31.0 | +5.0/-5.0 | NON-PLATED | 1
46.0 | +5.0/-5.0 | NON-PLATED | 3
63.0 | +5.0/-5.0 | NON-PLATED | 4
118.0 | +5.0/-5.0 | NON-PLATED | 2
125.0 | +5.0/-5.0 | NON-PLATED | 2
41.34x25.59 | +3.0/-3.0 | PLATED | 2
47.24x25.59 | +3.0/-3.0 | PLATED | 2
50.0x30.0 | +3.0/-3.0 | PLATED | 4
59.0x31.0 | +3.0/-3.0 | PLATED | 2
88.0x28.0 | +3.0/-3.0 | PLATED | 6
95.0x40.0 | +3.0/-3.0 | PLATED | 4

LAYER STACK-UP - ALL DIMENSIONS IN MILS

TRACE WIDTH / SPACE

LAYER 1 - PRIMARY SIDE - SIGNAL

LAYER 2 - GROUND PLANE
LAYER 3 - INNER SIGNAL
LAYER 4 - POWER PLANE
LAYER 5 - POWER PLANE
LAYER 6 - INNER SIGNAL
LAYER 7 - GROUND PLANE
LAYER 8 - SECONDARY SIDE - SIGNAL

120.0x40.0 | +3.0/-3.0 | PLATED | 1
140.0x40.0 | +3.0/-3.0 | PLATED | 1

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

DRAFTING | CalCad

DATE 08/14/13 | ENGR

DESIGN ENGR
