MinnowBoard-org/design-files/minnowboard-max/a1/MinnowBoard_Max_RevA1_sch.pdf

26
1

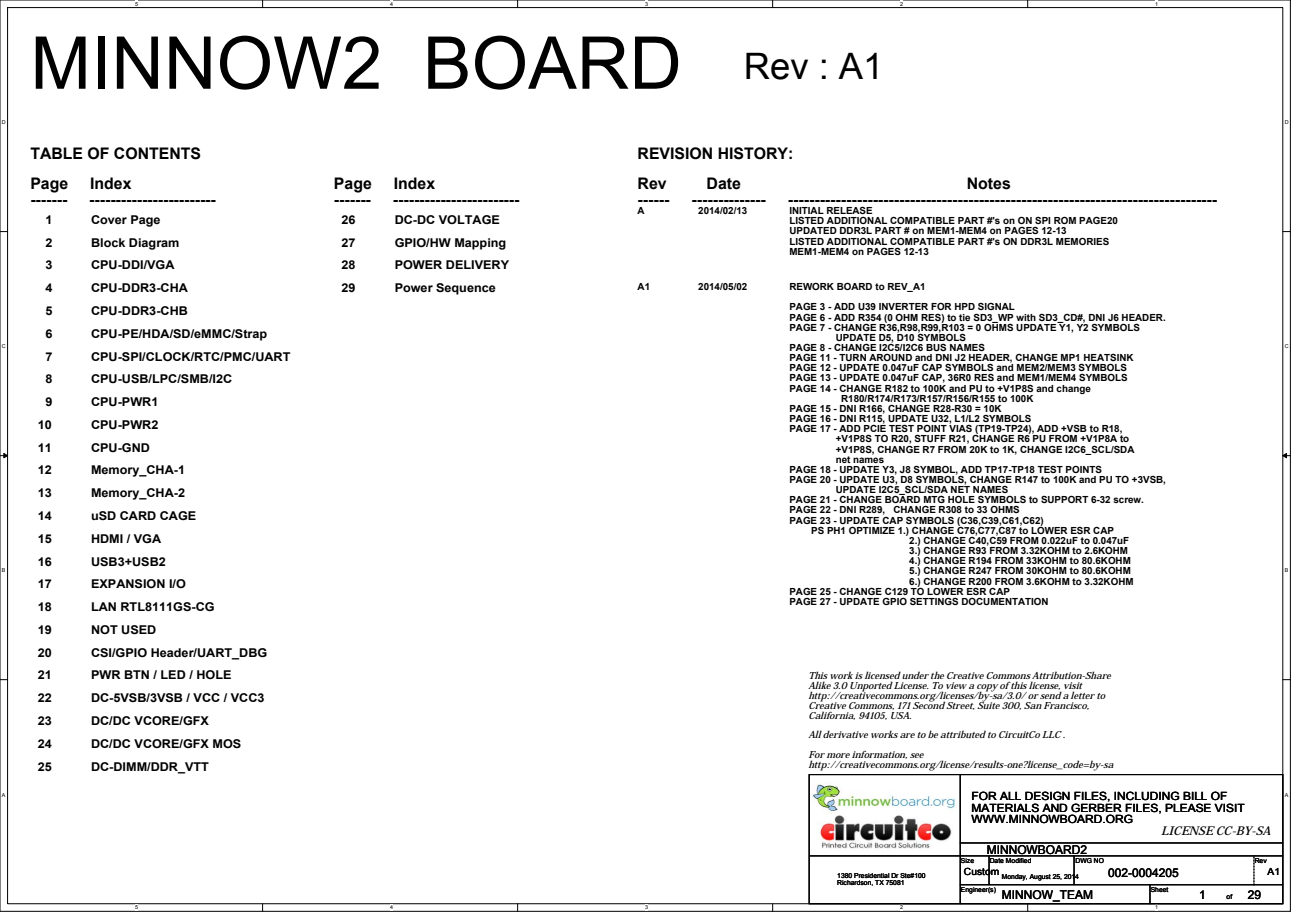
[picture p250: page 1]

INITIAL RELEASE
LISTED ADDITIONAL COMPATIBLE PART #'s on ON SPI ROM PAGE20
UPDATED DDR3L PART # on MEM1-MEM4 on PAGES 12-13
LISTED ADDITIONAL COMPATIBLE PART #'s ON DDR3L MEMORIES
MEM1-MEM4 on PAGES 12-13

Cover Page
Block Diagram
CPU-DDI/VGA
CPU-DDR3-CHA
CPU-DDR3-CHB
CPU-PE/HDA/SD/eMMC/Strap
CPU-SPI/CLOCK/RTC/PMC/UART
CPU-USB/LPC/SMB/I2C
CPU-PWR1
CPU-PWR2
CPU-GND
Memory_CHA-1
Memory_CHA-2
uSD CARD CAGE
HDMI / VGA
USB3+USB2
EXPANSION I/O
LAN RTL8111GS-CG
NOT USED
CSI/GPIO Header/UART_DBG
PWR BTN / LED / HOLE
DC-5VSB/3VSB / VCC / VCC3
DC/DC VCORE/GFX
DC/DC VCORE/GFX MOS
DC-DIMM/DDR_VTT

PAGE 3 - ADD U39 INVERTER FOR HPD SIGNAL
PAGE 6 - ADD R354 (0 OHM RES) to tie SD3_WP with SD3_CD#, DNI J6 HEADER.
PAGE 7 - CHANGE R36,R98,R99,R103 = 0 OHMS UPDATE Y1, Y2 SYMBOLS
PAGE 8 - CHANGE I2C5/I2C6 BUS NAMES
PAGE 11 - TURN AROUND and DNI J2 HEADER, CHANGE MP1 HEATSINK
PAGE 12 - UPDATE 0.047uF CAP SYMBOLS and MEM2/MEM3 SYMBOLS
PAGE 13 - UPDATE 0.047uF CAP, 36R0 RES and MEM1/MEM4 SYMBOLS
PAGE 14 - CHANGE R182 to 100K and PU to +V1P8S and change
PAGE 15 - DNI R166, CHANGE R28-R30 = 10K
PAGE 16 - DNI R115, UPDATE U32, L1/L2 SYMBOLS
PAGE 17 - ADD PCIE TEST POINT VIAS (TP19-TP24), ADD +VSB to R18,

+V1P8S TO R20, STUFF R21, CHANGE R6 PU FROM +V1P8A to
+V1P8S, CHANGE R7 FROM 20K to 1K, CHANGE I2C6_SCL/SDA
net names

PAGE 18 - UPDATE Y3, J8 SYMBOL, ADD TP17-TP18 TEST POINTS
PAGE 20 - UPDATE U3, D8 SYMBOLS, CHANGE R147 to 100K and PU TO +3VSB,
PAGE 21 - CHANGE BOARD MTG HOLE SYMBOLS to SUPPORT 6-32 screw.
PAGE 22 - DNI R289, CHANGE R308 to 33 OHMS
PAGE 23 - UPDATE CAP SYMBOLS (C36,C39,C61,C62)
PS PH1 OPTIMIZE 1.) CHANGE C76,C77,C87 to LOWER ESR CAP

UPDATE I2C5_SCL/SDA NET NAMES

PAGE 25 - CHANGE C129 TO LOWER ESR CAP
PAGE 27 - UPDATE GPIO SETTINGS DOCUMENTATION

This work is licensed under the Creative Commons Attribution-Share
Alike 3.0 Unported License. To view a copy of this license, visit
http://creativecommons.org/licenses/by-sa/3.0/ or send a letter to
Creative Commons, 171 Second Street, Suite 300, San Francisco,
California, 94105, USA.
All derivative works are to be attributed to CircuitCo LLC .
For more information, see
http://creativecommons.org/license/results-one?license_code=by-sa

FOR ALL DESIGN FILES, INCLUDING BILL OF
MATERIALS AND GERBER FILES, PLEASE VISIT
WWW.MINNOWBOARD.ORG

LICENSE CC-BY-SA

1380 Presidential Dr Ste#100 Richardson, TX 75081 | Size Custom | Date Modified | DWG NO 002-0004205 | Rev A1 Monday, August 25, 2014

Engineer(s) MINNOW_TEAM | Sheet of

# Bay Trail-I

# DDR3L memory down x16

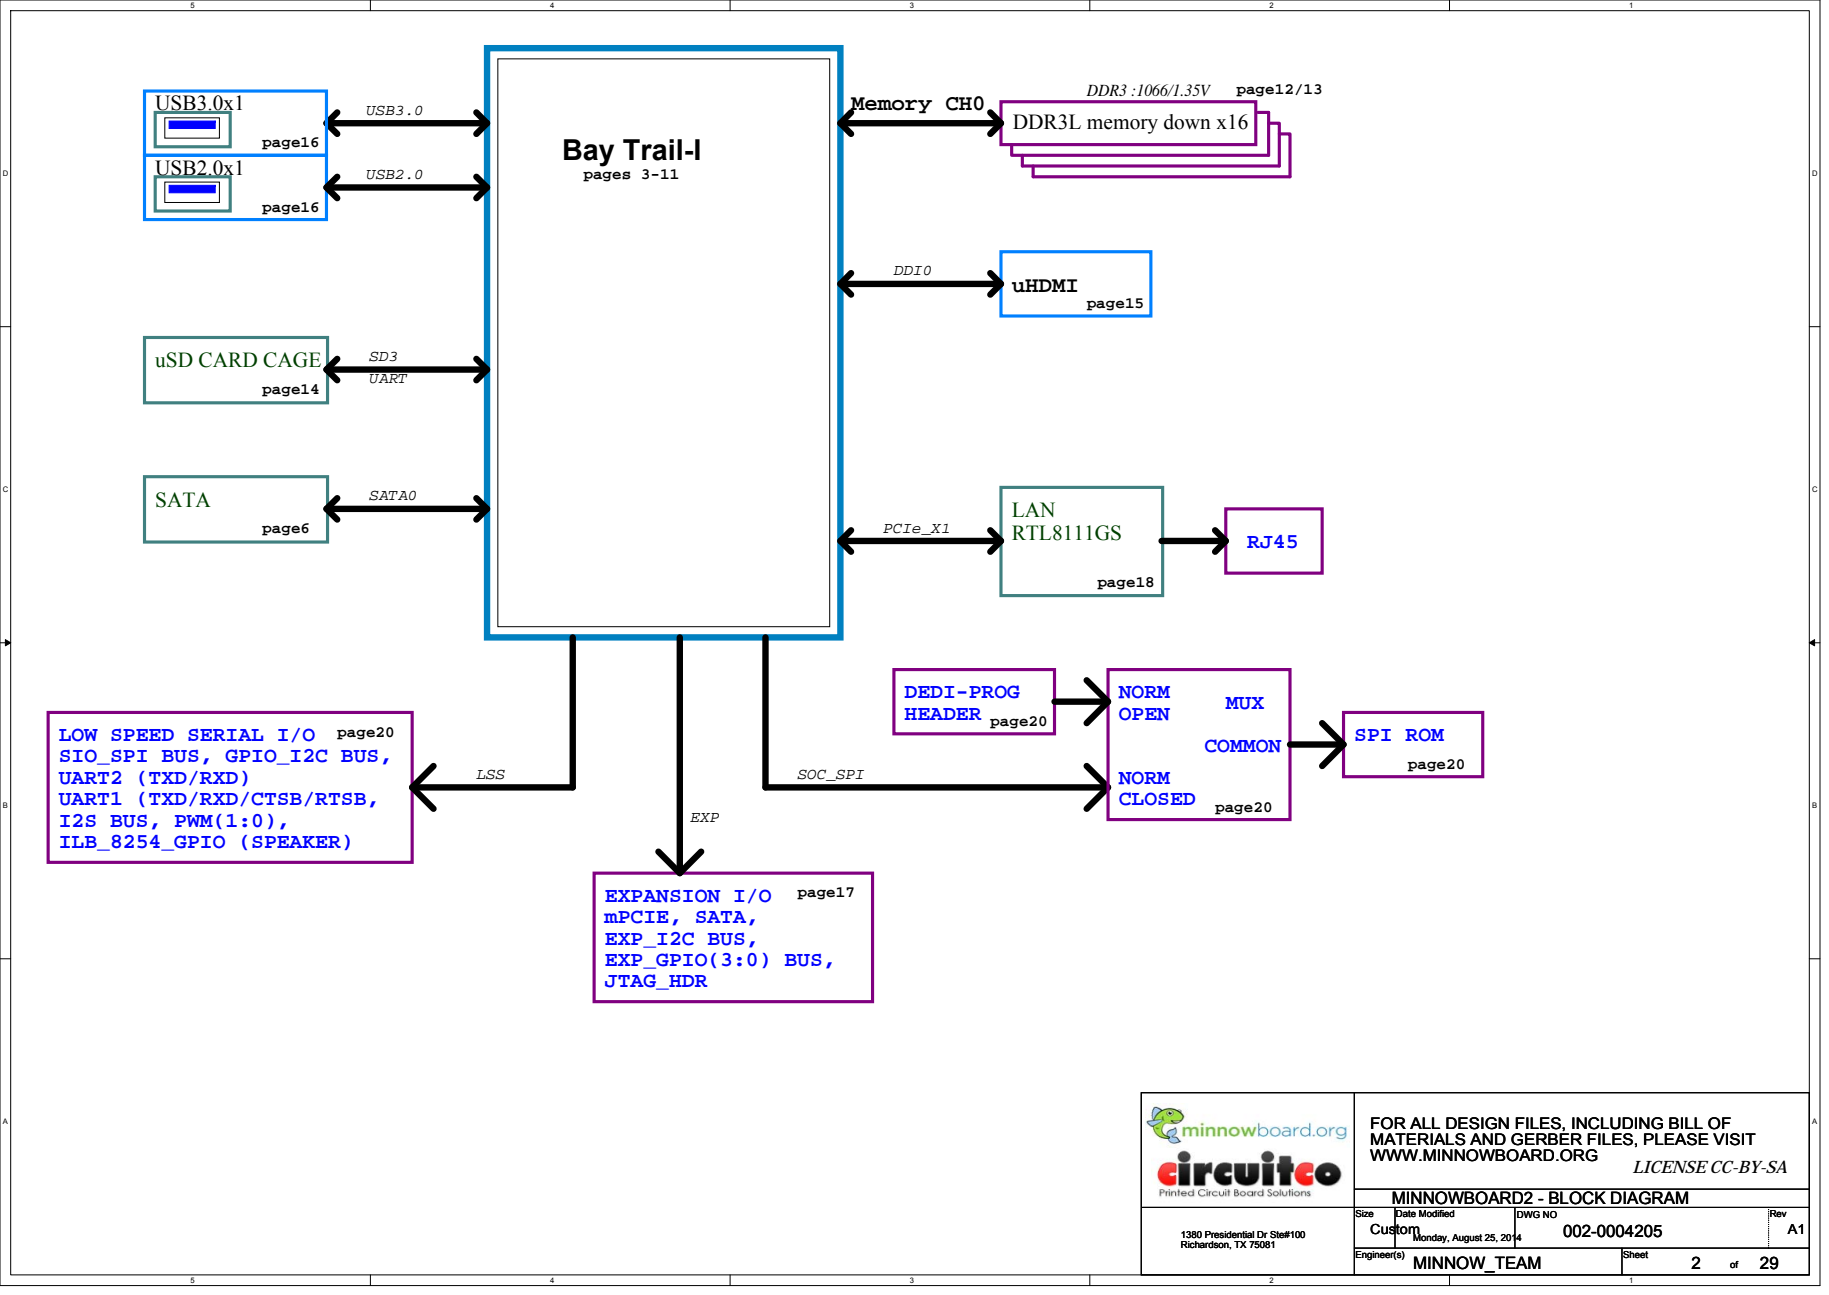
[picture p251: page 2]
DDR3 :1066/1.35V; LAN RTL8111GS PCIe_X1; SPI ROM; SOC_SPI; uHDMI; DDI0; USB3.0x1; USB3.0; USB2.0x1; USB2.0; Memory CH0; SD3 UART; page16; page14; page12/13; page15; page18; page20; page6; SATA; SATA0; EXPANSION I/O mPCIE, SATA, EXP_I2C BUS, EXP_GPIO(3:0) BUS, JTAG_HDR; page17; LSS; EXP; DEDI-PROG; HEADER; MUX NORM OPEN; NORM CLOSED; COMMON; pages 3-11; MINNOWBOARD2 - BLOCK DIAGRAM

uSD CARD CAGE

LOW SPEED SERIAL I/O
SIO_SPI BUS, GPIO_I2C BUS,
UART2 (TXD/RXD)
UART1 (TXD/RXD/CTSB/RTSB,
I2S BUS, PWM(1:0),
ILB_8254_GPIO (SPEAKER)

FOR ALL DESIGN FILES, INCLUDING BILL OF
MATERIALS AND GERBER FILES, PLEASE VISIT
WWW.MINNOWBOARD.ORG

LICENSE CC-BY-SA

## HDMI

# Bay Trail-M Remove eDP Port

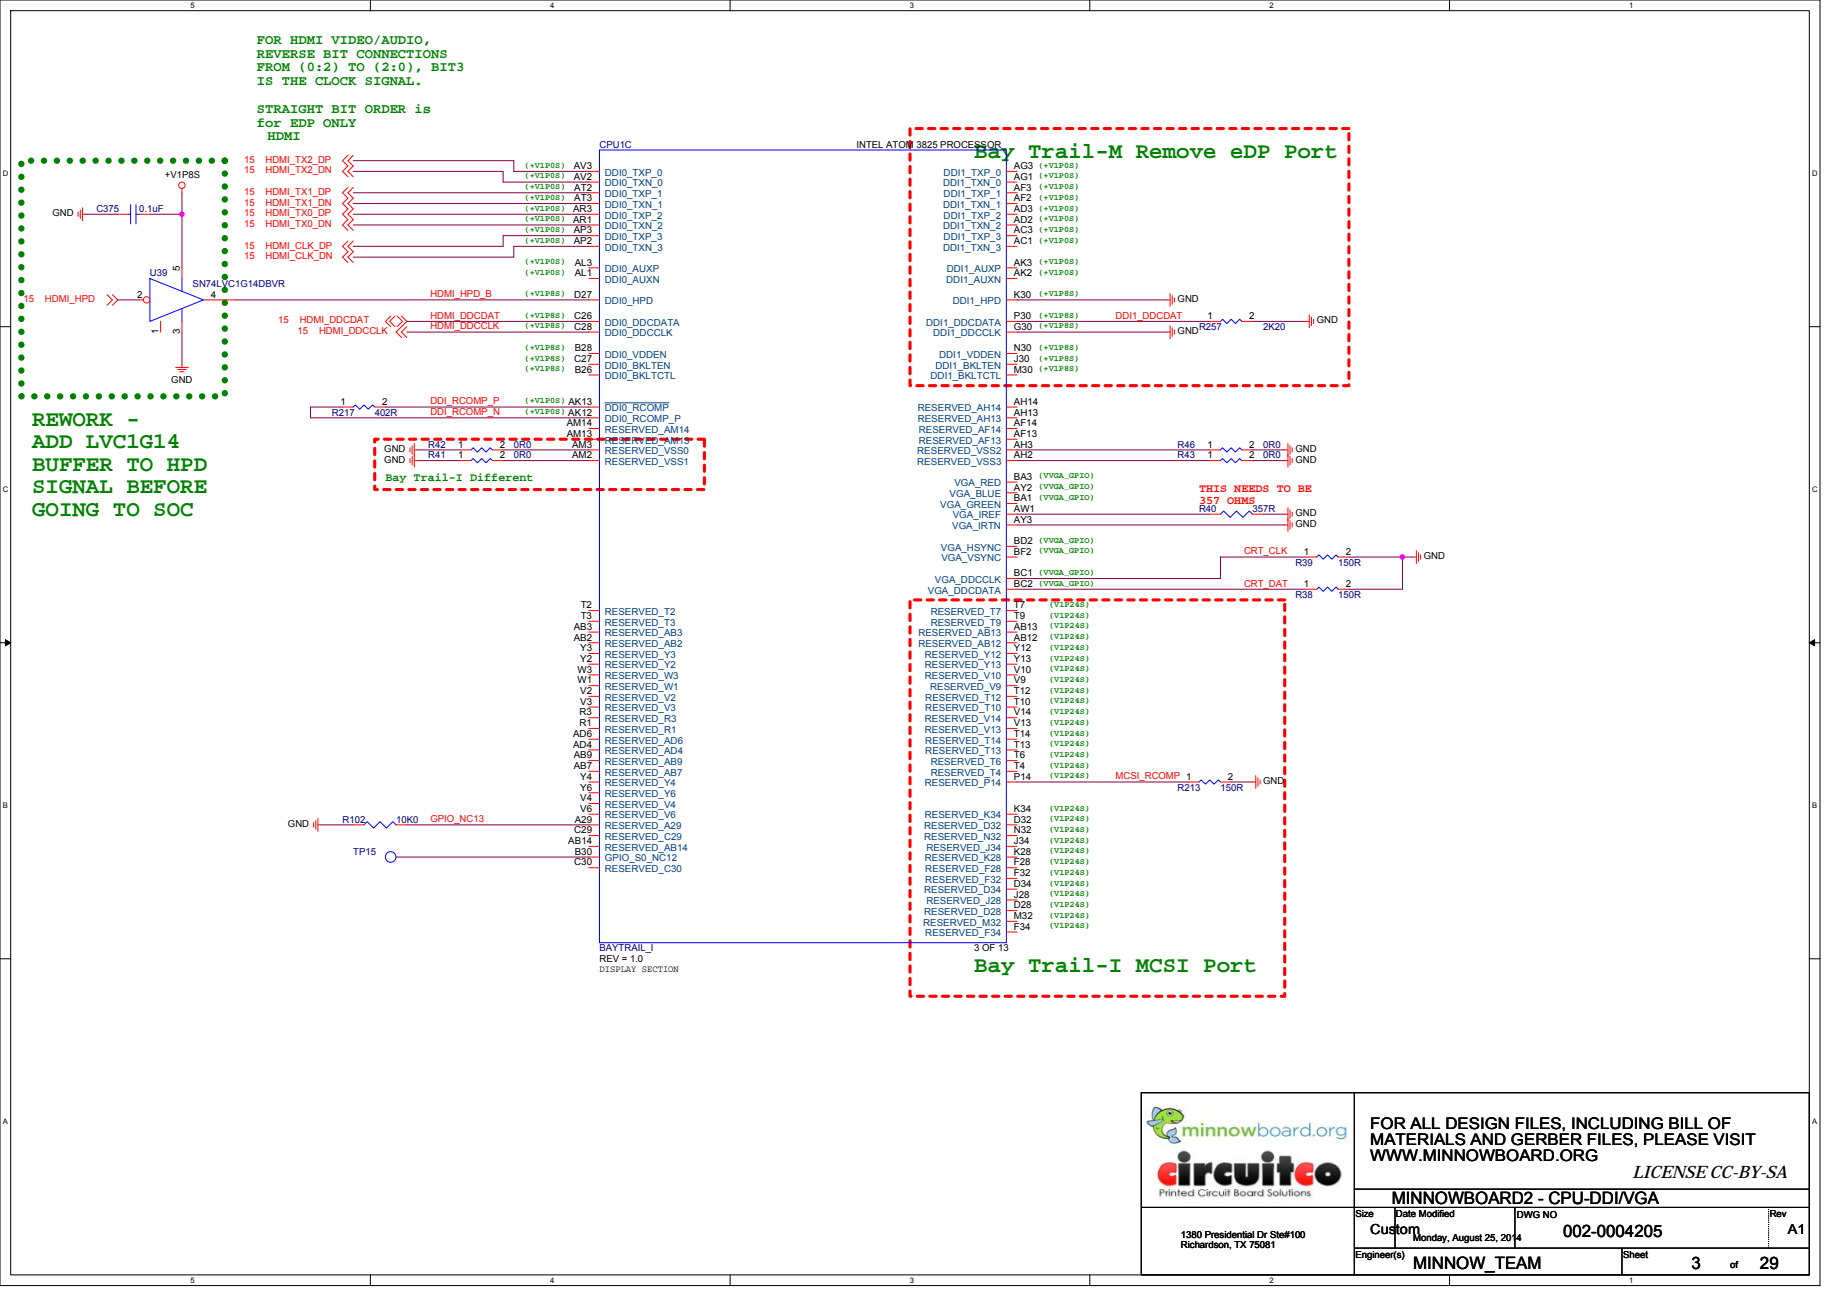
[picture p252: page 3]

FOR HDMI VIDEO/AUDIO,
REVERSE BIT CONNECTIONS
FROM (0:2) TO (2:0), BIT3
IS THE CLOCK SIGNAL.
STRAIGHT BIT ORDER is
for EDP ONLY

THIS NEEDS TO BE
357 OHMS

FOR ALL DESIGN FILES, INCLUDING BILL OF
MATERIALS AND GERBER FILES, PLEASE VISIT
WWW.MINNOWBOARD.ORG

LICENSE CC-BY-SA

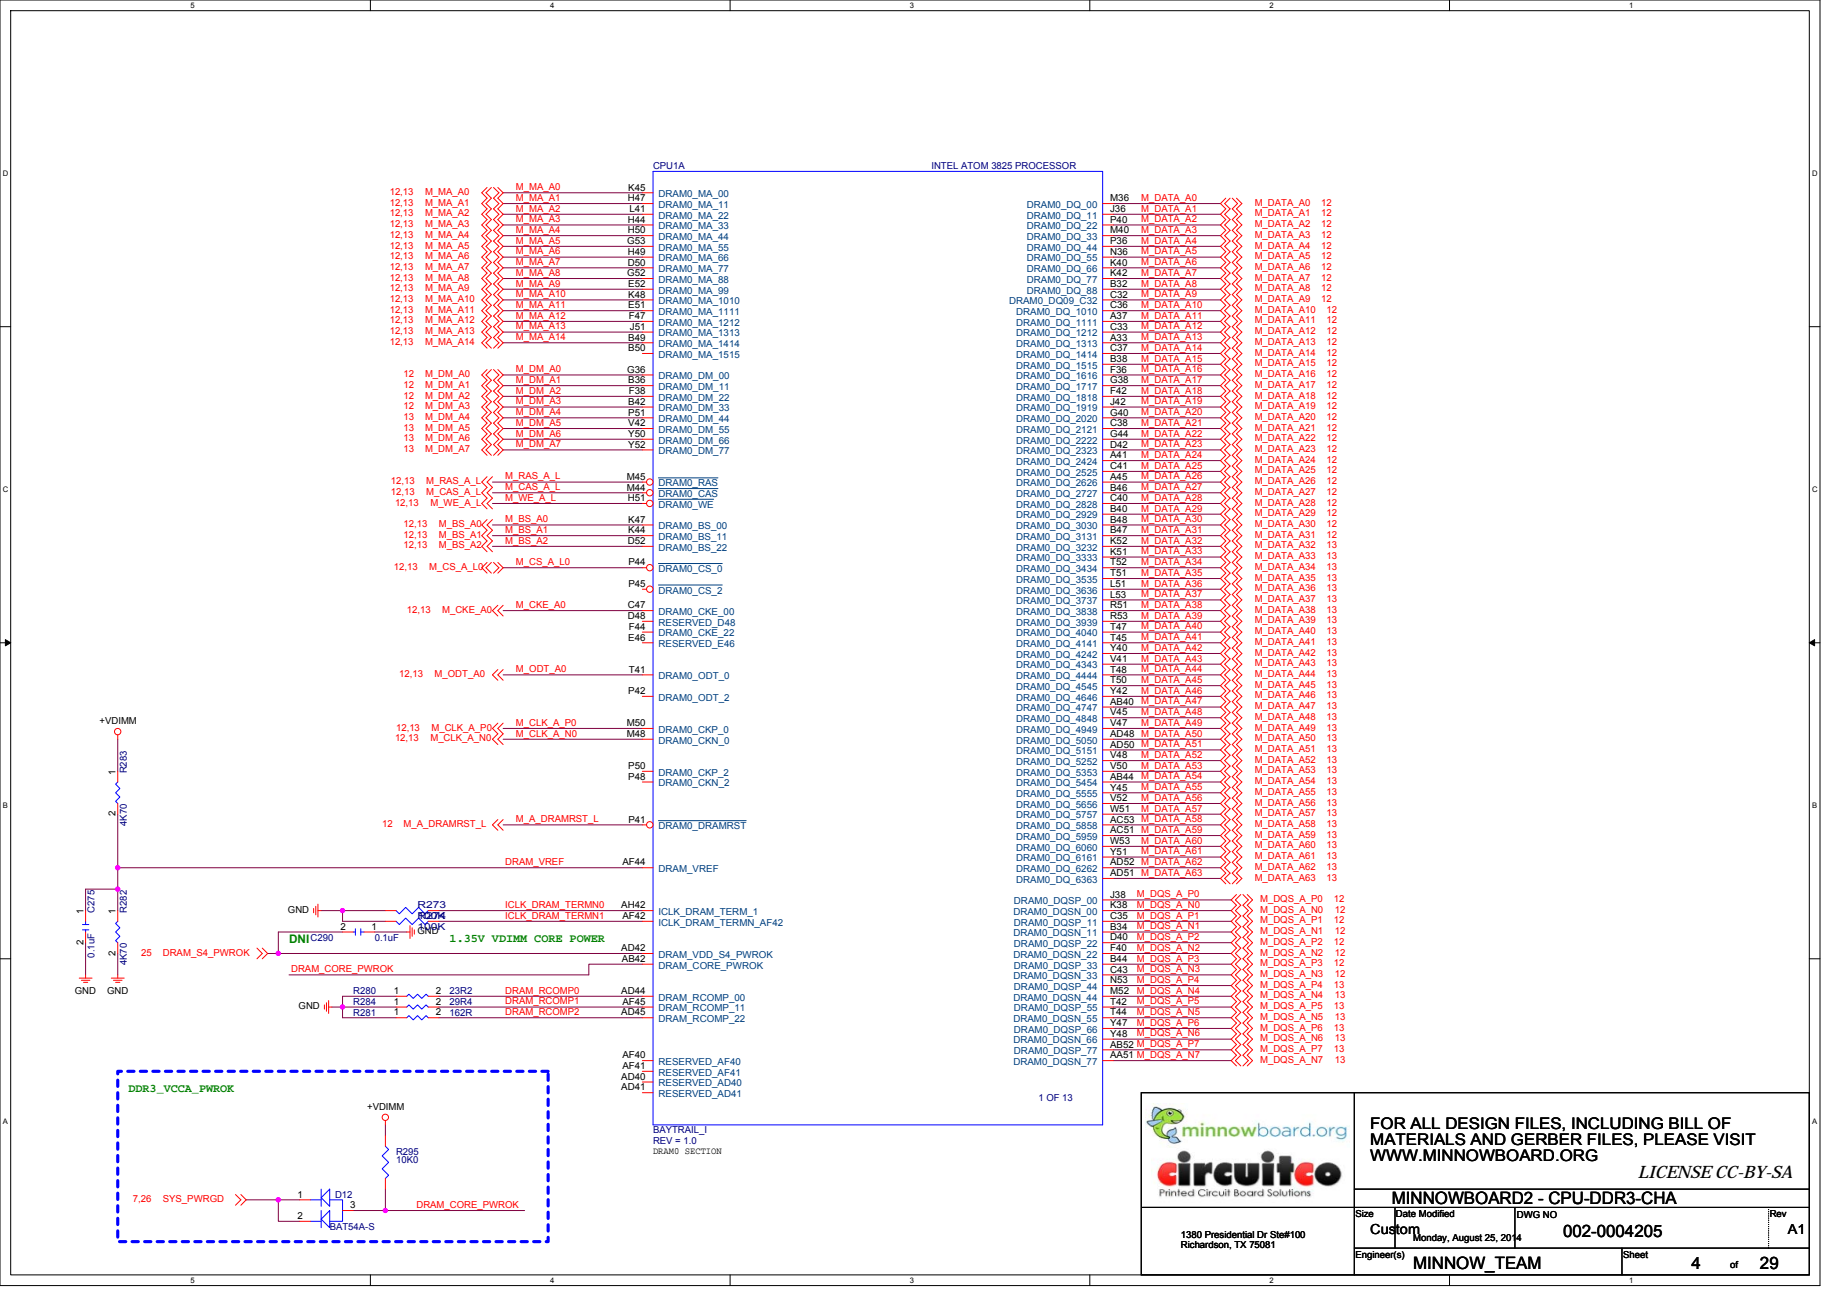
[picture p253: page 4]

FOR ALL DESIGN FILES, INCLUDING BILL OF
MATERIALS AND GERBER FILES, PLEASE VISIT
WWW.MINNOWBOARD.ORG

LICENSE CC-BY-SA

DRAM1 SECTION; MINNOWBOARD2 - CPU-DDR3-CHB; REV = 1.0; CPU1B; BAYTRAIL_I; DRAM1_ODT_0 AP41; DRAM1_CKN_0 AV48; DRAM1_CKP_0 AV50; DRAM1_DRAMRST AT41; DRAM1_CKN_2 AT48; DRAM1_CKP_2 AT50; DRAM1_DQSN_77; AJ51 DRAM1_DQSP_77; AH52 DRAM1_DQSN_66; AK48 DRAM1_DQSP_66; AK47 DRAM1_DQSN_55; AP44 DRAM1_DQSP_55; AP42 DRAM1_DQSN_44; AV52 DRAM1_DQSP_44; AU53 DRAM1_DQSN_33; BG43 DRAM1_DQSP_33; BH44 DRAM1_DQSN_22; AY38 DRAM1_DQSP_22; BA38 DRAM1_DQSN_11; BH34 DRAM1_DQSP_11; BG35 DRAM1_DQSN_00; BD40 DRAM1_DQSP_00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

INTEL ATOM 3825 PROCESSOR

FOR ALL DESIGN FILES, INCLUDING BILL OF
MATERIALS AND GERBER FILES, PLEASE VISIT
WWW.MINNOWBOARD.ORG

LICENSE CC-BY-SA

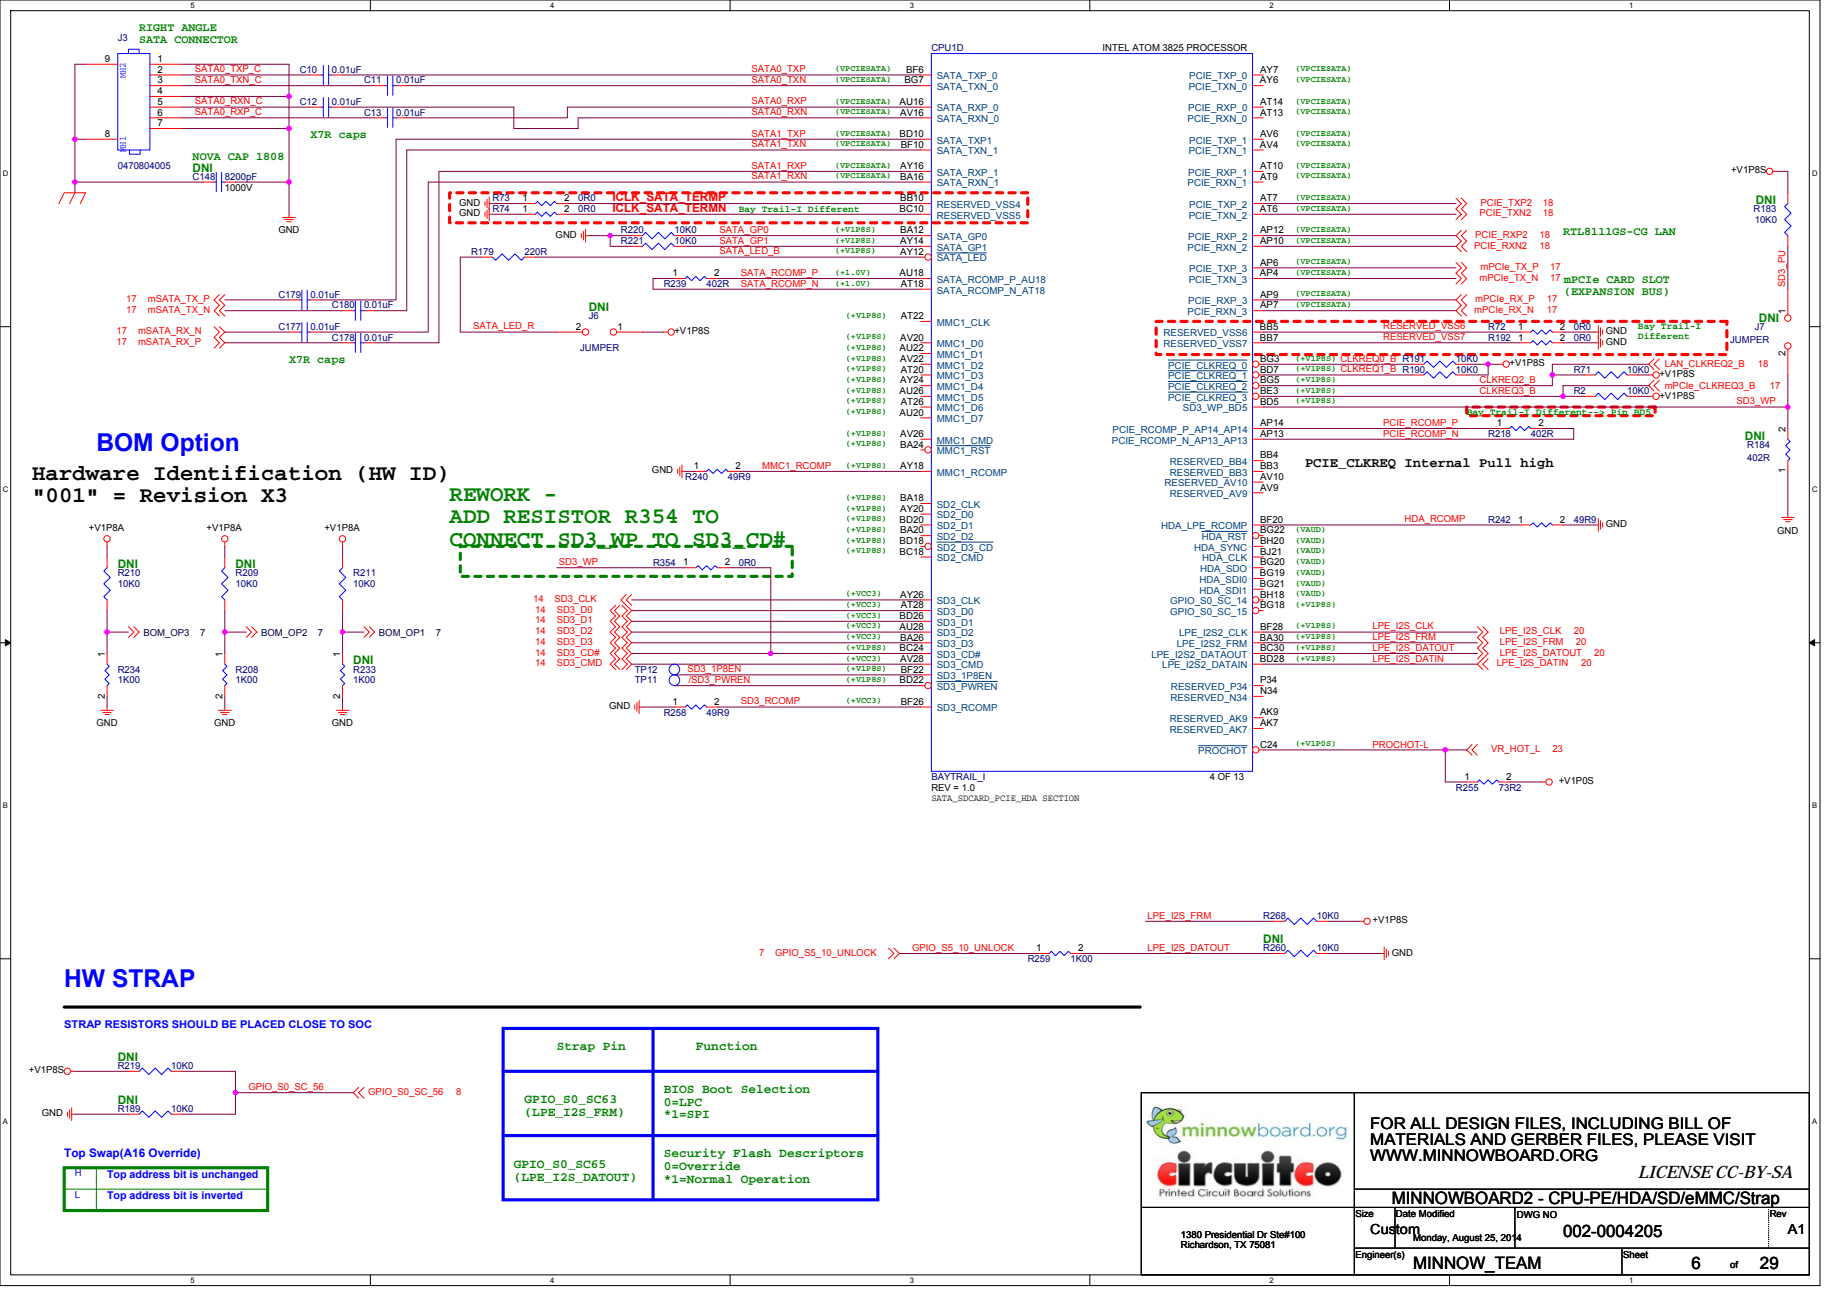
[picture p254: page 6]

Bay Trail-I Different--> Pin BD5

BOM Option
Hardware Identification (HW ID)
"001" = Revision X3

STRAP RESISTORS SHOULD BE PLACED CLOSE TO SOC

Strap Pin | Function

GPIO_S0_SC63 (LPE_I2S_FRM) | BIOS Boot Selection 0=LPC *1=SPI

FOR ALL DESIGN FILES, INCLUDING BILL OF FOR ALL DESIGN FILES, INCLUDING BILL OF FOR ALL DESIGN FILES, INCLUDING BILL OF MATERIALS AND GERBER FILES, PLEASE VISIT MATERIALS AND GERBER FILES, PLEASE VISIT MATERIALS AND GERBER FILES, PLEASE VISIT WWW.MINNOWBOARD.ORG WWW.MINNOWBOARD.ORG WWW.MINNOWBOARD.ORG LICENSE CC-BY-SA

GPIO_S0_SC65 (LPE_I2S_DATOUT) | Security Flash Descriptors 0=Override *1=Normal Operation

H | Top address bit is unchanged

Top address bit is inverted

MINNOWBOARD2 - CPU-PE/HDA/SD/eMMC/Strap

# UPDATE Y2 SYMBOL

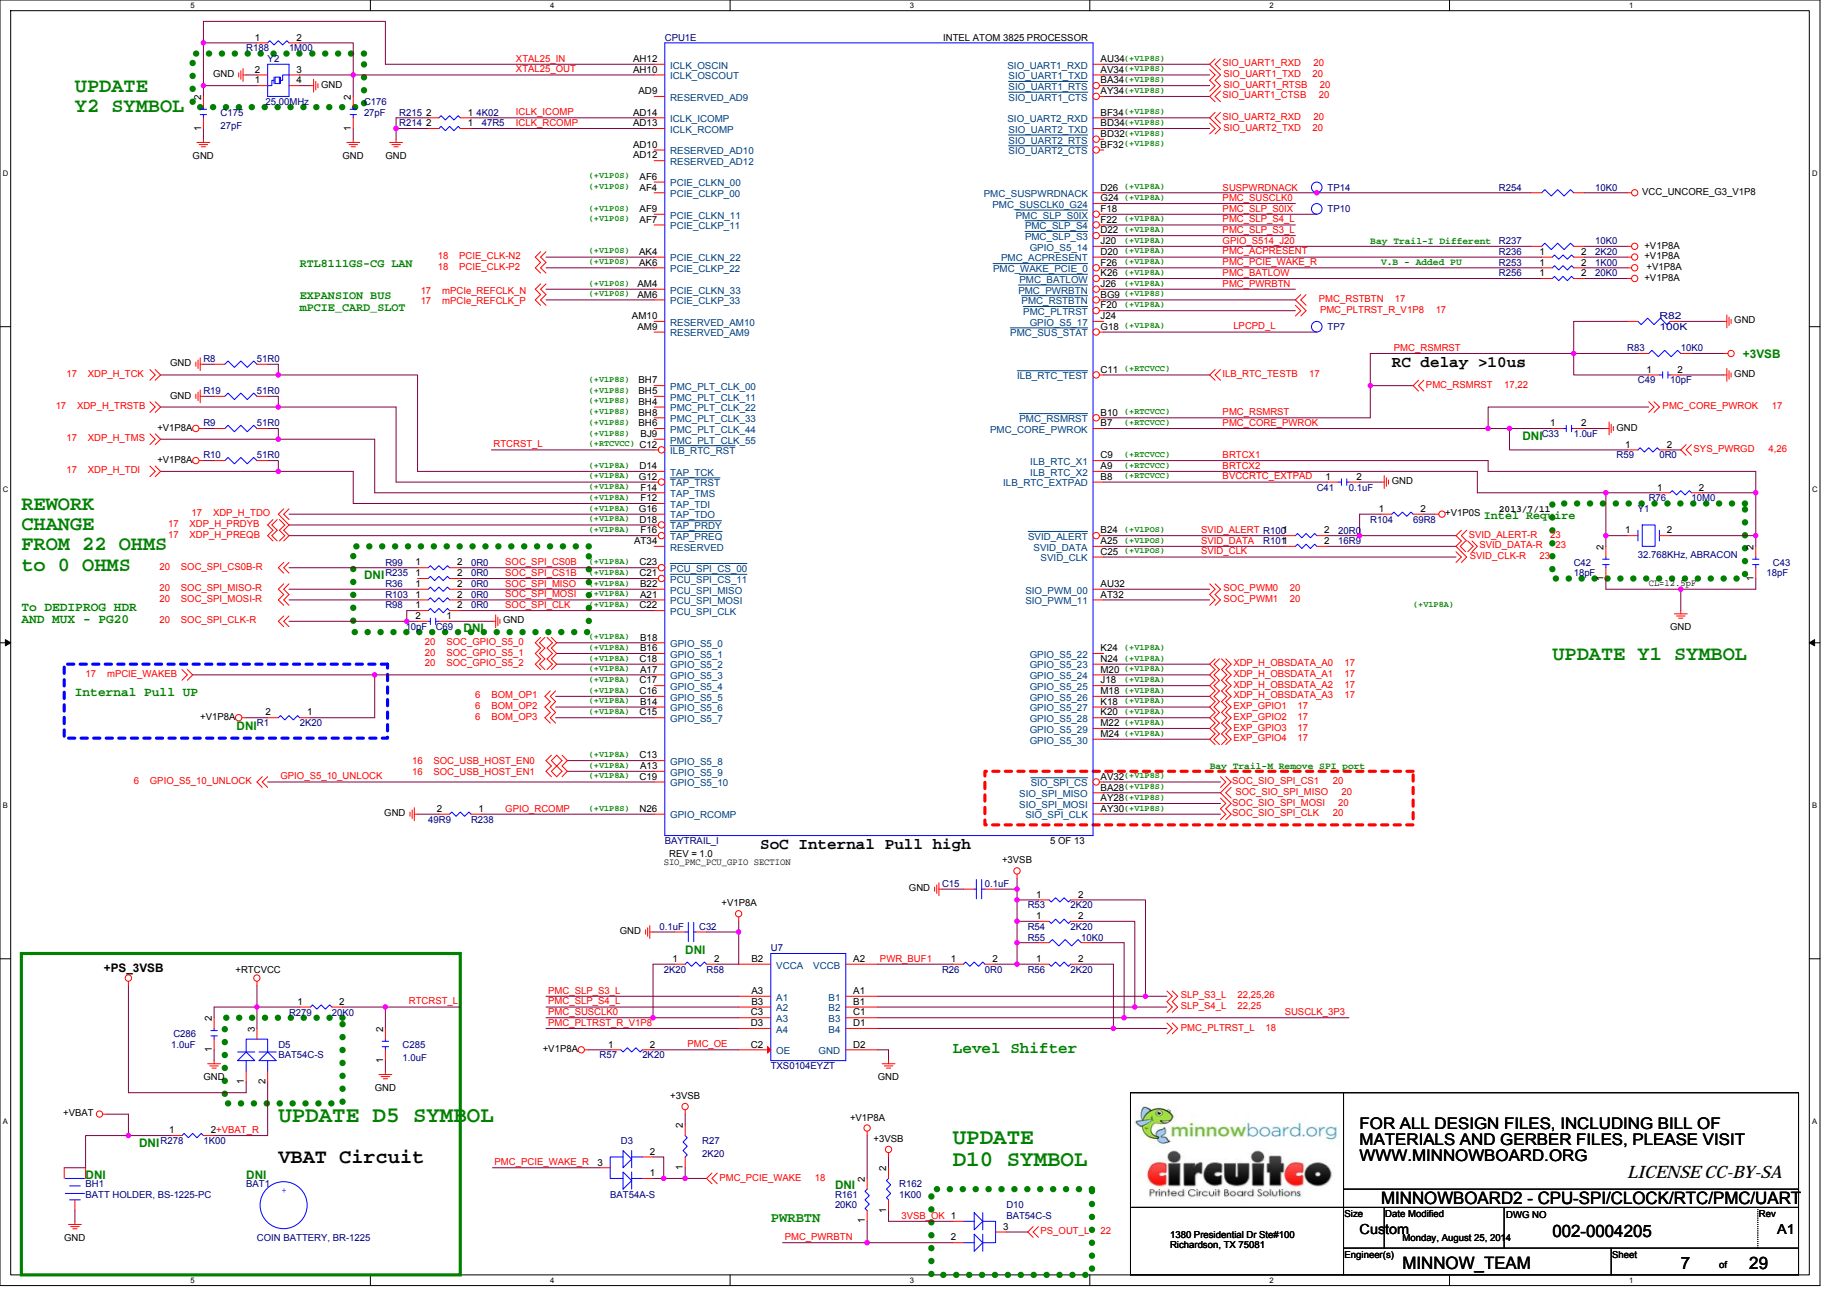
[picture p255: page 7]

Bay Trail-M Remove SPI port

SoC Internal Pull high

FOR ALL DESIGN FILES, INCLUDING BILL OF
MATERIALS AND GERBER FILES, PLEASE VISIT
WWW.MINNOWBOARD.ORG

MINNOWBOARD2 - CPU-SPI/CLOCK/RTC/PMC/UART

## USB2.0

## USB3.0

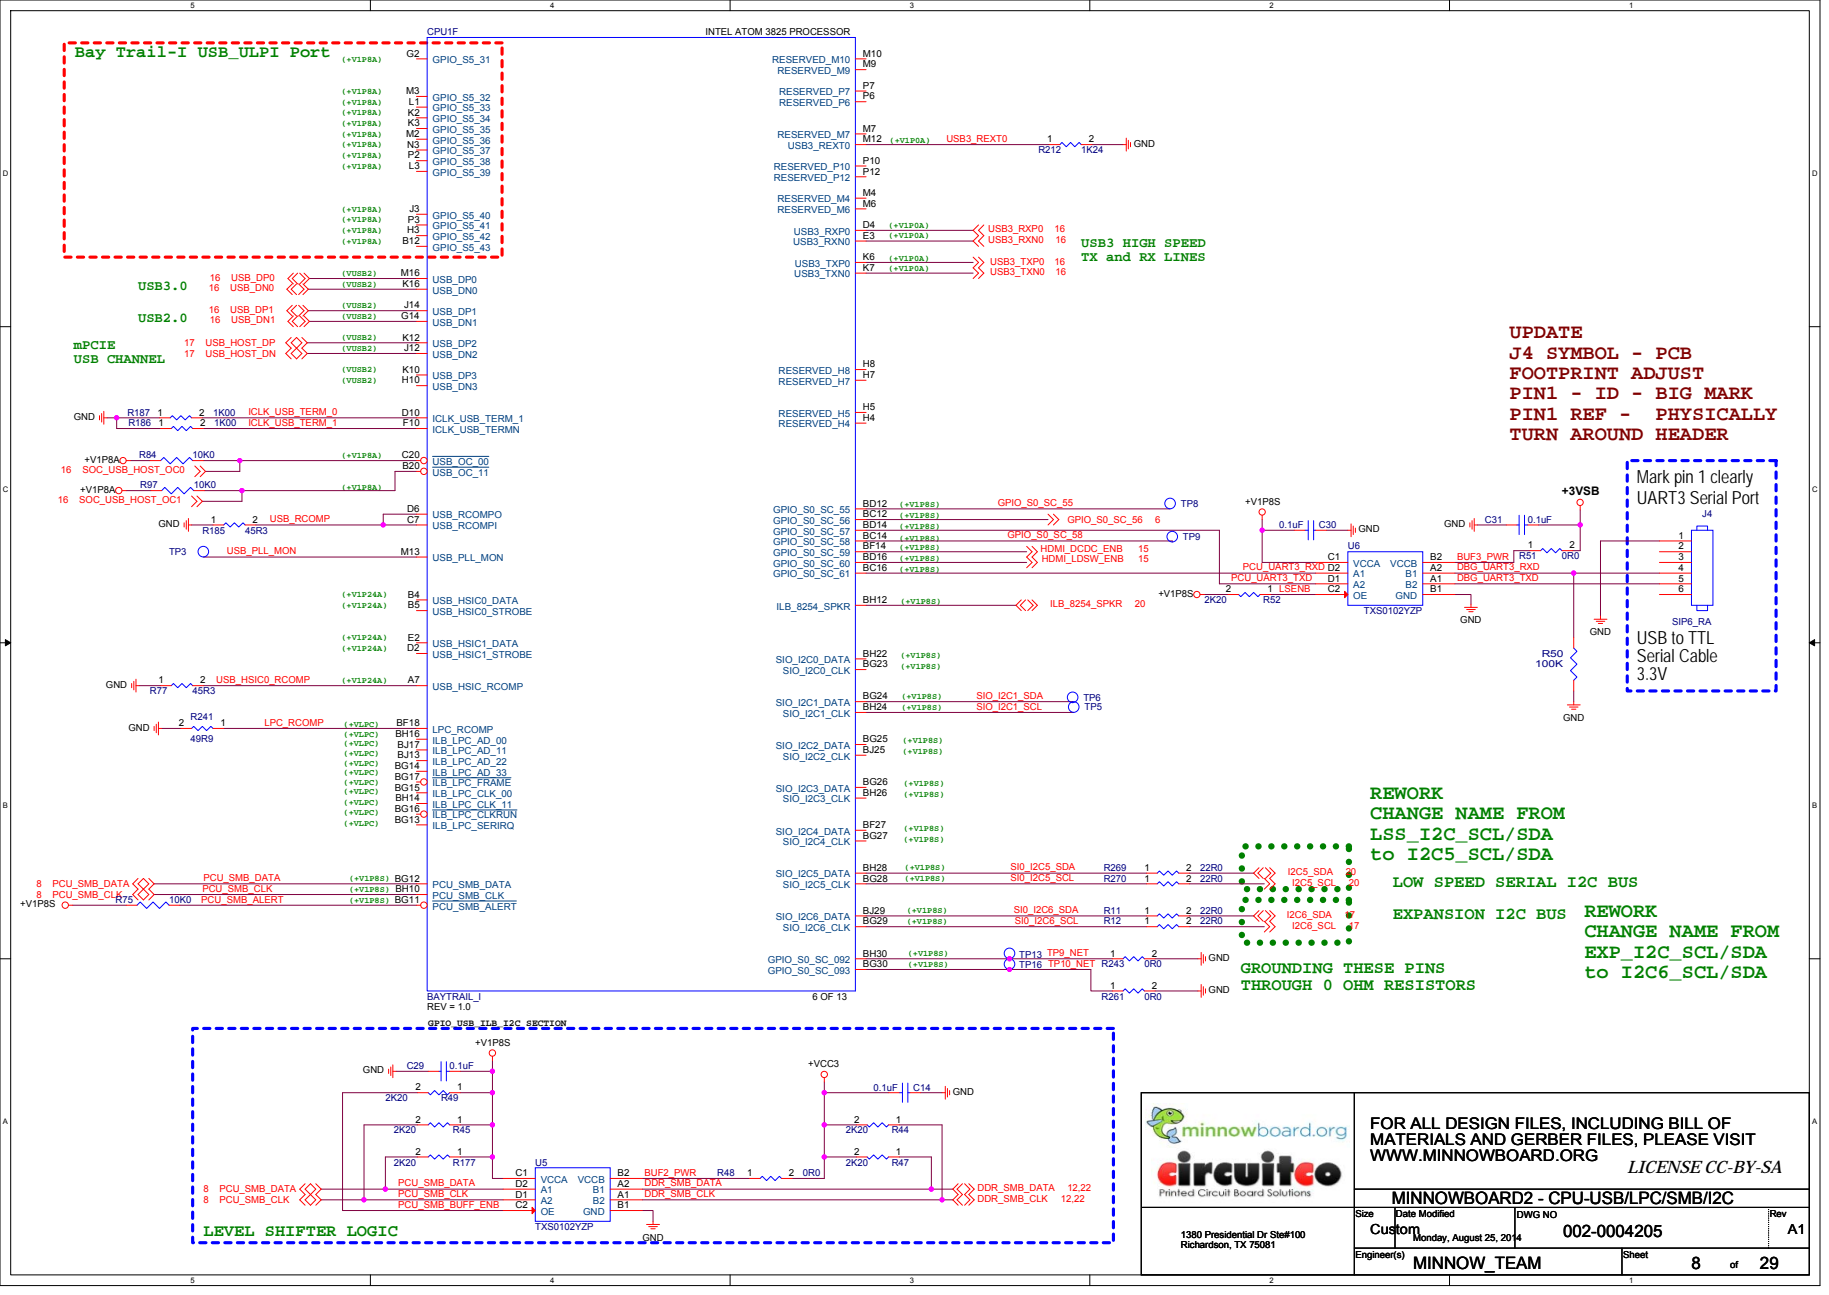
[picture p256: page 8]

USB3 HIGH SPEED
TX and RX LINES

(+V1P8S) SIO_I2C1_SCL TP5 (+V1P8S) (+V1P8S) (+V1P8S) (+V1P8S) (+V1P8S) (+V1P8S) | PCU_UART3_TXD | DBG_UART3_TXD | 5

REWORK
CHANGE NAME FROM
LSS_I2C_SCL/SDA
to I2C5_SCL/SDA
LOW SPEED SERIAL I2C BUS
EXPANSION I2C BUS

FOR ALL DESIGN FILES, INCLUDING BILL OF
MATERIALS AND GERBER FILES, PLEASE VISIT
WWW.MINNOWBOARD.ORG

LICENSE CC-BY-SA

MINNOWBOARD2 - CPU-USB/LPC/SMB/I2C

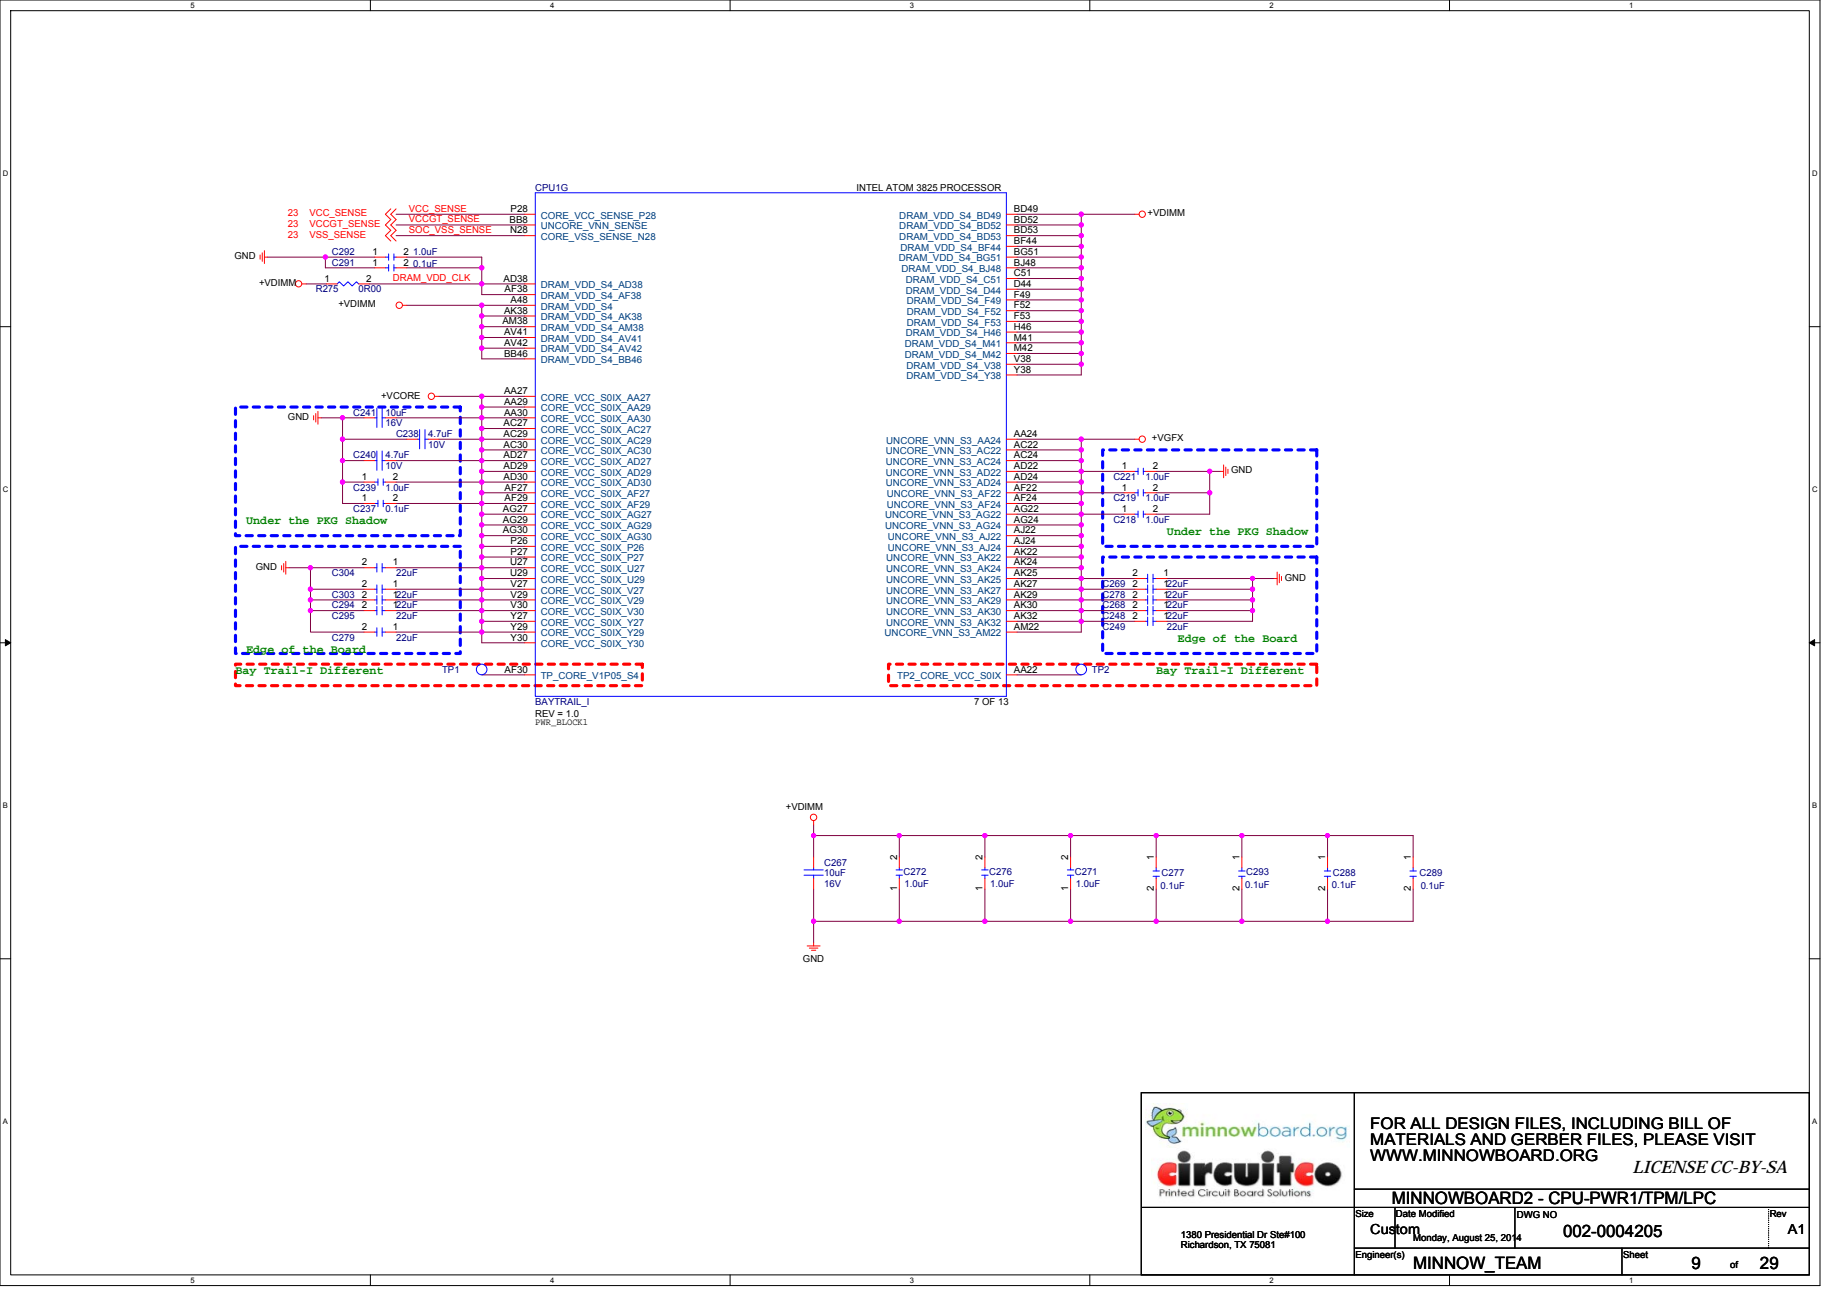
[picture p257: page 9]

Under the PKG Shadow

C269 2 | 1 22uF
C278 2 | 1 22uF
C268 2 | 1 22uF

Edge of the Board

FOR ALL DESIGN FILES, INCLUDING BILL OF
MATERIALS AND GERBER FILES, PLEASE VISIT
WWW.MINNOWBOARD.ORG

LICENSE CC-BY-SA

900mA

10mA

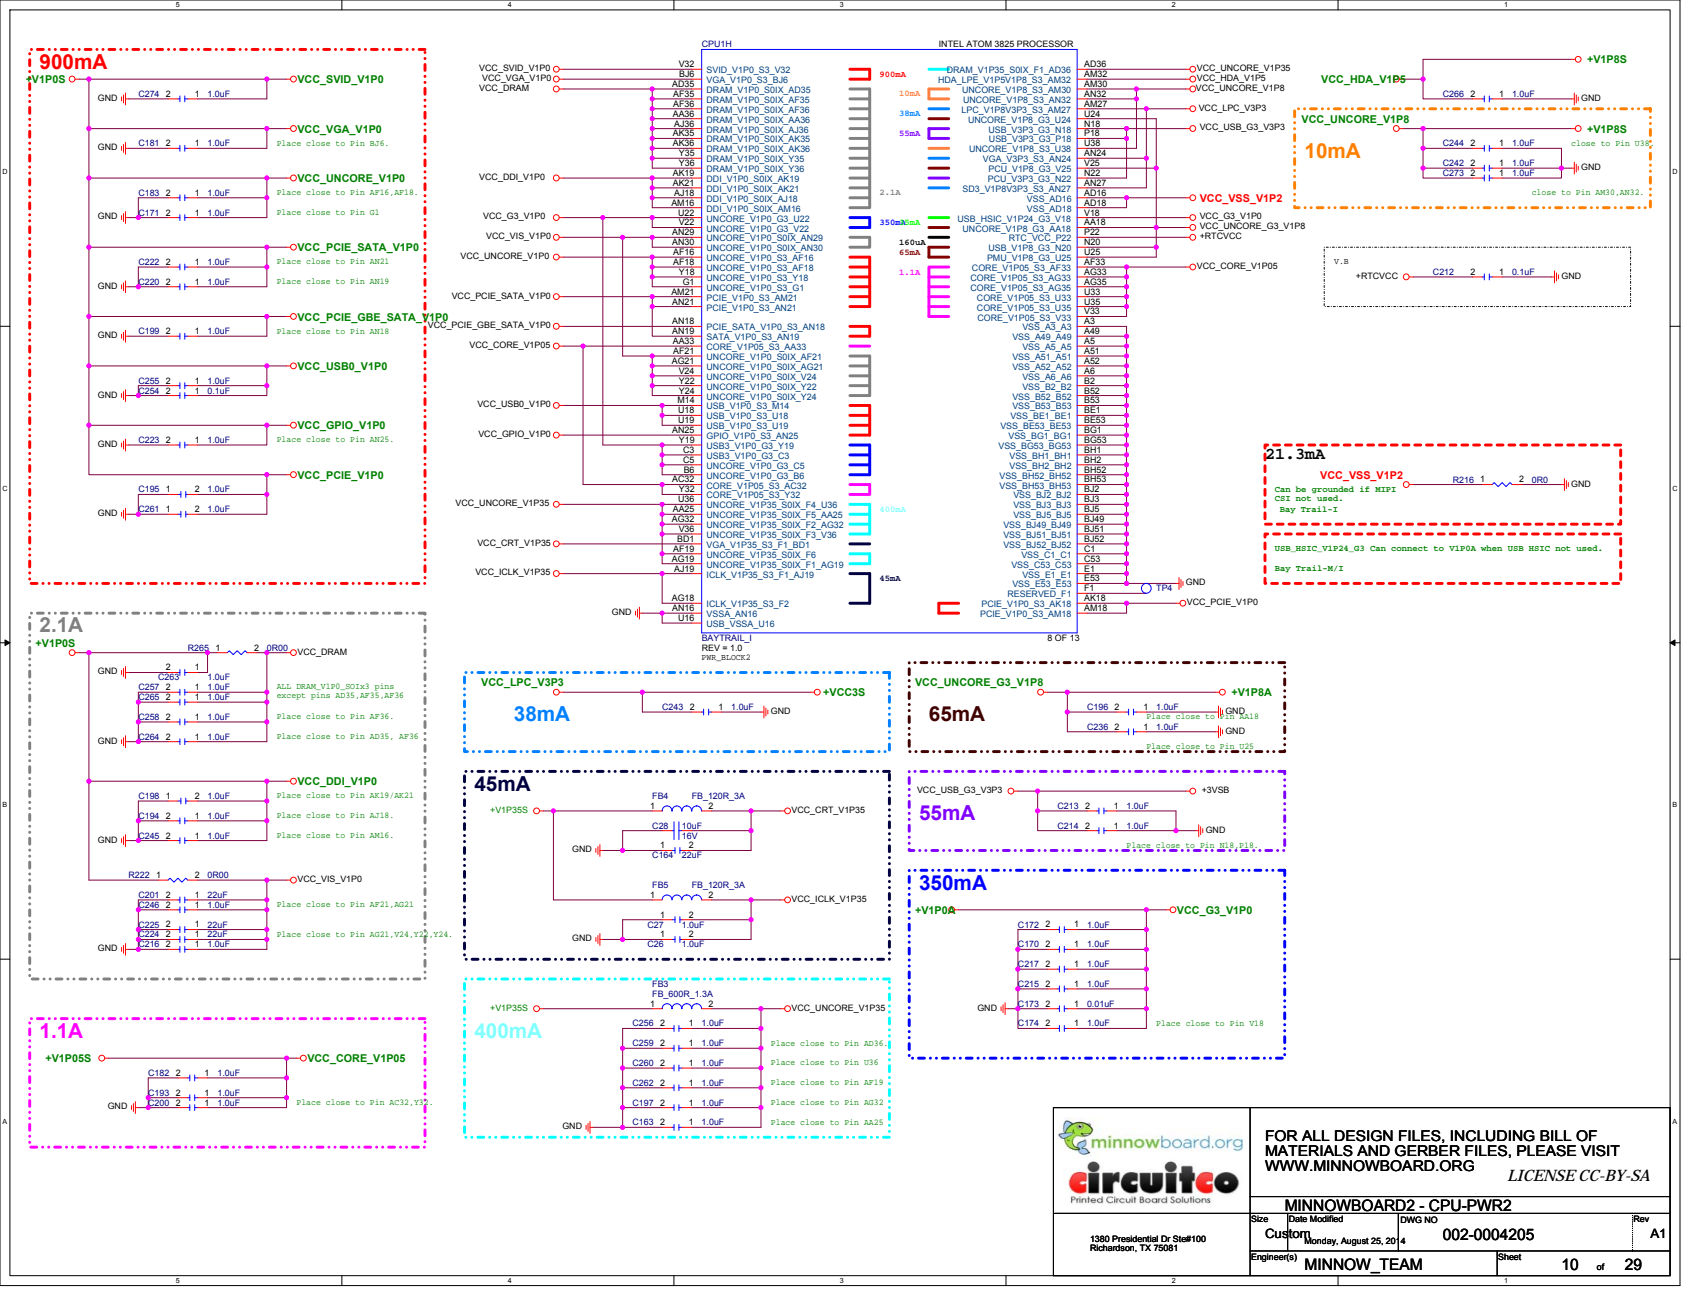
[picture p258: page 10]

VCC_VGA_V1P0
Place close to Pin BJ6.

VCC_UNCORE_V1P0
Place close to Pin AF16,AF18.

Place close to Pin G1

VCC_UNCORE_V1P0 VCC_PCIE_SATA_V1P0
Place close to Pin AN21

Place close to Pin AN19

VCC_PCIE_GBE_SATA_V1P0
Place close to Pin AN18

VCC_GPIO_V1P0
Place close to Pin AN25.

Can be grounded if MIPI
CSI not used.
Bay Trail-I

USB_HSIC_V1P24_G3 Can connect to V1P0A when USB HSIC not used.

Place close to Pin AF36.

Place close to Pin AD35, AF36

Place close to Pin U25

VCC_DDI_V1P0
Place close to Pin AK19/AK21

Place close to Pin AJ18.

Place close to Pin AM16.

Place close to Pin N18,P18.

Place close to Pin AF21,AG21

Place close to Pin AG21,V24,Y22,Y24.

Place close to Pin AD36.

Place close to Pin U36

Place close to Pin AF19

Place close to Pin AC32,Y32.

Place close to Pin AG32

Place close to Pin AA25

FOR ALL DESIGN FILES, INCLUDING BILL OF
MATERIALS AND GERBER FILES, PLEASE VISIT
WWW.MINNOWBOARD.ORG

LICENSE CC-BY-SA

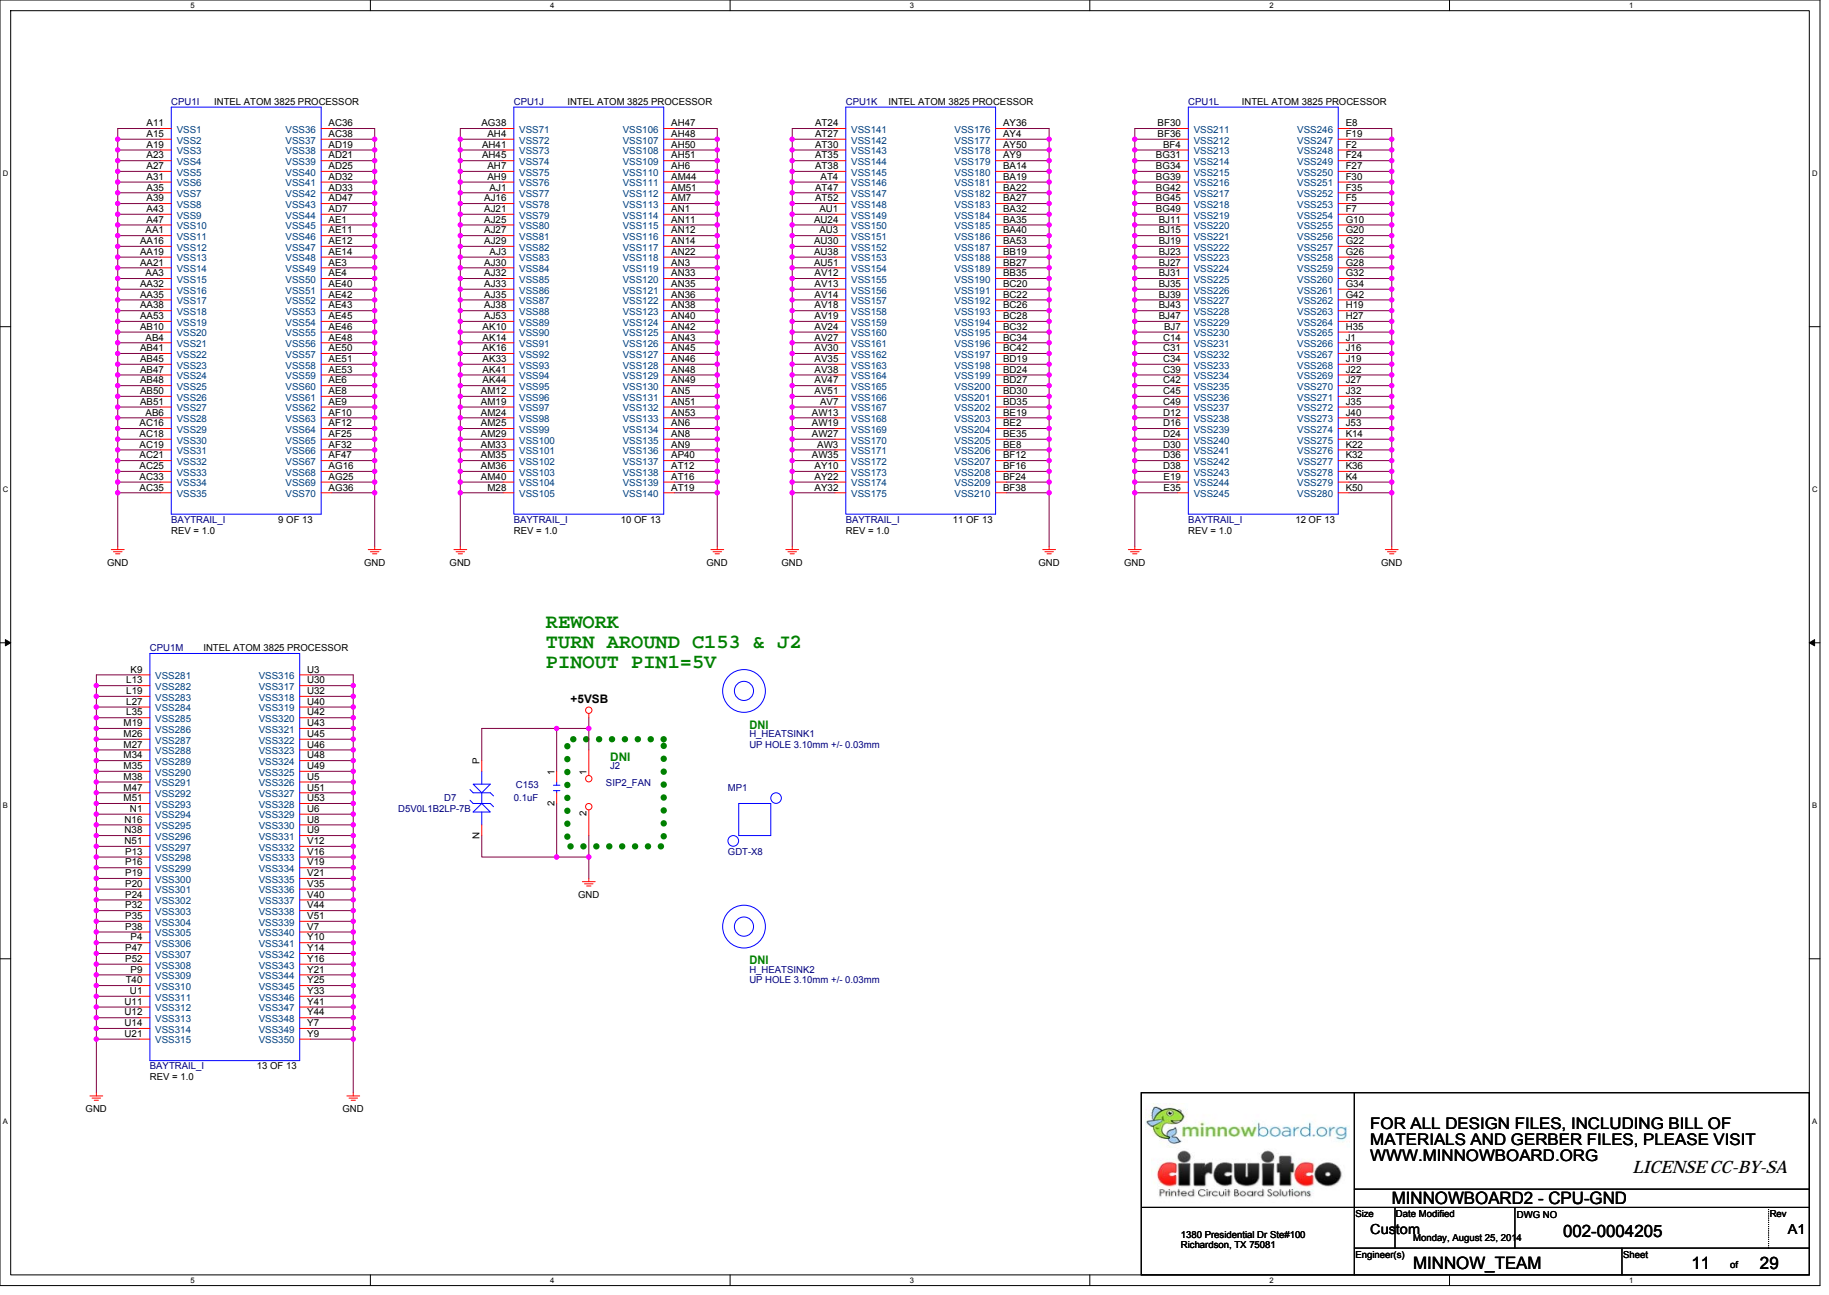
[picture p259: page 11]

FOR ALL DESIGN FILES, INCLUDING BILL OF
MATERIALS AND GERBER FILES, PLEASE VISIT
WWW.MINNOWBOARD.ORG

LICENSE CC-BY-SA

UPDATE MEM2 SYMBOL - 256Mx16 | UPDATE MEM3 SYMBOL - 256Mx16

# UPDATE CAP SYMBOLS

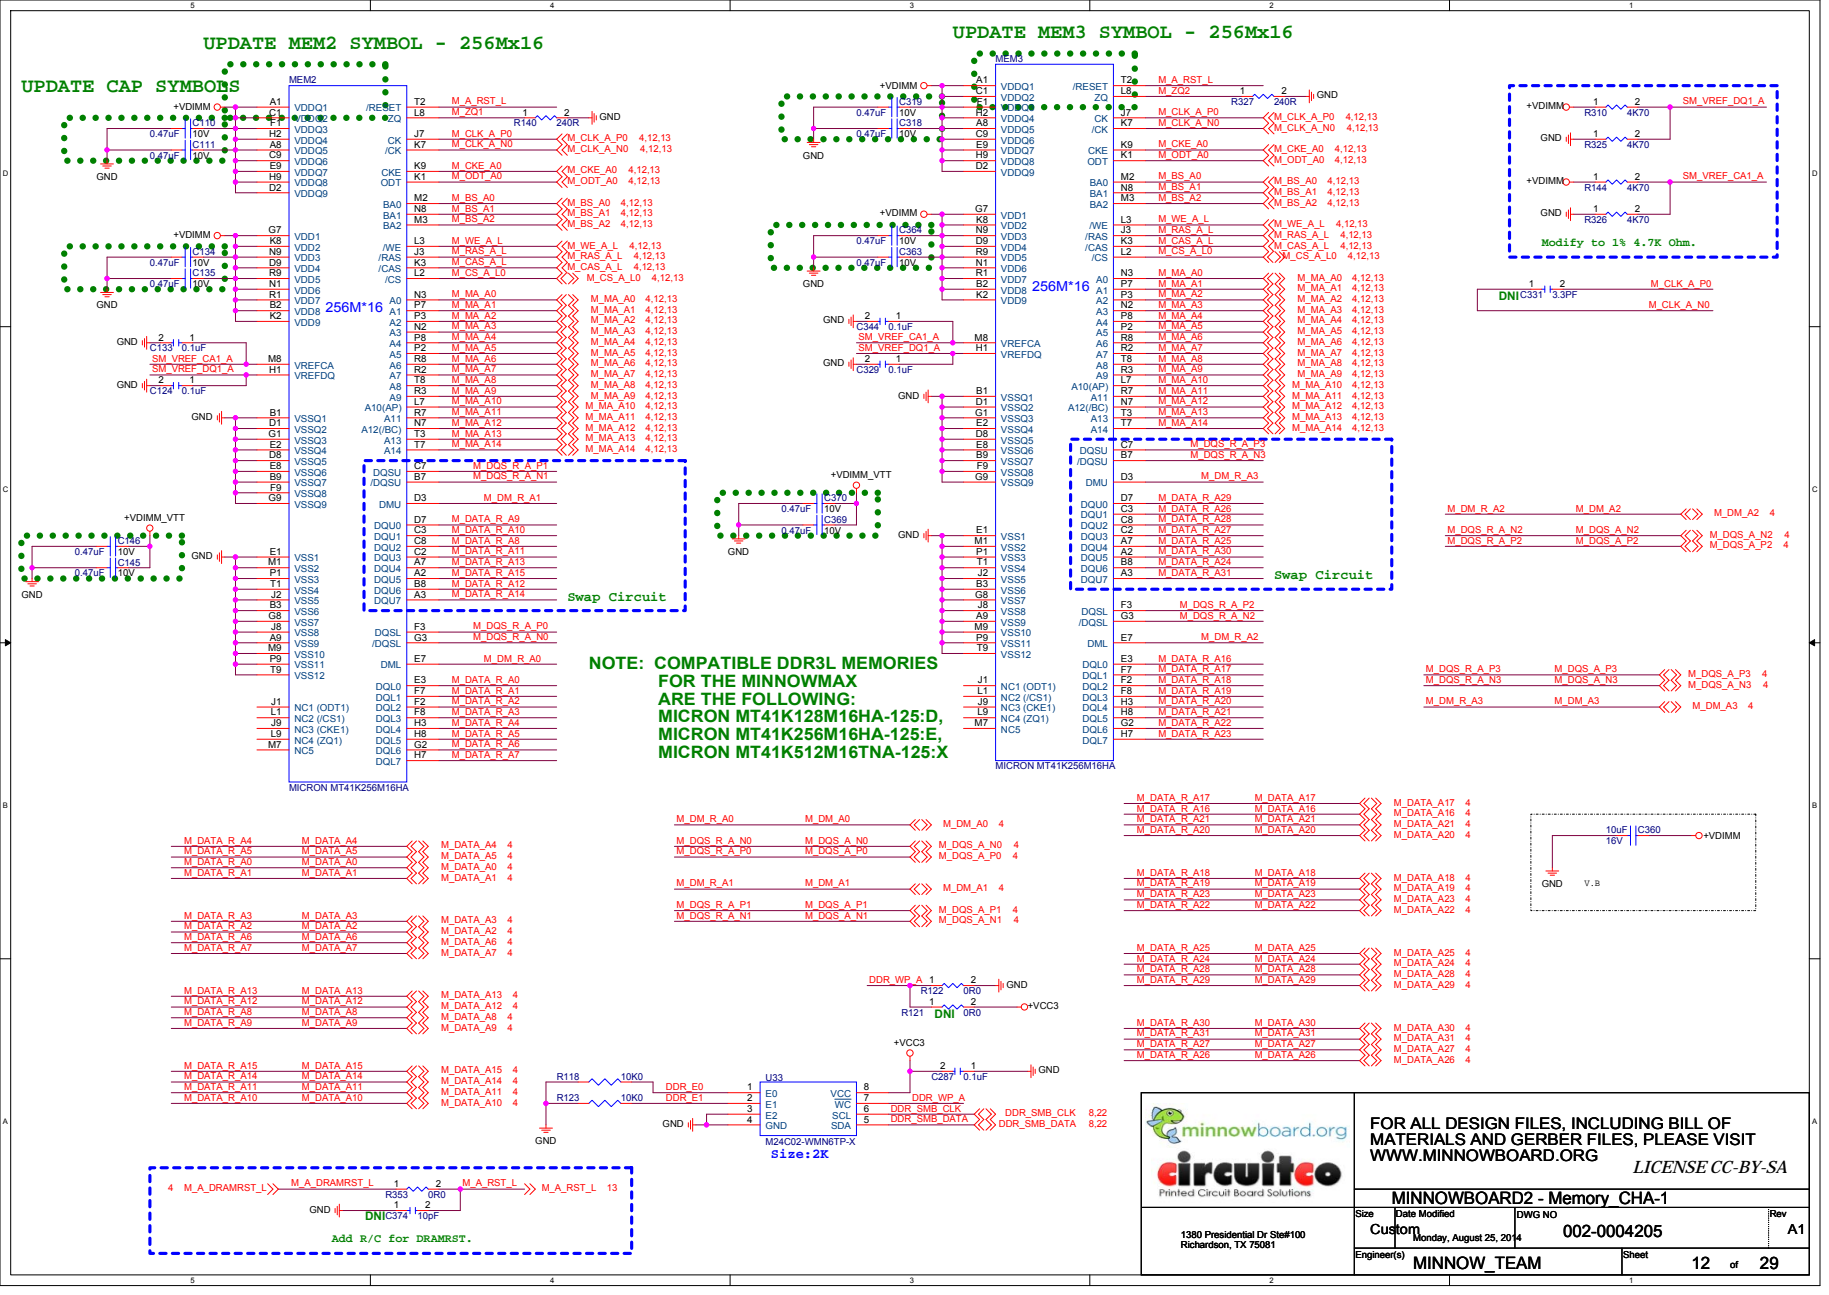
[picture p260: page 12]

FOR ALL DESIGN FILES, INCLUDING BILL OF
MATERIALS AND GERBER FILES, PLEASE VISIT
WWW.MINNOWBOARD.ORG

LICENSE CC-BY-SA

UPDATE MEM1 SYMBOL - 256Mx16 | UPDATE MEM4 SYMBOL - 256Mx16

# UPDATE CAP SYMBOLS

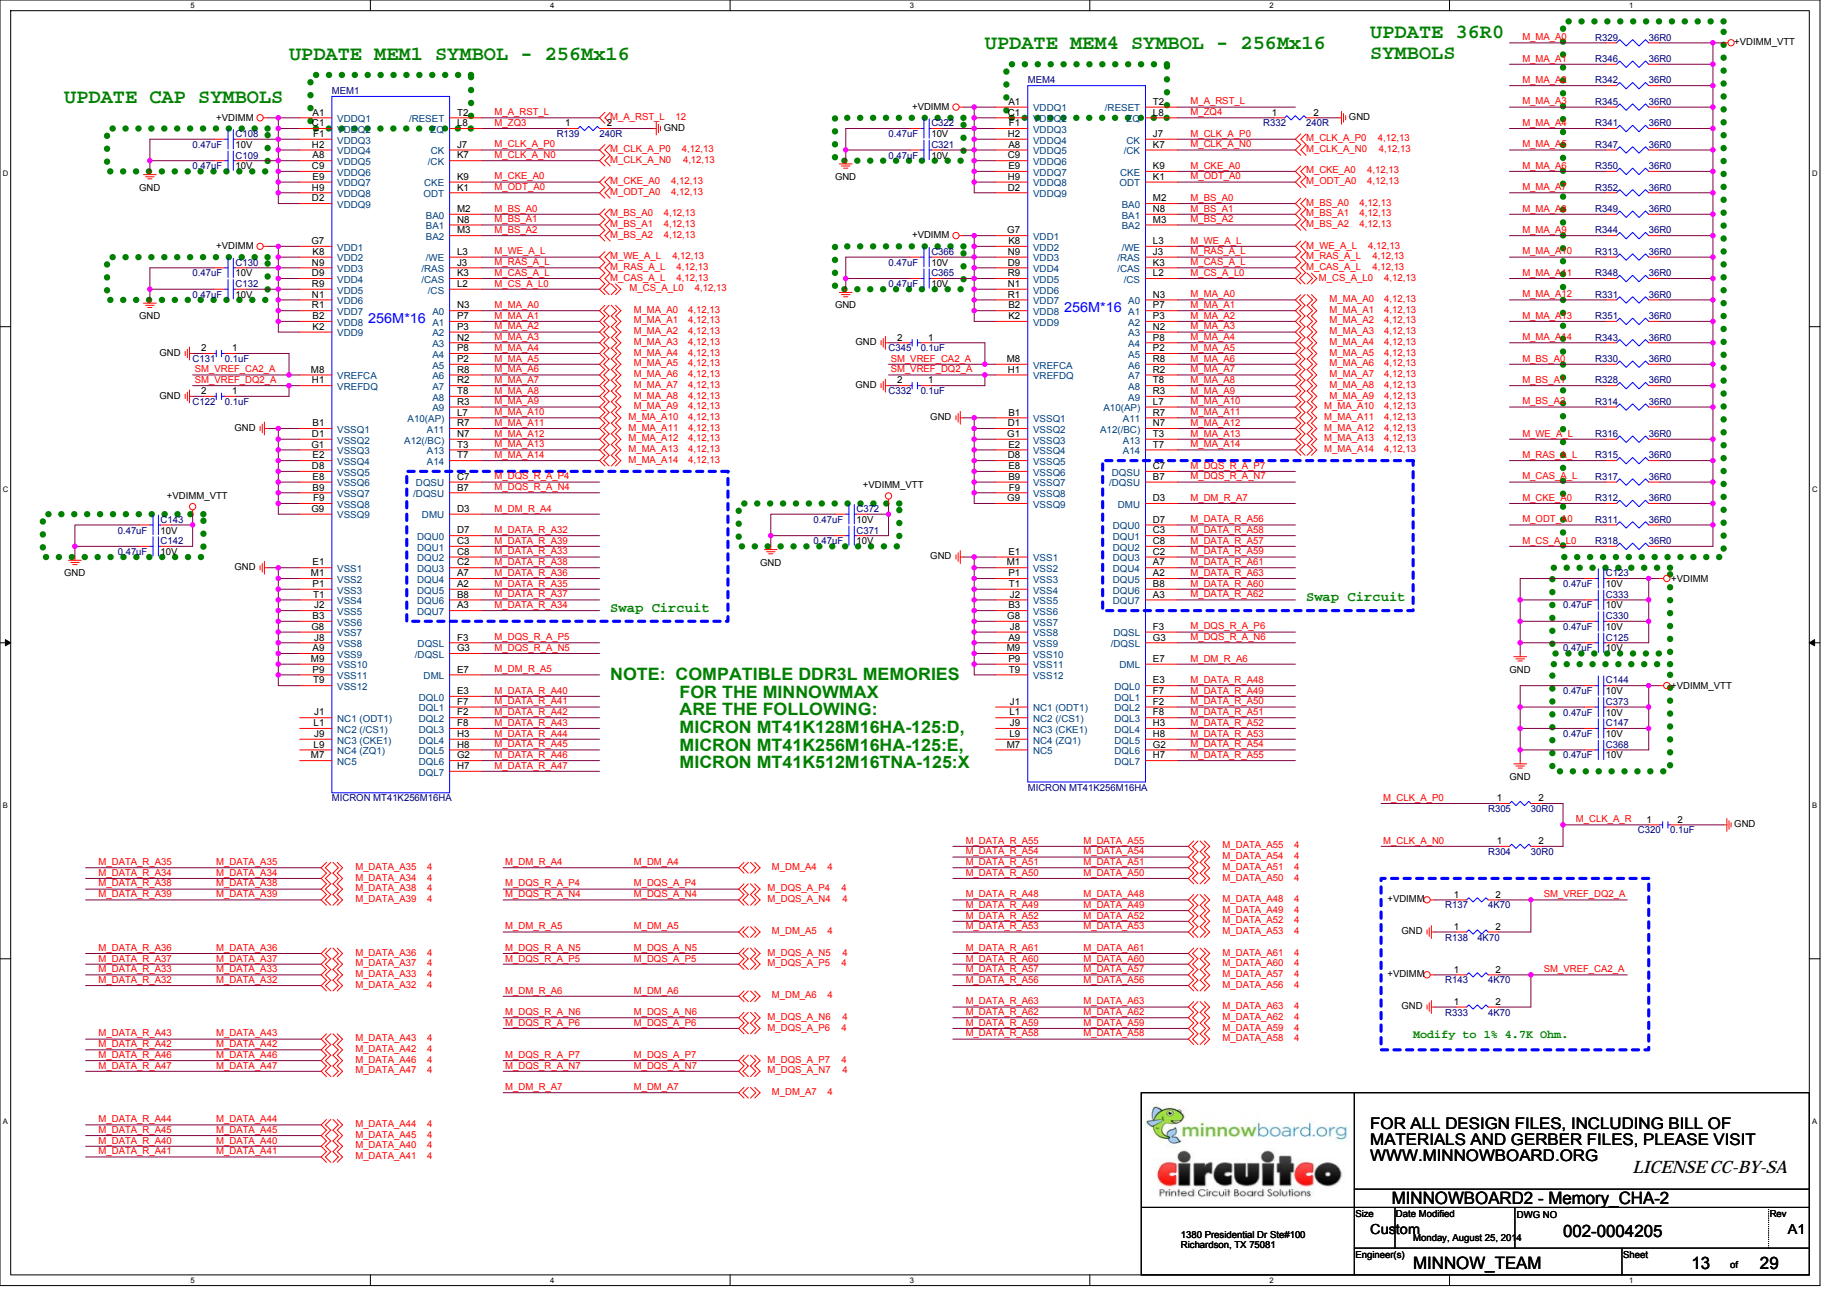
[picture p261: page 13]

FOR ALL DESIGN FILES, INCLUDING BILL OF
MATERIALS AND GERBER FILES, PLEASE VISIT
WWW.MINNOWBOARD.ORG

LICENSE CC-BY-SA

# REWORK -

R182

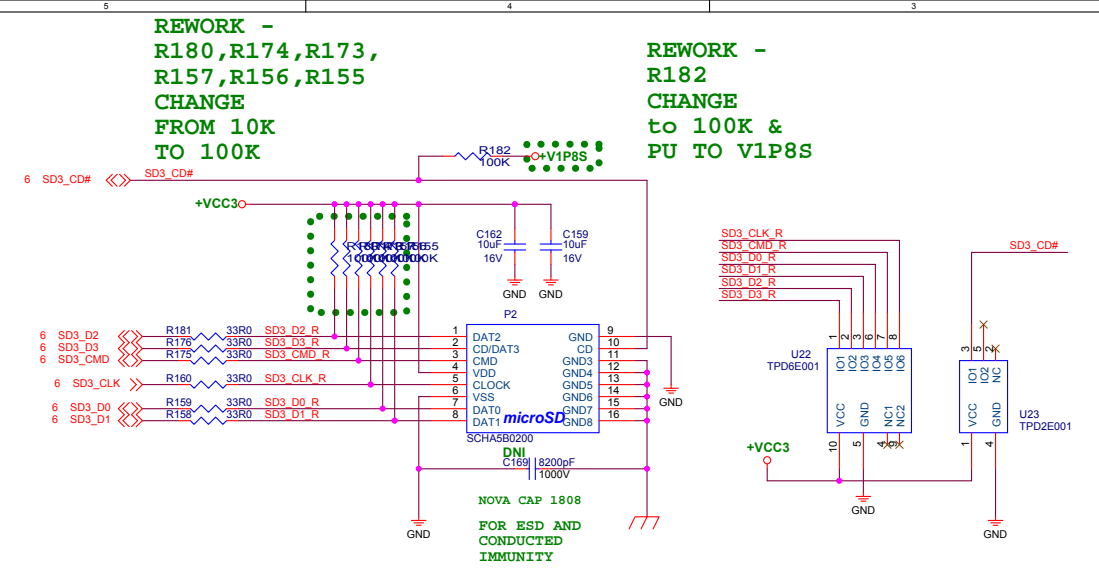
[picture p262: page 14]

FOR ALL DESIGN FILES, INCLUDING BILL OF
MATERIALS AND GERBER FILES, PLEASE VISIT
WWW.MINNOWBOARD.ORG

LICENSE CC-BY-SA

# uHDMI Connector Type D NEW TYPE - 4 THRU-HOLE

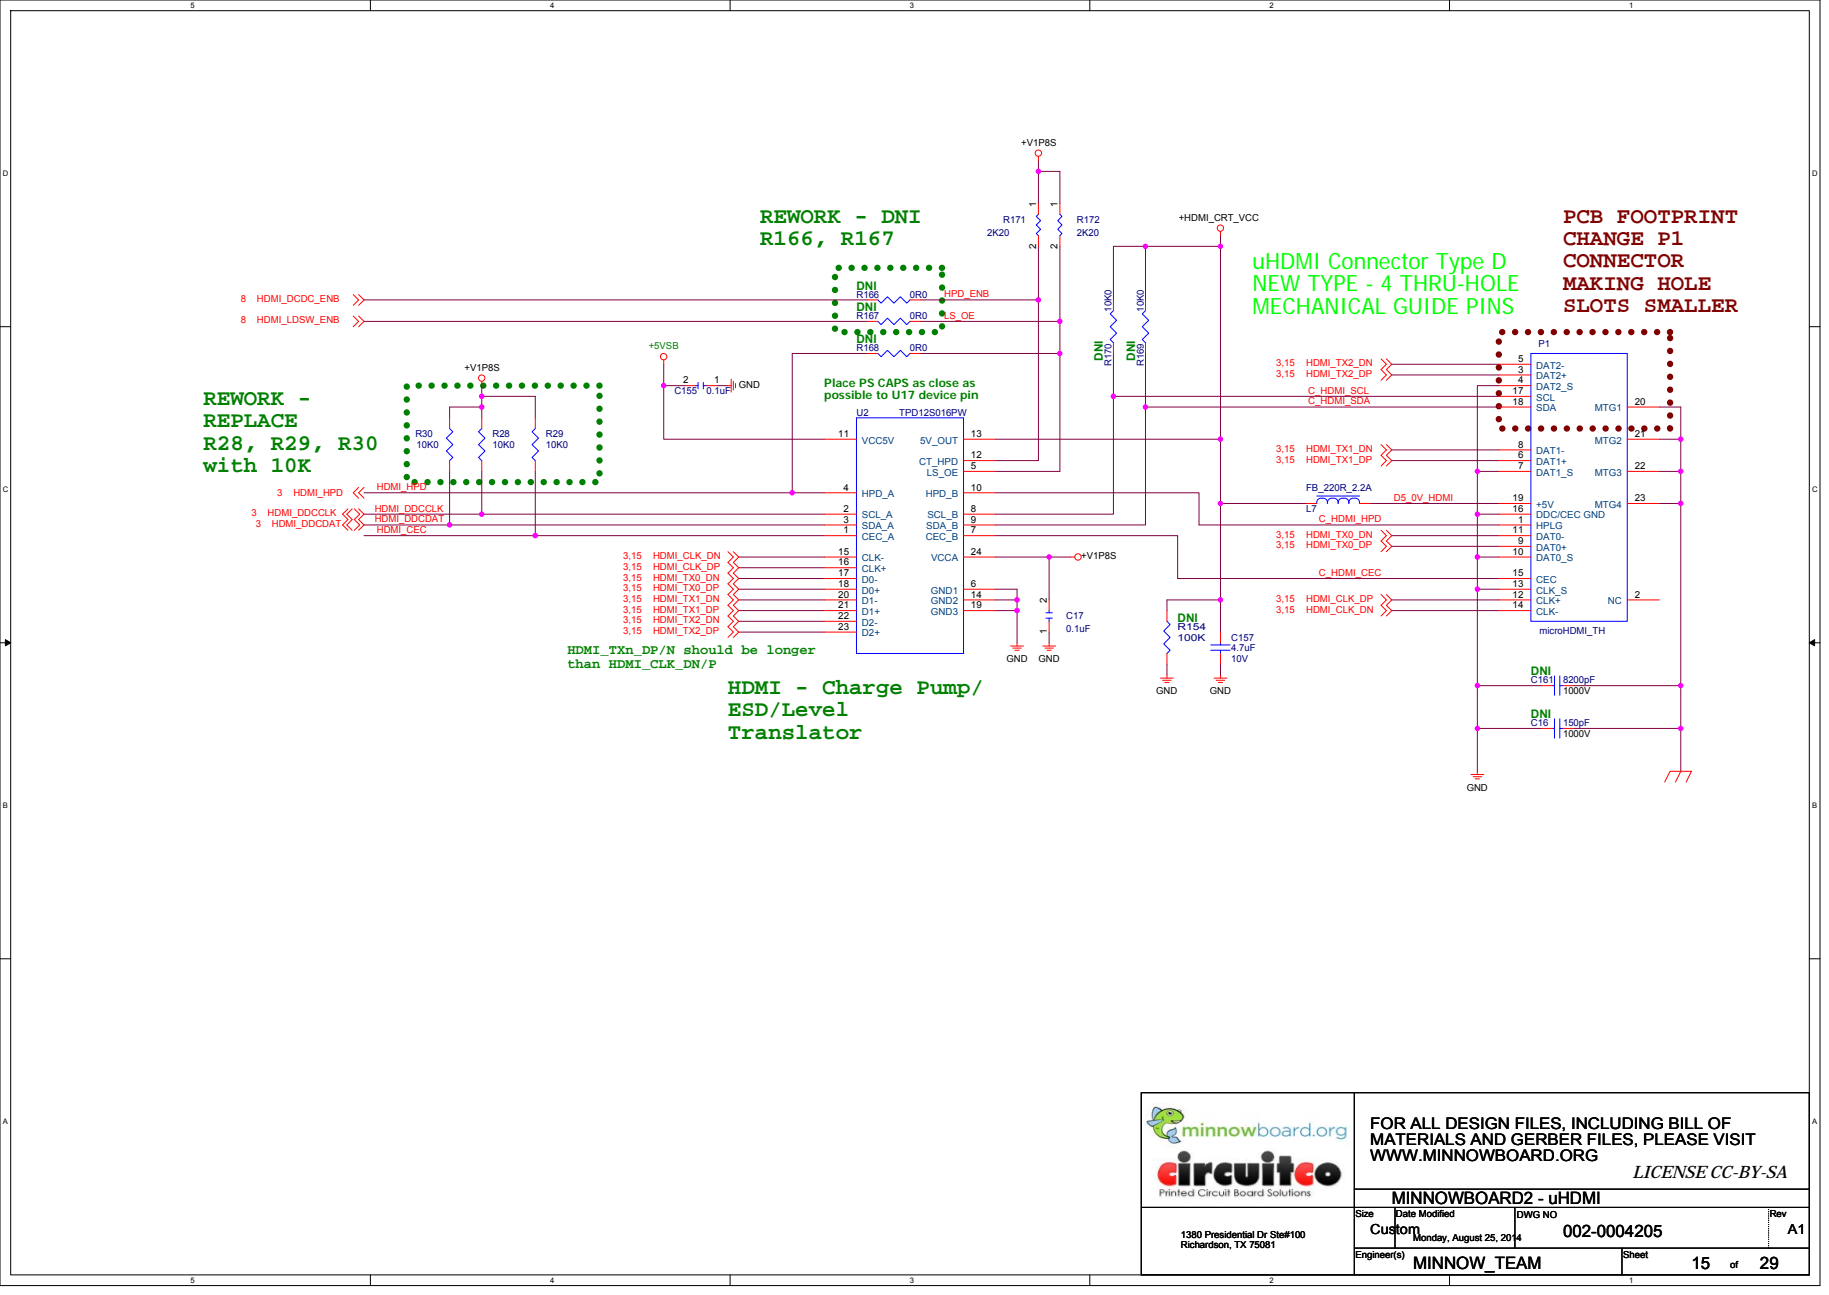
[picture p263: page 15]

Place PS CAPS as close as
possible to U17 device pin

FOR ALL DESIGN FILES, INCLUDING BILL OF
MATERIALS AND GERBER FILES, PLEASE VISIT
WWW.MINNOWBOARD.ORG

LICENSE CC-BY-SA

# USB3.0

# USB2.0

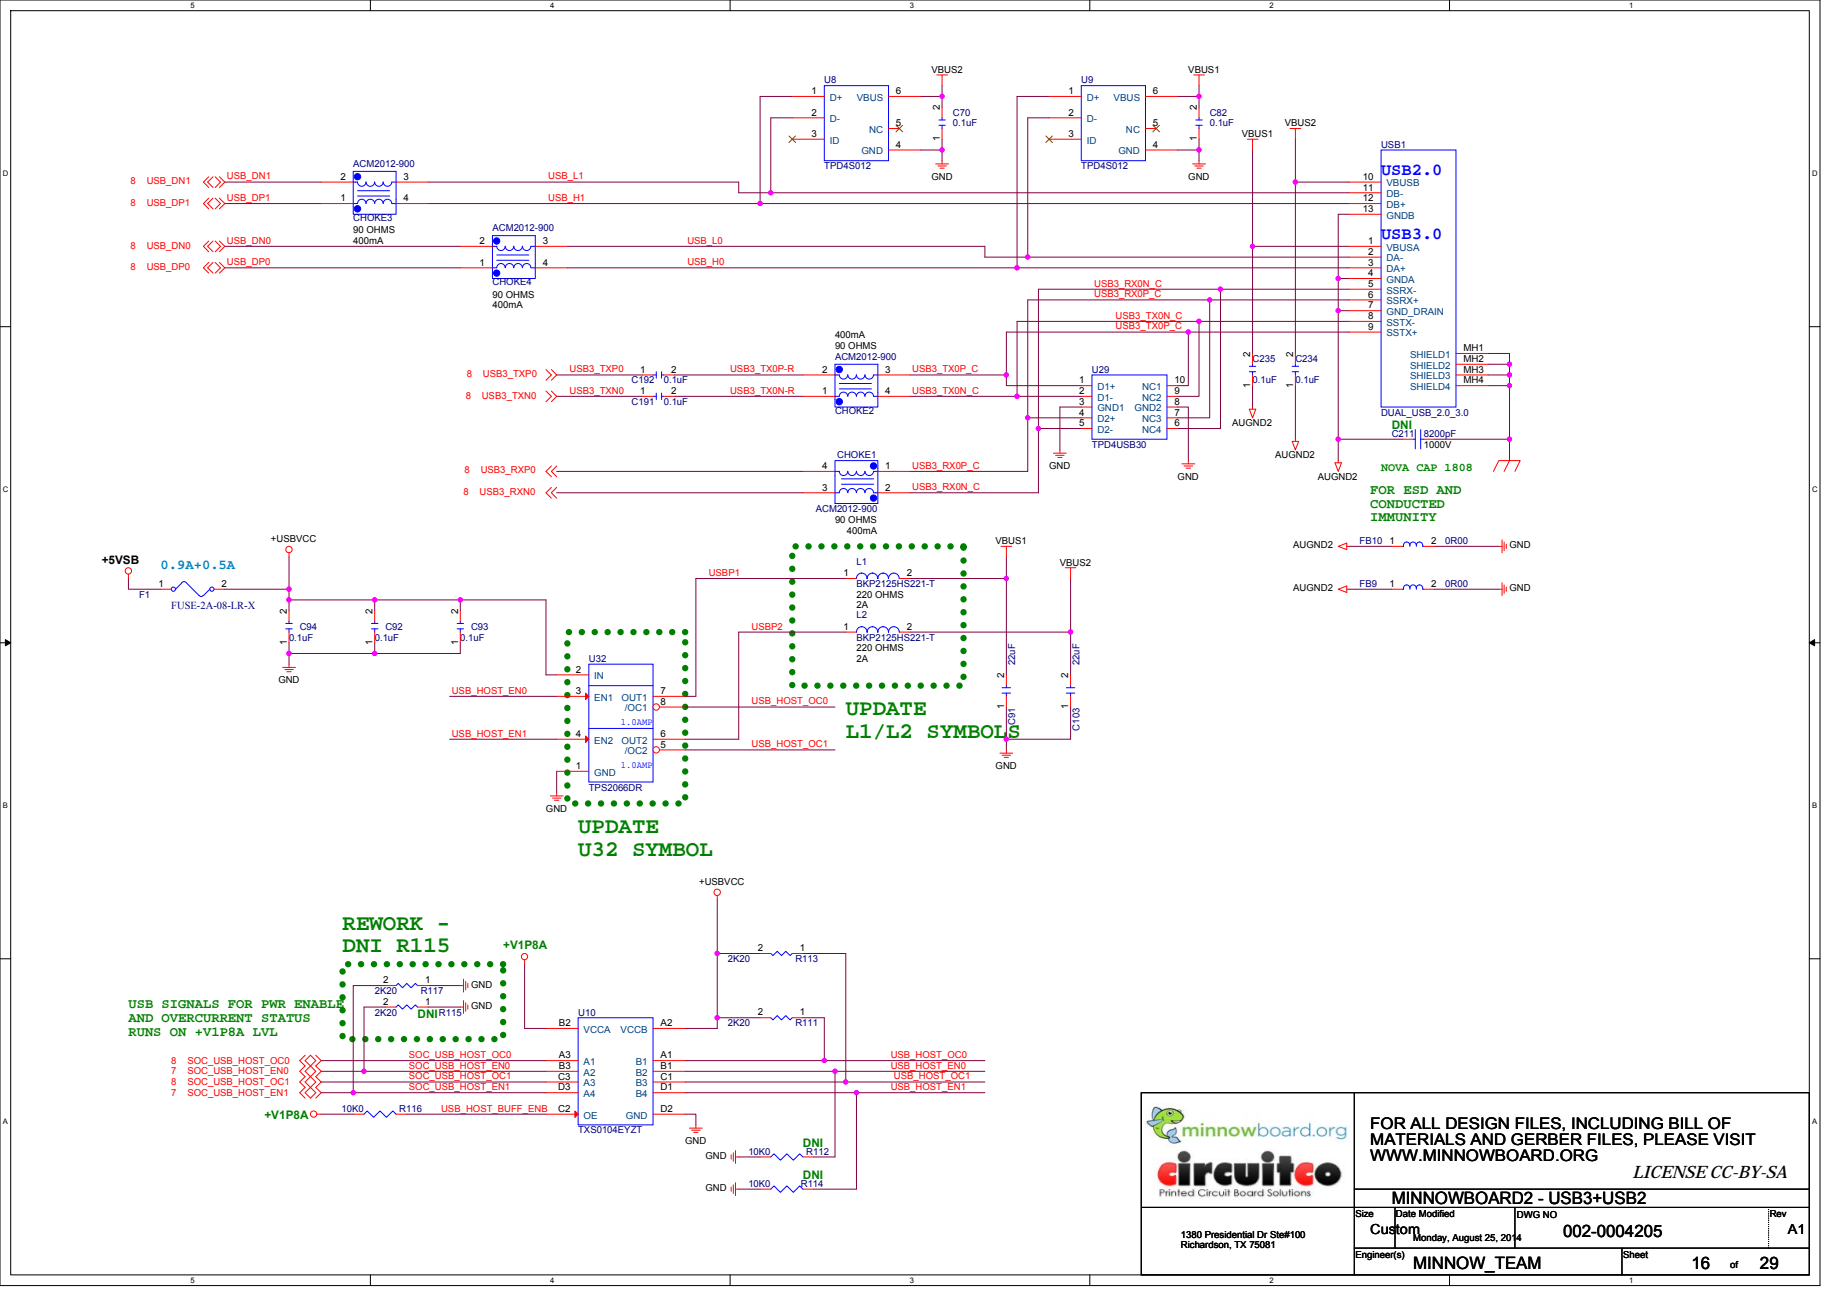
[picture p264: page 16]

USB3_RX0P_C | | | SSRX+ 6
USB3_TX0N_C | | | GND_DRAIN 7

USB3_TX0P_C | | | SSTX+ 9

USB SIGNALS FOR PWR ENABLE
AND OVERCURRENT STATUS
RUNS ON +V1P8A LVL

FOR ALL DESIGN FILES, INCLUDING BILL OF
MATERIALS AND GERBER FILES, PLEASE VISIT
WWW.MINNOWBOARD.ORG

LICENSE CC-BY-SA

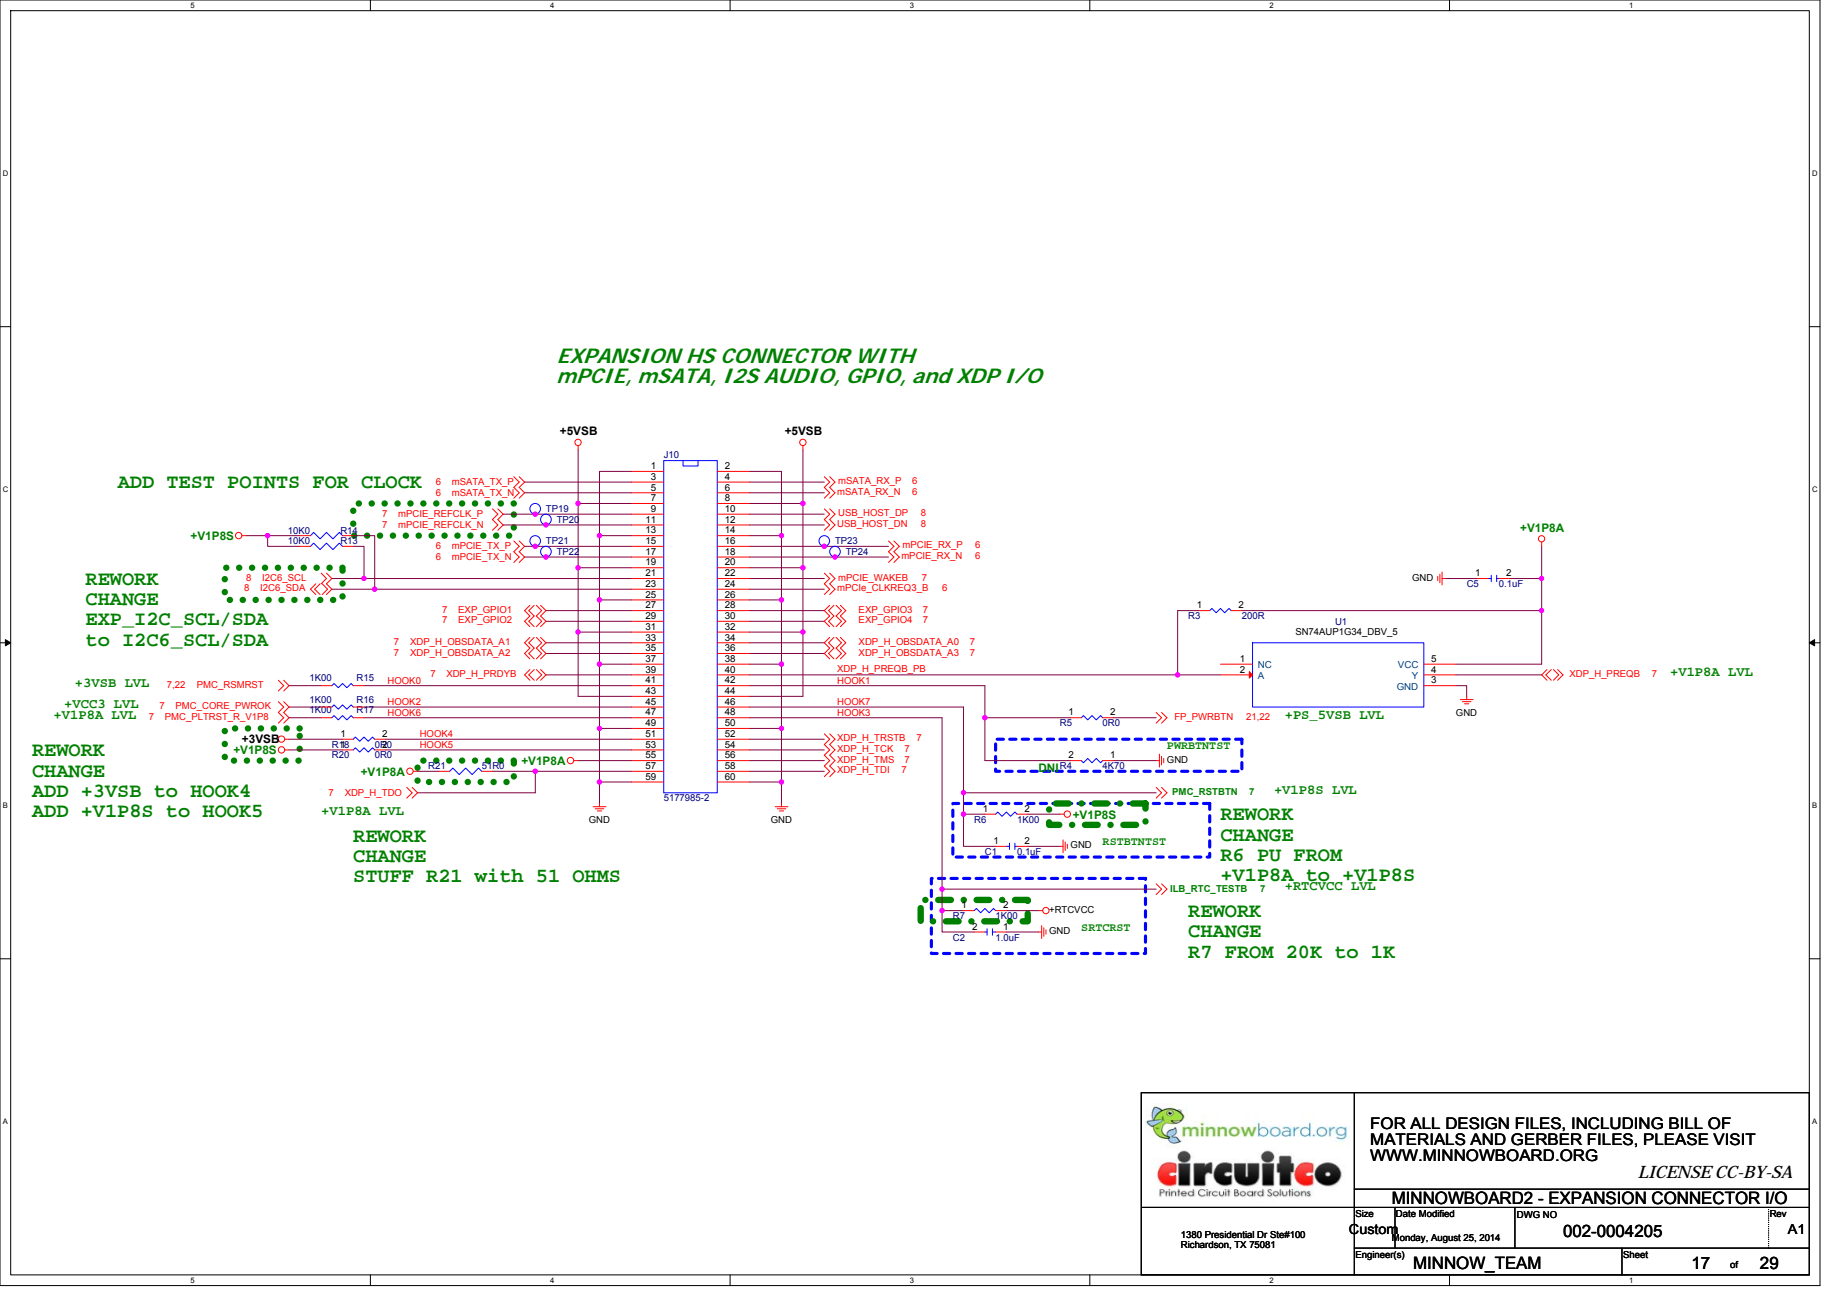
[picture p265: page 17]

EXPANSION HS CONNECTOR WITH
mPCIE, mSATA, I2S AUDIO, GPIO, and XDP I/O

ADD TEST POINTS FOR CLOCK

FOR ALL DESIGN FILES, INCLUDING BILL OF
MATERIALS AND GERBER FILES, PLEASE VISIT
WWW.MINNOWBOARD.ORG

LICENSE CC-BY-SA

## Closed To The CHOKE¡I

## Closed To Pin 23

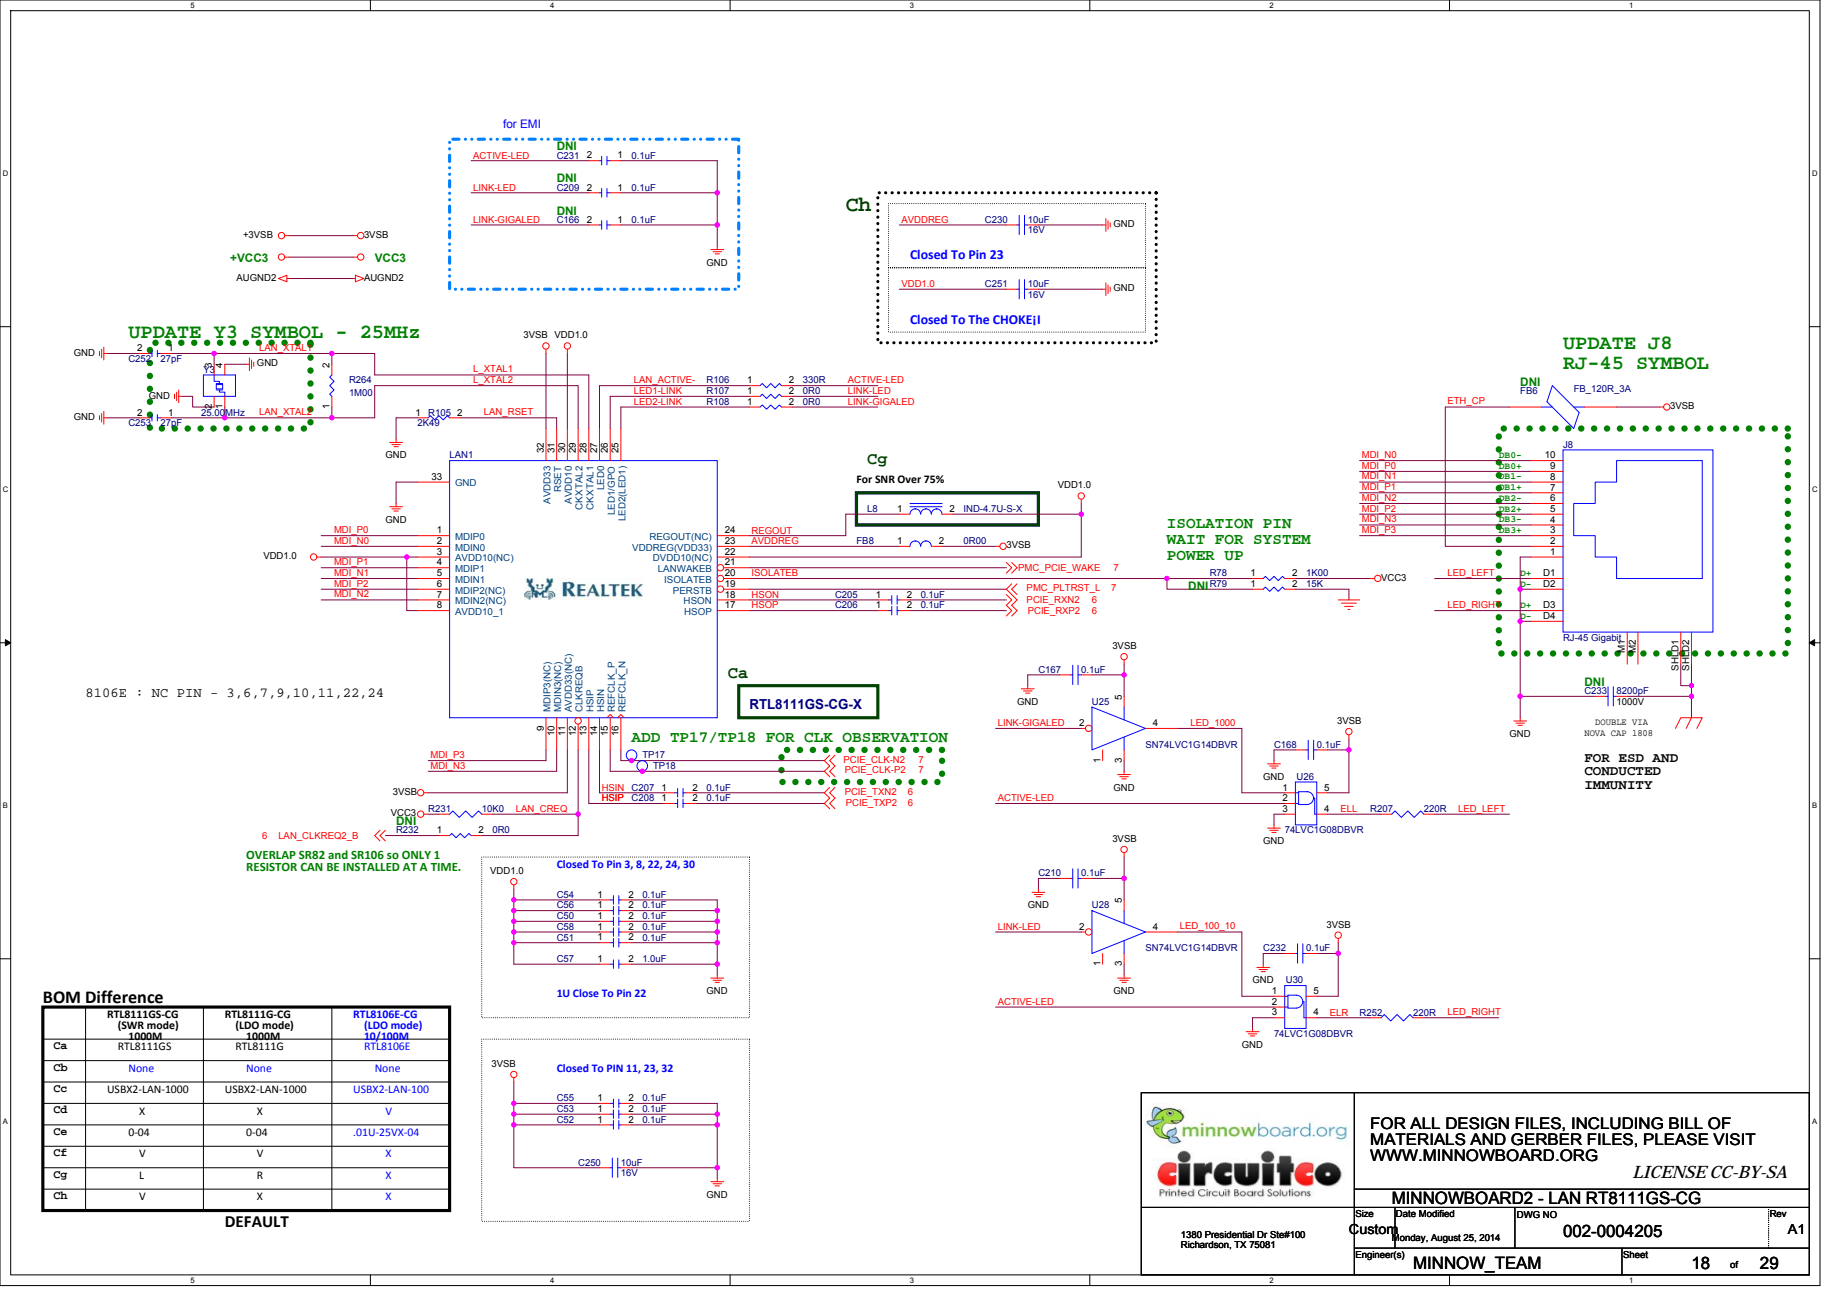
[picture p266: page 18]

for EMI DNI 3VSB VDD1.0

L_XTAL2

ADD TP17/TP18 FOR CLK OBSERVATION

6 LAN_CLKREQ2_B
OVERLAP SR82 and SR106 so ONLY 1
RESISTOR CAN BE INSTALLED AT A TIME.

Cb | None | None | None
Cc | USBX2‐LAN‐1000 | USBX2‐LAN‐1000 | USBX2‐LAN‐100

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

Ce | 0‐04 | 0‐04 | .01U‐25VX‐04
Cf | V | V | X
Cg | L | R | X

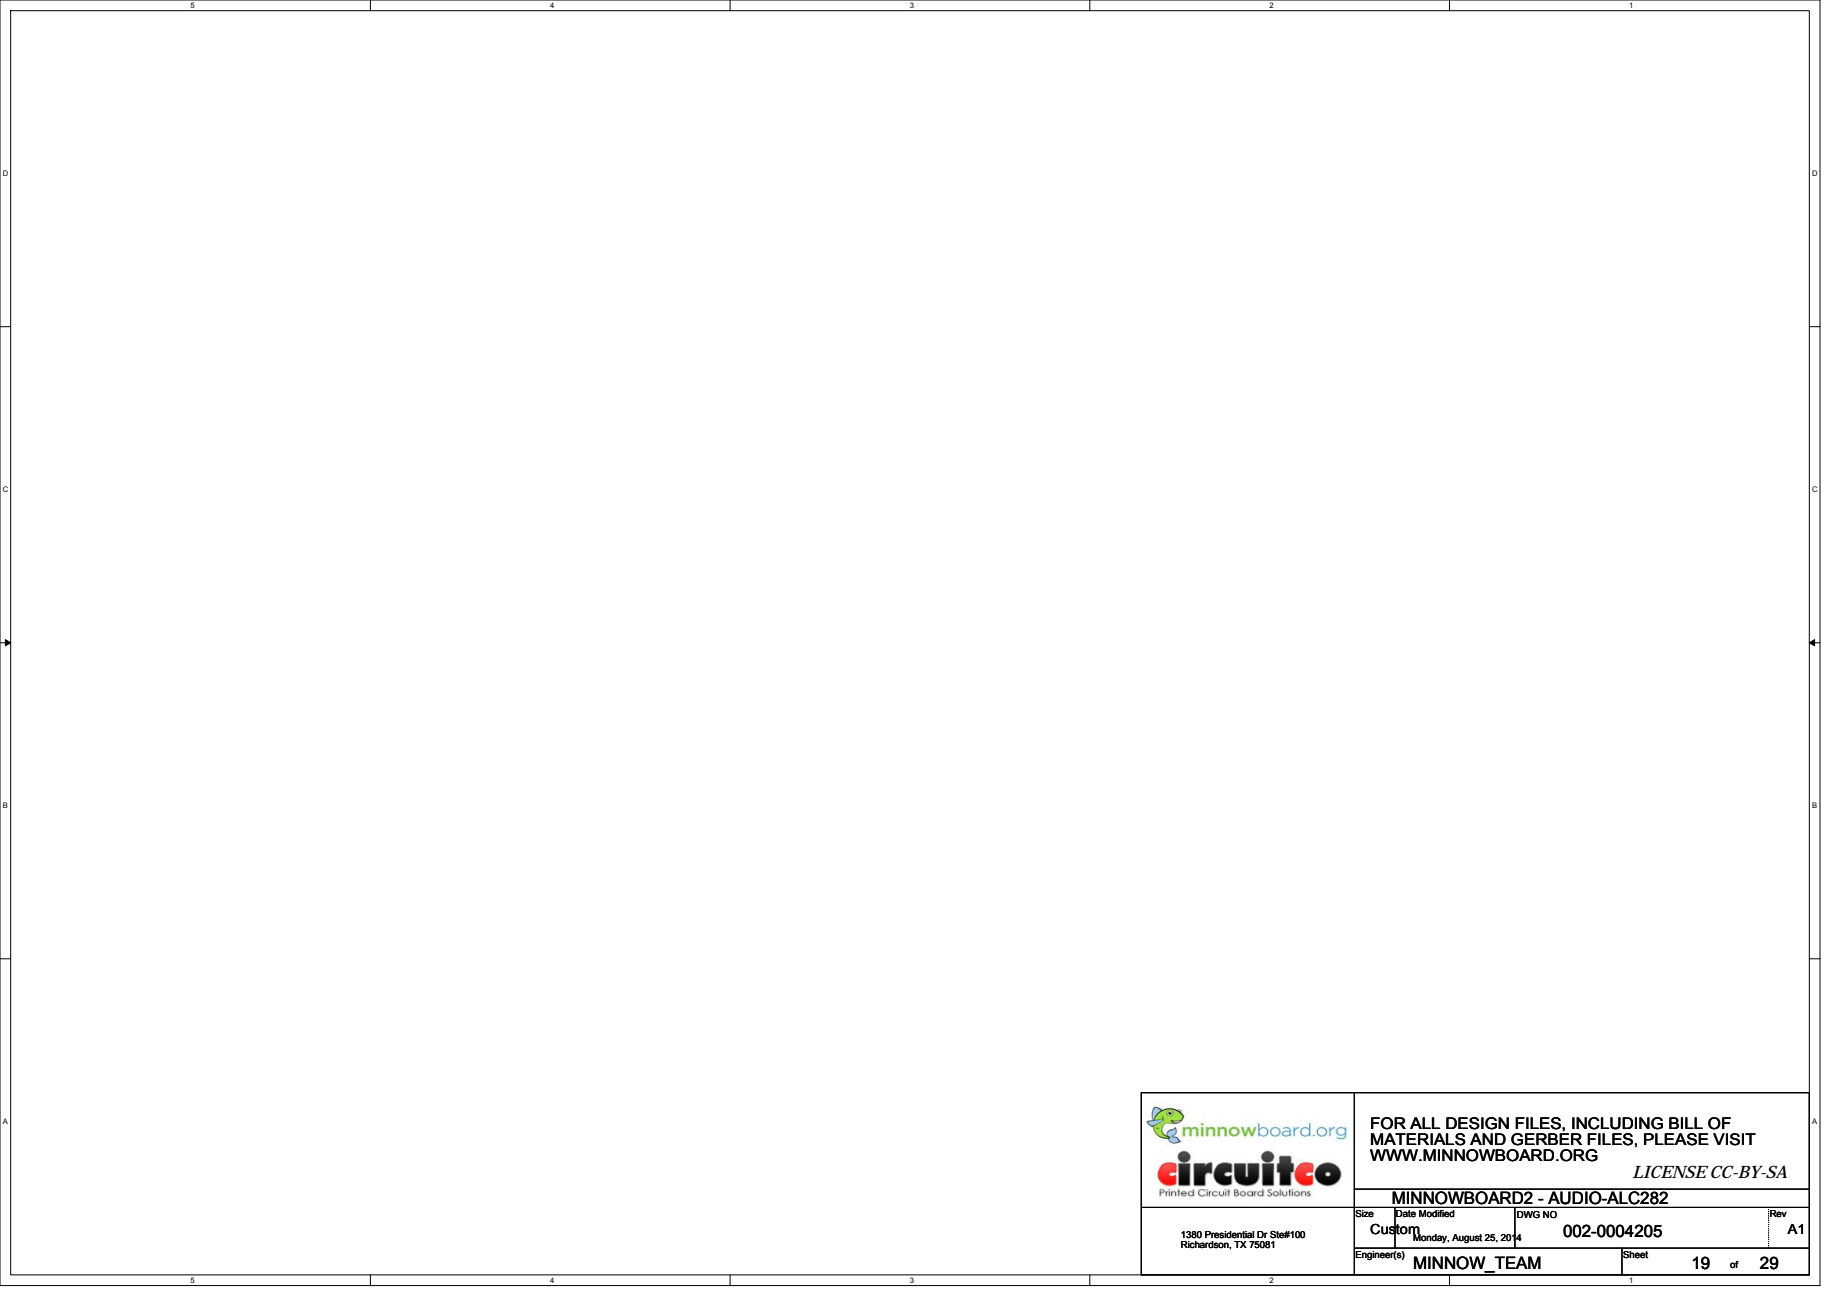
[picture p267: page 19]
MINNOWBOARD2 - AUDIO-ALC282

FOR ALL DESIGN FILES, INCLUDING BILL OF
MATERIALS AND GERBER FILES, PLEASE VISIT
WWW.MINNOWBOARD.ORG

LICENSE CC-BY-SA

## At least 0.1" on the pin 1-2 side and the pin 7-8 side to allow


space for the DediProg connector

NOTE: COMPATIBLE U3 SPI ROM PARTS

FOR ALL DESIGN FILES, INCLUDING BILL OF
MATERIALS AND GERBER FILES, PLEASE VISIT
WWW.MINNOWBOARD.ORG

LICENSE CC-BY-SA

MINNOWBOARD2 - SPI PROM/LSS HEADER

# ADAPTOR POWER LED

# DATASHEET SAYS


CHANGE MTG HOLES TO

BOARD HOLES - 4 TOTAL - 1 in EACH CORNER

FOR ALL DESIGN FILES, INCLUDING BILL OF
MATERIALS AND GERBER FILES, PLEASE VISIT
WWW.MINNOWBOARD.ORG

LICENSE CC-BY-SA

MINNOWBOARD2 - PWR BTN / LED / HOLES

# +3.3VSB / Boost +10V

# DC_IN 5V


ENLDO 12

PG High when +PS_3VSB OVER than 95%
PG Low when +PS_3VSB Under than 85%

FOR ALL DESIGN FILES, INCLUDING BILL OF
MATERIALS AND GERBER FILES, PLEASE VISIT
WWW.MINNOWBOARD.ORG

LICENSE CC-BY-SA

## Intel Require


PDG recommend Rpu should be 70 OHMS

CLOSE VCORE CHOKE DC side

COMPG 40 FBG 39

1 2 COMPG_RC2 1 2 | RTNG 38

CLOSE GFX CHOKE DC side

FOR ALL DESIGN FILES, INCLUDING BILL OF
MATERIALS AND GERBER FILES, PLEASE VISIT
WWW.MINNOWBOARD.ORG

LICENSE CC-BY-SA

# VCORE PHASE

# UPDATE IND SYMBOL


MLCC close to Switching MOS

Add 7 pieces MLCC for Power test.

FOR ALL DESIGN FILES, INCLUDING BILL OF
MATERIALS AND GERBER FILES, PLEASE VISIT
WWW.MINNOWBOARD.ORG

LICENSE CC-BY-SA

MINNOWBOARD2 - DC/DC VCORE/GFX MOS


STATE | S3 S5 VDDQ | | | VTTREF | VTT
S0 | Hi | Hi | on | | on
S3 | Lo | Hi | on | | Off(Hi‐Z)
S4/S5 | Lo | Lo | Off Discharge | Off Discharge | Off Discharge

PG enable when +VDIMM over 95%

FOR ALL DESIGN FILES, INCLUDING BILL OF
MATERIALS AND GERBER FILES, PLEASE VISIT
WWW.MINNOWBOARD.ORG

LICENSE CC-BY-SA

V1.0 : 3.6A
V1.05 : 1.3A


VGS=10V Rds(on)=65m MAX
VGS=5V Rds(on)=90m MAX
VGS should > 2V

FOR ALL DESIGN FILES, INCLUDING BILL OF
MATERIALS AND GERBER FILES, PLEASE VISIT
WWW.MINNOWBOARD.ORG

LICENSE CC-BY-SA

1380 Presidential Dr Ste#100 1380 Presidential Dr Ste#100 1380 Presidential Dr Ste#100 Richardson, TX 75081 Richardson, TX 75081 Richardson, TX 75081 | Size Size Size Custom Custom Custom | Date Modified Date Modified Date Modified | DWG NO DWG NO DWG NO 002-0004205 002-0004205 002-0004205 | Rev Rev Rev A1 Monday, August 25, 2014 A1 Monday, August 25, 2014 A1 Monday, August 25, 2014

Engineer(s) Engineer(s) Engineer(s) MINNOW_TEAM MINNOW_TEAM MINNOW_TEAM | Sheet Sheet Sheet 26 26 26 29 29 29 of of of

# PCH-GPIO function

Pin Name | Power Well | Usage

Interrupt mapping; Function; INT# port; PCIe*1 port; Device; Boot Set; GPIO_S5[03]; 1P8VSB, 20k,H; GPI; GPO; mPCIE_WAKEB; GPIO_S5[04]; 1P8VSB, 20k,L; LAN; INTC#; port 2; RTL8111GS-CG; GPIO_S0_SC[058]; GPIO reserved; GPIO_S0_SC[059]; GPO GPIO reserved; GPIO_S0_SC[060]; GPIO_S5[01]; OPEN; GPIO_S5[02]; GPIO_S0_SC[057]; UART Debug Port UART3 TXD; GPIO_S0_SC[061]; Debug Port UART3 RXD; UART; GPIO_S5[10]; TXE UNLOCK control; GPIO_S5[06]; BOM OPTION; GPIO_S5[07]; GPIO_S5[05]; GPIO_S0_SC[025]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

FOR ALL DESIGN FILES, INCLUDING BILL OF
MATERIALS AND GERBER FILES, PLEASE VISIT
WWW.MINNOWBOARD.ORG

LICENSE CC-BY-SA

MINNOWBOARD2 - GPIO/HW MAPPING

## Switching

## +3VSB

N-MOS; VNN; VCORE; SVID; Battery 3V; Bay Trail - M; AVDD; DVDD; ALC282; +5VSB; +VCC3; +VCC; Switching; DDR3L 1066MHz (SDRAM x4); +VTT_DDR; 0.5A max; +VTT_DDR:0.675V; LDO; 7.1A max; 0.075A max; 1.14A max; LAN RTL8111GS; eMMC; EXPANSION SLOT; +3.3V_AUX; FRONT USB3 * 1PCS; FRONT USB2 * 1PCS; max; 0.6A max; 8A max; 0.3A max; 4.8A max; 1.0A max; 1.917A max; 0.41A max; 0.033A max; 0.055A max; 1A max; 0.2A max; ??A max; 1.4A max; 0.75A max; 7.5W max; +PS_3VSB; +PS_5VSB; EuP; +10V (VOLTAGE DBLR)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

+VDIMM | 1.5A max

Can be grounded if MIPI CSI not used.

VRTC | RTC | 160uA

2.75A max

VDD3P3 | 3.3V | 370 mA

VDD1P0 | 1.0V | 300mA

VCC | 3.3V | 200mA

VCCQ | 1.8V | 150mA

FOR ALL DESIGN FILES, INCLUDING BILL OF
MATERIALS AND GERBER FILES, PLEASE VISIT
WWW.MINNOWBOARD.ORG

LICENSE CC-BY-SA

# PWR Sequence & RST Diagram

2.1

SYS5VSB_OFF(8); PS_OUT#(7); SYS_RESET#(AC3); PWBTN_L; SLP_S4_L; SLP_S4#(F22); +PS_3VSB; 25MHz; ICLK_OSCIN(AH12) ICLK_OSCOUT(AH10); Output Clock; Intel Bay Trail-M/I; EuP NCT3012S; VSB(2); PMC_CORE_PWROK(B7); PWRBTN#(J26); SLP_S3#(D22); PLTRST#(F20); RSMRST#(B10); RSMRST_L; SLP_S3_L; PS_OUT_L; PCH_PLTRST_L; Switching; +PS_5VSB; +5VSB; 13.1 +VCC; +3VSB; (MOS); 13.2 +VCC3 P31; LAN RTL8111GS; EXPANSION; DC-DC (NMOS); +5VSB 5; +1P0A_ENABLE; 6 +V1P0A +PS_3VSB 5.1; +1P8A_ENABLE; 7 +V1P8A +PS_3VSB 6.1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

FOR ALL DESIGN FILES, INCLUDING BILL OF
MATERIALS AND GERBER FILES, PLEASE VISIT
WWW.MINNOWBOARD.ORG

LICENSE CC-BY-SA
