MinnowBoard-org/design-files/minnowboard-turbot-dual-core/pcb-f200-revX205_Turbot-A/Minnowboard_Turbot_X205_Sch.pdf

# Rev : X205 TURBOT

# POWER DELIVERY

Power Sequence; REVISION HISTORY:; Page; Index; Rev; Date; Notes; TABLE OF CONTENTS; TITLE; DATE; SHEET; SIZE; DWG NO; REV; Prepared For:; ADI -80204-0125-G00; FIXES BASED ON ALPHA QUALIFICATION; SWAP IN NEW LOW-Vth FET FOR Q16, DNI U33 (SPD EEPROM); STUFF R354, REPLACE U32 (USB POWER SWITCH) WITH PART FROM X100 RELEASE; ADD LABELS TO BOM FOR PILOT PRODUCTION RELEASE; BOM FIX D5, D6, D10 TO PART WITH CORRECT FOOTPRINT; NO STUFF R53, R54, R55, R56 TO MATCH VALIDATED PROTOTYPES

INITIAL RELEASE OF TURBOT DESIGN

Cover Page
Block Diagram
CPU-DDI/VGA
CPU-DDR3-CHA
CPU-DDR3-CHB
CPU-PE/HDA/SD/eMMC/Strap
CPU-SPI/CLOCK/RTC/PMC/UART
CPU-USB/LPC/SMB/I2C
CPU-PWR1
CPU-PWR2
CPU-GND
Memory_CHA-1
Memory_CHA-2
uSD CARD CAGE
HDMI / VGA
USB3+USB2
EXPANSION I/O
LAN RTL8111GS-CG
NOT USED
CSI/GPIO Header/UART_DBG
PWR BTN / LED / HOLE
DC-5VSB/3VSB / VCC / VCC3
DC/DC VCORE/GFX
DC/DC VCORE/GFX PHASES
DC-DIMM/DDR_VTT

DC-DC VOLTAGE
GPIO/HW Mapping

This work is licensed under the Creative Commons Attribution-Share
Alike 3.0 Unported License. To view a copy of this license, visit
http://creativecommons.org/licenses/by-sa/3.0/ or send a letter to
Creative Commons, 171 Second Street, Suite 300, San Francisco,
California, 94105, USA.

Minnowboard Turbot design derived from Minnowboard MAX as
designed by CircuitCo LLC.

All derivative works are to be attributed to ADI Engineering
and CircuitCo LLC .

For more information, see
http://creativecommons.org/license/results-one?license_code=by-sa

ADI ENGINEERING
1758 WORTH PARK
CHARLOTTESVILLE, VA 22911
WWW.ADIENGINEERING.COM
TURBOT

For all design files, including bill of materials
and gerber files, please visit
www.minnowboard.org

## page12/13

# Memory CH0

pages 3-11; page20; COMMON; CLOSED; NORM; OPEN; MUX; HEADER; DEDI-PROG; EXP; LSS; page17; JTAG_HDR; EXP_GPIO(3:0) BUS,; EXP_I2C BUS,; mPCIE, SATA,; EXPANSION I/O; SATA; SATA0; page6; page18; page15; page14; page16; UART; USB2.0; USB2.0x1; USB3.0x1; USB3.0; DDI0; uHDMI; SOC_SPI; SPI ROM; PCIe_X1; RTL8111GS; LAN; DDR3 :1066/1.35V DDR3L memory down x16; Bay Trail-I; BLOCK DIAGRAM; Prepared For:

uSD CARD CAGE

LOW SPEED SERIAL I/O
SIO_SPI BUS, GPIO_I2C BUS,
UART2 (TXD/RXD)
UART1 (TXD/RXD/CTSB/RTSB,
I2S BUS, PWM(1:0),

ADI ENGINEERING
1758 WORTH PARK
CHARLOTTESVILLE, VA 22911
WWW.ADIENGINEERING.COM

## for EDP ONLY

## STRAIGHT BIT ORDER is


FOR HDMI VIDEO/AUDIO,
REVERSE BIT CONNECTIONS
FROM (0:2) TO (2:0), BIT3
IS THE CLOCK SIGNAL.

Bay Trail-M Remove eDP Port

## ABCD

CD


## ABCD

CD

DRAM1 SECTION; DRAM1_ODT_0; DRAM1_CKN_0; DRAM1_CKP_0; DRAM1_DRAMRST; DRAM1_CKN_2; DRAM1_CKP_2; DRAM1_DQSN_77; DRAM1_DQSP_77; DRAM1_DQSN_66; DRAM1_DQSP_66; DRAM1_DQSN_55; DRAM1_DQSP_55; DRAM1_DQSN_44; DRAM1_DQSP_44; DRAM1_DQSN_33; DRAM1_DQSP_33; DRAM1_DQSN_22; DRAM1_DQSP_22; DRAM1_DQSN_11; DRAM1_DQSP_11; DRAM1_DQSN_00; DRAM1_DQSP_00; DRAM1_DQ_6363; DRAM1_DQ_6262; DRAM1_DQ_6161; DRAM1_DQ_6060; DRAM1_DQ_5959; DRAM1_DQ_5858; DRAM1_DQ_5757; DRAM1_DQ_5656; DRAM1_DQ_5555; DRAM1_DQ_5454; DRAM1_DQ_5353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

ADI ENGINEERING
1758 WORTH PARK
CHARLOTTESVILLE, VA 22911
WWW.ADIENGINEERING.COM

D

D


Bay Trail-I Different--> Pin BD5

BOM Option
Hardware Identification (HW ID)
"001" = Revision X3

STRAP RESISTORS SHOULD BE PLACED CLOSE TO SOC

Top address bit is inverted

Top address bit is unchanged

CPU-PE/HDA/SD/eMMC/Strap

D

D


Bay Trail-M Remove SPI port

SoC Internal Pull high

BATT HOLDER, BS-1225-PC

CPU-SPI/CLOCK/RTC/PMC/UART

## TX and RX LINES

## USB3 HIGH SPEED


LOW SPEED SERIAL I2C BUS
EXPANSION I2C BUS

CPU-USB/LPC/SMB/I2C

D

D


AC30 | | AC22
AD27 | | AC24
AD29 | | AD22
AD30 | | AD24 | Under the PKG Shadow
AF27 | | AF22
AF29 | | AF24
AG27 | | AG22
AG29 | | AG24
AG30 | | AJ22
P26 | | AJ24
P27 | | AK22
U27 | | AK24
U29 | | AK25
V27 | | AK27
V29 | | AK29
V30 | | AK30
Y27 | | AK32
Y29 | | AM22
Y30 | | AA22

Under the PKG Shadow

Edge of the Board

10mA

900mA


Place close to Pin BJ6.

Place close to Pin AF16,AF18.

Place close to Pin G1

Place close to Pin AN21

Place close to Pin AN19

Place close to Pin AN18

Place close to Pin AN25.

Can be grounded if MIPI
CSI not used.
Bay Trail-I

USB_HSIC_V1P24_G3 Can connect to V1P0A when USB HSIC not used.

Place close to Pin AF36.

Place close to Pin AA18

Place close to Pin AD35, AF36

Place close to Pin U25

Place close to Pin AK19/AK21

Place close to Pin AJ18.

Place close to Pin AM16.

Place close to Pin N18,P18.

Place close to Pin AF21,AG21

Place close to Pin AG21,V24,Y22,Y24.

Place close to Pin V18 400mA

Place close to Pin AD36.

Place close to Pin U36

Place close to Pin AF19

Place close to Pin AC32,Y32.

Place close to Pin AG32

Place close to Pin AA25

D

D


L13 | U30
L19 | U32
L27 | U40
L35 | U42
M19 | U43
M26 | U45
M27 | U46
M34 | U48
M35 | U49
M38 | U5
M47 | U51
M51 | U53
N1 | U6
N16 | U8
N38 | U9
N51 | V12
P13 | V16
P16 | V19
P19 | V21
P20 | V35
P24 | V40
P32 | V44
P35 | V51
P38 | V7
P4 | Y10
P47 | Y14
P52 | Y16
P9 | Y21
T40 | Y25
U1 | Y33
U11 | Y41
U12 | Y44
U14 | Y7
U21 | Y9

D

D


D

D


D

D


## than HDMI_CLK_DN/P

## HDMI_TXn_DP/N should be longer


# USB3.0

# USB2.0


USB SIGNALS FOR PWR ENABLE
AND OVERCURRENT STATUS
RUNS ON +V1P8A LVL

D

D


EXPANSION HS CONNECTOR WITH
mPCIE, mSATA, I2S AUDIO, GPIO, and XDP I/O

## Close To Pin 23

D


VDD1.0
Close To The CHOKE

OVERLAP R231 and R232 so ONLY 1
RESISTOR CAN BE INSTALLED AT A TIME.

D

D

(BLANK); Prepared For:

ADI ENGINEERING
1758 WORTH PARK
CHARLOTTESVILLE, VA 22911
WWW.ADIENGINEERING.COM

## space for the DediProg connector

## and the pin 7-8 side to allow


POPULATE ONLY ONE OF THESE TO
SELECT THE OPERATING VOLTAGE OF THE
SPI FLASH.

At least 0.1" on the pin 1-2 side

NOTE: COMPATIBLE U3 SPI ROM PARTS

SPI PROM/LSS HEADER

# USE 10K PU

# DATASHEET SAYS


SYSTEM POWER LED - GPIO CONTROLLED

BOARD HOLES - 4 TOTAL - 1 in EACH CORNER

PWR BTN / LED / HOLES

# Current limit. 8A

# Imax. 4.8A


PG High when +PS_3VSB OVER than 95%
PG Low when +PS_3VSB Under than 85%

# Intel Require

D


PDG recommend Rpu should be 70 OHMS

CLOSE VCORE CHOKE DC side

CLOSE GFX CHOKE DC side

DC/DC VCORE/GFX CONTROL

## ID2 Max = 30A

## ID1 Max = 15A


MLCC close to Switching MOS

SPxx PLACE ON THE
SOLDER SIDE,
CLOSE INDUCTOR

DC/DC VCORE/GFX PHASES

D

D


RT8207M S3 and S5 truth table
STATE S3 S5 VDDQ VTTREF VTT

# +V1P0A

# +V1P0S


VGS=10V Rds(on)=65m MAX

VGS=5V Rds(on)=90m MAX
VGS should > 2V

## EXPANSION_BUS GPIO4

## EXPANSION_BUS GPIO3

## EXPANSION_BUS GPIO2

## OPEN

## XDP_H_OBSDATA_A3

## XDP_H_OBSDATA_A2

## XDP_H_OBSDATA_A1

GPIO_S0_SC[030] | 1P8V, 20k,H | GPO
GPIO_S0_SC[029] | 1P8V, 20k,H | GPO
GPIO_S0_SC[028] | 1P8V, 20k,H | GPO
GPIO_S0_SC[027] | 1P8V, 20k,H | GPO
GPIO_S0_SC[026] | 1P8V, 20k,H | GPO

## EXPANSION_BUS GPIO1

GPIO_S0_SC[024] | 1P8V, 20k,H | GPO
GPIO_S0_SC[023] | 1P8V, 20k,H | GPO
GPIO_S0_SC[022] | 1P8V, 20k,H | GPO

## XDP_H_OBSDATA_A0

GPIO_S5[09] | 1P8VSB, 20k,H | HDMI LD SWITCH ENABLE | GPO
GPIO_S5[08] | 1P8VSB, 20k,H | HDMI_DC_DC ENABLE | GPO
GPIO_S5[00] | 1P8VSB, 20k,H | SOC_GPIO_S5_0 (LSS CONN) | GPO
| | SOC_GPIO_S5_2 (LSS CONN)

## SOC_GPIO_S5_1 (LSS CONN)

GPIO_S0_SC[025] | 1P8V, 20k,H | GPO
GPIO_S5[05] | 1P8VSB, 20k,L | BOM OPTION | GPI
GPIO_S5[07] | 1P8VSB, 20k,L | BOM OPTION | GPI
GPIO_S5[06] | 1P8VSB, 20k,L | BOM OPTION | GPI
GPIO_S5[10] | 1P8VSB, 20k,H | TXE UNLOCK control | GPO
GPIO_S0_SC[061] | 1P8V, 20k,H | Debug Port UART3 RXD | UART
GPIO_S0_SC[057] | 1P8V, 20k,H | Debug Port UART3 TXD | UART
GPIO_S5[02] | 1P8VSB, 20k,H | GPO GPO

## OPEN

GPIO_S5[01] | 1P8VSB, 20k,H
GPIO_S0_SC[060] | 1P8V, 20k,L | GPIO reserved | GPO
GPIO_S0_SC[059] | 1P8V, 20k,L | GPIO reserved | GPO
GPIO_S0_SC[058] | 1P8V, 20k,L | GPIO reserved | GPO
LAN | INTC# | port 2 | RTL8111GS-CG
GPIO_S5[04] | 1P8VSB, 20k,L

## mPCIE_WAKEB GPO

GPIO_S5[03] | 1P8VSB, 20k,H | GPI

# Boot Set

# Device

Function | INT# port | PCIe*1 port

# Interrupt mapping

Pin Name | Power Well | Usage

# PCH-GPIO function

# GPIO/HW MAPPING

B

A | A

B

C

D

C

D

Prepared For:

BY:

## ADI ENGINEERING 1758 WORTH PARK CHARLOTTESVILLE, VA 22911 WWW.ADIENGINEERING.COM

## Bay Trail - I

## N-MOS

??? A max; PVDD; LDO; 0.07A max; CSI Connector; N-MOS; +10V (VOLTAGE DBLR); EuP; +PS_5VSB; +PS_3VSB; 7.5W max; 0.75A max; 1.4A max; ??A max; 0.2A max; 1A max; 0.055A max; 0.033A max; 0.41A max; 1.917A max; 1.0A max; 4.8A max; 0.3A max; 8A max; 0.6A max; 2.75A max; 410mA max; FRONT USB2 * 1PCS; FRONT USB3 * 1PCS; +3.3V_AUX; EXPANSION SLOT; eMMC; VCCQ; VCC; VDD1P0; VDD3P3; LAN RTL8111GS; 1.14A max; 0.075A max; Switching; 7.1A max; +VTT_DDR:0.675V; 1.5A max; +VTT_DDR; 0.5A max; +VDIMM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

Can be grounded if MIPI CSI not used.

ADI ENGINEERING
1758 WORTH PARK
CHARLOTTESVILLE, VA 22911
WWW.ADIENGINEERING.COM

2.2

+10V

+V1P2S_MIPI; +PS_3VSB DC-DC; +VDIMM; +VCORE_PG; PMC_CORE_PWROK; DRAM_CORE_PWROK; SLP_S3_L; 13 +VDIMM_VTT; +V_DIMM; 14.2 +VGFX; 14.1 +VCORE 13.2 +5VSB; +VCC; (ISL95837); Switching; DRAM_S4_PWROK; DRAM_VDD_S4_PWROK; 11 +VDIMM; +5VSB; SLP_S4_L; +PS_3VSB; +3VSB; +3VSB_EN; (NMOS); +1P8A_ENABLE; +1P0A_ENABLE; +PS_5VSB; EXPANSION; LAN RTL8111GS; (MOS) P31; 13.2 +VCC3; 13.1 +VCC; 19 PCH_PLTRST_L; PS_OUT_L; RSMRST_L; RSMRST#(B10); PLTRST#(F20); SLP_S3#(D22); PWRBTN#(J26); PMC_CORE_PWROK(B7); VSB(2)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

PWR Sequence & RST Diagram

ADI ENGINEERING
1758 WORTH PARK
CHARLOTTESVILLE, VA 22911
WWW.ADIENGINEERING.COM
