MinnowBoard-org/design-files/expansion-boards-lures/drone-lure/Drone-lure-sch.pdf

A

A

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

10/27/2015 7:01:39 PM f=0.90 C:\Users\davidand\Documents\eagle\drone-lure-revA1\drone-lure-revA1.sch (Sheet: 1/1)
